nathe-vink/earmilk/critic/LOG.md

# Critic log

One row per round. Fresh context, image only, using `critic/PROMPT.md`. At most three rounds per shot.

| Date | Shot | Prompt v | Round | Score | Three gaps | Fix first | What changed after |
|---|---|---|---|---|---|---|---|
| 2026-10-01 | 01 hero pair | v1 | 1 | 3 | (1) Light story contradicts itself: hard sun wedge on the wall but only faint short shadows, no contact darkening, no floor bounce. (2) Every surface a flat placeholder: no board sheen, drivers flat black with no surround or basket lip, parquet random rectangles, no reflection. (3) Composition unfinished: cropped beige block in the corner, no skirting, near speaker jammed right, empty middle. | One coherent light rig: window sun plus sky fill so the cartons throw hard shadows that agree with the wall wedge, sit in a contact shadow and pick up warm bounce. About an hour. | v2: sun stronger with fills cut back, hemisphere floor bounce, contact-shadow decals, skirting, chair replaces the sofa block, camera recentred, coated-board sheen, bevelled board edges, driver baskets with flange and screws. |
| 2026-10-01 | 02 two rooms | v1 | 1 | 3 | (1) No materials: flat white, razor fold edges, floors are tinted grids, the wall wedge in a is not received by the carton. (2) Drivers are decals: no surround roll, flange, rebate, screw heads or rim shadow; the oval has no edge thickness. (3) The pair disagrees on the product's colour (white/red vs kraft/black), and the warm key is not white-balanced. | Rebuild the drivers and the spout as hardware set into the cabinet: rolled surround, flange in a rebate with screw heads, dust cap that catches the key. Half a day. | v2: driver baskets rebuilt (flange, screws, glossy surround, shaded cone and cap), board sheen and bevels, windows moved front-left so the sun hits the faces the camera sees, hemisphere bounce, contact shadows, a chair in each room for scale. Colour difference between a and b is the shot's point (the sleeve swap) and stays. |
| 2026-10-01 | 03 bowl close-up | v1 | 1 | 4 | (1) The black faceplate is a void: reflects none of the white surround, no rim catch. (2) Bowl shading says key from below-right while the box is lit from above; no contact shadow under the lip. (3) Crop by accident: wordmark baseline sliced, a sliver of a second plane along the top edge. | One soft key from above-left with a white environment card, then pull the camera back a hair. About an hour. | v2: key moved above-left with the environment as the white card, faceplate made reflective, camera pulled back so the wordmark and the top edge clear the frame. |
| 2026-10-01 | 04 back | v1 | 1 | 3 | (1) No volume: parallel verticals, no top or side face, flat fills, and the backdrop seam runs through the port. (2) Shadow detached from the footprint, no contact occlusion; hard tonal steps on the carton say hard light while the shadow says overcast. (3) No materials: port a flat disc, posts flat dots, label a textureless inset rectangle. | Put it on the floor: one soft key from upper right, a tight contact shadow from the footprint, the slight downward perspective the seam implies. About an hour. | v2: camera raised to look slightly down so the gable top shows, key from upper right, contact shadow decal, post bodies and port flange given metal response, board sheen. |
| 2026-10-01 | 05 five flavors | v1 | 1 | 5 | (1) Cones uniform black with no gradient, no surround specular, no rim shadow into the dish. (2) Bases meet the backdrop as a hard line with no contact occlusion; the soft smudge to the right is weaker than the crisp faces. (3) On the white units the fin, slope and front are the same white a hair above the backdrop, so the gable fold never turns. | Rebuild the lighting: one large soft key from upper left at about 45 degrees, quarter fill from the right, a ground plane with contact occlusion. About an hour. | v2: key moved to upper left at 45 degrees with a quarter fill from the right, contact shadow decals, driver hardware rebuilt, cone and cap given a sheen so they shade. |
| 2026-10-01 | 06 mixed crate | v1 | 1 | 4 | (1) Nothing occludes: no shadows between cartons or on the crate's inner walls, no contact darkening, crate base has no shadow. (2) Flat surfaces: no creases, no sheen, crate grain runs the wrong way and is one stretched tile, floor flat. (3) The rim cuts through all three visible woofers; the red port cup is the loudest thing in frame. | Re-light with a real rig: large area key up-left, soft fill, occlusion so the cartons shadow each other and ground into the rim; drop the camera so the woofers clear the rim. About an hour plus fifteen minutes. | v2: contact shadows under crate and pints, key up-left, camera raised so more of each pint shows over the rim (the rim height is spec, so the woofers stay partly behind it), crate grain turned to run along the boards. |
| 2026-10-01 | 07 sleeve swap | v1 | 1 | 3 | (1) Frame b does not describe a physical event: the lifted tube's die-cut lands on the bowl and reads as a porthole, the small driver reads as an empty ring, and the lid is nowhere. (2) Nothing lit or grounded: no floor, no contact shadow, the hovering lid casts nothing. (3) Untextured primitives: drivers flat, razor edges, no crimped seam; hairline spike and dotted ridge on the lid in a. | Rebuild the action so frame b is a true intermediate state and re-render all three. A day. | v2: frame b now shows the lid standing on the floor beside the speaker and the tube lifted clear of the gable so nothing overlaps the bowl; contact shadows; fin cover sunk 2 mm to kill the z-fighting ridge; driver and board materials as above. The two-piece sleeve (tube plus lid) is a Decision and stays. |
| 2026-10-01 | 01 hero pair | v2 | 2 | 4 | (1) Room light and product light disagree: the warm patch high on the right wall reads as sun from the right while the cartons' right faces are dark and the floor shadows read short and soft. (2) No material: one flat white, no sheen, no crease lines, no board thickness at the spout, woofers near-uniform black with no surround roll or cap specular, soft-edged logo decals. (3) Viewport, not a picture: the pair split across depths, the second unit near the corner behind a chair, half the frame empty flat-tiled floor with no grain or reflection. | Relight with one sun through the window that reproduces the wall patch plus a sky fill, path-traced, so right faces go bright, fronts fall off with warm bounce, shadows go long with a penumbra, contact occlusion at the base. About an hour. | v3: ambient occlusion pass, glossier coated board, fold and crimp lines on the lid and fin, lighter shaded cones with a highlight on cap and surround, reflective floor, higher shadow resolution, 2x supersampling. The sun stays on the left window because the pair faces the room; the floor patch now shows where it comes from. |
| 2026-10-01 | 02 two rooms | v2 | 2 | 4 | (1) The room's light never touches the hero: window wedges on the wall and floor but the carton's faces stay flat, no shadow from the carton or the chair as read. (2) Flat untextured box and decal drivers: no scored folds, glued seam or crimp, no sheen or ink grain; cones with a baked gradient regardless of light. (3) The night version is a grade, not a relight: everything one monochrome brown, the brand red gone to black-brown, no cooler ambient in the shadows; the chair's back leg is tangent to the carton's edge. | Put the carton in the room's light: one real key where the wall wedge says the window is, shadows on every object, contact and occlusion at the base and under the chair legs, the night version driven by a warm lamp in that rig. About an hour. | v3: occlusion pass, fold and crimp lines, glossier board, shaded cones, a cool sky ambient in the old room so shadows are not sepia, chair moved off the carton's edge, 2x supersampling. The Oat print is dark brown by spec, not red. |
| 2026-10-01 | 03 bowl close-up | v2 | 2 | 4 | (1) The white body has no form: top face, front face and backdrop within a few points of the same off-white, razor edge with no highlight, the back corner dissolves into the background. (2) The recess contradicts itself: brightest at the top-left wall where a dish would be in rim shadow, an S-shaped highlight reads as a saddle. (3) Crop inherited from the viewport: bare top face is 60% of the frame, wordmark not aligned with the recess, a corner fragment and a red sliver at the bottom right. | Relight the body: one key from upper-left so top, front and side step down in value, a 1 to 2 mm edge radius catching a line, a backdrop a few points darker than the top. About an hour. | v3: key steeper and more frontal so the slope reads brighter than the front, occlusion pass, glossier board so the edge and faces separate, the side wordmark sliver cropped out, 2x supersampling. The ground stays #F8F7F4 by spec. |
| 2026-10-01 | 04 back | v2 | 2 | 4 | (1) The light that casts the hard parallelogram never touches the object: flat fills on every face, the fin throws nothing on the slope, a second blurred contact blob bleeds out to the left. (2) No paperboard: no score lines, sheen, kraft grain, the port a flat black disc, posts dots on a bevel-less plate. (3) Orthographic elevation pinned dead centre; spec rows at about 1% of frame height. | One large soft key from upper-left-front with a shadow catcher: slope brightest, gentle falloff on the vertical face, fin shadow on the slope, one shadow with a penumbra and a dark contact core. About an hour. | v3: contact decal tightened to the footprint, key moved to upper-left-front, occlusion pass, glossier board, crimp lines on the fin, metal posts with collars, 2x supersampling so the rows resolve. Straight-on is the brief. |
| 2026-10-01 | 05 five flavors | v2 | 2 | 5 | (1) Cartons cast almost nothing: a small smudge, no contact occlusion, no floor reflection, floor the same tone as the backdrop. (2) Flat fills: no coated-stock sheen, no highlight on the gable creases, drivers laid on the face with no flange shadow. (3) The horn reads as a dish seen from above while the mid is a dead-on circle: the sloped gable does not read on white. | Ground the lineup: one angled area key, a soft directional floor shadow, contact occlusion at every base, a faint floor reflection. About an hour. | v3: reflective studio sweep, occlusion pass, camera raised a few degrees so the slopes and fin read as a gable, fold lines on the lid, glossier board, 2x supersampling. |
| 2026-10-01 | 06 mixed crate | v2 | 2 | 4 | (1) Only the crate casts a shadow: nothing between cartons or into the crate, no contact at the crate's foot, a hard uniform parallelogram. (2) Camera pitched about 40 degrees down with parallel verticals; the rim crops every woofer and the crate takes 60% of the width. (3) Flat albedo everywhere, crate a single milled block, cartons without sheen or folds, while the bowls carry the only hot specular and read as glossy eyes. | Reframe first: drop to about 15 degrees down on a 70 to 85 mm lens, lift the woofers clear of the rim, then relight with one soft key and occlusion. About an hour plus a half-day. | v3: camera lowered to about 25 degrees on a longer lens from further back, occlusion pass, pint throats closed in the throat colour instead of black so they stop reading as eyes, crate boards given end grain and a chamfer, 2x supersampling. Pints stand on the crate floor and the rim is spec height, so the drivers stay partly behind it. |
| 2026-10-01 | 07 sleeve swap | v2 | 2 | 4 | (1) Lifted parts not in the same light as the carton: no shadow from the lid or the tube lands on the body; floor shadow one flat grey with the same razor edge near and far. (2) Hardware as flat fills: cones near-black discs with no recess shadow, bowl a flat red ellipse with a black ellipse pasted off-centre. (3) The frames do not describe one action: the lifted tube runs out of the top of frame b, and in c the old lid and tube have vanished. | Area key from camera-left and a bounce card at camera-right, re-render all three so the lid's and tube's shadows land on the carton and the floor shadow gains a penumbra. About an hour plus a half-day. | v3: key made steep so the lifted lid and tube shadow the carton, occlusion pass, wider lens so the lifted tube stays inside the frame, and in frame c the removed Whole lid and tube lie on the floor behind the speaker so the three frames are one action. |
| 2026-10-01 | 01 hero pair | v3 | 3 | 4 | (1) Room and product light still read as disagreeing: hard wedge on the wall, shadows read soft, floor pools feathered, plank values noisy. (2) No surface craft at spread scale: no board grain, fold shading faint, seal reads as stacked slabs, drivers read as discs at this distance. (3) No hero: two subjects on opposite thirds, left gable tip on the corner line, chair competes. | One hard key agreeing with the wall wedge, tight contact shadows, flatten the plank noise. About an hour. | Round cap reached. Remaining asks are penumbra, grain and bounce light: a path-traced or diffusion pass over this frame, not a change to the model. Composition note (corner tangent, chair) carried to the next camera pass. |
| 2026-10-01 | 02 two rooms | v3 | 3 | 4 | (1) No paperboard craft at this scale: creases faint, seal a slab with lines, port lip without thickness, drivers read flush. (2) Set reads as a blockout: plank texture repeats, no reflection of the carton, chair is six blocks. (3) Day shadow reads overcast against the wall wedge; night room merges into one olive mass with denoiser smearing; print reads brown-black. | Rebuild the carton's surface (creases, seam, crimped fin, port lip, recessed drivers). About a day. | Round cap reached. The night print is Oat's dark brown by spec. Surface fibre, reflections and penumbra go to the photoreal pass. |
| 2026-10-01 | 03 bowl close-up | v3 | 3 | 4 | (1) The faceplate reads as a flat circle in crushed black while everything else is foreshortened, so it reads as a sticker. (2) The red form's shading does not describe a surface: bright at both tips, a dark band through the middle, no contact occlusion along the rim. (3) The white body reads unlit: uniform top and front, razor edge, no ground or cast shadow in frame. | One soft key from upper-left, weak fill, an environment for the gloss to reflect, a ground plane for a contact shadow. About an hour. | Round cap reached. The faceplate is a true circle in the plane of the throat, perpendicular to the view, so it is not foreshortened; a slight camera offset would show its edge. Rim occlusion and reflections go to the photoreal pass. |
| 2026-10-01 | 04 back | v3 | 3 | 5 | (1) The front face is one flat value near the wall tone, the roof plane flat, the cast shadow a uniform wedge without a dark core at the base. (2) Port a pure-black disc with no inner wall, terminal plate flat with no screws. (3) No paperboard: no fibre or ink bleed on the kraft panel, corners read as soft bevels, the fin's crimp lines read as stacked plates. | One large soft key from upper-left with a weak fill so the faces take a gradient and a tight contact shadow forms. About an hour. | Round cap reached. Up one from round 2. Straight-on is the brief; a port interior and kraft fibre go to the photoreal pass. |
| 2026-10-01 | 05 five flavors | v3 | 3 | 4 | (1) Floor and boxes disagree: shadows pool right-rear while some left-facing sides are darkest and a white carton's right side is as bright as its front; contact shadows read faint. (2) Dead-matte razor-edged slabs: no grain, sheen, creases, seam or filleted edge. (3) From this height the roof reads as a chamfer, the spout as a flat ellipse, the drivers flush. | Re-light under one key front-left-high, remove the environment brightening the right sides, a real shadow catcher. About an hour. | Round cap reached. The environment fill is what keeps the white sides readable; a path-traced pass resolves both. |
| 2026-10-01 | 06 mixed crate | v3 | 3 | 4 | (1) Light contradicts itself: the crate's end reads brighter than its front while the shadow says front-left, and the wall carries a soft shadow a hard key could not cast. (2) The set is a finite slab: ground wedge at the corner, floor meets wall with no skirting, planks flat. (3) Nothing has a surface; the bowls read as decals. | One soft area key front-left and above, occlusion on, penumbra that widens, wall and floor shadows agreeing. About an hour. | Round cap reached. Skirting and a larger floor are a quick set fix for the next camera pass; surfaces go to the photoreal pass. |
| 2026-10-01 | 07 sleeve swap | v3 | 3 | 4 | (1) Lit front and turned side differ by a few percent; the lifted lid in a and tube in b read as casting nothing; no contact darkening read. (2) Drivers are the only photographic element against flat board; sleeve cut-outs coincide with the driver rims with no visible edge. (3) Continuity: the lid's oval shows a dark cone while the lid lies empty on the floor; the lifted lid's base lands on the horizon line; the bowl reads red in a and b and dark in c. | One large soft key from upper left, a seamless sweep instead of the wall-floor seam, contact occlusion under every piece, shadows from the lifted parts on the gable. About an hour. | Round cap reached. The bowl is red on Whole and dark brown on Oat by spec; the lid's oval shows the bowl through it, not a cone. The horizon tangent and the seam are a quick camera and backdrop fix for the next pass. |
| 2026-10-01 | 01 hero pair | v4 | 4 | 3 | (1) The room has a sun and the objects do not: the wall wedge and the floor patch are the brightest things in frame, yet the right speaker's right face is the darker face and its shadow reads as a faint short smudge. (2) One flat value per surface: no board tooth, no gable crease, drivers read as radial-gradient discs, parquet in hard blocks. (3) No focal point: two near-identical objects on opposite thirds, chair tangent to the left speaker, bottom third empty floor. | One real key, the same source that makes the wall wedge, so both cabinets take a bright right face and throw hard shadows, then pull the fill down. About an hour. | Look change round (lids and band). Same asks as rounds 1 to 3: the sun is the left window by design (the pair faces the room), its floor patch and the speakers' shadows agree, but the fill flattens them. Carried to the next pass: fill down, sun up. |
| 2026-10-01 | 02 two rooms | v4 | 4 | 5 | (1) A perfect extrusion: hard CG corners, no crease radius at the folds, crimp a ridged slab, drivers flangeless rings around a flat gradient. (2) Shadows disagree with themselves: the wall wedge in a is as bright as the product but the carton shows an even gradient and a soft smear; in b the carton carries hard self-shadows while its floor shadow is a long blur, and the black band dissolves into the floor. (3) The pair reads as two SKUs: red gable and band in a, cream gable and black band in b. | One key of one size per frame that the carton obeys; rotate the night key off the hero face; a dim cool bounce so the band separates; contact occlusion. About an hour. | Up one from round 3. The colour flip between a and b is the shot's point (Whole by day, Oat by night, the sleeve swap) and stays; the night band is Oat's dark brown print by spec. Carried: rotate the night key so the crimp's shadow clears the mid driver. |
| 2026-10-01 | 03 bowl close-up | v4 | 4 | 3 | (1) The red panel is one flat value with no falloff or specular lobe, the faceplate clipped to black with nothing reflected, so only the cavity reads as rendered. (2) An S-shaped crease where the lit upper wall meets the shadowed lower wall, which no rim shadow explains, and a razor rim with no fillet. (3) A fragment: the panel exits on three sides, a sliver of the top lip tangent to the frame, the white body dissolving into the backdrop. | Light it: a large soft key up-left plus a rim so the red takes a gradient, the barrel reflects a source, the rim catches an edge; then pull back. About an hour. | Down one from round 3 after the camera offset. The S-curve is the lip's hard shadow-map edge inside the bowl, not geometry: carried to the next pass as a soft terminator (the bowl stops receiving the key's shadow) and the camera tilted so the top lip clears the frame. |
| 2026-10-01 | 04 back | v4 | 4 | 4 | (1) Cast shadow 370 px to the right in an even grey but no contact shadow under the base and gable, body and edge all one value: a cutout with a shadow drawn beside it. (2) One matte shader everywhere: port a black disc with no inner wall, posts flat rings on a flat plate. (3) Dead-on at mid-height, the cyc's horizon slices the carton under the Facts box, side faces a 6 px strip, nothing to give scale. | Re-light in place: one large soft key high and front-left with a weak fill, a tight dark contact shadow under the base. About an hour. | Down one from round 3. Straight-on at mid-height is the brief (the back is the label). The cast shadow is the back key by design, so the Facts panel stays unlit by it. Surfaces go to the photoreal pass. |
| 2026-10-01 | 05 five flavors | v4 | 4 | 5 | (1) Every face a single flat fill, no falloff across the width, no sheen, folds hard unbevelled lines; on Chocolate and Oat the gable crease all but vanishes. (2) Contact shadows a few percent darker than the floor, no occlusion at the front bottom edges, so the row hovers. (3) Too close on too wide a lens: the end cartons fan out and show side faces the middle one does not, the floor-to-wall transition lands on the gable ridges, white flanks dissolve into the wall. | Re-light with one large soft key from upper-left far enough forward for a 15 to 20 percent falloff across each front face, a real contact pool, side faces down a stop, satin gloss on the board; a longer lens rides along. About an hour. | Held at 5. The lineup is a flat elevation by brief (five cartons, one row, same size), so the longer lens from further back is the cheap carry: camera back and focal up so the ends stop fanning. Falloff and gloss go to the photoreal pass. |
| 2026-10-01 | 06 mixed crate | v4 | 4 | 4 | (1) Two shadows from two suns: a soft blur under the crate's front edge and a razor-edged slab running off the right of frame ending in a stepped notch, while the crate's lit front and shadowed right faces differ by half a stop. (2) Nothing has a surface, and each woofer reads as a black rubber wheel pushed half into the carton body, peeking over the rim. (3) The subject loses its outline on the right: the wall-floor seam runs through the cartons at their waist, the two white cartons sit against an off-white wall, the planks run on a third diagonal. | Relight: kill both shadows, one large area key from upper left matched to the current shadow direction plus a dim fill, so the penumbra widens with distance and the cartons shade each other. About an hour. | Held at 4. The critic read the rim-cropped woofers as wheels, which is a readability problem not a surface one: carried as a camera fix (higher and closer so the crate's inside and the pints' faces show), the desk turned so the planks run with the wall, and the hard sun shadow softened. Crate size and rim height are spec. |
| 2026-10-01 | 07 sleeve swap | v4 | 4 | 4 | (1) The object revealed is not the same in each frame: pale gable in a, lighter tan core with no band in b, darker tan with a near-black band in c; the spout shows red in a and b and dark in c. (2) The pieces do not share one floor or light: the lifted lid carries a soft contact shadow in mid-air in a, the lifted tube adds nothing to the floor shadow in b, and in c the lid's base slides under the standing tube's front corner. (3) Flat colour with razor edges, drivers vignetted discs, so the sleeve's cut-outs in b read as grey dents. | Make the core one asset across the frames: one tan, the band present from b onward or absent everywhere, one interior colour in the spout, then re-render. About an hour. | Held at 4. The frames are one action by spec: a lifts the Whole lid off the birch cabinet, b lifts the Whole tube off it, c has the Oat sleeve on with the Whole lid and tube on the floor; the band belongs to the sleeve, not the cabinet, and the bowl is red for Whole and dark brown for Oat. The shadow in a is the lid's shadow landing on the gable top. The lid under the tube's corner in c is a real placement error: carried as a lid move. |
| 2026-10-02 | 01 hero pair | v6 | 1 (finish look) | 4 | (1) The room's hard sun reads from camera-right (wall patch, floor wedges) while both cabinets read lit soft from the front-left with no sun on their right faces, and the two gable tops come out two reds, one salmon, one crimson. (2) Nothing responds as a material: flat white with razor edges, no sheen, a five-tone floor with no grain or reflection even inside the sun patch, drivers as black discs. (3) The top half of the frame is empty wall, the brightest element sits in the far corner, the chair is half-cropped, the two units sit at mismatched depths, and the brand plate reads as grey type on a grey rectangle. | One sun the whole scene shares, so the hard patch crosses the right cabinet's faces and both throw a crisp matching shadow; a contact pass to ground the bases. About an hour. | First round on the finish look. The two reds are one lacquer under one sun (the slope faces it, the far gable does not); the critic reads the difference as two paints. Carried to v7: the badge given a dark field inside a chrome rim so it reads at room distance. The sun, surfaces and floor remain the renderer's ceiling. |
| 2026-10-02 | 03 bowl close-up | v6 | 1 (finish look) | 4 | (1) The red top is one flat value edge to edge, no falloff or specular roll, while the scoop carries a glossy streak and the white front brightens downward, away from the key the dome sets: a vector fill with a rendered hole in it. (2) The faceplate is a crushed black disc with no red bounce, no barrel side, no contact shadow on the cavity wall, so it reads as a sticker and the scoop's depth collapses. (3) A zoom, not a frame: the top plane leaves on three sides, a black component sliced at the bottom edge draws the eye first, no body edge for scale. | One satin material for top and scoop, a large low soft key from upper-left so the plane carries a gradient that runs into the scoop; pull back ten percent so the bottom sliver leaves. About an hour. | First round on the finish look. The top and the scoop are already one lacquer; the flat read is the renderer's lighting. The sliver at the bottom is the mid driver's flange, which v5 tilted into frame to clear the top lip: carried to the next pass as a crop that holds neither. |
| 2026-10-02 | 02 two rooms | v6 | 1 (finish look) | 4 | (1) Each room is lit by two sources that disagree: by day the wall wedge and the carton's shadow put the window up-left while the chair's shadow falls to its own left; by night the floor and wall glow from the right-front while the carton's left-facing front is the bright face. (2) The night carton is still at daylight exposure: the red top and skirt keep their daytime saturation while the room drops several stops into olive, and the gloss picks up no warm bounce. (3) Zero-radius edges, drivers as one flat black, no wall thickness at the spout, a badge with no bevel or contact shadow, and a hard diagonal tone break across the front through the mid in both frames. | One honest source per room (a window sun with sky fill; a warm lamp where the floor glow says it is), everything taking shadow and bounce from it, the night frame re-exposed. An afternoon. | First round on the finish look, the same Whole in both rooms since the sleeve went. The diagonal break is the window mullion's shadow, now a dark lacquer line to the critic; carried: a plainer window so no bar crosses the hero face. The night exposure and bounce go to the photoreal pass. The shot still needs a brief that is not the swap. |
| 2026-10-02 | 05 five flavors | v6 | 1 (finish look) | 5 | (1) Under each unit a faint grey mist trailing right with no dark contact core, floor and backdrop one flat off-white with no horizon: five cut-outs on a page. (2) Pure diffuse colour with razor corners, no specular line on the ridge or the verticals, no falloff down the front, while the drivers carry gloss; the white units' left edges dissolve into the sweep. (3) The plate is the same flat mid-grey rectangle on all five with near-zero-contrast text and no edge catch, and the horn mouth reads as a two-tone ellipse rather than a flared cavity. | Ground the row: a key with enough direction for one soft shadow with a dark core per base, occlusion in the seam, a two-stop falloff from floor to backdrop. About an hour. | First round on the finish look, held at 5. The badge contrast is carried to v7 (dark field in a chrome rim, polished letters). The horizon and the edge highlights are the renderer's ceiling; the lineup's flat elevation is the brief. |
| 2026-10-02 | 04 back | v6 | 1 (finish look) | 4 | (1) Every surface one flat value, no gradient across any face, no specular on the coating, the port a dead black disc with no lip or wall: a dieline shaded object in a photographic set. (2) A hard uniform cast shadow with no penumbra, no dark root, no contact occlusion, while the faces show no left-to-right shading to agree with it. (3) A portrait object dead centre in a landscape frame at a fifth of its width, side faces a sliver, the wall-to-floor break running through the bottom of the spec table. | A large soft key in place of the sun lamp plus an occlusion pass, so faces take a gradient, the shadow a penumbra and a dark root, the port lip a highlight. About an hour. | First round on the finish look, held at 4. Straight-on is the brief and the back is the label; the engraved wordmark above the Facts and the plinth across the bottom drew no comment. The soft key, the port's lip and the paperboard read go to the photoreal pass. |
| 2026-10-02 | 06 mixed crate | v6 | 1 (finish look) | 5 | (1) The long floor shadow says a low front-left key, but nothing inside the crate obeys it: the brown pint throws nothing onto the cream one, the red-capped one nothing onto the blue behind it. (2) The six openings do not agree: the brown carton's is a pale ellipse lighter than its skin with no interior darkness, the cream one mid-tan, the red one a shaded rim, the blues black; the nearest reads as a sticker. (3) Flat single tones, no tooth, no crease, razor edges; the crate wears three unrelated grains; the floor returns no sheen. | One true area key front-left at the floor shadow's elevation with shadow casting and contact occlusion on every object, so the pints shade each other and the interiors go dark. About an hour. | First round on the finish look, up one from v4. The openings differ by spec: each throat is painted in its flavour's mouth-to-throat gradient, and Chocolate's is lighter than its body. Shadows between pints and the three grains go to the next pass; the woofers no longer read as wheels. |
| 2026-10-02 | 03 bowl close-up | v7 | 2 (finish look) | 4 | (1) The scoop carries a softbox reflection and a bright upper-left lip while the red plate it is cut from shows no gradient or reflection across the top-right quadrant: two materials, and the largest area a vector fill. (2) No contact shadow or occlusion where the barrel enters the recess wall and no catch-light on its circumference, so the barrel and the dark upper-right of the recess merge; the dome reads as a plastic bead. (3) The plate cut on all four sides, the barrel in the right third, a second black element sliced at the bottom-centre edge, which reads as an accident. | The plate at the recess's satin roughness, one large soft key from upper-left so the plate takes a gradient and the recess reflection reads as that light, occlusion where the barrel seats; the recrop in the same pass. About an hour. | Round 2, held at 4; the badge change does not touch this frame. The plate and the recess already share one lacquer; the recess picks up the environment because it curves. The mid's flange at the bottom edge is the crop note from round 1, still open. |
| 2026-10-02 | 04 back | v7 | 2 (finish look) | 5 | (1) The cast shadow tapers to a point a carton-width to the right with no gable silhouette at its end, no contact shadow on the base's left half, no left-to-right roll on the body. (2) The port a flat black disc with no tube wall or rim, the white and the kraft single fills with no tooth, crease or fin seam. (3) The wall-to-floor horizon runs along the Facts box's bottom rule, and the terminal cup and the kraft panel both butt into the red plinth with zero margin while the panel keeps a white margin on its other three sides. | One large area key front-left and above with a real shadow catcher so the shadow is the carton's projected silhouette, contact occlusion across the base, enough wrap for a gradient. About an hour. | Round 2, up one. The zero margin is a real note: the birch panel starts at the shadow line and the post plate sits at z 112, so both touch the plinth. Carried: the panel's bottom lifted to z 140 (a 27 mm white margin like the sides) with the post plate on it, if the owner agrees it is not a Geometry change worth keeping. |
| 2026-10-02 | 05 five flavors | v7 | 2 (finish look) | 5 | (1) Not grounded: a faint blur offset lower right of each unit, no contact occlusion where the plinth meets the floor, floor and backdrop one value. (2) No tonal modelling: each face one value edge to edge, razor corners, the white bodies within a few percent of the backdrop so their unlit left edges dissolve, worst on Skim. (3) Cramped side to side and empty top to bottom: the row runs to within 8% of the edges while a quarter of the frame above and below is bare; the middle unit lands on a spread's gutter; the nameplate vanishes on the black base. | A shadow-catcher floor with one large softbox overhead and biased left, fill down, for contact occlusion, a readable cast shadow and a top-to-bottom falloff. About an hour. | Round 2, held at 5. The plate now reads on the four light plinths; on Oat's dark plinth its dark field disappears, so the chrome rim is the only edge: carried as a question for the owner (a light field on the dark flavours, or the rim alone). The frame: pulled back a step so the row has air at the sides. |
| 2026-10-02 | 02 two rooms | v7 | 2 (finish look) | 4 | (1) The product is not lit by its room: by day the wall patch and the chair's shadow are hard while the carton leaves a soft smear and a diagonal slit of light across its front that no window could produce; by night the cream front reads near-white while the wall a metre behind falls to near-black with no lamp to explain it. (2) Modelling defaults: flat white with dead-sharp edges, banding on the red slopes, a cone with a plastic specular blob, bezels flush with no recess shadow, the tweeter a black ball in a hole with no wall thickness. (3) A placeholder set: floors as flat colour blocks with stepped joints and no reflection, a bright vertical seam in the night room's corner, the product dead centre with an empty right third. | One source the room explains for both room and product: the window as the day key matching the wall patch's hardness, a motivated lamp in the night frame with the product exposed inside it. About an hour, half a day checked side by side. | Round 2, held at 4. The night lamp exists but sits out of frame at the right; carried: bring its glow onto the wall. The bright corner seam is the window wall meeting the back wall and is a set fix. The slit of light is the mullion shadow noted in round 1, still to remove. Rebriefing the shot stays with the owner. |
| 2026-10-02 | 01 hero pair | v7 | 2 (finish look) | 4 | (1) Nothing agrees on where the light is: cabinets shaded almost flat, the left cap salmon and the right maroon, floor bands running under both cabinets without a matching shadow, the near cabinet's lit front saying the key is on the camera's side while the floor to its right is the brightest patch, a razor-edged wedge on the wall that does not say whether it is sun or ceiling. (2) Every surface a flat shader: planks as colour blocks with no grain or reflection of the red bases, no board tooth or seam, drivers as radial-gradient discs, the badge a soft decal, the chair block geometry. (3) The staging works against the product: a high camera leaves 40 percent of the frame empty floor, both cabinets toed the same way so they read as parked boxes, the near one larger and low-right, the brightest area in the far corner, the chair against the left edge. | Relight from scratch with one source through the off-frame window plus a sky fill, real cast shadows and contact occlusion, so caps, floor bands, wall wedge and bases fall out of one rig. About an hour plus render time. | Round 2, held at 4. The badge now reads as a plate with lettering rather than grey on grey, which was this version's one change. The two caps are one lacquer under one sun; the floor patch to the right is that sun and the near cabinet's shadow lies inside it. Carried: toe both cabinets toward the lens and lower the camera so the pair reads as a pair. |
| 2026-10-02 | 06 mixed crate | v7 | 2 (finish look) | 4 | (1) The crate's floor shadow one flat polygon with the same razor edge at its tip as at the base, no contact darkening where the crate meets the floor, while the wall shadow is soft and faint: two lights. (2) Flat colour everywhere: no sheen, no crease or fin seam, no board thickness at the ovals (two read as lit recesses, four as black cavities), no rim thickness on the crate, floor as tinted rectangles with no reflection. (3) The three front gable ridges sit a hair below and parallel to the wall-floor seam, the rim slices the drivers to slivers, the shadow runs out of frame right while the left two-fifths is empty floor. | An HDRI plus a large soft key from upper-left with occlusion and contact shadows, so the shadow gains a penumbra and a contact line appears at the crate base; the camera drop clearing the ridges off the seam is a ten-minute follow-on. About an hour. | Round 2, down one from v6 (a different critic on the same set). The crate shot has no badge in view, so this version changed nothing it sees. Carried: the camera a hand lower so the ridges clear the seam, and the desk's planks given a sheen. The rim's crop of the drivers is the crate's spec height. |
| 2026-10-02 | 01 hero pair | v8 | 3 (finish look) | 4 | (1) Two lighting stories: a razor-edged sun wedge high right on the wall while both speakers throw wide soft shadows lower-left, the floor band runs flat to the far corner instead of sitting under the window, and the chair in that band casts nothing. (2) Flat fills: no board texture, no edge bevel catching a highlight, no warm bounce from the wood; drivers as discs with a radial gradient; the port on the slope a cut-out with no rim; planks with no grain or sheen even in the sun. (3) A wide lens high and off-axis makes the near speaker nearly twice the far one and tilts them opposite ways; the logo sits in the bottom 15 percent, the top third is empty wall, the chair a placeholder in the corner. | One light: a sun through a window portal on the right that makes the wall wedge, a hard floor patch under it, crisp shadows from both speakers and the chair, warm bounce on the white. About an hour. | Round 3, held at 4. The lettering replaced the plate and drew no comment, which is the result wanted. The sun's portal is on the left wall by design (the pair faces the room); the critic puts it on the right because the wedge falls there. Carried: toe the pair in, a longer lens from lower, the chair's shadow. |
| 2026-10-02 | 03 bowl close-up | v8 | 3 (finish look) | 4 | (1) The red top one flat value from the chamfer to the far edge, no falloff or stretched key reflection, while the scoop runs from pink to deep red: a sticker over a shaded object. (2) The cylinder meets the scoop with no contact shadow or occlusion at the seam, its rim without a catch-light, its face a black disc holding nothing; every edge a hard CAD edge with a one-pixel highlight, no radius on the rim or the chamfer. (3) The object pushed past three edges, the second black element a 30-pixel sliver at the bottom, the off-white front against a background of the same value: no silhouette, no scale. | One large soft key above and behind camera-left so the top takes a gradient and a stretched softbox reflection, a slight gloss on the red, occlusion where the cylinder seats; the pull-back a five-minute follow-on. About an hour. | Round 3, held at 4; this frame has no lettering in it, so v8 changed nothing it sees. Three rounds on the finish look now say the same two things about the close-up: the flat plate is the renderer, and the mid's flange at the bottom edge is a crop to fix. Round cap reached for this shot on this look. |
| 2026-10-02 | 05 five flavors | v8 | 3 (finish look) | 5 | (1) Grounding: deep self-shadow in the throats and surrounds but each cabinet meets the floor on a hard evenly lit edge with only a faint wash pushed right, no occlusion where the plinth touches the sweep. (2) Separation: the white bodies sit within a few points of the backdrop, held only by the bands and the drivers; on a spread the three white units become floating caps and plinths. (3) Flat albedo everywhere, no tooth or sheen or fillet highlight; cones, surrounds and the wordmark the same untextured grey with a radial gradient. | One key from upper-front-left with real contact occlusion under every base, the sweep falling off a few points warmer and darker behind the row. About an hour. | Round 3, held at 5. The wordmark is read as debossed grey on all five, so the cast letters survive the plate's removal but not the renderer's lighting; a lighter environment behind the camera would put chrome in them. The white-on-white separation is the brief's ground colour. Round cap reached for this shot on this look. |
| 2026-10-02 | 04 back | v8 | 3 (finish look) | 4 | (1) A hard uniform parallelogram shadow running 1.3 widths to the right while the carton that casts it is shaded flat edge to edge: no falloff, no terminator on the right edge, no contact darkening. (2) No surface anywhere: no tooth or poly sheen on the white, no print grain on the kraft, the three reds differ in hue rather than in light, the port a pure black disc, the plate a flat rectangle; the only specular on two 12 px posts. (3) The wall-floor seam at 48 percent of the height lands on the spec box's bottom rule; the carton 19 percent of the width dead centre; the one-sided shadow drags the weight right. | One large soft key from upper front-left with a weak fill from the right: gradients on the white and the reds, a terminator, a penumbra darkening to a contact line, the port's inner wall. About an hour. | Round 3, held at 4; the back has no lettering on the plinth, so v8 changed nothing it sees. The seam on the Facts rule has now come up twice: carried as a lower camera or a higher horizon. Round cap reached for this shot on this look. |
| 2026-10-02 | 02 two rooms | v8 | 3 (finish look) | 5 | (1) A razor-hard diagonal shadow across the front in both rooms while the floor shadow is a soft smudge to the right, no contact darkening under the carton or the chair, the chair's shadow going left and the carton's right. (2) Not a carton in the material: CAD-sharp edges, no fold or seam, the fin a 5 cm slab where a folded fin is a centimetre, the spout's inner wall the same red with no board core, a plastic sheen, the logo bevelled 3D type rather than ink, the woofer's surround nearly kissing the band while a wider gap separates the drivers. (3) A blockout room: flat rectangle planks with no gaps or reflection, the chair at the same height as the product reading as leftover dressing and crushing to a silhouette by night. | One source that explains everything, a crisp floor shadow with the gable in it, contact occlusion under both, the stray diagonal removed unless a window edge motivates it. About an hour. | Round 3, up one. The diagonal is the window mullion, flagged in rounds 1 and 2 and still to remove: it goes in the next camera pass. The fin's thickness, the driver heights and the lettering as metal are spec, not drift. Round cap reached for this shot on this look; the shot still wants a brief that is not the swap. |
| 2026-10-02 | 06 mixed crate | v8 | 3 (finish look) | 4 | (1) One hard uniform cast shadow to the back right as if by sun while nothing else agrees: no bright side to the floor, a flat wall, no contact darkening under the crate's front edge, the pints casting nothing on each other or the crate's inside. (2) Placeholder materials: the crate one veneer with no slats or joints, its bottom edge a fuzzy fringe, no sheen or crease on the pints, the openings disagreeing (a lit pale interior on the brown, black voids on the red and blue). (3) The camera 35 to 40 degrees above with a third of the frame empty floor shrinks the product to a miniature; the front wall hides the back row and crops the black parts to slivers; a horizontal seam against diagonal planks reads as a rotated texture. | A large soft key from the front left plus a dome fill so the shadow gains a penumbra, the surfaces a gradient and a specular, and contact occlusion appears under the crate and between the pints. About an hour. | Round 3, held at 4; no lettering in view, so v8 changed nothing here. The fringe along the crate's bottom edge is the end-grain texture on the base board's front face, a real texture bug: carried as a fix. The openings differ by spec. Round cap reached for this shot on this look. |
| 2026-10-03 | 01 hero pair | v11-pt | 1 (path-traced) | 6 | (1) The room and the product disagree about the light: a hard sun wash high on the right wall implies a high window at camera-right, yet both cabinets' right faces are darker than their fronts, the floor carries no sun patch and each throws only a short soft smudge to its left, so the product reads as lit by a frontal softbox and pasted into a window-lit room. (2) Both cabinets show front plus right side, so the pair reads as a duplicated asset rather than a staged pair, and the chair is sliced through the seat by the frame edge. (3) White body and red gable are flat fills with razor edges: no bevel catching a highlight, no sheen, no reflection in what should be a varnished floor; only the cones read as photographed. | Commit to one light: a window whose sun continues from the wall down onto the floor, rakes the cabinets and drops one hard warm-edged shadow each, or delete the wall wash and own the soft light. About an hour. | v12: the room closed with a ceiling and two more walls, so the only daylight is the window's; the wash was the sun spilling over a wall with no ceiling. Light units converted (the dome fill was five times the real-time ambient). Mullion gone, chair fully in frame, arrises eased in the shader. |
| 2026-10-03 | 02 two rooms | v11-pt | 1 (path-traced) | 5, 5 | a: (1) Not grounded: the boards at the foot as bright as the open floor, the shadow a wash with no dark core where cabinet meets floor. (2) The coral gloss mirrors a different white on every face, so one paint reads as three pinks. (3) The room is blocked, not dressed: the chair a massing model, the floor plank seams with no grain or sheen, within seven values of the wall. b: (1) The room says the light is camera-right (the chair's shadow falls left) yet the front face, facing away from it, is the brightest and flattest surface; the identical pill highlight on both dust caps is the frontal softbox's reflection. (2) The base meets the planks on a hairline with no contact shadow and no reflection in a floor with a visible specular pool. (3) The spout reads as a lens barrel or a lipstick: a red cylinder lying sideways in an oval with a glossy black disc at its end. | a: replace the near-uniform dome with a defined key up-left and pull the ambient down. b: kill the frontal softbox and let one light up camera-right do the job. About an hour each. | v12: both rooms closed, units converted, the dome gone from inside the rooms; the window and the lamp are now the only lights, so the fronts fall off and the bases sit in contact shadow. The chair and the spout are spec, not critic fixes: noted for the owner. |
| 2026-10-03 | 03 bowl close-up | v11-pt | 1 (path-traced) | 4 | (1) The red plane, seventy percent of the frame, is one flat value corner to corner: no specular lobe, no reflected ceiling, no falloff, so only the inside of the scoop behaves like matter. (2) The driver's rim takes its highlight upper-left while the deepest shadow in the scoop smears to the lower-left and the right wall, where the driver's shadow belongs, is the brightest red, so driver and recess read as lit by different suns and the driver as composited in. (3) The slab shows a 2 to 3 mm lip and meets the grey with no contact shadow, and a stray dark band in the top-left corner is a backdrop seam left in frame. | Rebuild the light: one large soft key up-left plus a reflective environment for the red to see, and a glossy clearcoat layer on the red (it has one; the environment had nothing in it). About an hour. | v12: the studio key is a softbox and the dome a gradient, white overhead and the backdrop tone at the horizon; the floor sweeps up into a backdrop so there is no seam; arrises eased in the shader. |
| 2026-10-03 | 04 back | v11-pt | 1 (path-traced) | 5 | (1) The floor shadow describes a steep soft key from front-upper-left but the object shows no sign of it: the white face a flat 221 across its whole height, the up-facing gable slope the same value as the vertical base band, the contact line eight levels darker at most, so the box reads as a cutout with a shadow drawn under it. (2) Two flat tones meeting in a hard seam that lands on the Facts panel's bottom rule, so the horizon runs through the pack; below it the white body sits three percent above the floor tone and the silhouette dissolves. (3) Nothing has a material: the port a flat disc, the emboss a soft grey stain blurrier than the label type, razor edges, the kraft panel a solid fill. | Relight: one large soft source raking from upper-left at 30 to 40 degrees to the baffle, a weaker fill from the right, so the body takes a real gradient and the emboss gets a highlight and a shadow edge; a seamless sweep while the lights are open. About an hour. | v12: softbox key on the real-time key's axis, gradient dome, sweep behind the subject, the bronze a metal (it had read as kraft), arrises eased. |
| 2026-10-03 | 05 five flavors | v11-pt | 1 (path-traced) | 5 | (1) Grounding: the floor the same flat value right up to every plinth, no occlusion pooling, no directional shadow, so five heavy boxes read as cut-outs. (2) Backdrop: a hard horizontal seam a quarter of the way down, just above the waveguides, with no tonal falloff on wall or floor, so the speakers sit in a box, not a studio. (3) Surface craft: single untextured values with razor edges that catch no highlight, and the wordmark on the chocolate unit cream-on-cream while the other four are crisp. | Re-light: a curved sweep in place of the wall-floor corner and one large soft source overhead and slightly forward of the row, so each plinth throws a short soft contact shadow and the sweep takes a gradient. About an hour. | v12: sweep, softbox, gradient dome, eased arrises. The chocolate wordmark is polished metal reflecting the dome; with a gradient to reflect it reads again. |
| 2026-10-03 | 06 mixed crate | v11-pt | 1 (path-traced) | 4 | (1) Ambient-only light: no contact shadow under the plinth, the back row lit like the front, nothing thrown into the crate, only a faint smear off the right side, so the crate reads as pasted on and the six units flatten into one plane. (2) The crate wall crops every driver to a black crescent over the rim and the back row to three roofs, so the one feature that says speaker is seventy percent hidden and reads as casters or lens caps. (3) Blockout surfaces: no fold seams or fin thickness, razor crate corners with no bevel, the base a flat zero-value black with no top-edge highlight, and the three roof ports rendering three different ways. | One large soft key from upper-left plus a weak fill, so the plinth gets a contact shadow, the cartons throw shadows into the crate and the back row drops half a stop. About an hour. | v12: the dome at a quarter of its strength, so the desk's sun and fill read; the black base was the base board sharing the walls' outer planes, which a path tracer renders black, now inset inside the walls. The crate's wall height is spec: noted for the owner. |
| 2026-10-03 | 01 hero pair | v12-pt | 2 (path-traced) | 5 | (1) The light splits the pair: the left cabinet stands in the sun patch (front 221, its red orange) and the nearer right one outside it (front 169, its red maroon), neither casts a readable shadow on floor or wall, and the wall is a smooth gradient with no patch, so a viewer sees two colourways in one shot and weightless boxes in hard sun. (2) Placeholder materials: no edge radius, so sunlit front and shaded side meet as a bare value step with no catch-light; the woofer cone glossy enough to mirror a white blob at the lit baffle's value; the floor wood by plank outline only, no grain, gap or bevel under a vinyl-smooth gloss. (3) Weight and light disagree: the nearer, larger cabinet is the one in shade, the chair is pushed into the darkest corner half hidden behind the left cabinet, and the centre 700 px is bare wall. | Relight with one key: widen or slide the window so the same sun hits both cabinets, the right one's shadow falling across the patch where the viewer can see it, so both reds match and the pair is pinned to the floor. About an hour. | v13: the window widened to 2.6 m so the band crosses both cabinets; the chair moved clear of the left cabinet; paper cones matte; plank grain and gaps stronger; the shader bevel 2 mm. |
| 2026-10-03 | 02 two rooms (a) | v12-pt | 2 (path-traced) | 6 | (1) The hardest shadow edge in the frame, the diagonal bounding the sun pool at the lower right, does not belong to the cabinet: it sits clear of the base's corner, the chair under the same light throws only a soft smudge, and the cabinet has almost no occlusion along its base, so it reads as placed on a picture of a floor. (2) Every edge a zero-radius line, the white one flat value from gable to base with no catch-light, no warm floor bounce in the lower third and no reflection, the fin a thick slab: beside the woofer frame's screw heads the box reads as an untextured primitive. (3) The room's corner line runs tangent to the cabinet's left silhouette, the chair sits in full focus at near-equal weight with its rail at the gable's height, and a hotspot is clipped by the top-right corner. | One committed source: the window's sun aimed so the cabinet itself casts a hard shadow attached to its base, occlusion under the band, the stray pool gone. About an hour. | v13: the window moves to the right wall in all three rooms, so from the camera at the right the sun lights the faces it sees and the cabinet's own shadow falls where the viewer can see it; the chair moves out of that shadow. |
| 2026-10-03 | 02 two rooms (b) | v12-pt | 2 (path-traced) | 5 | (1) The only light is an uncorrected tungsten spot, so the white front measures salmon and the side ochre, walls, floor and carton share one hue and nothing in the frame is neutral: a misrepresented product, not a mood. (2) The spot's hard edge draws a straight line across the floor at the carton's base, the back-left floor falls to pure black while the right wall at the same depth is lit, and the planks change colour at butt ends with no seam, so the object stands on the lip of a stage in a render room. (3) Both drivers one high-gloss black with a mirror sweep and polished bullet caps, so they read as lacquered dishes pressed into the box rather than paper cones in a basket. | A neutral key from the same upper-left position, a large soft cool fill from camera-right so the side and the floor behind come out of black, the key's edge feathered, the warm kept as a low rim, then white-balanced so the front lands near 235/230/222. About an hour. | v13: the window moves to the right as a cool dusk fill against a warm-white (not amber) lamp; the line on the floor was the dusk sun's band edge, which now falls elsewhere; paper cones matte. |
| 2026-10-03 | 03 bowl close-up | v12-pt | 2 (path-traced) | 5 | (1) A near-featureless dome with no key: the panel top one value corner to corner, the bowl a single-hue ramp, the dome's only specular the hairline where the bottom edge fillet catches it at a grazing angle, so nothing says whether the red is lacquer, satin plastic or paper. (2) The join between the barrel and the recess's back wall, the one thing the recess exists to show, is buried in the darkest zone: base, cast shadow and occlusion fuse into one black-on-maroon mass with no lit strip, seam or gap to say how the part is held. (3) The panel is a sheet while the recess is a bowl: an 8 px front edge against a 275 px barrel, so the pocket cannot fit inside that slab and reads as a hole punched in card with a bowl painted behind it. | One large soft area key camera-left, high enough to reach into the bowl, and the dome dropped to fill strength: a highlight gradient on the panel, a hot spot on the bowl floor, a readable shadow from the barrel with lit red between it and the wall, a glint on the dome. About an hour. | v13: the studio softbox sized and placed from the real-time key's distance (closer and smaller for the rake), the dome at fill strength. The slab reading is the gable's lip from this camera; a note for the owner. |
| 2026-10-03 | 04 back | v12-pt | 2 (path-traced) | 5 | (1) Dead-frontal with no side panel visible, the white front one flat value from gable fold to base though the brighter top plane says the key is overhead, and the sweep has no readable horizon to stand on, so the pack reads as a mockup template on a grey field; the same frontal light is why the emboss shows almost no relief. (2) No paperboard in the paperboard: CAD-sharp corners, no ridge seal or crease highlight on the gable, no fibre or print texture, and the base band cut off by a hard black groove that makes it read as a separate plastic plinth. (3) The parts that should sell speaker do not: the port a featureless flat disc with a thin lip, the posts two soft dots, the label's spec lines already soft at 1800 px, and the ochre panel the loudest element on the pack, fighting the red. | Pull the key up and to one side so the white face falls off half a stop from gable to base and the fold catches a highlight line, and turn the carton 10 to 15 degrees so a sliver of side reads a stop darker. About an hour. | The shot is briefed straight-on and the groove is the spec's shadow line; the raking key is a carry. |
| 2026-10-03 | 05 five flavors | v12-pt | 2 (path-traced) | 6 | (1) One enormous overhead dome and no key: the white body one value from cap seam to base band, the flanks barely a step darker than the faces, only the gable slope separating, so five flat rectangles with drivers pasted on. (2) The shadow under each cabinet a pale symmetrical blur no darker at the seam where the band meets the floor than halfway to the next unit, and no occlusion between units: cabinets that should press into the floor sit on it like empty cartons on a lightbox. (3) On the brown unit the mark is a cream a few points lighter than the cream band, a faint emboss beside four hard marks, read as a mistake before a colourway. | One large key from upper camera-left at about 45 degrees and a weak fill, so the face takes a gradient, the flanks drop a stop, the slope catches an edge and the floor gets a directional shadow with a dark contact line. About an hour. | v13: the studio dome dropped to fill strength, the key softbox placed from the real-time key's distance. The Chocolate mark is polished metal on a cream plinth, which is the spec: a question for the owner. |
| 2026-10-03 | 06 mixed crate | v12-pt | 2 (path-traced) | 5 | (1) The crate's front wall stands 243 px against 280 px of visible carton: half of each body hidden and the rim cutting two-thirds of every front disc, so the viewer cannot tell driver from wheel from cap and the hero reads as dropped into a box one size too deep. (2) The floor ends in a hard uncoved edge against the backdrop that slices through all six shoulders and lands on the crate's back-right corner, while the crate's hard shadow runs off the right edge. (3) The white carton's lit face sits within a few levels of the backdrop and the tan within six of the floor, so three of six cartons have no edge against the set and the eye lands on the red and blue tops at the back. | Get the rim below the discs: lift the cartons on an insert or cut the walls by a third, then re-render. About an hour. | The crate's wall height is spec and goes to the owner. v13: a cooler fill and a neutral dome in the desk room so the pale cartons lift off the set; matte cones. The hard edge is the desk's back edge against the wall. |
| 2026-10-03 | 01 hero pair | v13-pt | 3 (path-traced) | 5 | (1) The light does not read as one source: a hard sun lights the floor wall to wall and throws the left speaker's shadow across to the right one's feet, yet on the wall it lands only as a crisp rectangle whose top sits on the speakers' shoulder line and whose right edge stops dead with no matching cut on the floor, so the viewer cannot place the window and the patch reads as painted on. (2) No surface: the white baffle one flat near-clipping value, every corner and fold a razor edge, the gold badge a soft low-contrast smear on the coral, the spout a black oval with the dome floating in it though its slope faces the light. (3) Nothing grounded and the floor outguns the product: a specular wash that reflects neither body, bases meeting the floor on a hairline, the floor the brightest and most saturated surface in the frame, and the right speaker a fifth taller than the left with half again as much side. | Re-light from a real window behind camera-left with a single sun through it at 30 to 35 degrees, so one patch falls across floor, wall and speakers as one geometry and the left speaker's shadow ends short of the right one. About an hour. | Cap reached. The patch on the wall is the window's head cutting the band; the next pass should raise the sun so the band stays on the floor, whiten it so the floor does not go orange, and shoot from further back on a longer lens so the pair sits at one scale. |
| 2026-10-03 | 02 two rooms (a) | v13-pt | 3 (path-traced) | 4 | (1) The white body is not lit as a volume: front and side faces both measure 231 to 232 top to bottom, no warmth from the plinth or the sunlit floor, no occlusion from the driver rims, while the red gable beside them shows a clear lit and shade split, so the carton becomes a white cut-out with drawn edges and the red top proves the sun the white denies. (2) Nothing ties it to the floor: it stands in a hard-edged sun patch yet throws only a sliver of shadow that exits the patch into unlit floor, no gable silhouette anywhere, the boards under the plinth within a few percent of the open floor. (3) The set is built to a lower standard than the hero: the chair a slab on four square sticks, the floor a flat tan fill with hairline seams, no skirting where wall meets floor. | Slide the window's footprint back so its far edge sits well behind the carton and the full silhouette lands on lit floor, pull exposure down two-thirds of a stop so the white comes off the shoulder and the faces separate, a contact-occlusion pass under the plinth and the rims. About an hour. | Cap reached. The white is on the shoulder: the apartment needs two-thirds of a stop less in the path tracer, and the sun band a metre further back. Carries for a future pass, with a chair that is furniture. |
| 2026-10-03 | 02 two rooms (b) | v13-pt | 3 (path-traced) | 4 | (1) The product is lit by a light the room does not have: the room's only visible source is the sun slash from the right, yet the carton's front and gable are its brightest planes, its right-facing planes darker, the slash on the wall runs behind the gable with no shadow bite, and the carton throws no hard shadow while the chair plainly sits in the beam, so the chair is in the room and the speaker pasted on. (2) A primitive with a colour slot: zero-bevel edges with no highlight on ridge or corner, the fin a flat slab, no board grain, no specular break on the red, the emboss dark on dark red and gone at thumbnail size. (3) Hierarchy inverted: the brightest areas are the empty top-right wall and the lit floor wedge with the chair, the hero in the dim middle with the skirting line slicing through it, the camera at standing height so the floorstander reads as a tabletop model. | Put the product in the room's light: move the speaker or the sun so the slash rakes the gable and right side, cuts a hard shadow across the baffle, bites the wall band behind it and throws a long shadow down-left; kill the separate product key. About an hour. | Cap reached. The lamp is the room's second source and sits out of frame; the next pass should aim the dusk sun at the cabinet rather than the corner, and put the lamp in frame or drop it. |
| 2026-10-03 | 03 bowl close-up | v13-pt | 3 (path-traced) | 5 | (1) The barrel and its dome return no highlight at all, no rim on the upper-right edge, no catchlight on the element, though the long shadow trailing left across the bowl proves a strong key sits upper-right, so the hero element reads as a hole punched into the dish. (2) The red top one flat value corner to corner, no reflection gradient, no falloff, no visible edge face where it ends over the white, only a hairline seam, so the panel has no thickness and the white picks up no red bounce. (3) The scoop's rim blurry-soft on the left and lower edges while the top rim carries a crisp highlight and the seam is razor sharp, and the barrel's shadow runs half the dish and keeps widening, so the recess reads as a dent in foam. | Replace the flat dome with one large softbox upper-right-front and a white bounce card camera-left, the environment visible to reflections: a catchlight and rim on the dome, a gradient across the red, the lid's edge face at the seam, the shadow pulled back. About an hour. | Cap reached. The softbox sits where the rake key stood and the dome is a gradient; what the critic wants is a second, smaller source for the dome and the barrel. A carry for a future pass, with the crop. |
| 2026-10-03 | 04 back | v13-pt | 3 (path-traced) | 5 | (1) Dead-frontal and the light uniform on the box: two pixels of side face on a 341 px body, the front face 192 to 188 across its width while the backdrop behind it falls 191 to 172, the contact shadow a 16 px smudge, so the room is lit from the left and the box is not. (2) The white renders at about 189 with nothing in the frame above 204 and the backdrop at 186 and 180 against its flanks, so the silhouette is carried by the two red bands and on a white homepage the body sits as a dirty grey block, dead-centre with 730 px of empty grey each side. (3) Everything on the face a flat decal: the label black type on dark ochre at about 2:1, the driver a black disc with no cone or surround, the posts two dots, a seam at the base band with none at the top, and the stack logo, label, driver top-heavy with the lower half a void. | Reset the shot: swing the camera 25 to 30 degrees off axis and drop it to 40 percent of the height, one large soft key high-left with a weak fill, exposure up so the body sits near 235 to 245, a real contact shadow to the right. About an hour. | Cap reached. The shot is briefed straight on and the port is the port, not a driver. Carries for a future pass: half a stop more exposure in the studio, the bronze a little lighter under the engraving, a lower camera. |
| 2026-10-03 | 05 five flavors | v13-pt | 3 (path-traced) | 5 | (1) The dust caps and domes carry a crisp highlight from upper-left but the cabinets are lit by a shadowless dome: the big faces one flat value, the sloped gable no brighter than the body under it, no shadow direction on the floor, so drivers and cabinets read as lit in two different rooms. (2) No contact occlusion where the bases meet the floor, only a faint halo, and the white bodies and the pale blue sit within a few values of the backdrop, the red carton's side as bright as its front, so the row hovers over a grey card. (3) Dead-centre with equal gaps and 22 percent margins top and bottom, so a wide crop clips tops or bases and a spread's gutter runs through the centre carton, while the chocolate carton's tone-on-tone wordmark reads as blank beside four branded ones. | One large soft key from upper-left matched to the highlight on the dust caps, a weaker fill, a shadow catcher for a tight contact seam and a directional floor shadow, the backdrop dropped a stop so the white bodies separate. About an hour. | Cap reached. The dome at 1.3 is still the loudest source on a sweep this bright: the next pass halves it again and darkens the backdrop a stop. The Chocolate wordmark stays with the owner. |
| 2026-10-03 | 06 mixed crate | v13-pt | 3 (path-traced) | 5 | (1) Crate, desk and wall the same warm tan at nearly one value, meeting in a hard seam with no cove or occlusion, so the crate's edges are findable only where the plank joints stop and the viewer sees one beige mass with coloured tops. (2) The wall seam cuts across all three front gables at fin height and the crate rim bisects all three ports, so the two edges that explain the object are both interrupted. (3) The cartons now carry edge rounds and thick hole rims but no ear folds, seams or print, while crate and desk have zero-radius corners and a grain that is a faint uniform streak, so cartons read as moulded plastic and the set as untouched primitives from a different scene. | Separate the crate from the ground: a desk top a stop and a half darker or cooler than the crate (smoked oak, grey concrete), the wall kept. About an hour. | Cap reached. A darker desk top is the next pass's first move; the crate's wall height stays with the owner. |

## Verdict after three rounds

Scores went from 3 to 5 in round 1 to 4 to 5 in rounds 2 and 3. The round 1 fixes (grounding, driver hardware, framing) moved the needle; rounds 2 and 3 asked for the same things on every shot: penumbra that widens with distance, paper fibre and ink grain, floor reflections, bounce light, and one light the whole frame obeys. Those are properties of a path-traced render or a photoreal pass, not of the real-time renderer in `render/`, which is the limit `CLAUDE.md` names. The geometry never came up: proportions, bowl, drivers and label were accepted as drawn in every round.

What the critic asked for that is still cheap and render-side, for the next camera pass: move the hero's left speaker off the room's corner line, add skirting and a larger floor to the desk set, keep the lifted lid off the horizon line in the swap, and offset the close-up camera a few degrees so the faceplate shows its edge.

What needs the photoreal pass: everything about surface and light. The frames in `renders/2026-10-01` are proportion-exact control images for it.

## Round 4, on the locked look (v4)

A fourth round because the look changed (printed lids on the white flavours, the band with the wordmark, nothing under the gable); the three-round cap counts per look. Scores held at 3 to 5. The new print was accepted without comment in every shot: no critic flagged the band, the lid colour or the wordmark position, which is the result that mattered for this round. The asks are the ones from rounds 2 and 3 (one committed light, paperboard, bounce, penumbra), which the real-time renderer does not do.

Cheap carries for v5, all camera or placement: hero fill down so the sun's shadows read; night key rotated off the hero face; close-up bowl with a soft terminator and the top lip out of frame; lineup from further back on a longer lens; crate camera higher and closer so the woofers stop reading as wheels, planks with the wall; the Whole lid moved clear of the standing tube in the swap's third frame.

## Round 5: not run

v5 carried the round 4 camera and placement fixes (hero fill down, night key raised, close-up terminator softened, lineup on a longer lens, crate camera higher, swap lid moved). Before the critic ran, the direction changed on 2026-10-02: no sleeve, the colour a fixed finish, the band and the stand one built-in plinth, the wordmark a badge on the front and engraved on the back, no owner's panel. The critic resumes on v6, the first render of that look.

## Round 1 on the finish look (v6)

The first round on the 2026-10-02 direction: no sleeve, the colour a satin finish, the plinth, the badge, the engraved back wordmark. Scores 4, 4, 4, 4, 5, 5. The new parts were accepted as the object: no critic questioned the plinth, the two-tone gable, or the engraved wordmark; two read the badge as a flat grey plate with unreadable type (01, 05), which v7 answers with a dark field inside a chrome rim and polished letters. The rest is the list from every earlier round, one light the whole frame obeys, contact occlusion, edge highlights, surface tooth, bounce, which is the real-time renderer's ceiling and waits for the photoreal pass.

Carries for the next camera pass: a plainer window in the two rooms so no mullion shadow crosses the hero face (02); a close-up crop that clears both the top lip and the mid's flange (03); a brief for shot 02 that is not the sleeve swap.

## Round 2 on the finish look (v7)

One change from v6: the badge became a chrome rim around a dark field with polished raised letters. Scores 4, 4, 4, 5, 5, 4. The badge now reads as a plate with lettering in the hero and the lineup; on Oat's dark plinth its dark field disappears into the plinth and only the rim shows, which is a question for the owner (a light field on the two dark flavours, or the rim alone). Everything else in the round is the renderer's ceiling restated.

Carries for the next camera pass, all small: toe the hero pair toward the lens and lower the camera; a plainer window in the two rooms with the night lamp's glow on the wall; a close-up crop that clears both the top lip and the mid's flange; the lineup a step further back; the crate camera a hand lower; and, if the owner agrees, the back panel's bottom lifted to z 140 so the panel keeps a white margin above the plinth like its sides.

## Round 3 on the finish look (v8)

One change from v7: the plate is gone and the wordmark is cast metal letters standing on the plinth. Scores 4, 5, 4, 4, 5, 4. No critic remarked on the lettering as a problem; one read it as debossed grey type, which is the pale studio environment reflected in polished metal rather than the letters themselves. Three rounds on this look have now said the same things on every shot, so the cap is reached: the remaining asks are one light the whole frame obeys, contact occlusion, edge highlights, surface tooth and bounce, all of which wait for the photoreal pass.

Still cheap and still open, for the next camera pass: toe the hero pair in on a longer lens from lower; remove the window mullion so no bar crosses the hero face in the two rooms, and brief that shot anew; a close-up crop that clears both the top lip and the mid's flange; the back camera lower so the seam leaves the Facts rule; the crate camera lower and the end-grain fringe on its base board fixed; a brighter environment behind the camera so the chrome letters read as chrome.

## v9 of the back: no critic round

v9 renders the contained birch field (the Facts panel plus a 26 mm margin, the wordmark engraved on the finish above, the port and posts on the finish below) as the new default, with the full field kept as an option; both are in `explore/2026-10-02/r4-*`. A spec choice for the owner rather than a render iteration, and the cap for this look is reached, so no round was run.

## v10 of the back: no critic round

v10 renders the back as decided on 2026-10-02: an engraved bronze plate for the Facts, the wordmark as cast letters like the front, SHAKE WELL under the port and OPEN OTHER SIDE on the back slope. Spec choices, and the cap for this look is reached, so no round was run.

## v11: the camera carries applied, no critic round

v11 applies the small notes the three rounds on the finish look agreed on: the hero pair toed in from a lower, longer camera; the window mullion gone from both rooms; the close-up aimed to clear the top lip and the mid's flange; the crate camera lower and its base board's end-grain fringe fixed. It also carries the owner's calls: SHAKE WELL on the plinth's back, and the Facts border enclosing its footnote with even padding. The cap for this look is reached, so no round was run; the next critic round waits for the photoreal pass or a new look.

## Path-traced pass, round 1 (v11-pt)

The first round on frames from Blender's Cycles (`render/pathtrace.py`), the same model and rig exported from the real-time scene. A new render path, so the count restarts. Scores 6, 5, 5, 4, 5, 5, 4: the hero's 6 is the highest any frame has scored, and for the first time no critic asked for penumbra, bounce or contact occlusion as such. What every report said instead was the same two things. The fill swamped the key: the dome I had given Cycles was about five times the real-time hemisphere once units are counted properly (an irradiance is π times a dome radiance), so every face sat at one value and nothing sat on the floor. And the lacquer had nothing to reflect: a uniform grey dome, razor arrises, a studio with a hard horizon seam. Two things were plainly bugs: the sun wash high on the hero's wall was the sun spilling over a window wall with no ceiling, and the black band under the crate was its base board sharing the walls' outer planes, which a path tracer renders black.

v12 answers all of that without touching the product: the three rooms closed with a ceiling and two more walls, so daylight is only what the window admits; light units converted (sun as irradiance, area lamps as radiance times area times π, points times 4π, the dome divided by π); the studio floor sweeping up into a backdrop, its key a softbox and its dome a gradient; the bronze rendered as a metal; the cabinet's arrises eased by about a millimetre in the shader, silhouette unchanged; the crate base inset. Three critic notes are not critic fixes and go to the owner: the spout reading as a lens barrel (02b), the crate wall hiding the drivers (06), and the chair as a massing model (02a) if the room is to be dressed.

## Path-traced pass, round 2 (v12-pt)

Scores 5, 6, 5, 5, 5, 6, 5 against round 1's 6, 5, 5, 4, 5, 5, 4: the studio and the crate up, the hero down a point. The v12 changes did what they were meant to (nobody asked for a cove, a horizon or a black band again, and the back's bronze is now read as a plate rather than kraft) but they exposed the next layer, and the reports agree on it. In the rooms, the sun lit the faces the camera could not see: the windows were on the left and the cameras on the right, so each cabinet's own shadow fell behind it and the hero's two cabinets stood one in sun and one in shade, "two colourways in one shot". In the studio the dome was still the loudest source, so the key had no direction to name and the plinths sat on the floor without a contact line. The close-up's key was too big and too far to put a gradient on a panel that fills the frame. The old room's lamp was tungsten amber on a white product.

One bug surfaced on the way: glTF marks the sky planes unlit, and Blender's importer builds that as emission for camera rays only, transparent to every other ray, so the closed rooms had no sky light at all until the planes were rebuilt as plain emitters (the first v12 hero came out as a cave; it was discarded before the critic saw it).

v13, the third and last round for these shots: the windows move to the right wall in all three rooms, the camera's side, so the sun lights the faces the camera sees and the shadows fall where it can see them, the hero's window 2.6 m wide so both cabinets stand in one band; the chairs move out of those shadows. The studio dome drops to fill strength and the softbox sits where the real-time key stood (closer and smaller for the rake), the back's key rakes from the upper right. The old room's window turns to a cool dusk against a warm-white lamp. Paper cones go matte, plank grain and gaps stronger, the eased arris 2 mm, the desk's fill cooler. Still spec, not render, and still with the owner: the crate wall hiding the pints' drivers, the spout reading as a lens at room distance, the Chocolate wordmark as polished metal on a cream plinth, and the close-up's camera showing only the gable's lip.

## Path-traced pass, round 3 (v13-pt): the cap

Scores 5, 4, 4, 5, 5, 5, 5. Three rounds on the path-traced look have now been run on every shot, so this is the last word on these frames in this batch. The arc: round 1 (6, 5, 5, 4, 5, 5, 4) found a dome that swamped the key and nothing for the lacquer to reflect; round 2 (5, 6, 5, 5, 5, 6, 5) found the sun on the faces the camera could not see and the studio still dome-lit; round 3 found, with the windows moved to the camera's side and the studio keys raked, the next layer down, and it is a plateau rather than a slope. Each round fixed what the one before named and the fresh critic found the same score's worth of new things.

What round 3 names, and what it would take:

- **Exposure, both ways.** In the rooms the white body sits on the shoulder (231 on both faces of the apartment's cabinet, so the faces do not separate); in the studio it sits at 189 with nothing above 204. The real-time exposures came across unchanged and AgX places white differently from ACES. A per-room exposure in the path tracer: two-thirds of a stop down in the apartment, half a stop up in the studio.
- **The sun's footprint.** With the window at 14 to 24 degrees of elevation the band is long and narrow, so a cabinet stands at its edge and its shadow leaves the patch; the hero's band climbs the wall as a rectangle the critic read as painted on. Raise the sun, whiten it so the floor stops going orange, push the band a metre back.
- **Contact and weight.** Big soft fills (the sky through a 2.6 m window, the studio dome even at fill strength) lift the contact line under every base. Halve the studio dome again and darken its backdrop a stop; in the rooms the fix is the exposure above.
- **The set.** The chair is a massing model, the floors are flat fills with hairline seams, the desk is the crate's own colour. A chair that is furniture, a darker desk top, grain that reads at room distance.
- **Beyond render, for the owner.** The spout reads as a lens barrel from across a room (every round, both rooms). The crate wall hides the pints' drivers. The Chocolate wordmark is polished metal on a cream plinth. The tweeter sits in the bowl with no visible flange. The close-up's camera shows only the gable's lip. The old room's lamp lights the product from out of frame. None of these is a critic fix.

Where it stands: the path-traced frames are the best this project has made, and no critic in three rounds asked for penumbra, bounce or a horizon again; what they ask for now is a photographer's second day on set. The real-time frames remain the layout check and the canvas the source of truth for layout, copy and proportions.

### 2026-10-05: the owner's refinement pass (v14)

The path-traced look had used its three rounds per shot (v11 to v13). The owner asked for a further pass ("more photorealistic, polish the design, make sure the milk crate version is correct"), so the v14 batch counts as a new batch: round 1 again, at most three.

Where it ended (v16, round 3, the last in this batch): 01 5, 02a 5, 02b 4, 03 4, 04 4, 05 5, 06 5 (round 1 was 4 to 5). The rounds found three model bugs that every earlier batch had shipped: dust caps squashed across their axis, a port flange modelled as a solid disc over the bore, and cabinet corners the shader's bevel never reached because each panel was its own mesh. The owner's questions the critics raised are in the rows: the letter metal on light plinths, Chocolate's pale throat, a lip or trim at the bowl's mouth, shot 04's straight-on brief, the woofer's place near the plinth, a reveal where the gable meets the body.

| Date | Shot | Prompt v | Round | Score | Three gaps | Fix first | What changed after |
|---|---|---|---|---|---|---|---|
| 2026-10-05 | 01 hero pair | v14 | 1 (refinement) | 5 | (1) a hard, low sun lights the wall and floor but not the cabinets: no crisp shadow of their own, front and side nearly one value, the plinths in a pink glow instead of a dark contact crease, so they look pasted in; (2) every edge a sharp CG corner, every surface one flat colour, no sheen or seam where coral meets white, the bowls like boolean cuts, the gold wordmark the coral's value; (3) the sun patch lands on blank wall between the speakers, and the far speaker sits on two tangents (the chair's seat, the patch's edge) | Relight around the near speaker: swing the sun so its edge rakes across that cabinet, front and side a stop apart, a long carton-shaped shadow across the boards, the fill down so both plinths sit in contact shadow (an hour) | v15: the window and sun moved so the beam falls across both cabinets from the right, the near one's side lit and its front a stop down, long shadows across the boards and no patch on the wall; the fill and bounce down; the chair moved clear of the far cabinet; the eased edges 4 mm in the shader (was 2). The letters' metal and the seam at the gable are the owner's (not acted on) |
| 2026-10-05 | 03 bowl close-up | v14 | 1 (refinement) | 4 | (1) no key, only soft fill: the front one value, no shadow with an edge, and the deepest occlusion falls where the driver sits, so its trim, screws and dome barely separate from black and the oval with an off-centre disc reads as a sideways-glancing eye; (2) every surface featureless at a distance where paint shows orange peel, and the red top meets the grey body with no parting line or reveal; (3) the crop misses the front-left corner by a hair, a wedge of backdrop, a blank bottom third, nothing for scale | Relight around one key: a large soft source high at camera-left aimed down the scoop into the driver's face, ambient down a stop, so the throat bottoms out at oxblood and the trim, screws and dome take an edge (an hour) | v15: the overhead rake replaced by a large soft key front-left at about 18 degrees, the one direction that reaches a driver facing forward under the bowl's upper lip; environment and fill down; the camera pulled back with the corner inside the frame. For the owner (geometry, not acted on): a hairline reveal where the gable meets the body, asked for in two shots |
| 2026-10-05 | 02a bright room | v14 | 1 (refinement) | 4 | (1) the sun comes from behind-right but the white body ignores it: the baffle, which should be in shade, is the same near-clipped white as the sunlit side, so the box flattens into a glowing cut-out; (2) a blockout: knife edges, colour changes for joins, no texture, two reds that nearly match (the bright plinth slides toward coral under the tone map), drivers butted on with no rebate or contact shadow; (3) dead centre of the frame, from standing height looking down, which shrinks a floorstander to tabletop scale; the chair crowds the left edge | Relight around one motivated key: the sun or a large window light front-left so the baffle takes the key, the side a stop into shade, the shadow falling back-right; exposure down until the white sits below clipping (an hour) | v15, both rooms (see 02b): the window on the left wall, so the sun crosses the baffle and the gable and the side the camera sees falls a stop into shade; exposure down; the camera lower and the speaker off centre; the chair at the right, clear of the edge |
| 2026-10-05 | 02b older room | v14 | 1 (refinement) | 4 | (1) the carton is not lit by its room: the amber beam passes over the fin onto empty wall while the front sits in an even neutral fill, two lights, the product pasted in; (2) knife-sharp edges and untextured panels, the red clipping to orange on the lit faces while the front stays crimson; (3) the bottom third cramped (the woofer's surround near the band: spec), the wordmark dark on red in shadow, the cabinet on the centre line, converging verticals | Relight around one key the scene explains: move sun and window so the beam sweeps the front face and gable and throws a crisp shadow back across the floor, delete the neutral fill (an hour) | v15, both rooms: the window on the left wall, so a low sun crosses the front face and gable (the right side, the one the camera sees, falls a stop into shade) and the shadow runs back-right; the fills and the lamp down; the camera lower, the speaker left of the centre line, the chair at the right for balance; edges 4 mm. The woofer's place on the baffle is spec (not acted on) |
| 2026-10-05 | 04 back | v14 | 1 (refinement) | 4 | (1) dead on at eye level like an elevation: the gable collapses into a flat red stripe, no side shows, the outline a plain rectangle dead centre where a spread's gutter folds it, and OPEN OTHER SIDE points at a side the shot never shows; (2) one soft wash from the front: the face even edge to edge, the white body a shade above the grey backdrop, the cast shadow behind it out of view, the base a hard line on clean floor, so no volume and no weight; (3) placeholder surfaces: knife edges, no texture, the port a flat black disc with no surround (it was: the flange was modelled solid over the bore), the bronze label muddy and low in contrast; it also read the Facts' 12 in woofer as impossible on a face it sized at 4.5 in from the binding posts (a misread of scale: the face is 390 mm and the 12 in woofer is spec) | Swing the camera to three-quarters, 30 to 35 degrees off the face and 10 to 15 up, so the gable roof, a side and the cast shadow come into frame (an hour with relighting) | v15: not the camera (straight on is the brief, as in v3, v5 and v13). The key a smaller softbox from the camera's right, 30 degrees up and about 50 off the face, closer, so the face falls off across its width and the shadow lands in frame at the left; the dome at half and no edge strips, so the backdrop drops to a mid grey behind the white body; a reflector card behind the camera lighting only the bronze and the posts, so the plate reads bright and its engraving dark; the port's flange a ring with a rounded lip, so the bore shows; edges 4 mm |
| 2026-10-05 | 05 five flavors | v14 | 1 (refinement) | 5 | (1) one broad, even light from the camera side: the gable slope nearly the fin's value, the white bodies the backdrop's light grey, a faint smudge under each base for a contact shadow, so the fold flattens into a coloured cap and heavy cabinets read as cut-outs; (2) knife edges and flat matte faces with no crease, crimp, seam or sheen, the dust caps squashed horizontal pills (they were: squashed across their axis, in every shot), the wordmark all but gone on the brown unit's cream band; (3) a level, straight-on camera on five identical forms evenly spaced: the gable seen only face-on, the floor-to-wall line through the gaps at woofer height, the light-blue unit on the centre line where a gutter splits it | Relight: a large softbox key high and to one side so gable, front and side each take a value, the backdrop lit on its own, real contact shadows (an hour) | v15: a softbox high at the front-left and close enough that the sweep falls a stop below the white fronts, aimed so the five stay within a third of a stop; dome, fill and strips down so the sides keep their shade; all five turned the same 7 degrees (the very slight three-quarter the brief allows); the dust caps round domes; edges 4 mm. Lighting the backdrop to white was tried and dropped: its bounce filled the sides and AgX held it at a light grey. The camera stays straight on and centred (the brief). The letters on the cream plinth are the owner's (not acted on) |
| 2026-10-05 | 06 mixed crate | v14 | 1 (refinement) | 5 | (1) one clean satin shader in six colours: flat panels, no scores or crimp, no texture or wear, and the same stock driver at two sizes with one highlight on every dust cap, so it reads as a mock-up and the material is unknowable; (2) a single hard, low sun from the left leaves each face one value; the white crate, the white bodies and the cream wall sit at nearly one value, so the back-right carton barely separates from the wall and the weight piles onto the brown carton; (3) a high, centred three-quarter camera: an empty bottom third, every woofer jammed against the right edge of its window so the wall clips its frame, the centre line down a seam between cartons, and the cast shadow running out of the frame | Re-lock the camera: just above the gable tops, nearly square to the front so the woofers sit centred in their windows, an 85 to 100 mm lens, the crate to one side (an hour) | v15: the camera at desk + 0.38 m (the brief's 'slightly above desk height'), a shallower three-quarter (14 degrees), an 85 mm lens, the crate a little left of centre with its shadow in frame; the pints' rows 124 apart (9 mm from each long wall) so each woofer shows whole behind its window; the wall a warm grey so the whites separate; round dust caps; edges 4 mm. The cabinets are lacquered, not board, so no scores or crimp. Whole repeats |
| 2026-10-05 | 01 hero pair | v15 | 2 (refinement) | 5 | (1) the white cabinets have no form: front and side at almost one near-white value with knife corners, while the coral plinth below shows its two faces clearly apart, so the white has clipped and each speaker reads as a cutout; (2) nothing touches down: a hairline of darkening at each plinth, no soft shadow spreading from the base, the right speaker on bright floor along its front and right edges, the chair barely darkening floor or wall; (3) the one prop staged against the product: a chair centred against the wall behind the pair, facing the camera as the drivers do, a spot nobody listens from | Pull the white down until it stops clipping and bevel every cabinet edge 2 to 3 mm, so the panels separate as the coral ones do and each corner takes a highlight (under an hour) | v16: measured, the sunlit sides sat at 249 (the plinth's at 254 in red), so the exposure comes down about half a stop rather than the spec's white; the chair turned toward the window, set down rather than posed. The edges are already eased 4 mm in the shader. The contact shadows are the sun's: it reaches the floor at the lit faces' feet |
| 2026-10-05 | 03 bowl close-up | v15 | 2 (refinement) | 4 | (1) nothing in the light describes the scoop: no highlight on its rim or floor, the lit top falls into a gradient of clipped red bottoming out near (40, 0, 0), its deepest point darker than the tweeter's black faceplate, so the eye falls into a void and the waveguide reads as a hole; (2) each plane one flat value (the white front within ten levels, the red top within a dozen), the top mirroring no softbox, so the finish could be lacquer, satin or moulding; (3) an accidental crop: a sliver of the driver below at the bottom edge, an unexplained pale-pink band along the top, a third of the frame blank white | Relight around the scoop: one large softbox whose reflection lands as a gradient band across the red top and rakes into the bowl, a strip on the far rim, more bounce so the bowl fills with its own red (an hour or two) | v16: a 0.9 m softbox high to the left, where the red slope mirrors it, so a highlight band grades across the slope and its light reaches the bowl's floor; measured, the bowl now bottoms at about (87, 0, 0) and the darkest values in frame are the faceplate's (28, 23, 22); the crop up and tighter, so the mid driver's rim leaves the bottom edge and the fin stands whole at the top. No rim strip: the bowl's edge is a crease in this geometry |
| 2026-10-05 | 02a bright room | v15 | 2 (refinement) | 5 | (1) a painted placeholder: every edge of body, gable and fin a sharp corner, each face one flat tone with no sheen, the red band only a colour change with no seam or step; (2) the tweeter sits off-centre and deep, half hidden by the opening's right edge, so the spout reads as a hole with a black blob wedged against one side; (3) the low sun works on the empty floor (bright patches, a long shadow toward the chair and out of frame) while nothing crosses the cabinet, the front one even white | Round every edge of body, band, gable and fin about 2 to 3 mm and give the paint enough gloss that those edges catch the sun (an hour) | v16: the corners were never eased: each panel of the finish is its own mesh and the shader's bevel only sees its own object, so the path tracer now joins each cabinet's finish before rendering (every frame from v16); the shared camera a little more frontal (about 25 degrees off the axis, was 32), so the tweeter sits further into the opening. The seam at the plinth is a 3 mm shadow line in the model |
| 2026-10-05 | 02b older room | v15 | 2 (refinement) | 5 | (1) the brightest light on the top third and a soft diagonal shadow across the front below the upper driver with nothing in the room to cast it, so the body shows three colours (cream, dull grey, orange) and the fin washes to salmon; (2) flat untextured surfaces with knife edges, no sheen, the gable a plain triangle; (3) underexposed: near-black browns, the left third a void, the chair lost in the floor, the dark wordmark on shadowed red the hardest thing to read | Relight from one window just out of frame so the speaker's light, the chair's shadow and a crisp patch on the floor agree; a stop up; a large bounce opposite so the front reads one white from roof to plinth (an hour) | v16: the window taller (sill 0.35, was 0.95), so the beam takes the whole front from gable to plinth instead of cutting a diagonal across it (the window frame cast that edge) and lays a crisp patch on the boards; env, bounce, the lamp, the window's sky and exposure up, so the room and the chair read and the red stays red; the wordmark lit; the corners eased by the join, as in 02a |
| 2026-10-05 | 04 back | v15 | 2 (refinement) | 5 | (1) level, dead on, long lens: only one face shows, the gable a red trapezoid, no side wall, so the floor shadow is the only sign of depth; (2) no surface says what it is: knife-sharp vertical edges, the port a flat black disc with no lit crescent though the light comes from the right, the ochre panel a flat swatch with type on it; (3) everything on the centre line, the cabinet a fifth of the width, the shadow wedge out of frame on the left, the fold through every word | Turn the camera to three-quarters (30 to 35 degrees) from standing height, place it on a third, keep the shadow in frame (an hour; a day if the sides were never finished) | v16: not the camera (straight on is the brief, as in v3, v5, v13 and round 1). The corners eased at last (the join, see 02a); the port's flange moulded satin black with a fuller lip (4.5 mm) that takes the reflector, so the opening reads as a rim round a bore; the bronze brushed, so the reflector reads as a sheen across metal. The cabinet's width in a 3:2 frame is the brief's straight-on, full-height view |
| 2026-10-05 | 05 five flavors | v15 | 2 (refinement) | 5 | (1) no key: fronts, sides and gable slopes in one narrow band, a faint halo at each base, the white bodies a light grey barely above the sweep and no brighter than the empty floor (measured: fronts about 200, floor 198), so the eye slides off the product; (2) one untextured matte shader with dead-sharp edges on body, gable and band, no change of sheen between parts, a clay mock-up with finished drivers dropped in; (3) the row looks twisted: a full side on the left carton, almost none on the right (the 7 degree turn plus the lens's spread), the middle unit on the gutter | Relight: one large soft key high and to one side, a bounce opposite, a strip behind for an edge on every cabinet; whites just under paper white, the sweep a stop down, the floor darkening toward the bottom (an hour) | v16: square again; a grid on the key (75 degree spread, aimed at the cabinets' upper half), so the floor in front and the sweep fall off while the cabinets take the beam's core; exposure up a little (higher washed the colourways off their hex, which the brief holds true); the strips behind up for edges, the fill up from the right as a bounce; the corners eased by the join. The row stays centred (five in flavor order, equal spacing) |
| 2026-10-05 | 06 mixed crate | v15 | 2 (refinement) | 5 | (1) the gable openings look like holes in hollow shells: the brown carton's oval pale yellow inside and brighter than its face, the beige half lit, the red near black, a black tube hanging in each with nothing holding it: a cartoon eye on a model with its back missing; (2) one narrow band of warm mid-tones (cream crate, beige floor, taupe wall), the crate barely separate from the floor, the biggest dark mass the shadow in the empty right third; (3) one untextured satin on every surface, one soft radius on every edge, ruled floorboards with no grain or plank-to-plank change, no wear | Make the openings dark and attached: close the shells, a matte black inside every cavity, each tube seated in a flange (an hour) | v16: a walnut desk whose planks vary more, so the cream crate and the white pints stand off it; the corners eased by the join. Not the openings: each bowl's colour is the flavour's throat gradient in spec/colorways.json (Chocolate's runs cream #E2CBA3 to tan #A97E4F, so it reads paler than its brown face), and the tweeter is seated at the throat, small at this distance. For the owner: whether the Chocolate throat should run dark |
| 2026-10-05 | 01 hero pair | v16 | 3 (refinement) | 5 | (1) untouched CAD surfaces: the right cabinet's front-to-side edge jumps from 208 to 239 in a few pixels and never catches a highlight, its front a dead-flat 204 to 205 from gable to woofer, so the box looks less finished than the drivers mounted in it; (2) the low sun from camera-right spends itself on the blank side panels (every pixel above 232 is on the right cabinet's side) while the fronts with the drivers, wordmark and spout sit in flat fill; the left cabinet's front and side only 8 levels apart; the right half of each spout drops near black and swallows the tweeter; (3) one hue: floor, wall, chair and the cabinet white all within about 2 degrees of 29, no pixel bluer than red, so the milk-white reads peach and stale | A surface pass on the cabinet: 1 to 2 mm on every edge, a faint sheen and micro-roughness on the white and coral (an hour) | The last round in this batch. The edges are eased now (4 mm, joined), but a radius that small takes no glint from a sun behind the camera's side. For a next pass: the sun round to the front-right so the fronts and the spouts take it; a cool sky fill through the window so the white reads cold against the warm floor; an edge light (a white card camera-left) for a hairline on each corner |
| 2026-10-05 | 03 bowl close-up | v16 | 3 (refinement) | 4 | (read the crop as a bathroom vanity, the bowl a basin) (1) the back half of the bowl falls to near-black maroon though the slope around it is lit, so the bowl reads as a bottomless hole and the driver's housing melts into it on its left; (2) the driver has no visible seat: no cutout, flange or gasket line in the bowl's wall, its upper edge rising past the back-right rim with no notch, a loose part dropped in; (3) the red top shows no clear reflection, only a broad milky sheen washing its front-left third to salmon, true red only at the far right and in the bowl; the counter's edge cut dead sharp | Rebuild the light: lose the milky sheen, one large softbox reflected as a clear band across the red, a low fill card in front so the bowl's back wall holds a deep red (an hour) | The last round in this batch. v16's top softbox gave the slope its gradient but too broad a sheen. For a next pass: frame wide enough that the fin and the gable's outline say carton (tight on the bowl alone it read as a sink); the softbox smaller and further so its reflection is a band; a low card in front to fill the bowl's back wall; the tweeter's faceplate seated on a visible ring where the throat ends |
| 2026-10-05 | 02a bright room | v16 | 3 (refinement) | 5 | (1) the low sun throws a long hard shadow from the base to the right edge, yet the front facing it is an even light grey, no brighter than the sunlit boards and only a shade above the shaded side, so the speaker looks studio-lit and dropped in, and the sunlit floor at lower right is the brightest thing in frame; (2) flat colour fills: razor corners with nothing catching light, no sheen or grain on white or red, the gable meeting the body as a bare colour change; (3) the bowl a raw hole with no lip or trim and the driver half hidden at its right end, read as an eyeball or a camera lens peering out | Re-light for the product: the sun raking the front and gable, the white face just below clipping, the right side two stops down with warm bounce, the floor patch brought down (an hour) | The last round in this batch. For a next pass: the sun higher and further round so its patch lands on the cabinet, not beside it, and the exposure set off the white face; a trim ring or a polished lip at the bowl's mouth is a design question for the owner (the bowl reads as a hole at room distance in every critic round) |
| 2026-10-05 | 02b older room | v16 | 3 (refinement) | 4 | (1) no surface finishing: edges that never catch light (the corner a jump from cream to tan), flat colour with no sheen or reflection, the band only a colour change, the wordmark dark-grey extruded type; (2) murky light that gives no shape: the left of the frame near black, an olive-brown wall with no window patch to explain the key, the front one brightness top to bottom, the fin washed to salmon, the warm cast turning the white cream and the red orange; (3) the front layout looks dropped in: the woofer's ring almost on the band with a wide gap above it, the tweeter at the right end of the scoop off the drivers' line | Bevel every edge a few mm and give white and red a real satin lacquer, a seam where the band meets the body (half a day) | The last round in this batch. The woofer's place and the tweeter's (spec) are the owner's; the warm cast is the room's low sun by design. For a next pass: the window in frame or its patch on the wall, so the key has a source; the sun's colour less amber, so the carton keeps its red and white |
| 2026-10-05 | 04 back | v16 | 3 (refinement) | 4 | (1) level, dead on, long lens: a plain rectangle, no side panel, no gable end, on the centre line, read as a sign or a tabletop carton, the fold through the wordmark and the port; (2) one low light from camera-right throws a long shadow out of the left edge while the backdrop sinks to dark grey and the white body only reaches a flat light grey, so it looks stale; (3) flat planes with razor corners: the port a flat black disc with no tube going in, the terminals printed dots, the raised wordmark's grey sides like a drop shadow, the ochre label sticker or plate or veneer | Get off the front: swing 30 to 35 degrees so a side and the gable's end show, lower to port height, place it on a third (an hour) | The last round in this batch, and the fifth critic in a row to ask for the camera the brief rules out. For the owner: every round on this shot has scored the straight-on view itself; the three-quarter back view (r5-back-quarter in the explores) shows the same panel with the gable and a side, if the brief can allow it |
| 2026-10-05 | 05 five flavors | v16 | 3 (refinement) | 5 | (1) no real surface: edges that catch no light, each face one tone cap to base, nothing reading as board, lacquer or plastic, while the drivers have full contrast and hardware, so the boxes look like placeholders the drivers were dropped onto; (2) the wordmark fails on two units: white on Chocolate's cream band only a ghost of its shadow, white on Skim's pale blue barely legible; (3) head-on at mid-height, evenly spaced: the gable and fin read as two flat bands, the gutter lands on the middle unit | Round every edge a little, move the key about 45 degrees off the camera's line, a narrow strip on the far side, so each front falls off and each edge takes a line (an hour) | The last round in this batch. For the owner: the cast letters' polished faces read white on the light plinths (Chocolate's cream, Skim's pale blue), as two rounds have now said; a darker letter metal or a dark letter fill on light plinths is a design choice. For a next pass: the key further off the camera's axis, so the 4 mm edges (now joined) take a line |
| 2026-10-05 | 06 mixed crate | v16 | 3 (refinement) | 5 | (1) the light that throws the long shadow never shapes the product: the crate's right side and the cartons' right panels face away from it yet sit only a shade below their fronts, while the floor shadow beside them is half the sunlit boards, so the boxes look lit by another light than the room; (2) one clean material per colour: even bevels with no seam or grain, the crate an even matte with no moulded texture, all six drivers one glossy stock model; (3) the group straddles the centre line (a gutter through the white carton and the woofer below it) and the back row shows only as slivers above the front, so two rows read as one strip | Relight around one light with a believable origin: a large window light camera-left that shapes the boxes and casts the shadow, the fill that lifts the product but not the floor removed, a warm bounce on the right (an hour) | The last round in this batch. For a next pass: the desk room's cool fill and dome down so the shadow sides fall as far as the floor's shadow; the camera a touch higher so the back row's gables read; the drivers differentiated (the pint's are smaller, but one model scaled) |

### 2026-10-06: the owner's design points (v17)

The refinement batch had used its three rounds (v14 to v16). The owner then made four of the design points its critics raised (dark letters on the light plinths, a polished lip at the scoop, a three-quarter back view, Chocolate's throat run dark) and asked for an update based on the critics, so v17 is a new batch: round 1 again, at most three. v17 also carries round 3's render notes (the hero's sun on the fronts; the bright room's beam on the cabinet; a window patch in the older room; the close-up wider, its top light a strip, a card into the bowl; the line-up's key further round; the crate's fill down). Shot 04 now has two frames, a (straight on) and b (three-quarter, new).

Where it ended (v19, round 3, the last in this batch): 01 5, 02a 5, 02b 4, 03 5, 04b 5, 06 5; 04a stopped at round 1 (4) and 05 at round 2 (5), since what their critics asked for (a three-quarter camera) is what their briefs rule out. Round 1 was 4 to 5. The rounds found two real faults: a grey ring round every driver (the shader's eased edge rounding each hole's rim; v18 tucks the holes under the flanges) and the pints' edges eased at the floorstander's 6 mm, which made them look inflated (fixed in v20, rendered after the batch's last round). The owner's questions they raised are in the README's open questions: a reveal where the gable meets the body, whether the arrises may round the silhouette, taller crate windows, dark letters on the back, a narrower Facts table; and the tweeter, which still reads as an eye from off its axis.

| Date | Shot | Prompt v | Round | Score | Three gaps | Fix first | What changed after |
|---|---|---|---|---|---|---|---|
| 2026-10-06 | 01 hero pair | v17 | 1 | 5 | (1) read the room as lit by a low sun from the right (a hot patch on the right of the back wall, a bright pool lower right) while each cabinet's right panels are its darkest and the fronts lit flat as if by a softbox at the camera: the speakers dropped into a stock room (the sun was in fact front-left; its beam landing on the right read the other way); (2) every edge a sharp corner with no highlight, the white matte; the spout a saturated red hole nearly as bright as the roof, the tweeter jammed into its right end and half hidden behind the rim; (3) the two units pushed to the edges with equal weight, the centre going to a small chair against the wall, a spot no listener would sit in: no single hero | Put the cabinets and the room under one light: the floor pools, the long shadows and a tight contact shadow under each plinth from one source (an hour) | v18: the back wall 1.3 m behind the pair (was 2.5), so the low sun lays a band along its foot and each cabinet's shadow climbs into it, gable and all: the light on the fronts and the shapes on the wall are one sun; the window behind the camera nearly the wall's width, so the whole floor in frame is sunlit and only the shadows break it; less sky; the chair against the wall left of the left cabinet, out of the middle; edges 6 mm (were 4). The tweeter's place in the scoop is spec, seen 25 degrees off its axis |
| 2026-10-06 | 02a bright room | v17 | 1 | 5 | (1) a hard, low sunbeam runs across the boards to the speaker's right foot, yet the cabinet neither catches it nor casts a shadow from it, no long shadow from its base, only a thin contact line: pasted in (its long, thin shadow, cut by the narrow beam, did not read as its own); (2) the white a flat shader near pure white, front and side nearly one brightness while the plinth's faces differ, razor edges, no sheen; (3) the gable the least finished part: the tweeter off-centre in the oval and sunk below the lip; the fin a thick flat plank whose pale-pink top reads as a separate shelf | Relight so the speaker stands in the same sun as the floor: the beam on the cabinet, breaking across its front and side, throwing a long hard shadow, gable tip included (an hour) | v18: a French door in a wall closer still (x -1.7), the sun higher (30 degrees, 45 off the axis), so the beam is wide and the cabinet's whole shadow, gable and all, lies on the sunlit boards beside it; edges 6 mm, which also rounds the fin's top. The fin's 8 mm and the tweeter's place are spec |
| 2026-10-06 | 02b older room | v17 | 1 | 5 | (1) the speaker isn't standing in the room's light: the sun that throws razor-edged bar shadows on the wall never reaches it, its front lit dead even, its only shadow a broad soft darkening on the floor: golden-hour sun for the room and a softbox for the product; (2) knife-sharp corners and colour joints, no bevel catching light, the white one flat value: a clay model; (3) the spout tweeter a crushed-black lump against the right rim; the logo muddy grey-brown type at about 2:1 on the red band | Put the speaker in the room's sun: the raking beam across the cabinet and a long hard-edged shadow across the floor, the same way as the chair's (an hour) | v18: the back wall 0.8 m behind the cabinet (where a floorstander stands), the window narrower and down to the floor with one glazing bar, so the beam crosses the cabinet and its shadow, gable and all, climbs the wall inside the sun's patch beside the bar's: one sun for the room and the speaker; the chair moved into the shade at the left; edges 6 mm. The polished letters mirror a dark room, as metal does |
| 2026-10-06 | 03 bowl close-up | v17 | 1 | 4 | (1) too tight for a hero, too loose for a detail: the bottom edge cuts the white body, which melts into the grey sweep; the right side runs into the edge; the top quarter empty: an accidental crop, no scale; (2) the driver about 150 px wide, tucked under the top lip so the ring cuts across its housing, its black surround lost against the darkest maroon; the port on the centre line: at thumbnail size a lens or an eye in a red hole; (3) one broad soft light reflects across the upper left of the slope as a haze, dusty pink; the fin a second coral; the cavity orange-red as if lit from within; no shadow in the corner under the fin | Reframe: the whole carton on the sweep with a contact shadow, on a third; turn it until the port faces the lens enough for the cone to read (an hour) | v18: not the whole carton (the brief is the close-up), but its other half: back to the brief's gable height (0.97 m) and close, 25 degrees off the axis, so the mouth fills much of the frame and the camera looks along the throat at the tweeter, face on inside the lip, dome, surround, screws and seat ring readable; the fin across the top, the mouth left of centre; the top strip narrower and further, a line rather than a haze; edges 6 mm |
| 2026-10-06 | 04a back, straight on | v17 | 1 | 4 | (1) level with mid-height and square to the face: the gable a flat red cap, no side or depth, dead centre filling a fifth of the width, a packaging elevation, OPEN OTHER SIDE pointing at a side never seen; (2) one low key from the right over a mid-grey sweep: the white about the empty floor's value, no highlight, the amber label underexposed, the long dark shadow wedge out of the left edge the largest dark shape; (3) one matte shader, knife edges, no change of sheen; the port a flat black disc with no depth | A three-quarter from the front right, down about 15 degrees, a longer lens with shift, the carton on the right third (an hour) | Not the camera: frame a is the straight-on back the brief asks for, kept beside the three-quarter frame b (the owner, 2026-10-06), which is this fix. No v18 of frame a |
| 2026-10-06 | 04b back, three-quarter (new) | v17 | 1 | 4 | (1) every edge perfectly sharp, every surface one flat near-matte finish, the front-to-side corner a ruler line where a highlight should be: an untextured mockup; (2) the floor meets the grey backdrop at a hard horizon halfway up the frame, behind the middle of the carton; a near-white patch of light on the empty floor at the right edge as bright as the carton's white face; (3) the port a flat black disc, the terminals plain caps on a black tile with no metal or shine: stickers on a box | One surface pass: round every edge 1.5 to 3 mm and give the white and red a satin coated finish with a little shine and roughness variation (an hour) | v18: the sweep turned to face this camera, so its curve no longer reads as a horizon; the key 35 degrees off the back face (was 50), so the back takes more of it than the side, and gridded (55 degrees), so its spill no longer pools on the empty floor and bounces onto the shaded side; edges 6 mm. The finish is already a satin lacquer with a clearcoat and orange peel |
| 2026-10-06 | 05 five flavors | v17 | 1 | 4 | (1) a broad wash from the front: the white fronts one flat value, the sides barely darker, knife edges, the only floor shadow a soft smudge with no contact line: cutouts before a backdrop; (2) the drivers sit flush inside an even dark ring (a grey halo on the white fronts, a muddy brown one on Chocolate) that behaves like a drop shadow with no offset: stickers (a real fault: the shader's eased edge rounded each hole's rim round its driver); (3) five equal units evenly spaced, straight on from mid-height: the gable a coloured cap, the triangular side profile hidden, no hero or depth, the gutter through the middle carton | Relight: one large soft key high and 45 degrees camera-left so front, side and gable slope each take a value, a strip rim from behind, a real contact shadow under each base (an hour) | v18: each driver's hole in the finish now 5 mm inside its flange (10 % on the pint), so the flange covers the cut edge and the halo is gone, in every shot; the key's softbox 1.0 m (was 1.6), for a tighter shadow and contact line; the strips back behind the row's sides (125 degrees off the camera's line) and up, a rim on every silhouette; edges 6 mm. The camera stays straight on, the row parallel and the five the same size (the brief). The letters on the light plinths read now (the owner's dark bronze) |
| 2026-10-06 | 06 mixed crate | v17 | 1 | 5 | (1) the chrome-ringed ovals open holes into an unfinished cavity, the inner wall lit in a crescent and a dark ball floating to one side: half-closed eyes with pupils, faces before speakers; (2) the three drivers behind the crate's windows about 1.6 times the cartons' own and filling their windows almost edge to edge: a crate subwoofer with carton satellites, or six cartons each hiding a bigger driver? (they are the front pints' woofers, the mids standing above the rim); (3) cartons, fins and crate one untextured satin with one soft edge: soap bars and a CAD primitive | Close off the ovals with a matte black tube or backplate, or make the cavity black (minutes): not taken, the bowl is the waveguide, painted by the spec | v18: the camera higher again (about 20 degrees down), so all six read, not three faces and three rooftops; the drivers' halo fixed (see 05); edges 6 mm. For the owner: the crate's windows (spec since 2026-10-05) frame each woofer with 2.5 mm to spare; taller windows that also showed the plinths would say whose woofer it is |
| 2026-10-06 | 01 hero pair | v18 | 2 | 5 | (1) nothing in the room seems to cast the carton shadow on the wall: its floor part fades before reaching either cabinet, and the cabinets, lit hard from the front, cast nothing across the boards and have no contact shadow under their front edges: a shadow nobody casts, cabinets hovering; (2) each white front one flat value, knife corners; the sun band on the wall starts at the gable line, so the left edge sits against a wall about 4 % darker; (3) the hero within 7 % of the right edge, the centre bare wall; the chair's leg running along the left cabinet's edge, fusing them | Re-light round one sun from front-left so the wall silhouette becomes the left cabinet's own shadow running across the boards and up the wall, with contact and cast shadows for both (an hour) | v19: the room 3.0 m high and the window to 2.95, so the sun stands at 19 degrees (was 15) and lays more light on the boards, each cabinet's shadow running dark from its plinth to the wall; less sky; the floor less glossy (0.52); the walls a warm grey, so the white cabinets stand off them; the chair clear of the left cabinet's edge; the frame a little wider and centred further right, the hero off the edge |
| 2026-10-06 | 02a bright room | v18 | 2 | 5 | (1) the tweeter against the right end of the cut-out, half hidden by the rim, no mount visible: a webcam lens, a slipped part; (2) a flat white box, knife corners, no finish to name, hard joins between gable, body and band; (3) the low sun shapes the floor, not the speaker: the face lit evenly, the shaded side nearly the wall's pale grey, the strongest light on empty boards | Re-seat the tweeter inward until the cut-out frames it, with a mounting ring and a shadow inside (under an hour): the throat's place is spec | v19: the camera more frontal (about 18 degrees off the axis, was 25; shared with 02b), so the tweeter sits inside the scoop's opening; the walls a light warm grey, so the shaded side separates from them. The light stays (the cabinet's whole shadow now lies on sunlit boards) |
| 2026-10-06 | 02b older room | v18 | 2 | 4 | (1) the silhouette on the wall attached to nothing: no shadow crosses the boards from the plinth to the skirting, only a soft contact shadow: the speaker hovering, a second carton suspected; (2) the cabinet seemingly lit by a neutral product light: front and side within a few values, no warm cast, the only sun a hot sliver at the plinth's corner (measured: the front 226 against the side's 185, in the sun but only faintly warm since the last batch asked for less amber); (3) knife corners, flat fills, the woofer's rim on the white-to-red break, a near-black wordmark muddy on the red | Rebuild the light round one physical sun: the cabinet fully in the beam that paints the wall, front warm, the shadow unbroken from the plinth across the boards and up the wall (an hour) | v19: the sun higher (18 degrees, was 10) and a touch warmer, the window wider and taller, so the whole cabinet stands in the beam, the sunlit boards are bright enough to show its shadow running from the plinth to the wall, and the silhouette still climbs the wall beside the bar's; the camera as 02a |
| 2026-10-06 | 03 bowl close-up | v18 | 2 | 5 | (1) inside the oval the left 60 % a murky maroon with no readable floor or wall; the driver with no visible flange or contact shadow, a milky smear under its rim: a stock part hovering in a hole; (2) a shapeless diagonal wash bleaching the lower-left half of the red and the fin's end to salmon, saturated red only in the right third, no grain; (3) the white body the backdrop's flat light grey, front and side one value, knife edges, its right silhouette sinking into the backdrop | Relight: one overhead softbox, biased left and flagged, reflected as a defined band beside clean saturated red; a strip from camera-right for the planes; a small card into the port (an hour) | v19: a mid-grey set, so the white body stands off it and bounces less into the sides; half the environment, so the slope keeps its red beside the strip's band; the card into the bowl brighter and aimed at its far side; the tweeter's seat ring satin metal, a mount that reads (black, it vanished against the faceplate) |
| 2026-10-06 | 04b back, three-quarter | v18 | 2 | 4 | (1) the key blows the back face to nearly clipped white and leaves the side an even grey, no falloff, a long low shadow through the empty half; (2) sharp edges, one untextured material, the port a flat black disc with no tube wall; (3) the Facts plate a muddy ochre block with low-contrast type; the wordmark close above it; the terminal plate on the white-to-coral line (both spec) | Relight: the key down a stop with falloff, a large softbox front left, a bounce for the side, a thin rim from back right, the key higher so the shadow falls short and behind (an hour) | v19: the key a stop less, a 1.2 m softbox (was 0.7) and higher (50 degrees, was 35), so the face falls off top to bottom and the shadow falls short and behind; the fill from the camera's side up as a bounce for the side; the strips up for a rim; the reflector brighter, so the plate reads as metal |
| 2026-10-06 | 05 five flavors | v18 | 2 | 5 | (1) dead-on at mid-height: the gable a coloured stripe, the sides slivers, flat drawings with no depth or scale; (2) knife edges, one matte, the drivers copied box to box; (3) five identical units at identical intervals, the middle on the centre line, half the frame empty grey: a swatch strip, no hero, no copy space | A three-quarter view about 30 degrees off the row's line, the row receding, the nearest carton the hero (an hour) | No v19: the brief holds this shot straight on, the row parallel and the five the same size, and that is what this critic scored; the halo and the contact shadows were the round's fixes (4 to 5). The batch ends here for 05 |
| 2026-10-06 | 06 mixed crate | v18 | 2 | 5 | (1) the windows barely larger than the woofers, set back behind the wall, so from this raised camera they crop the cones unevenly (each surround under the window's top and right edges, a crescent of carton at the left): a fit error; (2) one satin and one soft edge for cartons and crate; the white carton the crate's off-white, barely separating; (3) the hardest contrast the long shadow on the empty right, the crate's shaded side nearly as pale as its front | Fit the woofers to the crate: each flush in its window with a dark baffle round it (an hour): the windows are spec | v19: the pints closer to the crate's long walls (rows 136 apart, 3 mm from each wall, were 124 and 9), so the woofers sit just behind their windows and the raised camera barely shifts them; the camera a little lower (about 18 degrees); the crate's white a shade deeper, so the white pints stand off it; the fill and dome down, so the shaded side falls |
| 2026-10-06 | 01 hero pair | v19 | 3 | 5 | (1) the cabinets bare primitives: dead-sharp edges, no reveal or shadow line where the coral roof and plinth meet the white body (a change of colour, as if painted on one block), the white flat and grainless: beside drivers with trim rings, screws and glossy caps, a placeholder; (2) fronts, sides and the sunlit cream band on the wall in one narrow range of near-white, the outlines soft (the right cabinet's left edge barely separating): cut-outs, the eye going to the cones and the wall shadow; (3) the darkest, sharpest shape the carton shadow on the wall, alone in the middle a fifth of the frame from the left cabinet that casts it, the two equal cabinets at the outer thirds: an empty middle, a ghost carton to work out, no hero; the gutter down the shadow's left edge | An edge-and-joint pass: round every edge 2 to 3 mm, a hairline reveal where roof meets body and body meets plinth (an hour) | The last round in this batch (5, 5, 5). The plinth's 3 mm shadow line is in the model (spec) but spans two pixels at this distance; the gable has none. For a next pass: a strip at each lit corner's mirror angle, so the 6 mm rounding takes a line (it is shaded, and the silhouette stays sharp by the render rules); the wall a step darker than the white, so the outlines hold. For the owner: a reveal where the gable meets the body, asked for in this batch and the last |
| 2026-10-06 | 02a bright room | v19 | 3 | 5 | (1) no material: the front one flat near-white from roof to band, the side one flat grey, knife edges, no sheen, grain, print or crease: the least physical thing in the room after the boards and the chair, a mockup whose weight and price can't be guessed; (2) the sun lights the room, not the product: its hard patches on empty floor and the chair's seat, the cabinet an even wash with no gradient or stripe of window light, the strongest shapes pulling the eye to the empty lower right; (3) the tweeter reads as a camera: a glossy black dome in a bright ring right of centre in the slot, in a cavity glowing hotter and redder than the roof: a webcam watching you (it is on the centreline, 170 back; off its axis it slides to the slot's end) | A real finish: round every edge 2 to 3 mm, a satin paint with a little variation in its shine and a faint fine texture, so the sun draws a line down each corner and the faces take a sheen (an hour) | The last round in this batch (5, 5, 5). For a next pass: a line on the corners (see 01); the door's glazing bars across the beam, so the sun draws on the cabinet as it does on the floor. For the owner: the tweeter at the back of its throat (spec) has read as an eye or a lens in most rounds since v14, from every angle off its axis |
| 2026-10-06 | 02b older room | v19 | 3 | 4 | (1) the key acts like a lamp two metres off, not a low distant sun: the cabinet's shadow on the wall a squat block about twice its width though it stands well off the wall (a sun 50 degrees off the wall's normal does widen it so), the white front near clipping and nearly neutral while the wall goes amber: dropped onto a lit set; the gable's shadow reads as a house; (2) still a blockout: sharp corners, no highlight line, flat paint, no seam where white meets red, a generic wordmark in muddy brown dying on the red; (3) no room for crops or a gutter: the cabinet three-quarters of the frame's height, its base about 7 % and its wordmark about 10 % above the bottom edge, its right edge 2.5 % left of the midline, a half-cropped dark chair against the left edge | Relight with a true sun: a distant key at the same low angle through real window geometry, the white a stop below clipping, the wall shadow true to the cabinet's proportions, the white pulled into the room's amber (an hour) | The last round in this batch (5, 4, 4). The shadow is a true sun's, so it reads wrong rather than being wrong. For a next pass: the sun nearer the wall's normal, so the shadow keeps the carton's proportions; the exposure set off the white, a stop below clipping, so it keeps the sun's warmth (the view transform takes a near-clipped warm white to neutral); the frame wider, with floor under the plinth and the chair whole or out |
| 2026-10-06 | 03 bowl close-up | v19 | 3 | 5 | (1) the driver seated in nothing: face on inside a mouth foreshortened to a thin oval, no baffle or back wall to bolt to, no occlusion where its flange meets the red, a pink halo off its right rim, a white smear under its lower left: a sticker in a red void, a smudge like dirt on the lens (the smear is the front card mirrored in the bowl's gloss); (2) the red doesn't hold: a broad soft light washes the left half of the roof and the fin to salmon, palest at the lower-left eave, the right half tomato: red or pink? faded plastic; (3) nothing manufactured: the fin's top, the roof's edges and the eave knife-sharp, the white an even untextured grey: CAD geometry | Re-seat the driver: the baffle it mounts to at the back of the cavity, an occlusion shadow round its flange, re-rendered clean of the halo and the smear (an hour) | The last round in this batch (4, 5, 5). For a next pass: the front card below the bowl's mirror angle (or flagged), so the gloss shows no smear; the top strip's band kept to the right half of the roof, so the red holds on the left; the throat's walls lit, so the tube from the mouth to the seat ring reads and the tweeter sits at its end; a line on the corners (see 01) |
| 2026-10-06 | 04b back, three-quarter | v19 | 3 | 5 | (1) where floor meets wall a bright arched horizon (near-white floor below, mid-grey wall above), peaking just right of the carton at the label's height and running out both edges at mid-height: a 3D app's default backdrop, its hard edge cutting the empty right half where a headline would go; (2) two flat tones, an even white back and a flat grey side meeting at a razor corner, no rounded edge to catch light, no sheen or grain: a CG box wearing stickers; (3) the label laid out like a first draft: each value about half a line below its label, so the table reads staggered (the rows share a baseline; the fall is the face's perspective), the wordmark almost on the panel's top edge, the terminal plate running into the red band (both spec) | Rebuild the backdrop: the curve and the horizon out of frame, one large overhead source so floor and wall shade into one gradient, the right half an even field about a stop under the white (an hour) | The last round in this batch (4, 4, 5). Turning the sweep (v18) took its curve off the carton but left it across the empty half, lit by the key's spill. For a next pass: the camera lower or the lens longer, so the curve sits behind the carton or out of frame, and the floor a stop under the white; a line on the corners (see 01). For the owner: at this angle the right-aligned values read as one row low; a narrower table, the values nearer their labels, would hold the rows together (the panel's layout is spec) |
| 2026-10-06 | 06 mixed crate | v19 | 3 | 5 | (1) cartons and crate smooth flat-coloured plastic with an even sheen, every edge the same soft round: the bodies inflated, the fin a fat rolled bolster, not a folded strip: squeezable, a vinyl toy or a placeholder (a real fault: the path tracer eased the pints' edges by the floorstander's 6 mm, which on a 100 mm carton with a 2 mm fin rounded the corners and the whole fin); (2) all six drivers one generic unit at two sizes, the small ones on the faces with no recess or gasket, the woofers nearly filling their windows, frames almost touching the right and bottom edges: in a warm low-contrast frame the strongest marks, a parts bin; (3) one hard warm sun the only light: every front one flat value, the shaded sides darker orange with no cool fill; the cast shadow off the right edge a dark striped slab with a stray bright wedge at the border; the spread's fold through the right-hand woofer; cartons and crate not separated from a warm room with no skirting | Rebuild the edges and surfaces: crisp creases, the fin with real sheet thickness, one material with fine texture and varied gloss (a day) | The last round in this batch (5, 5, 5). The inflated edges were a real fault, now fixed: v20 eases the pints' edges at their own scale (1.5 mm; the path tracer's radius now scales with each shot's cabinets), so the corners and the fin are crisp; rendered, no critic round. The drivers' sizes and the windows are spec. For a next pass: a cool fill from the room's side, so the shaded sides fall cooler than the sun's; the frame wider on the right, so the crate's shadow ends inside it |

### 2026-10-07: the Nutrition Facts printed on the body (v20 of the back)

The owner moved the Facts off the bronze plate and onto the body, printed under the clear like a carton's panel. A change to the printed look, so the back starts a new count: round 1 again, at most three. The other shots are unchanged by it. From this batch on, each image goes to its critic under a neutral file name, as `.claude/skills/critic-round` says; in the v17 batch's round 3 the critics were given the repo paths, which carry the product's name.

| Date | Shot | Prompt v | Round | Score | Three gaps | Fix first | What changed after |
|---|---|---|---|---|---|---|---|
| 2026-10-07 | 04a back, straight on | v20 | 1 | 4 | (1) a flat front view parked dead centre, level and square at mid-height: no side, the gable a slight taper, a standee or a dieline; the spread's fold through the product; (2) the white a light grey barely above the floor: the key off to the right lights the hidden side and grazes the face, razor corners, matte, no highlight; (3) the port a solid black disc with no tube wall; the post plate's bottom edge touching the shadow line above SHAKE WELL; fingertip-sized posts the only scale cue, so the cabinet reads a foot tall beside a label listing a 12 in woofer | A three-quarter from slightly above, turned 30 degrees, 85 to 100 mm, the label face brightest and the side a stop down, the carton on a vertical third (an hour) | Not the camera: the straight-on back is this frame's brief, and frame b is the three-quarter (the owner, 2026-10-06). The printed Facts drew no note; the plate's position over the shadow line is spec |
| 2026-10-07 | 04b back, three-quarter | v20 | 1 | 5 | (1) the light on the set: the bare floor beside the cabinet almost as bright as its front, the left edge fading out from the label down, the front one even white, the light pool's edge a hump-shaped horizon behind the cabinet at label height; (2) every edge a sharp corner, every panel one plain matte, no highlight line, sheen or reflection: the label and band copy read as stickers; (3) the printed face points at the near left edge, so the empty right half (the copy space) faces the blank side; the verticals lean in from the camera's tilt | Relight: the key off the floor, the ground a stop under the front, the sweep re-angled so the pool's edge leaves the frame, the key feathered top to bottom (an hour) | Round 1 of the printed look; the next pass is the owner's call (the 10/10 plan of 2026-10-07: edges, light per shot, composition). The copy reading as stickers is the matte look: printed under the clear it takes the finish's sheen, which this light does not show |

### 2026-10-07: the owner's geometry (v21 on)

The owner asked what it would take to reach 10/10 and chose three geometry changes: no lip at the scoop, the tweeter's ring and seat moulded black; the cabinet's vertical corners and the gable's hips rounded 3 mm in the model (the fin's edges 1.5); a 3 mm shadow line where the gable meets the body, like the plinth's. Then OPEN OTHER SIDE moved onto the fin's back face and the back's letters centred between the edge and the Facts. A new look, so a new count: round 1 again, at most three. Round 1 is every shot at v19's light and camera with the new geometry (v21); round 2 (v22) is light and composition per shot; round 3 is finishing. Every image goes to its critic under a neutral file name.

Where it ended (v23, round 3, the last in this batch): every frame at 5 but the crate at 4; 02b reached 6 at round 2 and fell back to 5. Round 1 was 4 to 5. In every shot the critics' asks converged on the same few things: edges that catch light, a finish they can name, drivers that look fitted rather than stock, and the tweeter, which from any camera off its axis sits at the right end of its scoop (it is at the back of the throat) and reads as an eye or a lens. Round 2 changed the sets and cameras; round 3 the finish: a colour coat with no gloss of its own under a full clear, edge lights seen only in reflections, AgX's very high contrast look in the studio. Found and fixed on the way: the crate's first round-2 final cut its left end (caught before its critic); the gloss roof mirrored the fin's OPEN OTHER SIDE upside down beneath it in the straight-on back (re-shot from 1.3 m; a sliver remains). At room distance the 3 mm rounds are two pixels, and no critic saw them as anything but sharp. The finish changed once more inside round 3: 03 and 04b (and a first 04a) were rendered while the colour coat still had a faint broad gloss of its own, and their edge lights lit the faces too; the rest render the colour coat matte under the clear, with the edge lights seen only in reflections (a container restart stopped the batch between the two, with nothing lost). The owner's questions from these rounds are in the README.

| Date | Shot | Prompt v | Round | Score | Three gaps | Fix first | What changed after |
|---|---|---|---|---|---|---|---|
| 2026-10-07 | 01 hero pair | v21 | 1 | 5 | (1) sharp-edged boxes in flat white and coral, no edge highlight or sheen, front and side almost one white: blockout geometry, no telling wood, plastic or card; (2) the drivers generic library parts (glossy black cones, grey rims, a busy ring of tiny screws) sitting on the baffle like decals; the tweeter a small disc at the right end of the spout, too small at homepage size; (3) the frame's centre a shadow on a blank wall, the pair in the outer thirds, the top quarter empty wall, a cut-off chair almost touching the left cabinet: neither speaker owns the image | Bevel every edge about 2 mm and a satin lacquer with some variation, so each box shows a lit edge (an hour) | v22: the camera further round (36 degrees) and closer at the brief's 1.2 m, level; the back wall 2.5 m behind the pair (was 1.3), so no carton shadow climbs it and the centre is the sunlit boards with the far cabinet's shadow running back across them; the sun 20 degrees off the axis; the chair whole at the left; the card and the exposure down, so each side falls well below its front |
| 2026-10-07 | 02a bright room | v21 | 1 | 5 | (1) the white front an almost even, almost blown-out plane, every edge sharp: a box with a default material or a foam mock-up; (2) the tweeter a glossy black dome half-hidden under the slot's lip with one pinpoint highlight: a camera lens, the carton seems to watch the room; (3) the sun hard on the floor only: no patch climbs the back wall, the chair throws no shadow onto it though it stands in that sun: the light painted on the floor | Round every edge 2 to 3 mm, a satin lacquer with some variation in roughness, the exposure down until the front keeps detail (an hour) | v22: b's camera (the brief's one camera for both frames: wider, level, the cabinet on the left third); the sun lower (18 degrees) and further toward the front (40 off the axis), so its beam lays a patch on the back wall behind the chair and the chair's shadow climbs it; the exposure down |
| 2026-10-07 | 02b older room | v21 | 1 | 5 | (1) every edge knife-sharp with no highlight line, the panels even fills: the low sun that cuts crisp shapes into the wall finds nothing on the speaker; (2) generic glossy cones in screwed trim rings, the woofer's ring near the band [spec], the wordmark muddy brown-grey [polished letters mirroring a dark room]; (3) the carton's silhouette inside the window-bar pattern, its edge running into a bar's shadow; the cabinet three-quarters of the frame with no floor under it; the chair a dark half-object cut by the edge | Bevel every edge about 2 mm with enough segments to hold a highlight (under an hour) | v22: the glazing bar moved, so its shadow falls clear of the silhouette; a wider, level frame with floor under the plinth, the cabinet on the left third and its silhouette on the right; the chair out of frame |
| 2026-10-07 | 03 bowl close-up | v21 | 1 | 4 | (1) one huge edgeless reflection turns the left half of the roof and fin dusty pink, fin and slope sharing one gradient: what colour, gloss or matte; (2) the driver has nothing to sit on, a pale smear below it with no light to explain it [the front card mirrored in the bowl's gloss], right of the oval's centre with nothing to say why [spec]; (3) the frame cuts the roof's front-left corner and the body, no floor: no sense of size | Relight: a narrow strip softbox high on the left, its reflection one defined band across the slope (an hour) | v22: the key a narrow strip, so the gloss carries one defined band; no edge strips; the card lower and softer, out of the bowl's mirror angle; the bowl's paint flatter (roughness 0.62, no clear); the camera back a fifth, so the gable's outline is whole; an edge light on the near hip |
| 2026-10-07 | 04a back, straight on | v21 | 1 | 5 | (1) level, square-on, dead centre: a flat print of the box, the product in the gutter; (2) no true white, the body about the floor's grey; the strongest contrast the long dark shadow off the left edge; (3) knife-sharp edges, the port a flat black disc with no tube wall, the wordmark raised with a drop shadow | A three-quarter from a little above (an hour) [the brief holds this frame straight on; frame b is the three-quarter] | v22: the three-quarter's set: a broad soft key higher on the camera's right, so the back is the brightest thing in frame, a stop above an even grey floor, and its shadow falls short; a level camera; the key's angle reaches into the port's tube |
| 2026-10-07 | 04b back, three-quarter | v21 | 1 | 5 | (1) the backdrop lit by a pool with an oval edge, a horizon or a spotlight behind the carton at the Facts' height; (2) shaded like a basic 3D shape, the front-to-side corner a hard cut, each face one tone [3 mm rounds, about 2 px here]; (3) nothing says speaker at a glance: the port a flat disc, the black post lost on its plate | Relight: kill the pool, light the backdrop on its own, a large soft key from the left with the front a step darker toward the base, a thin edge strip (an hour) | v22: the whole set mirrored, so the camera stands back-right and the printed back faces the empty right half; a level camera with lens shift; the floor a step darker and the backdrop lit on its own, no pool or horizon; a broad, ungridded soft key across from the camera |
| 2026-10-07 | 05 five flavours | v21 | 1 | 5 | (1) dead-on, the light from about the camera: every front one flat tone, the gable's triangle never shows; (2) the drivers one generic part repeated ten times, each woofer nearly 80 % of the front [spec]; (3) an unexplained darker patch on the backdrop; the floor nearly white, no contact line | Turn each unit 30 degrees, the camera above the gables, the key high camera-left (an hour) [the brief holds this shot straight on, the row parallel] | v22: the studio set of the backs (a darker floor, the backdrop lit on its own); the key high and further left, so each front falls off across its width and the slopes take more than the fronts; a smaller softbox for a contact line; a level camera; still straight on |
| 2026-10-07 | 06 mixed crate | v21 | 1 | 5 | (1) every carton panel one flat colour with knife-sharp edges [the pints' rounds are 0.77 mm, the floorstander's 3 mm scaled]; (2) the roof holes show the lit inside of an empty shell [the bowl's floor; no lip since the owner's choice]; (3) all six drivers one stock model, the woofers nearly filling their windows [spec]; the spread's fold through the red-roofed pint and a woofer | Round every edge 1 to 2 mm, wall thickness at the roof holes (an hour plus render) | v22: the camera back and the frame moved right, so the whole crate sits on the left page with room beside it (a first final at 0.68, 1.42, 1.84 cut its left end, caught before its critic and re-rendered); the cool fill onto the shaded side |
| 2026-10-07 | 04b back, three-quarter | v22 | 2 | 5 | (1) no real edges or depth: sharp corners, the white, red and plate one flat matte, the port a solid black ellipse in a thin grey ring with no tube wall: a black sticker; (2) one big soft light does all the work: no specular, almost no falloff down the face, the white only light grey, the backdrop taupe to putty: a narrow band of midtones, dim and stale; (3) the back and a blank side only: no driver, no scale [the shot's brief] | Round every edge 1 to 2 mm and a satin lacquer, so the light draws a highlight down each corner (an hour) [the corners are rounded 3 mm; about 3 px here] | v23: the finish a flat colour coat under a full clear, so the gloss is the clear's and mirrors a light as a shape; AgX's very high contrast look and the exposure up, so the white reads white over a darker set; edge lights on the near corner and the near hip; the port's tube a real black plastic's 3 % (was 1 %), so its wall shows |
| 2026-10-07 | 03 bowl close-up | v22 | 2 | 5 | (1) the scoop's left half a crushed near-black oxblood, the driver's flange running into the curved wall with no seat and no shadow: a dark hole, the driver dropped in; (2) the brightest value the near-blown reflection across the fin's left half over a flat tomato slope: two plastics glued together; (3) the crop a default: the body cut halfway, its left edge 40 px from the frame, the bottom quarter dull grey body, no scale | Relight: the softbox off the fin, an overhead strip whose reflection runs down the slope as one graded highlight, a fill into the scoop (an hour) | v23: the key higher (25 up, 32 off the axis), out of the fin's mirror angle and still inside the tweeter's view, a shorter strip; an overhead strip where the slope mirrors it, along the fall line beside the mouth; the card into the scoop's left wall; the frame centred on the gable, less body; the finish's new clear |
| 2026-10-07 | 04a back, straight on | v22 | 2 | 5 | (1) dead centre at mid-height, one face, the roof a red stripe [the brief]; (2) the white one even light grey, razor corners with no highlight, no change across the face; (3) the roof shinier than the body and mirroring the fin's OPEN OTHER SIDE as a blurred, upside-down ghost: a misprint or a render glitch where the eye lands first | A raised three-quarter (an hour) [frame b is the three-quarter; the brief holds a straight on] | v23: the ghost gone with the finish's new clear (it was the colour coat's own broad gloss catching the fin); the very high contrast look and the exposure up; an edge light on each vertical corner of the back |
| 2026-10-07 | 05 five flavours | v22 | 2 | 5 | (1) the whites dull light grey, barely brighter than the sweep and colder, front and side hardly different, no tight contact shadow: dingy, weightless; (2) a dome inside the red, blue and light-blue ports, an empty black hole in the brown and tan ones: pupil, pupil, pupil, hole, hole, two models, and the domes a staring eye [Chocolate's throat dark, the owner's choice]; (3) the wordmark's dark sides a heavy offset shadow, muddy on the light bands: WordArt | Relight: a large key high and 45 degrees round, a small light above and behind for the gables, the exposure up to just below clipping, the sweep a stop darker, a contact shadow at each base (an hour) | v23: the very high contrast look and the exposure up; the set half a stop darker, its own light down; the key's softbox smaller and the fill down, for a contact line; the finish's new clear. Still straight on (the brief) |
| 2026-10-07 | 02b older room | v22 | 2 | 6 | (1) the speaker not lit by the wall's sun: its front and shaded side one step apart, the white a pale off-white beside the wall's amber patch: lit on a separate set and pasted in; (2) the carton's shadow on the wall 1.5 times the speaker's width: a projected cut-out [the sun strikes the wall about 50 degrees off its normal, which stretches it; right, but it reads wrong]; (3) the surface stops at the bare model: sharp edges, no sheen; the woofer almost touching the band [spec] | One real sun through the window doing all the work, the sunlit faces amber, the shaded side bounce only (an hour) | v23: the sun a deep late-day amber and the exposure down, so the white front takes the sun's colour as the wall does instead of rolling off to white; the lamp at the right down, so the side falls to bounce; the finish's new clear |
| 2026-10-07 | 02a bright room | v22 | 2 | 5 | (1) shaded like a default primitive: sharp corners, the white front one flat value with no sheen, the red flat and chalky pink on the fin: the floorboards carry more surface than the product; (2) the sun has no punch: the wall's patch pale cream, not hot, the shade the same warm taupe as the sun, the cabinet's shaded side a step below its front, the sharpest light-and-shadow shape the chair's: hazy CG, a cut-out; (3) the tweeter against the right end of its cut-out, off the line the mid and woofer share [parallax: it sits at the back of the throat on the centre line], the cut-out an unlit black hole | One surface pass: bevel every edge 1.5 to 2 mm, a satin lacquer with a faint clear that picks up the window (an hour or two) | v23: the finish a flat colour coat under a full clear; the sun stronger and a warm white, the sky outside the door and the fill inside it blue and the fill down, so the patches go near white and the shade cool; the exposure down |
| 2026-10-07 | 01 hero pair | v22 | 2 | 5 | (1) every edge a sharp corner, every face one flat colour with no sheen, so the low sun never draws a highlight line: a clay mock-up; (2) on both units the driver wedged against the right end of its slot, the rest an empty red scoop [parallax: the tweeter sits at the back of the throat on the centre line]; (3) the light goes to the room: the strongest light the sun's band on the back wall right behind the near unit, its white melting into the cream wall and white skirting, its front and side almost one white; the two units' wordmarks unlike (one flat white, one coral on coral) | Round every edge about 2 mm so the sun draws a line along each corner (30 minutes) [rounded 3 mm; two pixels here] | v23: the window's head 0.2 lower, so the sun reaches the back wall only at its skirting; the walls and the skirting a deeper warm grey; an edge light on each near corner, seen only in reflections, so the round draws a bright line without lifting the faces; the finish's new clear |
| 2026-10-07 | 06 mixed crate | v22 | 2 | 4 | (1) the desk the loudest thing in frame: more than half the image, neighbouring boards jumping hard between dark and light, stubby, an even grain: a game asset that says CG; (2) the product a sixth of the frame, parked left, the wall line touching a carton's eave and grazing the crate's rim, the long spiky shadow the biggest shape: small, flat, pinned to the backdrop; (3) a blockout: flat cartons with no folds or seam [the lacquered pints have none, by the spec], the crate a putty tub, the stock drivers crammed into windows barely wider than the cone [spec] | Reset the camera: down to the cartons' shoulders, 85 to 100 mm, in until the crate fills half the frame, the wall line behind the product (under an hour) | v23: the camera lower (12 degrees down) on 100 mm and in close, the crate half the frame, the wall line behind it; a spread's fold between two columns of pints and two windows; the desk's boards twice as long, their tones closer; the finish's new clear. (Lower still would hide the back row, which round 1 of the v17 batch asked to see) |
| 2026-10-08 | 03 bowl close-up | v23 | 3 | 5 | (1) the driver mounted to nothing: the scoop wall around it crimson on the left, orange-red on the right, no contact shadow where its rim meets the wall, its top edge touching the opening's rim [the throat's end, 25 degrees off its axis]; (2) one soft highlight streak on the left of the slope and nothing else, the scoop's top edge a hard cut, the white body an even light grey; (3) the crop cuts the carton at the bottom and leaves about 2 % of background at the right, a quarter of the frame empty above the fin, no floor or scale [v23 shifted the frame to clear the left edge and overshot] | Seat the driver: a flat mounting ring with a rounded edge into the scoop wall, a contact shadow, its top clear of the rim (an hour plus render) | The last round in this batch: no further render |
| 2026-10-08 | 04b back, three-quarter | v23 | 3 | 5 | (1) every edge razor-sharp, the gable end a flat triangle with no fold creases, the white and red one even matte, so the key puts no highlight on the body [the edge lights here were the first, faint version, lit diffusely; see 01]; (2) the hardware not built: the port a flat black disc in a chrome ring with no tube wall, the post plate flat with no cup, flange or screws, its bottom edge on the line where white meets red; (3) the Facts values thin, pale grey, lighter than the rules, soft; a 12-inch woofer claimed on a box the posts size at under a foot | A surface pass: bevel every edge a millimetre or two, a satin finish with roughness variation (an hour) | The last round in this batch: no further render |
| 2026-10-08 | 05 five flavours | v23 | 3 | 5 | (1) a broad, nearly frontal light puts one flat value on every front, the white a dull light grey, the corners catching no highlight, the cones near-black with a pinprick on each cap: an untextured mock-up [the edge lights cannot reach the inner corners past the neighbours]; (2) the wordmark deep extruded type under a heavy dark offset: dark letters on the light bands a smudge, pale ones on red and blue a dated drop shadow [the cast letters' 2.5 mm sides]; (3) dead level and centred, the gables a band, the gutter through the middle carton [the brief holds it straight on]; Chocolate's and Oat's ports empty holes beside the others' domes | Relight with edges to catch: bevel, a large soft key high at camera-left falling off down the fronts, a strip across every cone and dome, the whites read white (half a day) | The last round in this batch: no further render |
| 2026-10-08 | 06 mixed crate | v23 | 3 | 4 | (1) a default room under one hard sun: the orange desk meeting a blank greige wall at a hard seam, the crate front and carton faces one flat value, the long dark shadow leaving the frame at the right, the desk and wall too close to Chocolate's and Oat's colours; (2) every surface an unbevelled fill: sharp carton edges, flat primary roofs, no folds, seams or print [not on the lacquered pints, by the spec], the crate front one smooth plane; the red-roofed white pint reads as a house icon; (3) the woofers filling their windows edge to edge [spec], the mids the woofer scaled down, the roof openings thin lozenge cuts with no depth: tissue-box slots | Relight on a neutral set: a sweep or a pale tabletop, a large soft key high at front-left, a rim from back-right, a soft contact shadow (an hour) | The last round in this batch: no further render. (It wants the camera high enough to show all six; round 2's wanted it at the cartons' shoulders) |
| 2026-10-08 | 02b older room | v23 | 3 | 5 | (1) the speaker in the sun's beam (its shadow inside the patch) yet its front and right faces almost the same neutral white, the right gable barely darker than the front slope, no amber: a softbox product in a sunset room [measured in the frame: front 218/197/186, side 123/87/53, a step of about 1.5 stops; the right gable 101/35/5 against the slope's 208/31/0; the front a warm cream, not the wall's amber]; (2) knife-sharp edges, no seam where the red meets the white, bare ring-and-cone drivers with marble-like caps, no trim, screws or cone texture; (3) the woofer nearly the front's width, its edge just above the band [spec]; the near-black wordmark on red a low-contrast smudge | Relight with the sun the only main light: the front warm, the side and right gable a warm mid-grey with a hard edge at the corner (an hour) | The last round in this batch: no further render. Down from 6: the deeper amber also took the lift off the frame |
| 2026-10-08 | 01 hero pair | v23 | 3 | 5 | (1) sharp-edged boxes in a flat even white with no shine, the red meeting the white as a hairline with no seam or gloss change: low sun would draw a line down every corner [the near corners do carry a line, two pixels wide at this size; the gable line is a 3 mm groove]; (2) the roof driver jammed into the right end of its cut-out with no bezel [the throat's end, 36 degrees off its axis]; (3) the red sliding to salmon-pink in the sun and crimson in the shade; the near wordmark a low-contrast pinkish emboss, the far one crisp white [polished letters mirroring the floor or the wall] | A real finish: 2 to 3 mm rounds, a satin lacquer that shows the window, a shadow gap where red meets white (an hour) | The last round in this batch: no further render |
| 2026-10-08 | 02a bright room | v23 | 3 | 5 | (1) the light goes to the chair: the sun's one hard moment the near-white patch on the wall with the chair's shadow cut into it, the speaker in soft directionless light with no hard light on its top [it stands in the beam; the sun rakes its front about 45 degrees off, which lights a flat face evenly], the patch's falling edge leading out of frame; (2) a 3D primitive: knife edges, the coral meeting the white with no seam [a 3 mm groove], the front one flat value with no reflection of the room; (3) the tweeter against the right end of the cut-out [the throat's end, 19 degrees off its axis]: a mistake, or an eye peeking out | Put the speaker in the sun: hard light raking its front and top and its own shadow across the floor; the chair into soft light or out (an hour) | The last round in this batch: no further render |
| 2026-10-08 | 04a back, straight on | v23 | 3 | 5 | (1) level and dead centre on one panel, the carton a fifth of the frame's width: no depth, the spec rows hairlines at homepage size, the gutter through the logo and port [the brief holds a straight on]; (2) the face lit almost flat, the shadow a shapeless cloud darkest behind and left, thinning toward the base, a faint contact line: floating; (3) razor edges, no crease where roof meets body, no crimp on the fin; a faint upside-down copy of OPEN OTHER SIDE below the fin [the gloss roof mirroring the fin: from the panel's height it was the whole line, sharp; from 1.3 m a thin sliver]; the port a flat disc, the black post lost on its black plate | A three-quarter about 30 degrees off from above the roof line, on a third (an hour) [that is frame b] | The last round in this batch: no further render. (First rendered from the panel's height, where the new gloss mirrored the fin's mark whole; re-rendered from 1.3 m before its critic) |

### 2026-10-08: the owner's answers to the critics (v24 on)

The owner answered the questions the v21 to v23 rounds raised ("address the additional critic requirements"). The changes:

- the edges rounded 6 mm (the fin's 3);
- the tweeter forward to 125 in a 74 throat, seated flush on the throat's flat floor;
- the drivers flush under satin black trim rings, the cones ribbed charcoal paper, the caps satin, the woofer 30 higher;
- the cast letters 1.5 proud with sides like their faces;
- a recessed terminal cup at 175;
- the Facts values in bold.

Two briefs changed: 04a is a straight-on detail of the label, and 05 a raised three-quarter. The critics' staging asks went in too:

- 06 on a neutral sweep;
- 02a with its sun on the speaker and the chair in the shade;
- 02b with the sun as its one main light;
- 01 with its red below AgX's shoulder;
- 03 recropped.

A new model and new briefs, so a new count: round 1 again, at most three. Every image goes to its critic under a neutral file name.

Where it ended (v26, round 3, the last in this batch): 04b and 06 at 6, 03 at 4, the other five at 5. Round 1 was 4 to 6 and round 2 all 5. What moved: the red holds its hue in every frame (Khronos PBR Neutral); the label detail lost its mirrored OPEN OTHER SIDE, the line-up its hot spots; the port reads as a tube; the crate's roofs sit a stop over their faces; the older room's silhouette reads as the carton. What did not, in any round: the white under sun at the top of the range with no falloff (each critic's fix: a real paint's albedo, about 0.8, under a satin clear); drivers that read as stock however they are mounted (flush trim rings a millimetre or two wide at room distance); the tweeter's place in its scoop from any camera above its axis (the owner's question); and the close-up and the label detail asked, every round, to be whole cartons on a floor (the briefs). Found and fixed on the way: the birch core's square corners stood through the 6 mm rounds, first at the rounds and then at the groove's corner; the denoiser drew each clear letter plane as a rectangle on a dark plinth (the planes are cut to their glyphs now); the bright room's and the hero room's left walls had no skirting (the hero room's fixed after the last render). Lost on the way: the polished clear of v26 drew the slope's light as a line and so drew the orange peel in it, crinkled vinyl to the close-up's critic (03 fell to 4) and dented foil on the crate's chocolate gable; and the corners' lights, three times as bright in the rooms in v26, also caught the fin's end rounds and read as an outline stroke. The owner's questions from this batch are in the README.

| Date | Shot | Prompt v | Round | Score | Three gaps | Fix first | What changed after |
|---|---|---|---|---|---|---|---|
| 2026-10-08 | 01 hero pair | v24 | 1 | 5 | (1) no cool light: the floor's shadows more orange than its sunlit boards, the cabinets' shaded sides kraft-brown, the red salmon in sun and oxblood in shade, and the two units unmatched (a salmon base with a white logo, an orange-red one with a faint tan logo): white or beige, red or coral; (2) a blockout: flat faces, razor edges with a hairline highlight [6 mm rounds], stock grooved cones like stickers with no screws or rim shadow [flush under trim rings], the roof tweeter in a crude oval with white sparkle pixels on its edge [fireflies]; (3) the floor a CG plank pattern, flat boards, identical gaps, 45 % of the frame | Relight for true colour: a large cool sky fill from the window side, less orange bounce off the floor; one red and one logo on both units (an hour) | v25: through Khronos PBR Neutral (the sunlit red holds its hue); the sky through the window behind the camera doubled, a cool fill in the shade; figure in the boards and lighter seams; a small light seen only in each plinth's letters; the indirect light clamped against fireflies (pathtrace.py). In the model: the trim rings gunmetal, the ribs a third as deep |
| 2026-10-08 | 02a bright room | v24 | 1 | 6 | (1) no finish: the white front one flat value, the coral faces flat fills, no sheen or reflection of the sunlit floor; (2) the drivers placeholder parts: the mid the woofer scaled down, the same ribbed cone, no fasteners [flush under trim rings]; the tweeter a black flange round a grey ring, right of centre beside an empty black void [the throat's end 19 degrees off its axis, the scoop's left wall in shade]: a webcam or a sideways eye; (3) the floor a procedural tile, flat boards between black seams, no grain | A real paint finish: a satin clear (about 0.3) so the front picks up a bloom from the sunlit floor, a faint orange peel, a lower white with gradation (an hour) | v25: through Khronos PBR Neutral, so the red is red and the white sits under the top of the range; figure in the boards' colour, broad enough to read from across the room, and lighter seams (pathtrace.py, textures.mjs); a small light seen only in the cast letters. In the model: the trim rings gunmetal, the ribs a third as deep. The finish stays a gloss clear (the critics of the studio frames asked for sharper reflections, not softer) |
| 2026-10-08 | 02b older room | v24 | 1 | 5 | (1) no sky light and no bounce: the carton's shadow on the wall about 6/4/2, darker than wall the sun never reaches, the cones crushed, the cabinet's shaded side caramel (76/44/16) [round 3 of the last batch asked for the sun as the one main light, so this round took out the lamp and most of the fill and the window's sky]; (2) shaded like a block: the white front one flat colour, no seams or screws, cone, surround and cap one glossy chocolate under the amber; (3) the wordmark brown on red at about 2.5:1, read first as "carmilk" [polished letters mirroring the dark room] | The missing fill: a large cool sky light in the window at about a tenth of the sun, then the exposure (an hour) | v25: the window's sky back up and the cool fill inside it at a fraction of the sun, the lamp still off; through Khronos PBR Neutral; a small light seen only in the cast letters, so they read as polished metal |
| 2026-10-08 | 03 bowl close-up | v24 | 1 | 5 | (1) one broad pink-white smear on the empty left of the roof and the rest one flat red, the slope, fin and gable end at the set's grey (luma 91 to 103 against 102 to 111): the lacquer reads matte, the brightest patch is empty roof; (2) the driver's boss against the scoop's upper lip about 70 px right of the centreline [it is on the centreline: the throat's end seen 22 degrees off its axis and 20 above, which also brings the faceplate's top up to the short upper lip], its faceplate crushed black, the screws bare dots, the dome murky with no highlight, the basin clipping to pure red (155, 8, 1): an eyeball rolled up in its socket; (3) close, high and wide, the verticals converging about 5 degrees, the body cut below the eave, no floor or scale: a toy held up to a phone | An 85 to 100 mm lens with vertical shift and pulled back so the whole carton stands on a floor, then the lacquer relit for that camera (an hour, then half a day) | v25: the camera levelled, the lens shifted; the set darker (0x8f8b84); the slope's light a thin strip seen only in the lacquer, laid across the upper slope below the fin (it was a broad strip lighting the left of the slope); a small light seen only in the dome, the faceplate and its screws. Still the close-up the brief asks for |
| 2026-10-08 | 04a back, label detail | v24 | 1 | 4 | (1) so close and square that only an 85 px sliver of the roof survives, no peak or fin, nothing for scale; the gutter through the wordmark [the owner's brief: a straight-on detail of the label]; (2) the letters throw a 5 px shadow while the carton throws none, no floor, the face only 2 % darker across its width: a cutout on a grey card; (3) separate slabs: a band darker than any print black under the roof [the spec's 3 mm shadow line], cream board-ends at the roof's corners and cream lines down both vertical corners [a modelling fault found here: with 6 mm rounds the birch core's square corners stood half a millimetre out of the finish; fixed for 02a, 02b and 01 in this round and every frame after] | Pull back until the whole carton stands in frame off the centreline, on a floor with a soft contact shadow, under one large soft key from the upper right (an hour) | v25: back far enough that the gable's peak and the fin stand above the label, still straight on and level, the frame ending below the Facts; the key raking from the right, 65 degrees off the face, so it grades across its width and the letters' shadows belong to it |
| 2026-10-08 | 04b back, three-quarter | v24 | 1 | 6 | (1) the whites a dingy 225 median, nothing above 236, the shaded side about 173, while the red band drops to maroon and the cast shadow stays about 45 to 55: lit by a different light from the floor, composited; (2) flat fills: no grain, crease, orange peel or wear, the red roof one red with no sweep: a packaging mockup; (3) the port flat black almost to its trim ring, no tube wall [its satin wall takes no light from this key]; the black post (about 5) lost in its black cup beside a fully modelled red one | Relight around the white: one large softbox high at the front-right so the front grades 245 to 225 and a sweep crosses the roof, a big bounce low left so the side (about 160) and the shadow (about 100) share one fill, a curve that stops greying the whites (an hour) | v25: the exposure up a fifth of a stop and the fill down, more of the dome's light, so the back reads white and the side and the shadow share one fill; a strip seen only in the lacquer, laid across the back slope; the reflector into the port's tube. In the model: the tube a lighter moulding, the cup dark grey, the black post glossy, the trim rings gunmetal |
| 2026-10-08 | 05 five flavours | v24 | 1 | 5 | (1) the key a stop hot: the white fronts clip to 255, the red band salmon (252, 155, 147) on the front and oxblood on the side, the blue periwinkle, the pale blue near neutral: three colours wrong on the face seen first; (2) the sweep only behind the middle: a hard horizon at the left edge against a near-black wall, a clipped white strip on the seam at the right [one of the studio's edge strips, seen directly: they had never been hidden from the camera], the top third a muddy dark gradient; (3) nothing seated: the drivers' flat grey rings with no lip or occlusion [flush trim rings, whose crown does not read at this size], no contact shadow at the front feet, uniform matte cabinets | The key down about a stop, a large bounce at camera-right, a tone curve that rolls the highlights off (an hour) | v25: the key down most of a stop and a broad fill from the camera's right; the backdrop lit evenly behind the row; the strips hidden from the camera (pathtrace.py); the camera back a little, so the left carton clears the edge. In the model: the trim rings gunmetal, the cones' ribs a third as deep |
| 2026-10-08 | 06 mixed crate | v24 | 1 | 5 | (1) every pint's tweeter against the top rim of a bare oval scoop, the scoop dark at the top and light at the bottom: a cartoon eye with the pupil rolled up, six faces [from 26 degrees above, the throat, now 15 mm behind the upper lip, projects at the top of the mouth; the paint runs light to dark, mouth to throat, by the colourways]; (2) one stock grooved driver at two sizes, no frame, trim ring or screws [flush under trim rings a millimetre wide at the pint's scale], the woofers nearly touching their windows [spec]; one satin plastic, no texture: clip-art; (3) the white crate (about 240) on a set of about 230 with no footprint on the lit side, its shadow a muddy 90: a cutout with a drop shadow | Rebuild the tweeter mount: centred in the scoop, a crisp lip, a trim ring on the dome (an hour) | v25: the camera lower (21 degrees down, was 26), so each tweeter sits further into its scoop; the set a step darker; more of the dome's light in the shadows. In the model: the cones' ribs a third as deep, the trim rings gunmetal. The tweeter's place in its scoop from above goes to the owner |
| 2026-10-08 | 01 hero pair | v25 | 2 | 5 | (1) the white without a surface: the sunlit fronts at the top of the range (about 249/238/230), no falloff or sheen edge to edge, the shaded sides a flat tan (about 110/88/70) from the warm bounce alone; (2) the red not holding: the fins pink (about 240/92/102) [the vertical faces mirroring the window's sky behind the camera, doubled in v25] beside orange-red slopes and bands, the far band coral where its sheen catches the sun: two units of a matched pair that differ; (3) a room of defaults: a featureless wall over the top half, procedural planks with one sheen, an untextured chair | Re-shade the white (its base to about 0.8, a satin coat) and a large soft fill from camera right, so the fronts land at 225 to 235 and the shaded sides read light neutral grey (an hour) | v26: the exposure down a twelfth; a soft cool fill from the camera's right (scene.mjs), so the shaded sides read a light grey (139/126/118 in the proof); the window's sky back to the room's own, so the fins keep their red (230/59/68 in the proof); the corners' lights twice as bright; the clear polished, every frame |
| 2026-10-08 | 02a bright room | v25 | 2 | 5 | (1) flat colour and knife edges: the white front one value corner to corner (about 242, a two-level spread), the red cap and plinth as even, the low sun drawing no highlight on any edge [6 mm rounds, about two pixels here; the near corner's light seen only in reflections barely drew]; (2) placeholder drivers: the mid and the woofer one generic part at two sizes, no trim ring or fasteners [flush under gunmetal rings], fine steps on the woofer cone like faceted geometry [the pressed ribs], the tweeter a dark cylinder right of centre in its socket, a webcam or an eye [the throat's end 19 degrees off its axis]; (3) the light, not the product, running the right 55 % of the frame: the 800 px shadow leading into a wedge of sun on the back wall at the edge (about 232, within ten levels of the white); the left wall without the back wall's skirting [a gap in the set]; the floor streaky noise with no grain | A real paint finish with a little gloss, the edges rounded so the sun draws them (an hour) [6 mm rounds] | v26: the sun up to about 31.5 degrees, so the light through the door lands on the boards before the back wall and the shadow ends inside the frame; both visible corners lit in reflection, the near one three times as bright; a skirting on the left wall (scene.mjs); the clear polished and the cones' ribs fainter, every frame |
| 2026-10-08 | 02b older room | v25 | 2 | 5 | (1) blockout edges, the only edge a 2 px line down the front corner [6 mm rounds and the corner's light]; the white front one flat peach (about 246/196/166) [the amber sun]; cone, surround and cap one glossy brown [three materials under amber]; (2) the darks crushed with no fill: the cones' insides 2/0/0, the wall shadow about 20/14/2, 55 % of the frame under 40, no cool light anywhere [v25's sky and cool fill too weak]; (3) the wall shadow, the image's idea, a squat lopsided barn about 375 by 300 px that does not read as the carton [the wall 0.6 m behind the cabinet, the sun 50 degrees round and 23 up: the silhouette's top at 0.52 m] | A materials-and-edges pass: rounded edges, a real lacquer or satin board, a material per driver part (half a day) | v26: the back wall nearer (0.55 m, was 0.8) and the sun lower (20 degrees; further round it would miss the window), so the silhouette climbs to about 0.74 m, nearer the cabinet; the cool lamp, the window's fill and sky and the room's bounce up; both corners lit in reflection, the near one three times as bright; the clear polished, every frame |
| 2026-10-08 | 03 bowl close-up | v25 | 2 | 5 | (1) too close on too short a lens: the roof flaring toward the lens like a wedge, its left edge leaning out 27 degrees against 9 on the right, the frame cutting just below the shoulder, no floor or scale [the brief: a close-up of the bowl]; (2) one broad reflection doing all the work: the upper third of the slope bleached to salmon pink (about 251/222/221) and every other plane one value edge to edge, the pink smear pulling the eye from the tweeter [the slope's strip, spread by the clear's 0.1 roughness and the peel into a band]; (3) a kraft sliver at the top-left corner [the birch core at the groove's corner: v25's inset cleared the rounds, not the groove's floor round]; the seam a near-black band [the spec's shadow line]; blotchy streaks in the highlight; the tweeter a plain grey dome in a murky horn | Pull back on a long lens (100 to 135 mm) until the whole carton stands on a floor with a contact shadow and room for type (an hour) | v26: a 100 mm lens from 1.74 times as far on the same line, a little wider, so the roof keeps its shape and the gable a margin each side; the clear polished (0.05, was 0.1) and the peel down by two-fifths, every frame, and the slope's strip a third as wide and half as bright, so a light draws a line instead of a band; the core inset to clear the groove. Still the close-up the brief asks for |
| 2026-10-08 | 04a back, label detail | v25 | 2 | 5 | (1) the frame tight round the graphics: about 6 % headroom over the fin and under 4 % below the label, the base cut, logo and label on the centreline, no floor or scale [the owner's brief: a straight-on detail of the label]; (2) no shape: the fin and the slope within 3 % of each other, the white 8 % from corner to corner, only thin dark lines where the planes turn: a packaging mockup; (3) the slope mirroring a squashed, upside-down OPEN OTHER SIDE under the fin [from 1.3 m the slope's top 13 mm mirrors the fin] and no shine elsewhere; cream specks at the shoulder's corners [the core]; the cast letters' soft shadow against flat print, the a and the r all but touching [the spec's cast letters and tight tracking]; a blank row under the title [as drawn on the canvas] | A slight three-quarter, pulled back and up, standing on a floor with a contact shadow, off the centreline, 10 to 15 % margins (an hour) [frame b is the three-quarter] | v26: the camera up to 1.9 m and back to 3.3 m, level, the lens shifted, so the slope's mirror direction clears the fin and the slope takes the light above the set; about a tenth of the frame over the fin and under the Facts; the key raking harder (75 degrees off the face) and the far fill down, so the white grades across its width; the core inset. Still straight on and centred, as briefed |
| 2026-10-08 | 04b back, three-quarter | v25 | 2 | 5 | (1) the back slope blown to near white (254/249/248 at its core, the median 252/229/229) while the fin, gable end and plinth keep a deep red, the gable the brightest thing in frame: pink gloss on a matte box [v25's strip seen only in the lacquer, at 2.5]; (2) clean untextured fills, the spec panel a vector decal, the port a pure-black disc, cream pixels at the roof's corners [the core at the groove's corner, two pixels at the near eave]; (3) the back favoured, no driver, nothing in the sweep for size [the brief: the back three-quarter] | Feather or swing the light so the slope catches only its falloff and keeps its red under a narrow shaped highlight (an hour) | v26: the slope's strip a third as wide and a quarter as bright under the polished clear, a line; a small light from the camera's side linked to the port's tube alone, on the far wall the camera sees (a glint with a position, pathtrace.py); the core inset |
| 2026-10-08 | 05 five flavours | v25 | 2 | 5 | (1) every plane one tone: the white fronts clipped at 245 to 251 edge to edge, the light blue's side 20 levels under its front, no edge catching a highlight: paperboard, MDF or plastic?; (2) two hard-topped hot spots at the ends of the horizon, the right near white beside the red unit [the edge strips' pools on the sweep: the strips hidden from the camera in v25, their light not], the wall within five levels of the brown carton's shaded roof; (3) the light blue's wordmark brown [the owner's dark bronze letters on the light plinths, 2026-10-06], Oat's inside a rectangular decal patch [found and fixed: the denoiser drew each clear letter plane as a faint rectangle on the near-black plinth], the mid the woofer scaled down, with no screws or gasket [flush under a trim ring] | Relight on a clean sweep: lose the hot spots, a large softbox close in from the front-left, the whites down to about 230, a strip behind for the edges (an hour) | v26: no strips; a light seen only in reflections on each carton's near corner; the exposure down a tenth and the fill down; the backdrop's own light up; the letters' planes cut down to their glyphs (pathtrace.py), every frame |
| 2026-10-08 | 06 mixed crate | v25 | 2 | 5 | (1) every front-facing plane the same light: the pints' fin, slope and face within a few percent, the white face one near-white, the gable flattened into a panel with an oval hole; (2) no contact shadow along the crate's front edge, the floor under its lip the brightest there, the cast shadow a third of the lit floor and running out of frame; (3) one stock driver repeated with no trim or screws [flush under trim rings a millimetre wide at this scale], every tweeter against the top lip of its scoop [from 21 degrees above: the owner's question], the back row's tweeters cut by the front fins [the packing] | Raise the key toward overhead so each roof sits a stop above its face and the shadow ends in frame; a broad soft top light (an hour) | v26: the key up from about 43 degrees to 61, so each slope sits more than a stop above its face, the floor under the lip falls into shade and the shadow ends in frame; the exposure up a fifth |
| 2026-10-08 | 01 hero pair | v26 | 3 | 5 | (1) the white without material: each sunlit front one value (about 247/233/221) with no sheen or reflection of the window or floor; the drivers bare rings [flush under trim rings]; (2) the tweeter an unresolved boolean, jammed into the right-hand end of its scoop, its housing touching the rim, no flange or fillet [the throat's end seen off its axis: the owner's question], a pink-white glint on a scoop tip; (3) the set unfinished: the skirting stopping dead at the corner, the left wall bare to the floor [a gap in the set, fixed after this round in the hero room, as v26 did in the bright room]; procedural planks; an unlit chair at the wall's value | Rework the white: a satin lacquer that picks up the window and the floor, a faint peel, the sunlit faces half a stop down (an hour) | The last round in this batch. The fins keep their red and the shaded sides read grey under the new fill; the white wants a real paint's albedo under the sun |
| 2026-10-08 | 02a bright room | v26 | 3 | 5 | (1) flat colour fills: the white front one value at about 246, at the clip point, edge to edge, the sunward slope the same flat red as the band; (2) the window light contradicting itself: crisp shadow edges but the patch's far end a soft round glow on the skirting with no light above it [the sun raised in v26 so the patch stops short of the wall; the penumbra of its far edge, 4 m from the door head, reaches the skirting], the long shadow leading to it; (3) stock drivers with no recess shadow or lip [flush under trim rings], the tweeter a webcam lens [the owner's question]; pure-white slivers on both ends of the fin [the corners' lights, mirrored in the fin's end rounds too] | Re-shade the cabinet: the white to a paint albedo of about 0.8, a satin lacquer, rounded edges, the fin's slivers removed (an hour) | The last round in this batch. The wedge on the back wall and the skirting's gap are gone; the white wants a real paint's albedo, and the corners' lights a receiver list that leaves the fin out |
| 2026-10-08 | 02b older room | v26 | 3 | 5 | (1) the sunlit front overexposed into one value, red at about 248 across 99 % of it, one flat peach plane: the milk never reads as white [the amber sun at v25's exposure]; (2) the drivers chocolate-brown lathe shapes in one gloss [three materials under amber]; a 2 px pure-white hairline down the front-right corner and both ends of the fin, cooler and brighter than the sunlit face [the corners' lights, three times as bright in v26, mirrored in the fin's end rounds too]; (3) the speaker blending into the light: its left edge inside the window light's soft edge, its shaded side the sunlit wall's value, the cast shadow (about 30) half the window frame's (about 66) and nearly as big as the speaker, seen first | Expose for the white: the sun a stop down, a filmic curve, the white balance part way to the sun, the face near 230 (an hour) [AgX turned the lit red salmon] | The last round in this batch. The silhouette now reads as the carton (the wall nearer) and the darks hold; the exposure wants to come down for the white, and the corners' lights to go back to a third |
| 2026-10-08 | 03 bowl close-up | v26 | 3 | 4 | (1) the planes not separated: but for one near-white band, the fin and the slope almost one red (about R203 against R208) ridge to eave, the white body a flat 242 to 247 with no shadow under the gable, only an 8 px black line [the spec's shadow line; the gable does not overhang]; (2) the driver against its scoop's top lip with empty floor to its left [the throat's end 15 mm behind the upper lip, seen from 20 degrees above: the owner's question], its faceplate taller than wide on the slope [it faces forward, on the bowl's axis], its collar without the crisp edge the red edges carry: an eye glancing up and right; (3) the highlight band crinkled and blotchy, wrinkled vinyl wrap [the orange peel, which the polished clear now draws as a line]; the frame edge to edge, the gable's corner 25 px from the bottom, the driver on the centre line [the brief: a close-up] | Relight with a graded product rig: a large gradient softbox so the slope carries a clean reflection ridge to eave, the fin flagged a step darker, the white falling off with a soft shadow under the gable (half a day) | The last round in this batch. The polished clear sharpened the slope's light into a line and so showed the peel in it: the peel wants to go, or the clear back to a satin, for this camera; the driver's place in the scoop is the owner's question |
| 2026-10-08 | 04a back, label detail | v26 | 3 | 5 | (1) straight on from dead centre, the fin 9 % from the top, cut under the port: no side, base or floor contact, the cast shadow only a near-black wedge in the bottom-left corner [the brief: a straight-on detail of the label]; (2) plain matte colour: the roof a smooth red gradient with no sheen [from 1.9 m the slope mirrors the set above the key], the shoulder an even black hairline [the spec's shadow line], each vertical edge a ruler-straight line of one width [the corners' lights]; (3) the wordmark raised lettering with a soft drop shadow, so tight the letter sides close the gaps, charcoal (about 60) against the label's near-black (about 21) [the polished cast letters mirroring the dark set, at the wordmark's tight tracking] | Reset the camera: pull back and down so the whole carton stands on the sweep, off the centre line, turned 15 to 20 degrees [frame b] (an hour) | The last round in this batch. The ghost under the fin is gone (the camera at 1.9 m); every critic of this frame asked for the whole carton turned to show a side, which the brief rules out: the owner's question |
| 2026-10-08 | 04b back, three-quarter | v26 | 3 | 6 | (1) flat light: the front from about 240 at the top to 220 above the base, the left face an even grey around 140, one soft stripe on the roof, the wall an unlit olive-brown (about 85/82/75), the brightest open area the empty floor at the bottom right; (2) no sign of making: the white panels within half a level once the gradient is removed, the rounded corners never catching a highlight [the corners' lights at 0.6, which also light the faces], a glossy cap with one stripe on a base that looks matte [the same clear on the plinth, mirroring the dark set]; (3) nothing for scale and the back facing us, the port read as a small driver [the brief] | Relight: one large soft light high to the camera's right, so the front fades top to base and wraps onto the left face, a thin strip along the left edge, the pool moved off the empty floor onto the wall behind (an hour) | The last round in this batch: up from 5, the slope red under a line of light and the port a tube with a wall |
| 2026-10-08 | 05 five flavours | v26 | 3 | 5 | (1) the cream and chocolate units read matte beside the white units' glossy lacquer, each with a 2 to 3 px near-white line down its front corner, glaring on the chocolate [one clear on all five: the key's reflection falls on the three nearer fronts only; the corners' lights, the same on every carton, read hardest on the darkest]; (2) the key broad and frontal, the whites at 242 to 250, every plane one value (the red's white front 242 to 243, the chocolate's 74 to 80); (3) the backdrop a muddy near-black brown behind the far end (about 43/38/31), the chocolate's shadow side darker than the wall; the red unit's near-black shadow out of the right edge with no bounce; the light blue's letters brown [the owner's dark bronze on the light plinths] | One finish on all five and true radii so the corners catch graded highlights (an hour) [one finish; 6 mm rounds] | The last round in this batch. The hot spots and the clipped strip are gone and every corner carries a line; the corners' lights want to scale with each body's colour, and the backdrop more light at the far end |
| 2026-10-08 | 06 mixed crate | v26 | 3 | 6 | (1) the cream crate at the cream sweep's brightness (about 240), no contact shadow along its front or left base, while the right base's shadow goes to about 80 [the key at 61 degrees lights the floor in front as it lights the crate's face]; (2) one stock driver at two sizes with no trim ring or fasteners [flush under trim rings a millimetre wide at this scale], every tweeter off-centre in its scoop [the owner's question]; (3) the finishes not matching: the brown gable's highlight a crinkled foil-like ripple [the orange peel, which the polished clear draws in the highlight on the darkest gloss], the light blue satin, the white near-clipped | Relight for separation: the sweep a stop below the crate or the key flagged off the floor in front of it, and contact shadows at the front and left base (an hour) | The last round in this batch: up from 5, each roof a stop over its face; the floor in front of the crate wants a flag, and the peel the same as 03 |

## Critic v2 on the engine (e rounds), 2026-10-08

The protocol changed (`critic/PROMPT.md` v2, CLAUDE.md): a fresh critic scores the image blind, then reads the shot
card and measures (`critic/measure.py`, by part through the render's mask) and prescribes at most eight changes, each
one setting from the card with its value now, the value to set and an accept test the next render must pass. The
engine applies them as written (`studio/engine/render.py --apply`) and `critic/round.py check` runs the tests. The
replies are in `critic/rounds/2026-10-08/`. The geometry, the colours, the drivers and the waveguide are out of scope
by the card, so each round's "out of scope" list is the record of what only the owner can change.

| Shot | Render | Round | Blind score | If fixed | What it prescribed | Next render's accept tests |
|---|---|---|---|---|---|---|
| 01 hero pair | e1 | 1 | 4.5 | 7.0 | c1 the window 0.6 m toward the camera so the left unit is in the sun (its front 92 against 176); c2 the grey rug out of frame; c3 lens shift 0.12 for a copy side; c4 one glazing bar fewer (its shadow banded the fronts); c5 exposure 0.7 to 1.1; c6 a glint on the rings and surrounds; c7 the sideboard from orange to a neutral #897C6E. Out of scope: the pair's toe-in (placement), the drivers' black, the waveguide's shape. Applied all seven, and the toe-in from 12 to 5 degrees (mine: placement is not the critic's) | e2: six of seven pass (left front 230, foreground oak, copy side lum_range 21, fronts' p5 214, rings' p95 103, sideboard neutral); the fronts' median 227 against a 190 to 215 band |
| 04b back, three-quarter | e1 | 1 | 5.5 | 7.5 | c1 the key from azimuth -45 to +20 (it lit the side, the back sat at 184); c2 the fill from 60 to -70 (its reflection banded the Facts); c3 Standard view instead of Khronos PBR Neutral (the amp plate 100 % crushed); c4 the key 3 to 2.4 W/m2; c5 white balance 5600 K; c6 the rim up to 75 degrees for a contact pool; c7 a glint on the connectors; c8 an edge strip for a line down the near round. Out of scope: the plinth's corner seam (an engine fault, fixed: colour zones now cut the faces at their boundary), the amp plate's finish, wider shadow lines. Applied all eight | e2: five of eight pass (side 203, plate 19 out of black, contact pool -23, connectors 204, the corner's line 255); the back clipped at 254 under Standard. Metered at -2 EV: the back at 1.03 scene-linear, so e3 takes the key to 1.7 and -0.1 EV. e3: seven of eight pass (the back 229, the side 191, its top 236, the corner's line 243); the white's dE 4.6 against 4 |
| 04a back, label detail | e1 | 1 | 5.0 | 7.5 | c1 the target down 0.154 m and c2 a 105 mm lens (the Facts small and low, a third of the frame empty above the fin); c3 the key's colour from 5600 K to white (the body read cream, nearer Chocolate's #F1E3CC than white); c4 the key closer, 2.4 to 1.3 m, for a fall-off; c5 the key up from 28 to 38 degrees so the roof parts from the fin; c6 a glint on the port's flare. Out of scope: the roof mirroring OPEN OTHER SIDE (gloss on the fixed roof), the 3 mm shadow line. Applied all six | e2: two of six pass (the Facts now 360 px wide, the fall-off 17); the fin's box missed by 15 px; the white neutral (210/207/204) but dark against the test's grey; the glint aimed at a curved flare the camera sees as a flat flange. Metered the margins at 215 and 205: e3 at +0.25 EV. e3: three of six (the white now dE 1.97 to its grey; the fin's box and the port's glint still miss, the gable's fall-off -11 against -13) |
| 02a bright room | e1 | 1 | 5.5 | 7.5 | c1 the sky 3 to 8 (the room a dim afternoon); c2 one glazing bar (their cross banded the face and the wordmark); c3 a fill from the right for the shaded side (khaki at 94); c4 the sun's colour on the daylight locus, #FFEBCE (the whites magenta); c5 a glint on the letters (+15 on the red); c6 and c7 the side table and vase 0.25 m left, off the silhouette. Out of scope: the plinth corner's white round (fixed in the engine), larger letters. Applied all seven | e2: five of seven pass (the room at 210, one glazing bar's band 1.2, the shaded side's fill 181 in blue, the letters 211); the sun's colour dE 4.7 against 3, the table's side 137 against 150 |
| 03 waveguide close | e1 | 1 | 5.5 | 7.0 | c1 the key down from 55 to 20 degrees and c2 the top strip 0.45 m right (their reflections washed the glossy slope salmon); c3 a glint on the dome; c4 white balance 5700 K; c5 the fill 0.7 to 1.2 for the gable end; c6 the fill's colour to 5700 K; c7 f/8 to f/16. Out of scope: stair-steps in the waveguide's reflection (shading, not shape: the engine now shades faceted CAD smooth, `"smooth"` in the product file), the tweeter's own black. Applied all seven | e2: four of seven pass (the slope's salmon gone, g 30; the top strip's reflection 68; the gable end 158; f/16's edge 58); the dome's glint p95 99 against 100, the whites dE 3.2 and the fill's grey 3.9 against 3 |
| 01 hero pair | e2 | 2 | 5.5 | 7.0 | c1 the camera centred (x 0.55 to 0) so both cabinets show a side; c2 and c3 glints on both woofer cones (62 to 70 % crushed); c4 and c5 glints on both wordmarks; c6 the oak's grain 0.6 to 1.0; c7 the plaster's bump 0.025 to 0.1; c8 the sun's angle 1 to 0.53 degrees (shadow edges 27 px). Out of scope: the toe-in, the letters, the cones' black, the waveguide. Applied all eight, and the sun's 4300 K moved onto the daylight locus (#FFDDAF; the whites read pink, a* +4.3, from a Planckian sun under a daylight white point, which the bright room's critic found too) | e3: two of eight. The cones out of black but chrome: glints of 64 W clip 7 % of each cone (the critic expected a band of 90 to 140). The wordmarks' glints lit nothing on the letters and put a white patch on the floor in front of each plinth: a vertical letter face mirrors the floor there, so no lamp can sit where the critic placed one (it had tilted the normal 20 degrees up to keep the lamp above the floor). The engine now places a glint from the surface the camera sees and skips an impossible one with the reason; e4 tunes the cones' glints to a p95 of 100 to 150 by proof |
| 05 five flavours | e1 | 1 | 6.0 | 7.6 | c1 white balance 5800 K (the whites cream, b* +6.5); c2 the sweep from #C9C4BB to mid grey (the Oat melted into a backdrop of its own colour, 14 levels apart); c3 a level camera (verticals leaning 4 degrees); c4 a reflection-only card for the cones (28 % crushed); c5 +0.2 EV. Out of scope: the cones' black, the letters, the rounds, the row's placement (the Oat 12 % taller than the Whole). Applied all five | (rendering) |
| 02b older room | e1 | 1 | 5.5 | 7.5 | c1 the sun from azimuth 55 to 38 (the carton's silhouette 2.5 times its width, wider than tall); c2 to c4 the window toward the front, larger, one column of panes (to keep the beam on the speaker and bars off it); c5 a fill for the shaded side (brown card at 33); c6 the sill 0.55 to 0.40 (its shadow sank the plinth to 10); c7 the wainscot up to 1.25 m (its rail would cut the fin's shadow); c8 the sun 3.2 to 1.8 W/m2 (the front pinned in the shoulder, the red pink). Out of scope: turning the speaker or moving it nearer the wall, the cone's black. Applied all eight | e2: two of eight; the speaker out of the sun. The critic meant the window toward the front (its centre at y -2.75) and wrote along -1.3, but along runs toward -y on the right wall, so the window moved to the back. The knob now says which way each wall runs; e3 at +1.3, where the critic's own sun (azimuth 38, elevation 8) meets the wall inside the opening. e3: eight of eight pass (the front in the sun at 210, the shaded side 97, the plinth 77, the silhouette on the wall) |
| 08 the inside | e1 | 1 | 5.0 | 7.0 | c1 the sweep from #C9C5BE to #75726D (cut faces, chambers and backdrop one value; the brightest area empty floor); c2 the inside lamp 1.1 to 0.3 (the chambers brighter than the cut); c3 a kick light for the drivers in section; c4 the key to azimuth -50 and c5 to 6 W/m2 (the panels throw no shadow into the cavities); c6 lens shift 0.18 (the fold through the product); c7 white balance 5800 K. Out of scope: the plinth's red (the zone fault, fixed in the engine since this render), the drivers' baskets. Applied all seven | e2: two of seven (the key's shadows in the chambers, the fold clear); everything about a stop dark. Metered: the cut at 0.475 (176), so e3 at +0.6 EV puts the cut at 215, the chambers about 170, the floor about 162 |
| 08b the tweeter, fitted and wired | e1 | 1 | 5.0 | 7.0 | c1 the inside lamp up from 5 to 35 degrees (the room brighter than the cut); c2 (asset) the horn's faceted crease: done in the engine, faceted CAD now shaded smooth; c3 the key in to 0.7 m and c5 down to 0.45 m (a flat section); c4 the sky 0.6 to 0.3; c6 (asset) the insert's streaky cut face: section rules now take their own shader, the insert's plain; c7 a diffuse lamp into the mouth for the fin's red; c8 a pool on the sweep. Out of scope: the insert's cut face as light as the birch (mine to set: now a darker grey, 25 and more levels apart), the bay's red walls, the cable's turn, the tweeter's internals. Applied the six settings | e2: three of eight (the dome's highlight 247, the insert's section even, a pool on the sweep); a stop over (the cut at 232 against 170; rendered before autoexpose). The bay and the inner walls rendered red and white: the paint and its zones covered the inside. The engine now gives the inside of the product its own materials (raw birch, bare resin), found by rays from each face against the assembled product, and keeps each face's material through the cut (clearing a mesh's materials had reset them); e3 with both and autoexpose: four of eight (the dome's highlight 245, the insert's section even, the pool, the sky). The bay and channel still red: the cable and connector inside them counted as walls, so the faces were not found inside; the engine now ignores loose parts (`interior_ignore`) and also finds faces covered by a near part, and e4 takes both |
| 05 five flavours | e1 | 1 (e2) | | | e2: two of five pass (the sweep 131, verticals plumb); the fronts 242 against 224 to 236. Metered as scene-linear EXR: the white fronts at 1.13 to 1.17, so -0.65 EV (exposure -0.45); the cones at 0.027 to 0.042, so the reflection card larger (8 x 3 m) and brighter (3.5) | e3: two of five (the sweep 115, verticals plumb); the whites dE 4.6 against 3, the fronts 238 against 224 to 236, the cones' p95 25 against 55. The reflection probe: the 8 x 3 m card reaches 4.8 % of the cones' pixels, whose lower halves mirror the open sky in front (azimuth -85 to 28, elevation 2 to 58). e4 adds a reflection-only panel 12 x 4.6 m in front, linked to the cones, its strength tuned by proof (p95 81 at 6.7). e4: four of five (the cones' p95 72, the fronts 231, the sweep 102); the whites dE 3.6 against 3 |
| 09 bookshelf pair | e1 | 1 | 5.5 | 7.5 | c1 the wall darker, #F1EEE8 to #CFC6BA (the right speaker's front melted into the sunlit wall, a 3.8 step); c2 a strip key in front of the pair for falloff and the bowls; c3 the sun 2.5 to 1.0 (every lit white in the shoulder); c4 and c7 the picture frame down and left (touching the top edge, crowding the right gable); c5 the art lighter (the darkest mass in frame); c6 a glint on the right wordmark; c8 one row of panes (a transom's shadow across both plinths). Out of scope: the sideboard against the wall, the waveguide's shape, the letters' finish. Applied all eight, and the sun on the daylight locus (#FFEBCD; the whites 244/239/244) | e2: six of eight pass (the right front's edge 49, the strip key's falloff 8, the bowls, the art 69, the transom's shadow gone); the wall 144 against 150 to 205, the right wordmark 252 (glint 0 burned it white) |
| 08 the inside | e1 | 1 (e3) | | | e3 at the metered +0.6 EV: six of seven pass (the cut 161, the chambers 172, the drivers' kick 71, the key's shadows, the fold clear, white balance dE 4.0); the sweep 163 against 207 to 238 | e4 with the inside unfinished (raw birch) and autoexpose: five of seven (the cut 163, the chambers 149, the drivers' kick 73, the fold clear); the sweep 155 against 207 to 238, white balance dE 4.6 against 4.5 |
| 04a back, label detail | e3 | 2 | 5.5 | 7.5 | c1 a lamp behind the gable for a pool on the sweep (orbit misread as round its target: placed at the critic's world point); c2 the port's glint 25 mm lower; c3 (asset) a graduated overhead light so the roof slope reads as lacquer: built as the engine's panel light, ramped 0 to 1 from y 0.20 to 0.45, reflection only, strength tuned by proof to 0.47 (falloff 12.0 against 10); c4 the key 1.2 to 0.8 m wide (its edge in the fin); c5 the target 28 mm down (the port crowded the bottom edge); c6 a glint on the letters; c7 white balance 6300 K. Out of scope: a three-quarter view (the purpose fixes it straight on), the roof mirroring OPEN OTHER SIDE | e4: four of seven. e5 (the key's colour and aim corrected): five of seven (the white dE 1.1, the roof's sheen 12.2, the letters' sheen 142, the Facts' fall-off 6.9, the whites' p5 215); the pool behind the gable fails (falloff -4 against -15 or steeper): re-aimed to the critic's world point the lamp lights the floor behind the speaker, out of the camera's sight, and proofs showed the test does not move with its power, which the next card says; the port's glint (15 against 40): its flange is flat and its bore straight |
| 04b back, three-quarter | e3 | 2 | 6.0 | 7.5 | c1 white balance 5600 to 5800 K (B 6 to 8 over R on every white); c2 a side softbox (the side face one value, 190 top to bottom); c3 lens shift -0.078 (the product across the spread's gutter); c4 the dome 0.4 to 0.15 (a third of the light, a blue veil on the red); c5 the key 1.7 to 2.3 (the back at 226); c6 the RCA out of glint 0 (68 % clipped); c7 a sheen on the amplifier plate (16.4 flat). Out of scope: turning the product, the amplifier's parts, the fin's print mirrored in the slope | e4: five of seven (the side's falloff 17, the dome's veil gone, the plate's sheen 22, the RCA out of the clip); autoexpose chose -0.5 EV, which left the back at 199 against 230 to 244 and the whites dE 9.0 against 2.5 |
| 03 waveguide close | e2 | 2 | 5.0 | 7.0 | c1 the hard top strip replaced by a 4.2 m panel ramped over five stops (the waveguide drawn by one thin streak whose edge broke into facet teeth); c2 the camera nearer the waveguide's axis (the right wall hid 30 % of the dome); c3 the key up from 20 to 40 degrees, into the recess; c4 the sweep darker, #B7B2AA to #A29E98, for the right silhouette. Out of scope: the insert's tessellation (the engine now shades the waveguide from its true surface, sampled on a fine grid by `fab/horn_grid.py`), the joint round the insert, a shallower bowl, a glossier dome. Applied all four | e3: three of four pass (the panel's ramp on the slope 15.8, its streak's teeth gone from the top strip, the white side 224); the sweep 153 against 118 to 142 (autoexpose could not meet both brightness tests). The waveguide's reflections still saw-tooth: the horn's normals were weighted by distance across each grid quad, spiking at its corners, and its long thin facets kink the interpolated normal; both fixed in the engine before e4 |
| 10 both sizes at home | e1 | 1 | 6.0 | 7.4 | c1 window 0's upper glazing bar out (its band across the hero's front); c2 a flag to shade the wall behind the bookshelf unit (its body and the sunlit wall one value); c3 the sun on the daylight locus, #FFEBCD (lilac whites); c4 window 0 moved 80 mm (its jamb's shadow on the sideboard's door seam); c5 a glint on the hero's cone; c6 a glint down the hero's right side; c7 the sun's disc 1 to 0.55 degrees. Out of scope: the bookshelf unit along the sideboard, the lacquer's albedo, the cone's finish. Applied all seven; the engine gained flags (black cards that cast shade) | e2: five of seven pass (the hero's front p5 236, the bookshelf's left edge 110 against the shaded wall, the jamb's shadow off the door seam, the cone 44 % crushed against 50, the side's glint p95 218); the sun's colour dE 2.9 against 2, a shadow's edge 14.8 against 15 |
| 02a bright room | e2 | 2 | 6.0 | 7.5 | c1 lens shift 0.1 (the spread's gutter through the side face); c2 exposure 0.6 to 0.25 (the red a light scarlet, the lit faces 0.7 to 0.9 EV past the view's knee); c3 white balance 5200 to 5450 K (the sky through the front window turned the front cyan); c4 the walls lighter, #F1EEE8 to #FBF7F1; c5 the letters' glint re-aimed (its lamp fell below the floor); c6 the right fill 0.35 to 0.6; c7 the oak's grain 0.6 to 1.0; c8 a glint on the woofer's cone. Out of scope: turning the speaker to the camera, moving it toward the back wall, a 5000 px render. Applied all eight | e3 (rendering) |
| 07 exploded | e1 | 1 | 5.5 | 7.4 | c1 the fill 0.8 to 1.7 (the front baffle, which carries the drivers and every explode axis, lit by the fill alone); c2 the rim off (its reflection washed the roof's slope pink); c3 the fill's specular 0.4 to 1.0 (the cones read as holes); c4 the camera nearer the explode axis (the woofer's ring overlapped its surround); c5 white balance 5600 K (the white body cream); c6 the key in from 2.4 to 1.5 m for a fall-off down the side. Out of scope: the woofer's ring 30 mm further out, the insert 20 mm further out of its pocket. Applied all six, and both of those: the explode distances are the shot's, not the product's (ring 0.34 m, insert 0.33 m) | e2: four of six pass (the baffle 211, the roof's red back at dE 1.7, the cones' sheen p95 57, the side's fall-off 18); white balance dE 4.7 against 3; the ring's gap tested on a fixed region that the ring's new distance moved off |
| 09 bookshelf pair | e2 | 2 | 5.0 | 7.0 | c1 exposure 0.6 to 1.1 (half a stop under); c2 glint 0 from 2 to 0.4 W (it burned the right wordmark white); c3 a 50 mm lens (the pair 32 to 36 % of the frame); c4 the print 0.17 m lower; c5 the print a painting instead of a flat slate board; c6 the sky 3 to 4; c7 the target 60 mm up (the sideboard's leg on the edge); c8 a glint on the left wordmark. Out of scope: the cones out of near-black (the drivers' finish), the speakers closer together. Applied all eight; the engine paints the print from the critic's colour bands (`set.props.*.artwork`), and the letters' lamps sit 0.15 m out so their mirror rays clear the sideboard | e3: six of eight pass (the right front's edge, the strip key's fall-off, the painting, the sky's wall 150); both wordmarks 248: the glints moved them 4 to 5 levels across a 3x range, so the shoulder, not the glint, holds them white |
| 04b back, three-quarter | e4 | 3 | 5.5 | 7.5 | c1 exposure -0.5 to 0 (the back 199, lavender-grey); c2 the side lamp 2.3 to 1.1 (side and back one value, a cut-out); c3 and c4 the key and side on the daylight locus, #FFF7EA (Planckian 5600 K lamps under a 5800 K white point: a* +2.6, the sweep mauve); c5 the plate's sheen moved over the connectors (they sat on its dark end); c6 a reflection-only panel for a graduated sheen down the roof's back slope (flat at 72); c7 a lamp on the left of the sweep (the copy field fell off by 38); c8 a glint on the port's lip. Out of scope: a satin flare (the rubber is the drivers' surrounds' too), the product further right (placement). Applied all eight | e5: seven of eight pass (the back 232, the side 28 under it, the whites dE 1.3 and 1.8 from neutral, the roof's sheen 19, the copy field's fall-off -17, the port's lip p95 104); the plate round the connectors 104 against 50 to 75: with the blacks made real after e4, the anodised plate reflects 4 %, and even at 1 W its glint leaves it at 101 |
| 04a back, label detail | e5 | 3 | 5.5 | 7.5 | c1 the letters' sheen centred on the word (centred on the e, it lit e-a-r-m paper-white and left the l and k grey: a range of 145 across one word); c2 a wash on the sweep above the fin (the sweep one value, 143; the bg lamp moved it +0.8, as the card's tuning note said); c3 the sheen 0.5 to 0.3 W, so the letters sit 20 to 35 under the panel round them, as satin metal; c4 the port's lip glint 3 to 40 W (the flange 13 at every radius and bearing); c5 an edge light down the shadow side's vertical round. Out of scope: a three-quarter view (the purpose fixes it straight on), a rolled lip on the port, the red's chroma where the clear coat mirrors nothing bright. Applied all five | e6: five of five pass (the word one metal, range 14; the sweep's wash 155; the letters 213, under the panel; the port's lip p95 119; the shadow side's edge line 237) |
| 08 the inside | e4 | 2 | 5.5 | 7.0 | c1 the key from azimuth -85 to -40 (it grazed the cut plane: 6.5 % of it reached the section, one value from gable to plinth); c2 the key 6 to 2.5 W/m2 now that it faces the cut; c3 the key down from 42 to 30 degrees, into the chambers; c4 the dome 0.6 to 0.3 (the backdrop 27 levels under the section); c5 a glint on the woofer's cone; c6 white balance 5800 to 6000 K. Out of scope, and taken by the engine as faults of its own: the blacks (the baskets, the motor and the amplifier at 0.4 to 0.8 % reflectance, so no light could model them: every black in both products now reflects 3 to 4 %, as real black paint, rubber and plastic do, and the anodised cone is a dielectric); the drivers in section (their motors and baskets now cut to bare steel and aluminium); the birch's plies (a plywood panel's cut face now shows its veneers, 1.4 mm each, long and end grain alternating, with glue lines). Applied all six | e5 (rendering): the key, the dome and the glint tuned by proof |
| 02b older room | e3 | 2 | 6.5 | 8.0 | c1 white balance 4300 to 3700 K (the sunlit white peach, dE 7.4 from the Oat flavour's body); c2 the wainscot's fields 0.62 to 1.9 m wide (a stile's shadow rose out of the silhouette like an antenna); c3 the plaster darker, #D8CCB8 to #A89E8F (the sun patch on the upper wall 0.92 of the speaker's white, the largest bright shape); c4 a reflection-only panel for a ramp down the white front; c5 one for the red roof's slope; c6 a glint on the woofer's cone. Out of scope: the waveguide's depth, turning the speaker (now the critic's to change), the red on the shaded side. Applied all six | e4 (rendering): the two panels and the glint tuned by proof |
| 08b the tweeter, fitted and wired | e3 | 2 | 4.5 | 7.0 | c1 the bg lamp up from 25 to 80 degrees (from the camera's side it flooded the section with twice the key's light: the insert's cut face fell off by 1); c2 the key 2.8 to 5.5 to carry the level; c3 the rim to azimuth -160 (the bowl's lower wall mirrored it as a white band with teeth along it); c4 the fill's specular off (a hard salmon plateau in the bowl); c5 white balance 5600 K; c6 the inside lamp down to 10 degrees, under the top panel; c7 a graduated panel for one soft highlight down the bowl; c8 the key to azimuth -10, onto the insert. Out of scope, and the engine's to fix: the plies, the bay's red walls (both done since e3), the waveguide's teeth (the horn's facets now refined onto its true surface and its normals interpolated without spikes); the plug's and socket's one cream (both are natural nylon); the tweeter's motor in section (its body now cuts to bare steel). Applied all eight | e4 (queued): the key, the inside lamp and the panel tuned by proof |
| 05 five flavours | e4 | 2 | 5.5 | 7.5 | c1 the fill 0.8 to 1.8 (the white sides 1.2 to 1.9 stops under the fronts, the Chocolate side near black); c2 the key on the daylight locus, #FFF3E1 (lilac whites); c3 a strip for the five roofs to mirror, the same ramp on each; c4 a reflection-only card in front for the fronts and the plinth letters (grey print at 92); c5 the fill to azimuth 35 (each neighbour shaded the next one's side); c6 the fill on the daylight locus; c7 exposure -0.7 to -0.5 for the Oat's body. Not prescribed for want of a test, and taken: the same camera line 1.55 times further back at 70 mm, so the five read at one scale (the Whole's side to front 1.22 against the Oat's 0.43). Out of scope: a satin cone (the named driver's finish; its blacks now reflect as real ones do) | e5 (rendering): the fill and both panels tuned by proof, then the camera |
| 07 exploded | e2 | 2 | 5.5 | 7.5 | The first critic to use the explode distances: c1 the insert drawn out 0.33 to 0.52 m (it still covered the cabinet's eave corner); c2 the tweeter 0.20 to 0.36 m, alone on the axis between the pocket and the insert (it hung in front of the opening); c3 the camera up 1 m, 28 degrees over the target, so the pocket's bore and magnets show past its near wall (0 px now); c4 a reflection-only panel for the drivers' cones and surrounds; c5 a lamp on the sweep behind (157, darkest on the key side); c6 white balance 5600 to 6000 K; c7 the key narrowed 1.4 to 0.6 m so it stops wrapping the front corner; c8 a graded panel for the roof's and the insert's lacquer. Out of scope: the cones' finish, the wordmark's size, cutting the pocket's wall, a shallower waveguide. Applied all eight | e3: six of eight pass (the insert clear of the eave, the tweeter alone on its axis, the pocket in view, the cones' sheen 41, the sweep 181, the roof's sheen p95 145); the baffle beside the corner 234 against 198 to 214, white balance dE 3.6 against 3.5 |
| 10 both sizes at home | e2 | 2 | 5.5 | 7.2 | c1 the side's glint 0.8 to 1.0 m (its mirror image ended a quarter of the way up the hero's side: a 119-level break); c2 the left window to the right wall (its sun stripe as bright as the fronts, at the frame's edge); c3 a reflection-only panel in front for a sheen down both white fronts (one value, in the view's shoulder); c4 the floorstander turned from 10 to 0 degrees, the first use of placement, so its red gable end reads (a 13 px grey sliver); c5 the plaster warmer, #F1EEE8 to #EDE5D8; c6 a glint on the bookshelf's letters (4.5 levels over the blue). Out of scope: the cone's finish, the roofs' colours in the view's toe, the letters' size. Applied all six | e3 (queued): the panel and the letters' glint tuned by proof |
| 04b back, three-quarter | e5 | 4 | 6.0 | 7.2 | c1 the plate's glint 1 to 0.2 W (the plate a mid-grey slab at 100: the realer black lifted it); c2 the side lamp 1.0 to 0.4 (side and back 34 levels apart, 48 wanted); c3 the target 40 mm down for floor below the base; c4 glint 0 moved onto the IEC inlet's frame (skipped on the round socket, which mirrors the module); c5 (asset) matte cards on the floor round the base seen only in the plinth's lacquer, so its red is not veiled pink by the lit floor: built as reflection-only flags (`reflect_only`), placed as the critic gave them. Out of scope: a larger plate, legends on it, the fin's print mirrored in the roof. Applied all five | e6 (queued): the glints and the side lamp tuned by proof |
| 01 hero pair | e4 | 3 | 5.0 | 7.0 | c1 the plaster darker, #E6E0D5 to #B0A595 (the sun patch behind the left speaker as bright as its white body: 27 levels of silhouette); c2 the Standard view instead of PBR Neutral (its toe crushed the red's G and B to 9-15 and the cones to 57 % black); c3 exposure 1.1 to 1.4; c4 a reflection-only panel behind the camera for a ramp down both fronts; c5 the oak's plank contrast 0.45 to 0.8 (it read as laminate); c6 the skirting darker with the wall; c7 a reflection-only card on the floor in front of both plinths for the cast letters (they mirror the floor there, so their glints were skipped). Out of scope, and noted for the finals: the denoiser's smear at 96 samples and the 1350 px frame (fixed on the card; the deck's images are rendered again at full size and more samples). Applied all seven | e5 (queued): the panel and the card tuned by proof |
| 09 bookshelf pair | e3 | 3 | 5.5 | 6.9 | c1 the sun 1 to 0.5 (from behind the camera it lit both fronts square, deep in the view's shoulder: 4 levels of range under the woofer); c2 the key up from 35 to 55 degrees to rake down the fronts; c3 white balance 5200 to 5700 K (the white b* -4.7 against a warm wall); c4 f/4 so the wall and print soften behind the pair; c5 and c6 the letters' glints off and to 0.05 W: read through the engine's tuning note, the glints were 45 % of the letters' light, hidden by the shoulder. Out of scope: a brushed letter finish, the left fin mirroring the front window (only moving the window clears it). Applied all six | e4 (queued): the sun tuned by proof |
| 02b older room | e3 | 2 (e4) | | | e4: three of six pass (c1 the sunlit white's blue 201 at 3700 K; c3 the plaster 149; c5 the roof's sheen falls 22). c2 the stile's line is still there (edge 59): at 1.9 m the fields left a stile at the wall's centre, behind the silhouette. c4 the face's sheen falls 11.9 against 12. c6 the cone's glint p95 117 against 22 to 70, tuned down to 1.33 W, the floor of its range | |
| 02b older room | e4 | 3 | 6.0 | 7.5 | c1 the wainscot's fields 1.9 to 1.5 m, so the stiles fall at -1.2 and +0.4 m, clear of the silhouette (the antenna, a line 74 levels deep, was the centre stile's moulding); c2 and c3 the face and roof sheen panels warmed to 3400 and 3200 K (D65 panels under a 3700 K white balance gave periwinkle letters [127,147,205], a lavender top-left on the front, and a magenta roof slope, dE 16 from the red); c4 the fill 5000 to 4000 K (the shaded side slate blue, b-r 36); c5 the sun 0.7 to 0.3 degrees (the bars' shadows all penumbra, 11 px); c6 the oak lighter, #6E4B30 to #8C6644 (the floor 12.9, crushed); c7 the sky 1.2 to 1.7 (the right third navy-black at 15). Out of scope: a satin finish on the letters (fixed through the lamp's colour instead) | job02b4: all applied, c5 and c7 tuned by proof |
| 02a bright room | e2 | 2 (e3) | | | e3: seven of eight pass (the gutter clear of the side, range 4.7; the red's R 210; the front dE 2.4 from white; the walls 202; the letters 215, the top of their range; the side 174; the cone's sheen p95 73). c7 the oak's grain range 4.9 against 6 to 16 | |
| 02a bright room | e3 | 3 | 5.5 | 7.0 | c1 the letters' glint lamp 6 to 20 cm (it lit r-m-i into one white blob, 40 % clipped, and left e and k at 130); c2 a reflection-only panel ramped down the lacquer, bright under the eave and gone by mid-face (the front one value, 243 to 242); c3 the right fill cool, #D6F0FF (the shaded side beige-pink, dE 5.3 from a neutral grey); c4 the horizon cooler, #D0ECF8 (the shade pinker than the sun); c5 the sky 8 to 9.5 (the back wall 199, dim); c6 the oak's plank contrast 0.4 to 0.7 (neighbouring planks 2 to 8 levels apart, laminate). Out of scope: the 3 mm shadow lines under the gable and over the plinth, sub-pixel at this distance (spec geometry) | job02a4: all applied, c1, c2, c5 and c6 tuned by proof |
| 05 five flavours | e4 | 2 (e5) | | | e5: six of seven pass (the sides 181; the roofs' sheen falls 19; the letters 145; the fill's falloff 36; the side dE 1.8 from white; the Oat 186). c2 the front dE 2.01 against 1.8 | e6: six flavours since 2026-10-08, Matcha (British racing green, its waveguide matcha) fourth, spaced as before; rendered, not yet critiqued |
| 01 hero pair | e4 | 3 (e5) | | | e5: four of seven pass (the plaster 148; the front dE 2.8; the sun patch 230; the fill side 104). c4 the fronts' ramp falls 14.3 against 8 to 14 and c5 the oak's range 15.0 against 16, both just outside after the exposure; c7 the letters 222 against 110 to 165: the reflection card barely moved them, since polished letters show what they mirror | |
| 09 bookshelf pair | e3 | 3 (e4) | | | e4: three of six pass (the fronts 227; their falloff 14.5; white balance dE 2.47). c4 f/4 left the painting too sharp (edge 21.4 against 8 to 18) and c5 the right letters' glint at 0 left them grey (p95 74 against 205 to 238): both re-tuned in job09c, the aperture and the glint. c6 the left letters 247 with their glint at 0.05 W: lit by what they mirror | |
| 10 both sizes at home | e2 | 2 (e3) | | | e3: three of six pass (the side's glint edge 3.9; the left window on the right wall, 117; the gable's green 31). c3 the front sheen panel did not move the fronts' falloff (1.5 to 1.7 across 3 to 9); c5 the wall dE 5.7 from #EDE5D8; c6 the bookshelf's letters 243 against 110 to 175, whatever the glint's power | |
| 04b back, three-quarter | e5 | 4 (e6) | | | e6: four of five pass (the plate 71; the side 193; the target's floor 125; the plinth's green 33). c4 the glint on the IEC inlet does not land: its reading did not move between 2 and 4 W | |
| 08 the inside | e4 | 2 (e5) | | | e5: three of six pass (the key's falloff 21.6; the chambers' range 58; the cone's glint p95 149). c2 the cut 212 against 215 to 228; c4 the dome's backdrop 107 against 138 to 160; c6 white balance dE 5.1 | |
| 08b the tweeter, fitted and wired | e3 | 2 (e4) | | | e4: four of eight pass (the bowl's rim lamp 85; the inside 115; the insert's cut p95 124; the backdrop's falloff). c1 the section's falloff 2.0 against 6 to 45; c2 the red's R 191; c4 an edge 24.7 against 8; c5 white balance dE 3.5. Saved as 08b-final.png, which fab/README.md shows | |
| 03 waveguide close | e2 | 2 (e4) | | | e4: three of four pass. Meant to test a 384-section waveguide against the teeth in the bowl's reflection, but the render model had not been rebuilt (byte for byte the 96-section file), so it tests nothing; the teeth are unchanged. They sit along the crease where the side walls turn into the long floor, where neighbouring meridians differ most in length, so the stations along each wall are skewed between them: the rebuild now has four times the stations as well | |
| 04a back, label detail | e6 | 4 | 5.0 | 6.3 | c1 the clear coat 0.08 to 0.22 (the roof mirrors the fin's OPEN OTHER SIDE upside down in a band under the ridge, range 41.7): tuned instead to the least roughness that blurs it (range 14 to 18), since the finish should match the other frames; c2 the letters' sheen 0.2 to 0.13 W (faces 213 against a panel at 229 to 236: a pinkish sticker); c3 a halo lamp on the backdrop above the fin (one flat 150 to 155). Out of scope: a flared port; chamfered letter faces | job04a5 |
| 07 exploded | e3 | 3 | 5.5 | 7.0 | c1, c2, c6, c7, c8 the woofer (0.16 to 0.31 m), its ring (0.34 to 0.49), the mid (0.13 to 0.23), its ring (0.24 to 0.34) and the insert (0.52 to 0.68) drawn out along their axes (the drivers' motors still over their holes, 1 px from the cabinet's edge; the mid's ring touching the insert); c3 the sweep #C9C5BE to #A09C95 (the insert's grey flank 1.2 levels off it); c4 the fill 2.23 to 1.9 (the two white planes 9 apart); c5 the gloss panel 3.6 to 1.5 (the red washed salmon, dE 21). Out of scope: the insert's grey, the drivers' cones, the letters, the parts' axes, the cutaway set | job07d |
| 10 both sizes at home | e3 | 3 | 6.0 | 7.6 | c1 the hero turned -16 degrees (its plinth mirrored the sun's glare off the glossy floor into the lens: dE 19.8, and the fin the front window: 20.8); c7 the bookshelf unit to -22 for a matching three-quarter (side to front 0.11 against the hero's 0.30); c2 the sky 3 to 5.5 (the shaded wall 112, mauve); c3 the sun 2.5 to 1.6 (both fronts in the view's shoulder, 240 to 243); c4 and c6 graduated panels for the hero's front and side, placed for the new angle; c5 the side's disc glint off (its rim an arc across the side); c8 a glint for the bookshelf's cone (p95 33). Out of scope: a matte clear coat (the finish is the product's); the letters' metal | job10d |
| 01 hero pair | e5 | 4 | 5.5 | 7.0 | c1 a graduated panel on the floor under the camera's sightline for the fronts to mirror over their whole height (the front_ramp reached only their top quarter: falloff 6.5 below it); c2 and c6 the letters' card 0.67 to 0.3 and warm (letters 220, half clipped and icy blue; the plinth behind them pink, dE 11.3); c3 the oak's grain 1 to 2.5 (range 4 inside a sunlit plank); c4 a ramp over the roofs (flat at 70); c5 a warm bounce on the right speaker's inner side (75 against the wall's 77). Out of scope: a satin finish on the letters or plinth; darker cones; a wider frame | job01c |
| 04b back, three-quarter | e6 | 5 | 5.5 | 7.0 | c1 and c4 (asset) receivers for the reflect-only flags (the sweep's own gloss saw their undersides: straight-edged patches 3 levels deep in the copy space): Cycles cannot limit what sees a card, so the engine makes reflect-only flags one-sided, the floor seeing through their backs; c2 a graduated panel for the side's lacquer (falloff 5.9, a grey card); c3 (asset) the IEC glint was skipped for an occluder 0.00 m away: the engine's occlusion test now ignores hits within 2 mm and faces seen from behind (the bezel sits inside the amp module), and takes an occlusion_ignore list. Out of scope: a larger frame for the connectors | job04b5 |
| 08 the inside | e5 | 3 | 5.5 | 7.0 | c1 the key -40 to -55 degrees so the back panel's shadow falls across the far walls (the wall beside the divider 181 against a 202 section); c2 a grey zenith, #FFFFFF to #8C8C8C (the panels' tops brighter than their own cut faces); c3 +0.4 EV (the white 210, dE 10); c4 a neutral sweep, #75726D to #6A6D71 (beige on beige); c5 a pool on the cove (falloff 12.6); c6 a fill from beside the camera for the baskets (62 % of the woofer's crushed). Out of scope: a detail inset for the tweeter's connector; lighter baskets | job08d |
| 04a back, label detail | e6 | 4 (tuning) | | | c1's satin clear coat needed 0.26 to blur the fin's print in the roof (range 17.5): satin on one frame of twelve, while the 10 and 01 critics took the clear coat as the product's finish. Reverted to the product's 0.08; the card now offers only the set's materials and the engine holds back a change to a product preset. 04a-e7 (satin) is a record only; e8, gloss with round 4's other changes, goes to the next critic. Whether the lacquer should be satin: an owner question | job04a6 |
| 05 six flavours | e6 | 3 | 5.5 | 6.5 | c1 the floor card 7.1 to 9.0 m wide (it ended inside the Oat's reflection: its 'milk' 92 against 'ear' 146, its plinth stepping 30 to 22); c2 the key 4 to 9 m out (the floor falls 34 levels left to right, brightest where nothing stands, and the Oat gets 60 % of the Whole's key); c3 a panel behind the row facing down onto the floor between the cartons (every gap a near-black wedge at 42 to 47, the Chocolate's edge lost in it). Out of scope: the Chocolate's cream waveguide (its depth is acoustic); larger rounds; a lighter Chocolate | job05f |
| 08b the tweeter, fitted and wired | e4 | 3 | 4.5 | 6.5 | c1 (asset) the bowl's crease a zipper of teeth (step 21 against 0.7 in clean bowl): the adaptive waveguide, in the render model since 01:00; c3 (asset) a soft dark smudge on the tweeter frame's flat cut face: the boolean's caps took normals blended from the part's sides, and the engine now gives every cut face its own normal, flat; c6 (asset) a black flag the fin mirrors instead of the grey sweep (the fin dE 13 from the red, a pink veil), added; c2 a pool on the cove; c4 the key 2.3 to 2.9; c5 the mouth lamp 2 to 4.5 for the fin's face. Out of scope: the tweeter's inside in section; the cable's doubled-back run; birch figure on the cut faces; a letter's edge notching the silhouette | job08b4 |
| 03 waveguide close | e2 | 2 (e5) | | | e5, the first render on the adaptive waveguide: three of four pass (the slope's falloff 15.8; the facets' range 1.3; the white 224). c4 the backdrop 153 against 118 to 142. The teeth along the floor's creases are gone; the next critic sees crisp creases, set by the acoustics | |
| 03 waveguide close | e5 | 3 | 5.5 | 7.5 | c1 the 4.2 m top panel halved (the lit roof and the horn's floor coral, dE 13.7, while the vertical fin is 3.6); c2 its ramp falling twice as fast behind the ridge (the floor as bright as the roof, so the horn reads raised, not sunk); c3 a pool on the sweep (one value, 153 to 159); c4 a dark reflection flag for the gable end (a grey veil, brick-brown); c5 a sheen along the fin (4 levels end to end); c6 the key 40 to 25 degrees (the white 224, greyish); c7 the dome's glint 3 to 6 W (dimmer than the rim). Out of scope: softer creases (acoustic); a satin insert (the product's finish); a wider seam; the shadow line under the gable | job03d |
| 09 bookshelf pair | e5 | 4 | 5.5 | 7.2 | c1 and c2 a 57 mm lens and the target up (the pair 9.6 % of the frame, empty wall above, a blurred sideboard below); c3 a fill for the white sides (123 and 112, darker than the wall behind them; the two fronts 227 and 211); c4 a ramp panel over the roofs (range 3 to 6, matte); c5 (asset) a real turntable for the white box with a stick tonearm at the frame's centre, as bright as the fronts: the engine's new record player, walnut on feet, an aluminium platter with felt mat and record, a tonearm on its pivot base with counterweight, headshell and rest; c6 f/1.7 to 2.8 (the nearer speaker 2 to 3 px soft); c7 a sheen panel for the plinths (dE 8.2, crushed). Out of scope: a glossier white; a larger wordmark | job09d |
| 07 exploded | e3 | 3 (e4) | | | e4: seven of eight pass (the drivers clear of the cabinet; their rings clear of the drivers; the sweep 145; the gloss's green 88; the insert clear of the mid's ring). c4 the front 231 against 208 to 222 | |
| 07 exploded | e4 | 4 | 5.0 | 6.4 | c1 the drivers' reflection panel 1 to 8 (the black drivers matte silhouettes, woofer p95 67.6; the last tuning tested a median, which a highlight never moves); c2 the target down 0.13 m (the base 70 px from the bottom edge, 186 px of sweep above the fin); c3 to c8 every part drawn further out for even gaps (the motors 17 to 21 px from the cabinet, the rings 26 to 27 px from their drivers). Out of scope: the baskets drawn as solid cones (the real ones are cast, with windows: the driver models now cut six windows between spokes, PROPORTIONED); the insert's grey body (the printed resin, unpainted where it sits in its pocket, by design) | job07g |
| 04b back, three-quarter | e6 | 5 (e7) | | | e7: three of four pass. The one-sided flags cleared the sweep (both patches' falloffs -3.0, as the critic predicted); the side's sheen falls 17.2. c3 the IEC glint still skipped: the occlusion_ignore change was an asset and held back (set since), and the hit is 2 to 5 mm out on a front face, the connector sunk in the plate | |
| 04b back, three-quarter | e7 | 6 | 6.0 | 7.3 | c1 the sweep #B4AFA7 to #8E8A83 (the cove beside the white side 160 against 196: grey on grey); c2 the rim strip 1.8 to 0.4 m (the floor under the plinth a long ramp, not a contact shadow: the carton cut off only part of the strip); c3 the plate's glint 0.3 to 0.12 m (the plate one flat 63 to 77); c4 glint 0 onto the round connector's raised shell, whose mirror ray clears the plate; c5 (asset) a black cutter off frame for the bright bottom-right corner, added. Out of scope: the fin's lettering mirrored in the roof's gloss (a true reflection; an owner question) | job04b7 |
| 01 hero pair | e5 | 4 (e6) | | | e6: five of six pass (the fronts' ramp 17.4; the letters 163; the plaster's range 15.5; the oak's p95 140; the front dE 6.3). c5 the right cabinet's shade side 99.7 against 100 to 135, the inner fill tuned 0.18 to 0.51 | |
| 02a bright room | e3 | 3 (e4) | | | e4: five of six pass (the letters' p5 176; the red dE 2.6; the front dE 0.7; the back wall 209; the plaster's range 16.2). c2 the lacquer ramp's falloff down the white front 0.5 against 5 to 8: the panel lights the front's clear coat evenly, so the front stays one value | |
| 03 waveguide close | e5 | 3 (e6) | | | e6: five of seven pass (the horn's floor falls -13.5 toward the throat; the background's gradient 21.4; the fin's sheen 26.4; the white 231; the dome's p95 140). c1 the lit roof dE 6.5 from #C62828 against under 5 (13.75 before the halved top panel); c4 the gable end's green 11 against 12 to 40 (the flag took the grey veil off and a little more) | |
| 02b late sun | e4 | 3 (e6) | | | e6 (e5 a record: the tuner's runaway sky): three of seven pass (the moulding line clear of the shadow, edge 0.4; the front's blue 220; the bar shadows' edge 32.6). c3 the roof's front slope dE 14.0; c4 the shade side's blue 109 against 68 to 86; c6 and c7 the wainscot 34.6 and the floor 14.9 against 17 to 26 and 19 to 27: the exposure's +1.6 EV overshot the wainscot and left the floor short | |
| 08 the inside | e5 | 3 (e6) | | | e6: none of six pass, each near its band (the far walls' falloff -23.7 against -35 to -75; the zenith's 4.5 against -8 to -45; the white 204 against 206 to 220; the backdrop dE 4.7 from neutral against 2.5, gone cool blue; the pool 48.5 against 20 to 34, overshot; the baskets' dark 15.3 against 5 to 14). The tuner set aside the key's swing and the pool's cut because each broke the backdrop's neutrality, which a later change broke anyway. The baskets now show their windows and spokes | |
| 07 exploded | e4 | 4 (e5) | | | e5: eight of eight pass (the woofer's p95 126, the drivers' panel tuned 5 to 10.55; the sweep 149; every part clear of the cabinet and its neighbours, p5 116 to 134 in the gaps; the margins balanced). The baskets show their windows, the spokes top and bottom | |
| 02a bright room | e4 | 4 | 5.0 | 7.0 | c1 the oak 0.42 to 0.65 rough (the floor mirrored the sunlit wall into the speaker's floor shadow, which showed only where it mirrored the wall's own shadow: 148.5 beside the plinth against 151.4 in sun); c2 the lacquer ramp off (invisible to the camera, but the floor mirrored its base as a hard curved edge, range 26.8; it never reached the front); c3 the white point 5450 to 5950 K (the white front blue, B 13 over R); c4 the sun 2.5 to 3.3 (the boards in sun no brighter than their own spread); c5 a broad glint on the front (one value, 240 +/- 1); c6 (asset) scanned oak with pores and figure. Out of scope: a glossier clear; a cooler red | job02a6 |
| 01 hero pair | e6 | 5 | 5.0 | 6.8 | c1 PBR Neutral for Standard (every pixel above the left mid 255, the red veiled pink, dE 8.0 and 5.2); c2 the oak's grain 5 back to 1.2 (1-3 px streaks, brushed metal); c3 the exposure after it; c4 the fronts' ramp x2.5 (PBR Neutral's shoulder squeezes it from 21 to 6 levels); c5 the boards' contrast 0.8 to 1.4 (3 levels between boards); c6 a sheen on the right mid (37.6 against 67.5, near black under the new toe); c7 (asset) end joints at random (one column of joints at x 512): the engine's oak, every row slid at random; c8 (asset) a print for the frame (a flat #3F5B6E field): the engine's colour-field painting in the critic's palette. Out of scope: a 16:9 crop | job01e |
| 02b late sun | e6 | 4 | 6.0 | 7.2 | c1 the sun 1.8 to 1.05 (the lit plinth's red at scene-linear R 1.22, deep in PBR Neutral's shoulder: coral, dE 14.6; the roof 12.5); c2 the fill 0.17 to 0.28 (the silhouette 13.7, a hole with no wall in it); c3 the woofer's glint 1.33 to 0.35 W (a blue wash, B 33 over R); c4 the frame 0.018 right (the gutter on the silhouette's edge). Out of scope: a satin clear on the red; the silhouette's proportions (a re-stage from azimuth -37) | job02b6 |
| 04b back, three-quarter | e7 | 6 (e8) | | | e8: three of five pass (the sweep beside the white side 126; the plate's sheen -17.3; the bright corner gone, -6.0). c2 the floor under the plinth falls -26.8 against -27 to -48, a contact shadow now; c4 the round connector's glint p95 210 against 110 to 200 | |
| 04a back, label detail | e6 | 4 (e8) | | | e8, gloss with round 4's other changes: one of three pass (the panel 186). c1 the fin's lettering mirrored in the roof's gloss, range 41.9 against 4 to 18: a true reflection, which the polariser (on the cards since) can take out; c3 the backdrop above the fin 176.8 against 160 to 168, a pool too bright | |
| 07 exploded | e5 | 5 | 5.0 | 6.8 | c1 a floor light behind the product (the floor darkest right behind it, 110 to 118, against 157 to 166 in front); c2 the key -40 to -65 degrees (side and front meet 3 levels apart, a soft cylinder); c3 a 57 mm lens (the parts the frame is for illegible: the tweeter 30 x 43 px); c4 the target left for the group's balance; c5 and c6 the insert 0.92 m and the tweeter 0.6 m out (the drawer crowded the mid's ring, 29 px). Out of scope: the insert's grey flanks (its bare resin) | job07h |
| 04a back, label detail | e8 | 5 | 5.0 | 6.5 | c1 the polariser at 0.95, pass axis vertical (the roof mirrors the fin: a reversed OPEN OTHER SIDE under the real one, range 41.7; the slope is seen at 52 to 56 degrees, Brewster's angle, so its glare is nearly all s-polarised); c2 the roof's ramp x10 (the filter takes the slope's gloss gradient with the ghost); c3 the letters' sheen 0.3 to 0.12 m (every face one value, 184 to 190: grey plastic); c4 a kicker for the left edge's round. Out of scope: a satin clear on the roof; a camera above the ridge; a glossier port lip; polished letters | job04a7 |
| 04b back, three-quarter | e8 | 7 | 6.0 | 7.2 | c1 +0.15 EV (the hottest flat white 236, the band over the plate 210: grey, not white); c2 the rim 75 to 57 degrees (overhead, it lit the roof's back slope 0.9 stop above the plinth on the same side: two reds); c3 the key 2.6 to 3.5 m out (the far strip of the back falls 25 levels, so the hot corner caps the exposure). Out of scope: a larger frame for the Facts' 7 px rows (the finals) | job04b9 |
| 02a bright room | e4 | 4 (e5) | | | e5, the first on the engine's new oak (each board its own wood, end joints at random): two of six pass (the speaker's floor shadow 126, the oak 0.62 rough; the ramp's edge gone, range 6.4). c3 the white dE 3.6 from neutral against 1.5; c4 the boards in sun 146 against 160 to 172 (the sun tuned to 4.8 reached 159); c5 the broad glint's falloff 2.8 against 4 to 9; c6 a board's figure 7.3 against 9 to 20 | |
| 02b late sun | e6 | 4 (e7) | | | e7: two of four pass (the woofer's glint 88, the gutter's lit strip 106). c1 the plinth's red dE 10.9 against 7: the tuner had it at 5.6 with the sun at 0.98, then the exposure step lifted the frame 0.3 EV for the brightness tests and the shoulder bleached it back; c2 the silhouette 28.7 against 18 to 28. The exposure step now reads colour too (Blender's own pipeline per exposure); e8 is e7 re-exposed | job02b7 |
| 01 hero pair | e6 | 5 (e7) | | | e7: six of eight pass (no clipped white under PBR Neutral; the oak's figure 5.4; the boards' steps 13.4; the right mid 53; the end joints at random, 0.1; the print 46). c3 the room 54 against 78 to 88 and c4 the fronts' ramp 27.5 against 11 to 22: the old exposure step took 0.85 EV off for whites it expected to clip; e8 is re-exposed through Blender's own pipeline | job01f |
| 09 bookshelf pair | e5 | 4 (e6) | | | e6: six of seven pass (the fronts 228; the white sides 136 and 150; the turntable 58, the engine's walnut record player in place of the white box; the nearer speaker sharp, edge 14.8; the plinths' sheen 65). c4 the roofs' gloss range 24.3 against 28 to 70 | |
| 02a bright room | e5 | 5 | 6.0 | 7.5 | c1 the sky 10.3 to 12.8 (the shaded back wall, most of the frame, 194.7 against 203 to 216: sunny but grey); c2 the sun 4.8 to 2.8 (the lit red candy: the plinth's front 239/48/43, dE 9.3, the fin 10.1, the roof 7.4; the white hides the same 0.5 to 0.7 EV in PBR Neutral's shoulder); c3 the right fill 0.52 to 0.9 (the white side 165.4, a grey panel, and the plinth under it rust, blue 7, hue 41.8); c4 the lacquer ramp on at 20 (the front one value eave to plinth, falloff 1.8: matte card). Out of scope: the horn reads as a soft scoop at this size, which is light on its lip or a higher camera, never the simulated geometry | job02a7 |
| 04b back, three-quarter | e8 | 7 (e9) | | | e9: three of three pass (the hottest flat white 246.4; the roof's red against the plinth's, r 202 in the band 197 to 209, with the rim at 54 degrees; the back's fall corner to corner 19.7 with the key further out). Next: round 8 | |
| 07 exploded | e5 | 5 (e6) | | | e6: six of six pass (the floor behind the product 142.8, the floor light tuned; the side and front apart with the key at -60 degrees, 187.9; the darkest gaps 88.9; the sweep 199.8; the insert and the tweeter out clear of the cabinet, ranges 2.3 and 3.0). Next: round 6 | |
| 09 bookshelf pair | e6 | 5 | 6.0 | 7.5 | c1 the key 55 to 72 degrees (the white fronts one value, falloff 9.1 left and 7.6 right: flat cards); c2 the wall #CFC6BA to #E7DDD0 (the side faces the wall's own value, -3.3 and -5.7: no silhouette, and a mid-grey room); c3 the plinths' sheen faded toward the base, ramp [1, 1] to [0, 1] (a flat pink veil on the left, a 7.0/px step on the right; the letters bluish white, 244); c4 the print's dark band lifted (51.5 on a 150 wall, the heaviest dark between the speakers). Out of scope: a satin clear on the fin (the left fin mirrors the window, dE 26.7 from the right one) | job09e |
| 10 both sizes | e3 | 3 (e4) | | | e4 (job10d's render died for memory; the tuned shot rendered alone): seven of eight pass (the red front's dE 3.7; the sky's wall 140.9; the white 224.4; the red front's ramp 10.8; no glint edge on the white, 0.7; the red side's ramp edge 49.4; the bookshelf turned, its side 159.7). c8 the woofer's glint p95 72.4 against 80 to 175. Next: round 4 | |
| 04b back, three-quarter | e9 | 8 | 5.5 | 7.5 | c1 the rim 54.8 to 80 degrees (its long shadow cut a bright wedge out of the floor from the front-left corner, range 16.3, and left a bright fan right of the plinth, 153.1 against 131.9); c2 the rim 2 to 1.2 W/m2 so the roof's red holds overhead (r 203 now); c3 the rim 0.3 x 0.4 to 0.6 x 0.6 m (the base a smudge, 18 levels, not a contact shadow). Out of scope to the critic: the fin's lettering mirrored in the roof, which the polariser on the card answers, so the engine adds it at 0.9, axis vertical; the amplifier's connections small at this size | job04b10 |
| 07 exploded | e6 | 6 | 5.5 | 7.0 | c1 a 0.15 diffuse share on the drivers' panel (the front, the face with the holes, 209 beside the corner and no brighter than the plain side, 200: a grey card); c2 the key 3.2 to 2.5 (the side's top band 221, the frame's brightest white on its emptiest face); c3 a kick on the insert (its grey body 151 on a 142 floor, edge 6.4); c4 the top lamp 1.3 to 0.7 (the roof's lit slope coral, dE 11.4); c5 a strip for the motors (black holes, p95 28); c6 a neutral sweep (dE 2.8 warm). Out of scope: the insert's hidden body in a colour; the pocket's bore larger; brighter letters; a profile on the trim rings | job07j |
| 02b late sun | e6 | 4 (e8) | | | e8 (the exposure again through Blender's own pipeline, +1.55 EV): four of four pass (the plinth's red dE 5.1; the silhouette's wall 22.7; the woofer's glint 73.5; the gutter 91.0). Next: round 5 | |
| 08 the inside | e6 | 4 (e7) | | | e7: four of five pass (the backdrop behind the roof 125.3; the mid's glint 72.9; the white front 233.2; the cut faces 206.8). c2 the cavities 145.8 against 126 to 140, the on-axis fill at its floor of 0.03. Next: round 5 | |
| 10 both sizes | e4 | 4 | 6.0 | 7.4 | c1 the red side's ramp panel ramped up its height, z 0.25 to 0.75 (it stood on the floor, which mirrored its foot as a hard white wedge beside the floorstander, 179.6 against the oak's 111, and a lavender smear); c2 the exposure 0.7 to 1.0 (the frame a third of a stop low: the white 231, the red plinth dE 3.8, the blue 4.7); c3 the panel 0.95 to 0.72 m tall (the gable end mirrored its top, pink-lilac, dE 25.3); c4 the white point 5200 to 5500 K (the white body cyan, B-R +13); c5 the sun's disc 0.55 to 1.5 degrees (hard notched edges behind the small unit). Out of scope: the horn reads as a dark slot at this size (light and camera only); lighter letters on the 2% plinth | job10f |
| 03 waveguide close | e6 | 4 (e7) | | | e7: six of seven pass (the 105 mm crop on the horn, 73.3 and 39.4; the fill's mirror image off the horn's wall, 94.4; the two cards on the mouth's rim, 126.4 and 113.6; the roof's red dE 3.2). c6 the white still dE 6.4 from neutral with the key on the daylight locus. Next: round 5 | |
| 08b roof section | e4 | 3 (e5) | | | e5 (job08b4's render died for memory; rendered alone, on the CAD with the tweeter in from behind): two of six pass (the bay's edge 2.3; the insert's red 181). c2 the block's fall 4.0, c3 a region that now takes in an edge (range 242), c4 the roof 206, c6 dE 10.5: the section's layout moved with the drawing check's d1, so round 3's regions no longer all mean the same thing. Next: round 4 | |
| 02b late sun | e8 | 5 | 6.0 | 7.0 | c1 the facesheen panel off (the glossy wainscot mirrored it as a grey halo round the carton's top and right, 62.4 against 8.2); c2 the sun 3000 K to #FFBD66 (the white body rose, Lab 91.6/5.7/5.9, the plaster salmon); c3 one panel across the wall (a joint rose out of the fin like an antenna, another edged the sunbeam); c4 the fill 18 to 40 degrees up (the wainscot mirrored it in the top-left corner, 66.5); c5 (asset) a roughness for the wainscot's paint: the engine's new set.wainscot.roughness, eggshell 0.7, with the facesheen back on at 5 | job02b8 |
| 08 the inside | e7 | 5 | 5.5 | 6.5 | c1 the exposure 0.1 to 0.3 (the white front 224, the roof dE 3.7, nothing clipped); c2 (asset) the kick linked to the front, the roof and the horn, which the engine does (now on the card), so the empty sweep right of the product falls back (127.6, as bright as the halo behind it); c3 a glint across the horn's bowl (flat red, p95 104); c4 the key 30 to 18 degrees (the cavity floor 186.9 outshone the bottom panel's cut face, 175.6); c5 (asset) a low strip linked to the plinth alone (maroon, dE 11.2); c6 a glint in the tweeter's housing (42 % crushed). Out of scope: ply stripes on the cut faces; a larger frame | job08f |
| 03 waveguide close | e7 | 5 | 5.5 | 6.8 | c1 the exposure -0.45 to -0.05 (the roof 174/29/33, dE 5.5; the white front 204); c2 an 88 mm lens from the same place (both eave corners cut off, -52 and +46 px past the edges); c3 the target 26 mm up (the fin's top edge out of frame from x 214 to 950). Out of scope: a radius on the insert's outer edge so the seam catches a highlight instead of drawing an outline round the arch | job03f |
| 04b back, three-quarter | e9 | 8 (e10) | | | e10: three of three pass (the floor's wedge gone, range 3.3; the roof's red r 200 with the rim overhead; the base's contact shadow -23.3); the polariser at 0.9 took the fin's mirrored lettering off the roof. Next: round 9 | |
| 02a bright room | e5 | 5 (e6) | | | e6: three of four pass (the shaded wall 206.1 with more sky; the lit red dE 3.4 with less sun; the front's fall 4.9 with the lacquer ramp on). c3 the white side 173.6 against 182 to 196, the fill at its range's top. Next: round 6 | |
| 07 exploded | e6 | 6 (e7) | | | e7: two of six pass (c2 the plain side 186.3; c4 the gable's red 211). The drivers panel's 0.08 diffuse share was read as fully diffuse (a panel's share was a boolean): the front 238 at any share, the key tuned to 1.3 and the top lamp to 0.1 against it, so the insert's body fell to 157; the reflection-only motor strip showed nothing on the ferrite (roughness 0.8: p95 20 to 24 at strength 2 to 11). e8 reruns the round from e6's shot: a panel's share is now a fraction (a twin panel, unseen, carries it), the strip lights the two magnets diffusely, and a tune keeps the tests the one before it left passing | job07k |
| 08b roof section | e5 | 4 | 5.5 | 7.0 | c1 the sweep's pool 1.9 to 1.0 (the backdrop 133, at the insert section's own value, 139: dE 6.9); c2 the key's elevation 45 to 62 degrees (the cut lit head-on: the back panel's cut face falls 9 levels over 250 px, the insert's section 136 to 140); c3 a polariser at 0.8, pass axis vertical (a flat pale-pink wedge, 243/148/152, over a quarter of the bowl); c4 the camera 50 mm left, behind the front's plane (the white front edge-on as an 8 px line down the right edge); c5 the inside lamp 0.70 to 0.50 (the interior, 122, would outshine the backdrop). Out of scope: a satin clear on the insert; a lighter section colour; the cast letter on the back's silhouette; a lighter tweeter frame. e6 renders the CAD of the drawing check's round 2 (the retaining sleeve, the silicone seal), the card's must-show list with it | job08b6 |
| 03 waveguide close | e7 | 5 (e8) | | | e8: three of three pass (the exposure -0.45 to -0.05: the white front 230.2; the 88 mm lens and the target 26 mm up: both eave corners and the fin's top edge in frame, the corners' p5 163.0 and 177.5) | job03f |
| 10 both sizes | e4 | 4 (e5) | | | e5: four of five pass (the ramp off the floor, the oak beside the floorstander 100.5; the white 1.93 from #F2F0EA at exposure 0.95; the gable end's mirror image g 22; the sun's disc 1.0 degree, the small unit's shadow edge 2.2). c4 the white body's cast dE 2.53 against 2.2: 5300 K 3.48, 5800 K 2.74, 6800 K 9.02, so the white point alone does not take it under (the body's cast is the sun's and the wall's, not the camera's) | job10f |
| 02b late sun | e8 | 5 (e9) | | | e9: three of five pass (the shadowed wainscot 21.2; the window bars' shadows 0.3; the fill at 45 degrees, the corner 34.2). c2 the front's sunlit patch dE 8.3 from #EBDCC7: the hex sun (#FFBD66) under a white point set for the 3000 K sun leaves it neutral and 25 levels dark (208/194/186); c5 the front's fall 32 to 38 at any facesheen (2.7 to 8), so the lamp is not what sets it, with the wainscot at roughness 0.7 | job02b8 |
| 05 six flavours | e6 | 3 (e7) | | | e7: three of three pass (the key 7 to 10 m out, the near carton's highlights p95 157.4; the gaps between the cartons lifted, falloff 19.1; the floor between them 84.6). Its mask pass died again for memory (9.7 GB, the waveguide's normals refined on six copies); without that refinement (a flat id mask cannot show it) it ran in 41 s | job05i |
| 02a hero | e6 | 6 | 6.0 | 7.0 | c1 the exposure -0.15 to -0.35 (the white front pinned in the view's shoulder, 247 to 250 over its upper 60 %: falloff 4.9); c2 a reflection panel over the roof's front slope (one value, 80 +/- 2: matte plastic); c3 the sky's horizon #D0ECF8 to #D6EAF8 (the shaded wall mint, a* -1.9); c4 the sun's disc 1 to 0.53 degrees (window patches' edges 14 to 27 px); c5 the lacquer ramp's colour #FFFFFF to 5950 K (its reflection blue on the white, b* -1.8). Out of scope: a lighter or shallower waveguide; a glossier clear on the white; finer sampling | job02a8 |
| 04b back, three-quarter | e10 | 9 | 5.5 | 7.0 | c1 the right flag 1.65 m further right (its shadow a 40-level wedge in the bottom-right corner); c2 the paper #8E8A83 to #B3B1AC (copy space 118.6, comfortable for neither black nor white type); c3 (asset) a contact shadow under the plinth, which the engine now has (set.contact: the sweep's colour darkened by ambient occlusion within 5 cm; the strip under the front corner only 17 levels under the floor 60 px out); c4 the side lamp 0.47 to 0.30 against the lighter paper's bounce. Out of scope: the Hypex plate's white connectors; a glossier clear on the gable | job04b11 |
| 01 hero pair | e6 | 5 (e8) | | | e8: six of eight again. Exposed through Blender's own view transform, the exposure stays at +0.70: c3 (the room, 54.1 against 78 to 88) and c6 (53.3 against 30 to 60) pull it opposite ways, so the room wants light, not exposure; c4 the fronts' ramp 27.5 against 11 to 22 | job01f |
| 08 the inside | e7 | 5 (e8) | | | e8: three of six pass (the white front 235.2; the key at 7 degrees, the bottom's cut face 172.1; the plinth's strip linked to the front, dE 4.25). c2 the empty sweep 77.2 against 90 to 112 once the kick lights only the product; c3 the horn's glint 223 at 1 W, the bottom of its range, against 150 to 212; c6 the tweeter's glint lost its tune to the memory killer (5.3 at 0.3 W). e9 tunes the two glints again | job08g |
| 10 both sizes | e5 | 5 | 6.0 | 7.3 | c1 the flag behind the sideboard 0.46 x 0.42 to 2.2 x 0.72 m (the sun's patch on the wall, 218.7, cut into stripes by both speakers' shadows at product height); c2 a reflection panel over both roofs (the red slope one value, 61.3 to 61.8); c3 the sun #FFEBCD to #FFF2E3 (the sunlit whites cream, b* +4.7); c4 a side ramp for the bookshelf (its side flat, falloff 2.1, against the floorstander's 66.6); c5 a card for the bookshelf's letters (p95 109 on a 65 plinth). Out of scope: a shallower waveguide; a glossier clear; a larger wordmark | job10g |
| 03 waveguide close | e8 | 6 | 5.5 | 6.5 | c1 a graduated card in front of the right flag (the right gable end one value, 38.1, range 1.4: matte); c2 a glint on the arch's crown (its crest highlight breaks for 40 px, 85 against 151 to 159); c3 the paper #A29E98 to #9C9F9E (the sweep rose, chroma 4, 10 to 17 degrees from the red); c4 a crescent on the tweeter's surround (an iris with a catchlight: p95 42); c5 the fin's sheen 1.77 to 1.0 (the fin's left end at the slope's value, 84 against 90). Deferred: a lens shift putting the tweeter at 58 % of the width (a camera move resets the round's regions). Out of scope: the insert's seam outline; the eye-under-a-brow read of the horn | job03g |
| 02b late sun | e9 | 6 | 5.5 | 7.5 | c1 the exposure +0.65 (the sunlit white 170, 68 % of the frame under 40); c2 the woofer's glint off (a blue fan on a black cone, 16/23/42); c3 the sun #FFBD66 to 2600 K (the beam beige, the white near neutral); c4 the fill 2.6 to 1.75 m (it floods the wall facing away from the window, 0.68 of the beam's patch); c5 one glazing bar instead of two (a blue-grey stripe across the face between the drivers); c6 the sky 2 to 4.5 (the window side near black, 9.1). Out of scope: lighter reds in shade; a warmer cone | job02b10 |
| 05 six flavours | e7 | 4 | 6.0 | 7.4 | c1 a polariser, pass axis horizontal (the plinths' sides mirror the floor: the Oat's 76/75/74, dE 14.8 from its brown); c2 the key x0.6 (it strikes the roofs square: the red slope dE 5.1, and parks the white fronts on the shoulder); c3 a strip over the row, linked to the fronts (each front one value, 240.9 to 237.1); c4 the paper #808080 to #8E8E8E (to hold the backdrop once the key is down); c5 a floor card for the cast letters (flat grey print, 141 to 148); c6 the sweep's contact shadow at 0.5 (the cream plinth on a bright halo, 13 over the floor). Out of scope: a satin clear on the plinths; a reshaped waveguide | job05j |
| 04a back, label detail | e8 | 5 (e9) | | | e9: three of four pass (the polariser takes the fin's mirrored lettering out of the roof, range 5.1; the roof's ramp, falloff 11.2; the left edge's kicker, p95 242.1). c3 the letters' sheen card jumps across the band: 0.10 m a range of 153, 0.16 m 135, 0.28 m 14.9 against 24 to 45; 0.28 kept, the letters one grey | job04a7 |
| 09 bookshelf pair | e6 | 5 (e7) | | | e7: three of four pass (the fronts' lower edge -16.4; the plinth's sheen, its edge 1.3; the wall 103.2). c1 the fronts' fall from the key 8.3 against 18 to 32: at 46, 66 and 76 degrees it reads 6.2, 5.4 and 5.1, so the key's height does not set it (the fronts sit on the view's shoulder) | job09e |
| 01 hero pair | e6 | 5 (e9) | | | e9: six of eight, now with the room in (round 5's exposure back, tuned to the room: 82.9; the mid's glint down under it, 45.2). c4 the fronts' ramp 8.3 against 11 to 22; c5 the board seams' edge 16.9 against 6 to 14 at the higher exposure | job01g |
| 04a back, label detail | e9 | 6 | 5.0 | 6.5 | c1 the letters' card 0.28 to 0.24 m (flat grey paint, range 14, 36 under the panel); c2 the roof's ramp x1.9 (falloff 11.1, its lower half the fin's value); c3 a glint into the port's lower wall (a black disc, 44 % crushed); c4 a card for the fin (head-on, over-saturated, dE 3.14); c5 the exposure +0.1 (the shaded side 218). Out of scope: a 5 degree turn; a deeper shadow line; a lighter port flange; a wider frame with the plinth | job04a8 |
| 09 bookshelf pair | e7 | 6 | 6.0 | 7.5 | c1 a reflection-only ramp in front of the pair, 2.2 x 0.62 m at y -1.6 (the fronts fall 7.5 and 10.0 from eave to plinth, and the key's height moved it only 5 to 6 last round); c2 a black card the left fin mirrors instead of the front window (the fin pink, dE 23.7 against the right's 3.4); c3 the fill 0.404 to 0.08 W/m2 (the right side 172 on a 169 wall: no edge); c4 the print 0.62 x 0.82 to 0.5 x 0.66 m (33 px of headroom, the largest shape in frame); c5 a linen rug #A99E8C over the oak's sun patch (the whites pink-cream, a* +2 to +2.9, dE 4.3); c6 the side window 0.4 to 1.1 along (a striped band of sun on the frame's left edge, 195.5 on a 173.5 wall). Out of scope: the right carton turned on its own (a pair stays mirrored); the letters as cast metal | job09f |
| 08 the inside | e7 | 5 (e9) | | | e9: four of six pass (the white front 235.2; the horn's glint 183 at 0.34 W; the bottom's cut face 172.2; the plinth's strip, dE 4.25). c2 the empty sweep 77.2 against 90 to 112 (not tuned this round); c6 the tweeter's glint never lands: the point given is on the frame's cut edge, seen edge-on, which mirrors the frame itself, so the engine skips it (4.4 at 1 and 2 W). Round 6 judges e9 | job08g |
| 01 hero pair | e9 | 6 | 5.5 | 6.5 | c1 the exposure -0.2 (the white fronts in the tone curve's shoulder, every channel over its knee: falloff 12.2 left and 11.0 right, and more front light flattened them further, 7.6 to 5.9); c2, c3 both woofers' glints 2.67 to 1.0 W (a lavender crescent over a fifth of each cone, p95 202 and 184); c4 the roof ramp 1.43 to 0.95 (the slopes pink, dE 11.0 and 8.5); c5 the inner fill 0.51 to 1.4 (the right speaker's shaded side 90, muddy grey). Blocking a 9: the pair small in the frame (40 % of its height), the two whites dE 4.1 apart, the sun on the cabinets as a 12 px strip. Out of scope: a heavier clear coat; the drivers' colours | job01h |
| 10 both sizes | e5 | 5 (e6) | | | e6: three of five pass (the sun #FFF2E3, the whites' b 233; the bookshelf's side ramp, falloff 44 at 1.0; its letters' card, p95 174 at 0.4). c1 the widened flag takes the sun's patch off the wall altogether (49.2 against 100 to 160: the stripes gone, and the patch with them); c2 the roof sheen's tune stopped one proof short, extrapolating past the range (0.8 gave 49.8, 0.19 gives 13.5 against 15 to 45). Round 6 judges e6 | job10g |
| 02b late sun | e9 | 6 (e10) | | | e10: three of six pass (the sunlit white 218.5 at +1.75; the fill at 1.44 m, the wall 43.1; one glazing bar, the face 222.7). c2 the woofer's cone still blue with its glint off (b 30 against 18 or less: the blue is the sky in the cone, not the glint); c3 the 2600 K sun dE 8.78 against 3; c6 the sky: 6.35 gave the window side 24.0 inside 18 to 30, but the tune kept 3.5 (13.0). Round 7 judges e10 | job02b10 |
| 08 the inside | e9 | 6 | 5.5 | 6.8 | c1 the key 7.3 to 18 degrees (the back panel's cut face one value, falloff 8.9, every cut face 187 to 209: a flat diagram; the low key also throws a streak across the sweep); c2 the sweep's contact 0 to 0.5 (the floor under the cut edge 97.3, brighter than the open floor: the base pasted on); c3 the plinth's light 1.48 to 2.0 W/m2 (the red band dark and saturated, dE 4.49). Out of scope: ply laminations on the cut faces; the tweeter's black chamber; a section colour for the cut | job08h |
| 03 waveguide close | e8 | 6 (e9) | | | e9: three of five pass (a neutral paper, dE 1.05; the surround's crescent, p95 79.5 at 4.0 W; the fin's sheen, 68.2 at 1.04). c1 the gable card ran out of proofs going down: 0.6 gave 54.1, 0.2 still 23.3 against 10 to 20; c2 the arch's glint too: 3 W gave 229.8, 1 W still 198.7 against 120 to 160. e10 tunes both again from lower values | job03h |
| 10 both sizes | e6 | 6 | 6.0 | 7.4 | c1 a fill panel 2.0 x 0.6 m behind the flag, facing the wall (the wall behind and between the pair an umber band, 45.6 at 63/43/18 against 154 beside it: the flag that keeps the sun's patch off the wall also shades the window's skylight); c2 the red's side ramp from [0, 1] to [0.4, 1] (its lower back corner 91.5, brown-grey: it mirrors the ramp where it is 0). Out of scope: a glossier clear coat (the fronts read as card at 234 to 244, on the tone curve's shoulder) | job10h |
| 02b late sun | e10 | 7 | 6.0 | 7.5 | c1 the carton turned 14 to -40 degrees (its shadow on the wall reads as a box with clipped corners: the sun sees the ridge 66 degrees off its axis, the roof strip 46.4); c2 the wall #A89E8F to #847B6F (the sunlit upper wall the largest bright shape, 167.5, flat, on the top edge); c3 the fill 0.3 to 0.45 W/m2 (the turned front off direct sun would fall to a grey 103). Out of scope: the woofer's cone colour; a deeper accent paint | job02b11 |
| 04b back, three-quarter | e10 | 9 (e11) | | | e11: three of four pass (the right flag's wedge gone, falloff 2.2; the paper 147.5; the side's light 189.9 at 0.14). c3 the contact shadow under the plinth barely moves with its strength (0.4, 0.6, 0.8 give -22.5, -23.1, -23.5 against -30 to -45): at 5 cm its reach, not its depth, is short. Round 10 judges e11 | job04b11 |
| 02a hero | e6 | 6 (e7) | | | e7: four of five pass (the front's fall 9.3 out of the shoulder; the roof's sheen p95 102.6 at 1.71; the wall neutral, dE 0.84; the window patches' edges 23.4). c5 the lacquer ramp's reflection just short of neutral, dE 1.29 against 1.2. Round 7 judges e7 | job02a8 |
| 07 exploded | e6 | 6 (e8) | | | e8 (round 6 again from e6's shot, a panel's share now real): five of six pass (the white front 231.7 at a 0.15 diffuse share; the plain side 194.8; the insert's body 179.6 at a 2.0 kick; the gable's red 218; the motor's strip p95 60.1 at 18). c6 the sweep still a touch warm, dE 2.86 against 2.0 at #9C9C9C. Round 7 judges e8 | job07k |
| 05 six flavours | e7 | 4 (e8) | | | e8: three of six pass (the polariser, the Oat's plinth dE 5.13; the key x0.6, the red slope dE 2.38; the gap lift 146.9 at 2.07). c3 the front strip moves nothing (falloff 3.0, 2.9, 2.9 at 0.5, 0.9, 0.17): the white fronts sit on the view's shoulder, where added light cannot make a fall; c5 the letter card under the plinths reads 158.4 at 0.8 and at 1.5 W: it does not reach the letters at all (the engine to check, the new polariser first); c6 the sweep's contact at 1.0 still 130.4 against 104 to 122. Round 5 judges e8, its card now saying where the view compresses | job05k |
| 04b back, three-quarter | e11 | 10 | 5.5 | 6.5 | c1 the key 30 to 48 degrees (the back's white band 238.4, paper white, its fall 10 to 16: the hero face over the view's knee, and a 1.7 m shadow smeared up the sweep); c2 the contact's reach 5 to 10 cm (its strength moved the crease only 1); c3 the connectors' glint 2 to 0.4 W (their rims and the rocker 30.7 % clipped: white stickers); c4 a specular kicker for the far-left round (no highlight, p95 190.6). Out of scope: a sheen on the upper back (it would grey the marks' black); darker connector housings | job04b12 |
| 02b late sun | e10 | 7 (e11) | | | e11: three of three pass (the carton turned to -36 degrees, its shadow on the wall now a gable-top carton with its fin, the roof strip 83.3; the wall #847B6F, its sunlit patch 127.5; the fill at 0.24 W/m2, the front 168.0). Round 8 judges e11 | job02b11 |
| 02a hero | e7 | 7 | 5.5 | 7.0 | c1 the exposure -0.3 to -0.9 (the white front in the view's shoulder, 248.4 with a range of 1.2 between the drivers: card); c2 the lacquer ramp 30 to 8 (once off the shoulder, 30 would print a stripe); c3 the right fill 0.7 to 1.3 W/m2 (the shaded side a stop under the front); c4 a wash on the back wall above the speaker (the walls would go grey at the new exposure); c5 the planks' contrast 1.2 to 0.45 (plank swings of 35 hide the sun and the speaker's floor shadow). Out of scope: an off-white lacquer; a lighter red | job02a9 |
| 07 exploded | e8 | 7 | 5.5 | 7.0 | c1 the sweep #9C9C9C to #858585 (the floor between the parts 147, only 49 under the white side: grey on grey); c2 the drivers panel's diffuse share 0.36 to 0.13 (the front baffle p95 234.6, 45 % of its white over the knee); c3 the gloss ramp 1.7-2.4 to 2.1-2.3 m (the roof slope a flat pink veil, dE 8.67, g 74); c4 the white balance 6000 to 6300 K (whites b* -1.8 to -2.8). Out of scope: a flange on the waveguide; the insert's grey body (the owner to confirm it); the letters as metal. For a 9: the camera 15-20 degrees round to the front, the drivers 0.06 m further out | job07l |
| 04a back, label detail | e9 | 6 (e10) | | | e10: four of five pass (the letters' card at 0.225 m, a range of 45.1; the roof's ramp at 23, falloff 23.1; the fin card at 0.9, dE 1.52; the exposure 0.32, the shaded side 223.4). c3 the port's glint aimed at z 0.325, under the port (z 0.359 to 0.451): the engine found the back panel there, so 12 to 66 W gave the tube's lower wall 0.1 to 1.2. A small lamp at the port's mouth, linked to the tube, in its place (e11) | job04a8, job04a9 |
| 05 six flavours | e8 | 5 | 5.5 | 7.4 | c1 the exposure -0.6 to -1.0 (the three whites 234 to 236 in the shoulder, falloff 3.0 to 3.7: paper cards); c2 a ramp on the fronts from just above the eaves (front_strip too weak and far: 0.1 for its whole range); c3 light for the roofs and the bowls (Skim's slope 150.0 against 154.6 of ground above it); c4 a background light behind the right half (the band above the row falls 13 levels toward the shaded sides); c5 the row centred (margins 169 and 117). Out of scope: the letters as metal (the letter card never reached them: it lay under the floor card; raised and see-through now, tuned in the same job) | job05l |
| 02b late sun | e11 | 8 | 6.0 | 7.5 | c1 the exposure 1.8 to 2.05 (the white front 169.9, 30 to 50 under a lacquer white: pinkish-grey card); c2 a reflection card the front can mirror (its x-falloff 0.7: the facesheen sits 84 degrees off its normal); c3 a strip in the letters' mirror path (the letters 30.5 on a 36.8 plinth); c4 the wall #847B6F to #6F685E (the sun patch only 42 under the white); c5 a green tint (the white a* 8.1: pink; the engine's own tint, not on the card, tuned for it). Out of scope: lighter letters; lighter cones | job02b12 |
| 10 both sizes | e6 | 6 (e7) | | | e7: two of two pass (the fill panel behind the flag at 0.18, the wall behind the pair 111.1 from 45.6; the red's side ramp from 0.33, its lower back corner 117.1). Round 7 judges e7 | job10h |
| 09 bookshelf pair | e7 | 6 (e8) | | | e8: four of six pass (the fronts' fall 28.0 from the reflection ramp at 20; the left fin dE 2.4 off its card; the fill at 0.19, the side 148.0 off the wall; the smaller print 153.5). c5 the linen rug turns the bounce near neutral but not quite (dE 3.01 against 2.5); c6 the side window moved 0.7 m back still leaves the left edge band 192.6 against 158 to 182. Round 7 judges e8 | job09f |
| 07 exploded | e8 | 7 (e9) | | | e9: four of four pass (the sweep #858585, the floor between the parts 118.6; the drivers panel's diffuse share 0.10, the front p95 226.5; the gloss ramp from 2.04 m, the roof's g 62.0; the white balance stays 6000 K, the side's b 196.0). Round 8 judges e9: the light settled, the camera move round to the front is next | job07l |
| 10 both sizes | e7 | 7 | 5.0 | 7.0 | c1 the sun 1.11 to 0.7 W/m2 (both white fronts in the shoulder, 241.5 and 234.9: cards beside sides at 172); c2 the red's reflection ramp 6.5 to 1.3 (tuned while its front was compressed; the likely source of a pale patch on the floor); c3 a lamp over the roofs (the red slope dE 4.4, the blue 5.6); c4 the bookshelf's letter card smaller (its plinth mirrors it as a lighter rectangle round the wordmark: linked to the letters instead, see-through for the plinth); c5 a teak sideboard (taupe on taupe). Out of scope: brighter letters; a less glossy roof | job10i |
| 04a back, label detail | e10 | 6 (e11) | | | e11: four of five again; c3 the port lamp at the mouth reaches the tube's lower wall in proportion (0.02, 0.08, 0.2 W give 0.4, 2.1, 4.6; the render 5.8 against 12 to 45): about 1.7 W needed, re-tuned in the next job. Round 7 judges e11 | job04a9 |
| 04b back, three-quarter | e11 | 10 (e12) | | | e12: three of four pass (the key at 51 degrees, the back's white 218.4 in the lacquer range; the contact's reach 0.24 m, the crease 136.4; the connectors' glint at 1.2 W, p95 214.0). c4 the kicker at its top, 0.9, leaves the far-left round at 192.6 against 210, and the sweep mirrors it as a hot white blob at the left: linked to the product only and tuned higher (e13) before round 11 | job04b12, job04b13 |
| 09 bookshelf pair | e8 | 7 | 5.5 | 7.4 | c1 the exposure 0.8 to 0.25 (the fronts 238.6, their upper 60 % within 3 levels: cards); c2 the sky 4.4 to 6.5 (to keep the wall bright after the cut); c3 the lens 57 to 66 mm, c4 and c5 the speakers 0.13 m in (13 % of the frame, at its edges, the art and turntable holding the centre); c6 the art down 0.17 m (a tangent at the top edge at 66 mm); c7 a strip over the sideboard (the roofs held by the key alone; no occlusion at the bases); c8 the front sheen 20 to 6 (the rings a cold white, the plinths' feet pink). Out of scope: darker letters; a more open bowl | job09g |
| 04a back, label detail | e11 | 7 | 5.5 | 7.0 | c1 the exposure 0.32 to 0.09 (the back 232.2, its fall 10 levels all in the shoulder: a printed card); c2 the letters' sheen 0.14 to 0.075 W (the word white on white, 230 on 239); c3 the port's lamp out to 13.5 cm and up 15 cm at 1.6 W, 6300 K (it warmed the flange and left the bore 5.8); c4 and c5 the kickers up for both rounds (+7 and +10 over the panel). Out of scope: a turned carton; a wider frame; a deeper shadow line; a satin flange | job04a10 |
| 07 exploded | e9 | 8 | 6.0 | 7.0 | c1 a pool of light on the sweep behind the parts (117.6 there, range 3.2: the parts float in fog); c2 a low fill for the white side's lower third (it falls 42.5, to 177); c3 a card the side plinth mirrors (its red dE 13.8, G 8); c4 a kick for the mid's cone (47.8: a hole); c5 the white balance 6000 to 6300 K (neutrals b* -2.6); c6 a card for the letters (53.8 on a 47 plinth). For a 9: the view more onto the front (the waveguide 61 degrees off axis). Out of scope: a more open bowl; tilting the insert; finishing its sides; lighter letters, cones or red | job07m |
| 03 waveguide close | e9 | 6 (e10) | | | e10: five of five pass (the gable card at 0.13, the right gable end's fall 15.0; the arch's glint at 0.28 W, p95 157.5; the paper dE 1.05; the surround's crescent 78.9; the fin's sheen 68.2). Round 7 judges e10 | job03h |
| 05 six flavours | e8 | 5 (e9) | | | e9: five of five pass (the exposure -1.17, the Whole's lower white 201.8 out of the shoulder; the front ramp at 0.88, its fall 18.8; the roof fill at 2.13, Skim's slope 144.9 over the ground; the background light at 3, the band above the row -5.3; the row centred). The letter card, raised above the floor card and see-through for the rest, at 1.58: the letters p95 206 (154 before), metal at last. Round 6 judges e9 | job05l |
| 02b late sun | e11 | 8 (e12) | | | e12: four of five pass (the exposure 2.06, the white strip 182.2; the front card at 0.5, its x-fall 11.6; the letters' strip at 0.047, the letters 76.6 off a 41 plinth; the darker wall, the sun patch 117.1). c5 the tint (the engine's, not on the card then): lower is greener, 16 gave dE 10.7, 1.9 gives 4.6 against 4.5, a hair short. Round 9 judges e12 | job02b12 |
| 03 waveguide close | e10 | 7 | 5.5 | 7.0 | c1 a graded reflector on the waveguide wall's mirror ray (the wall a flat facet, one value 113.6 to 109.5: a pale plate; an asset, done as a glint with a ramp, which the engine now builds as a panel on the surface's own mirror ray); c2 the key 30 to 45 degrees (the front 227.1 in the shoulder); c3 a 9-degree snoot on the throat (a near-black pit, R 114 to 149; an asset, done with the engine's spot); c4 a lamp at the surround's lower left (its outline lost there); c5 the fill 1.2 to 1.65 (the shadow side 155.9, the gable end maroon). Out of scope: the notch at the mouth's lower lip (the ribbon's pull groove, 30 x 1.5); a curved wall; a matte dome | job03i |
| 05 six flavours | e9 | 6 | 5.5 | 7.0 | c1 the sweep #8E8E8E to #C0C0C0 (the white sides 140 to 153 on a 105 to 147 ground: silhouettes dissolve, steps of 2 to 10); c2 the key -40 to -28 degrees (it grazes the left sides and the Matcha's green bounces onto the Skim's, a* -3.4); c3 the tint 10 to 4 (whites a* +1.2 to +1.6); c4 the exposure -0.12 for the added light; c5 the background light 3 to 1.2 (a hot spot right of the Oat). For a 9: a 135 mm lens from 18 m for an even rhythm. Out of scope: a rounder bowl; larger rounds; a glossier coat | job05m |
| 01 hero pair | e9 | 6 (e10) | | | e10: three of five pass (the inner fill at 1.4, the right speaker's shaded side 122.6; the roof ramp at 1.02, the slopes dE 6.6; the left woofer's glint 1.49 W, p95 135.1). c1 the exposure down 0.2 to 1.23 leaves the fronts' fall at 15.2 against 18 to 26 (the shoulder is not the only flattener); c2 the right woofer's glint taken to 0.33 W and its p95 still 163.3: the cone's own sheen, not the glint. Round 7 judges e10 | job01h |
| 02b late sun | e12 | 9 | 6.0 | 7.5 | c1 the exposure +0.2 (the front 190.0, under the card's 200-220 for white lacquer); c2 the tint 1.9 to -6 and c3 the colour temperature 3700 to 3550 K (the white salmon, Lab 77/+5.9/+10.1, dE 5.2 to warm white #D9C9B8); c4 the roof-sheen panel moved over the slope's mirror rays (the slope one value, 51.4, only its ridge corner saw the panel); c5, c6 the window 2.5 to 1.6 m high with one bar (the light ran off the top edge, 116 against a 16 to 23 wall); c7 a glint for the woofer's shaded half (median 5.5); c8 the letter kick 0.047 to 0.085 (letters 76.6 on a 44 plinth). Out of scope: the cone's upper-right quadrant (it mirrors its own black interior); brighter letters | job02b13 |
| 07 exploded | e9 | 8 (e10) | | | e10: six of six pass (the background pool at 1.40, the sweep behind the parts 146.8; the low fill at its 0.7 top, the white side's lower third 193.0; the plinth sheen 0.55, the side plinth's g 31; the mid's kick 3.07, its cone 76.3; 6300 K, the white's b 180; the letters' card 0.32, the letters 123.8). Round 9 judges e10 | job07m |
| 01 hero pair | e10 | 7 | 6.0 | 7.0 | c1 the exposure 1.23 to 0.9 (the white fronts median 231.9, p95 239.6, all over the 226 knee: their fall 16.3, compressed); c2 a glint for the left woofer's inner half (23 % of its cone at 3 or under, mirroring the shaded room); c3 the sideboard #897C6E to #705A48 (its sunlit front 125, the wall's sun patch 150 and the cabinets' sides 120 to 202 in one band). For a 9: the two whites within dE 2 (now 4.1, the right one takes more sky). Out of scope: the red at its hex while the white drops; bevelled letters | job01i |
| 07 exploded | e10 | 9 | 5.5 | 7.0 | c1 the sweep #858585 to #9A9A9A (the set a dull 116 to 143 band, corners 117); c2 the tint 10 to 4 (every neutral a* +1.5 to +2.2, the white pinkish); c3 the low fill moved 0.3 m along the face (its rectangle mirrored in the side's clear coat, +12 levels); c4 the insert's kick 2 to 3 (its white 183); c5 a reflection panel for the waveguide's far wall (the bowl one flat red, 59 to 87); c6 the key 5600 to 6300 K (the side's top warm, b* +2); c7 the low fill 0.7 to 1.1 (the side's lower third 194, the plinth dE 9.5). For a 9: the cabinet turned about 10 degrees toward the lens and the explode 15 % longer. Out of scope: the tweeter and insert turned to the lens; larger magnets | job07n |
| 09 bookshelf | e8 | 7 (e9) | | | e9: eight of eight pass (the lens 57 to 66 mm and the pair 0.13 m in, the art lower: the pair larger in the frame; the front sheen at 12.0403, the trim rings and plinths 131.7; the exposure 0.15, the white 217.5; the sky 7.0, the room 180; the strip over the sideboard 0.7, dE 1.65). Round 8 judges e9 | job09g |
| 02a cover | e7 | 7 (e8) | | | e8: three of five pass (the exposure -1.06, the white front 206.6; the right fill 1.0, the shaded side 150.6; the planks' contrast 0.6, range 18.7). c2 the lacquer ramp at 12.0 leaves the front's fall at 28.2 against 10 to 20; c4 the wall wash at 2.0, the wall 198.1 against 180 to 196. Round 8 judges e8 | job02a9 |
| 09 bookshelf | e9 | 8 | 5.5 | 7.0 | c1 the front sheen 12.0 to 4.8 (the upper fronts 236.5, p95 241.6: one value in the shoulder); c2 the roof sheen 0.6 to 1.8 (the slopes flat red, p95 77); c3, c4 both letter glints moved 0.13 m in onto the letters (they sat off the plinths: p95 146 and 168, no specular); c5, c6 a glint on each trim ring (flat grey bands, 123 to 142, between dark hairlines); c7 the sun 1 to 6 degrees across (its shadow's hard edge left a pale panel behind the turntable); c8 the fill 5700 to 10000 K (the shaded sides tan, dE 9). For a 9: the pair matched in size and height, the sideboard's corner out of the frame. Out of scope: the rings' finish; the dark gap round each ring | job09h |
| 03 waveguide close | e10 | 7 (e11) | | | e11: three of five pass (the key at 48.0 degrees, the white front 212.4; the fill 1.8, the shadow side 174.8; the throat's 9-degree snoot 26.275 W, its red 182). c1 the graded reflector on the wall's mirror ray at 0.3333: the wall's fall -3.3 against 7 to 20 (it lights the wall evenly); c4 the lamp at the surround's lower left skipped: that surface mirrors the insert itself, 0.01 m away, so no lamp can sit there. Round 8 judges e11 | job03i |
| 02a cover | e8 | 8 | 6.0 | 7.5 | c1 the lacquer ramp 12 to 3.5 (the upper front 240.9, in the shoulder: its fall all in the lower half); c2 the sun 2.2 to 4.4 and c3 the sky 11.5 to 5.5 (the beam barely on the floor, 121.6 against 127.8: the wall's shadow floats free of the speaker); c4 the right fill 1 to 2.4 (the side 150.6, grey); c5 the wall wash 2 to 2.9 (for the sky taken off); c6, c7 the sun #FFF1E0 and the fill #EAF4FF (the white neutral as the sun's share doubles); c8 the gable sheen 1.7 to 3.8 (the slope matte, p95 68). For a 9: the wall patch glowing 35 over the shade, a crisp contact line. Out of scope: the reds at their hex while the white models | job02a10 |
| 04b back | e11 | 10 (e13) | | | e13: three of four pass. The kicker linked to the product only (receivers *), so the sweep no longer mirrors it as a blob; tuned to 5.6, the far-left round's edge reaches p95 193.6 against 210 (c4): the kicker lights the round's face, not its edge line. Round 11 judges e13 | job04b13 |
| 03 waveguide close | e11 | 8 | 5.5 | 7.0 | c1 the key 1 x 1 to 0.6 x 0.6 m (its mirrored edge a pink glare at the slope's lower-left corner, 138.9 against 85.9); c2 the left-wall reflection graded toward the tweeter (one flat 136 band); c3 the background pool 2.08 to 1.2 (the backdrop's corner 217, brighter than the white front's 212); c4 an asset, a black flag between the key and the front to grade the white base (flat 212, falloff 4): done with the engine's new flag type; c5 a vertical sheen for the fin (one value top to foot). For a 9: a closer lens (about 100 mm) as a separate pass; the white tab at the eave notch (p95 235) confirmed. Out of scope: the notch; the horn's creases; the insert's seam | job03j |
| 04a back, label detail | e11 | 7 (e12) | | | e12: four of five pass (the letters' sheen 0.082 W, the word 183.8 in metal's range; the port lamp out and up at 4.2 W, the bore 18.9; the kickers 4.2 and 5.5, the corner rounds' edges p95 243.6 and 247.8). c1 the exposure was tuned first and set aside at 0.05 and 0.063 (the back 216 to 217, in range) because the left kicker, not yet raised, then fell under its test; left at 0.15 the back is 223.4 against 214 to 220. The engine now tunes a global setting last; job04a11 re-tunes it with the kickers in place | job04a10 |
| 05 six flavours | e9 | 6 (e10) | | | e10: four of five pass (the sweep #C0C0C0, the silhouettes 161.2 behind the Oat; the tint 6, the Whole's front 1.29 from neutral; the exposure -1.35, the front 210.0; the background light 1.84, the ground's fall -4.0). c2 the key's turn does not reach the Skim's green side: -48, -32 and -24 give 9.39, 8.74 and 8.99 against 3.2 (its median 140, 146, 136: still green), so the bounce is not the key's; the card now says so for a swept angle. Round 7 judges e10 | job05m |
| 04b back | e13 | 11 | 5.5 | 7.0 | c1 the paper #B3B1AC to #9E9C97 (the backdrop by the side face 164.4 against the side's 189.9: light grey on grey); c2 the background lamp 0.65 to 0.25 (the copy space one flat 159 to 166, falloff -7); c3 the kicker 5.6 to 0.5 (a clipped 2 px line along the hip and the body's left edge, p95 255); c4 an asset: the plinth band as its own part and a lamp linked to it (the band 7.3 to 11.9 dE from #C62828 while the roof is 3.5; no lamp can lift it without the white above); c5 an asset: a tight contact core (the floor under the plinth 0.76 of the open floor, the wide term at its ceiling); c6, c7 the tint 10 to 7.5 and 5800 to 6100 K (the white lilac and cool, dE 2.1). The engine now has both assets: zone parts (back-panel.plinth, lit by receivers *.plinth) and set.contact.core_strength | job04b14 |
| 01 hero pair | e10 | 7 (e11) | | | e11: two of three pass (the exposure 0.84, the white fronts 211.5 out of the shoulder; the walnut sideboard, the cabinets' ground 80.1). c2 the glint on the left woofer's inner half was skipped: that half of the cone mirrors its own surround, 0.19 m along the mirror ray, so no lamp can sit there; the cone stays at 15.1 against 26 to 42. Round 8 judges e11 | job01i |
| 05 six flavours | e10 | 7 | 5.5 | 6.5 | c1 the sweep #C0C0C0 to #909090 (the ground 164, the same as the white sides' 157 and the Matcha and Oat fronts: four silhouettes step 1.6 to 7; round 6 had lightened it from #8E8E8E for the same reason, the sides then rising with the bounce); c2 the roof sheen 1.53 to 6.0 (the slopes flat, Matcha 49 to 47, the toe cancelling a faint veil on saturated colour); c3 a panel linked to the side faces (the white sides would fall to about 140 with the darker paper's bounce); c4 a kick linked to the mids (flat dark discs, p95 34). Blocking a 9 also: the Skim's green side wants the units spaced wider | job05n |
| 08 the inside | e9 | 6 (e10) | | | e10: two of three pass (the key up to 18.7 degrees, the section's fall 16.9 and its shadow attached; the plinth's lamp at 2.6, the red band 1.63 from #C62828). c2 the contact crease: the sweep's contact term from 0.5 to 1.4 moved the floor under the base 99 to 92 against 70 to 86; past 0.9 its multiplier turns negative, so the card now gives the term a range, and the engine has a tight contact core for this | job08h |
| 01 hero pair | e11 | 8 | 5.0 | 6.3 | c1 a warm lamp linked to the fronts (the right white 4.4 dE cooler and darker than the left: the toe-in turns it from the sun); c2 the inner fill linked to the left side only (it lit the sideboard's right end inside the right speaker's sun shadow, 88 against a shadowed top of 22); c3 a lamp linked to the gables (the red 7 to 8.4 dE dark, maroon); c4 a new glint where the left cone's mirror ray clears its surround (31.9 % crushed); c5 the print 1.55 to 1.32 m (floating, crowding the top); c6 the planks' contrast 1.1 to 0.6 (one plank 19 levels over its neighbours in the copy space); c7 the plaster's bump 0.1 to 0.3 (a featureless wall under a raking sun) | job01j |
| 02b late sun | e12 | 9 (e13) | | | e13: seven of eight pass (the exposure 2.35, the white front 204.3; 3450 K and tint -3, the white 1.39 from warm white, its blue 188; the roof sheen over the slope's mirror rays, its fall 23.8; the window shortened, the light closed inside the frame, one bar; the letters' kick 0.079, 121.1). c7 the glint for the woofer's shaded half was skipped: the cone there mirrors itself 0.17 m off, so the lamp stood behind it (10.9 against 12 to 32); the engine now moves such a lamp in front of what the surface mirrors, from the next job | job02b13 |
| 08 the inside | e10 | 7 | 6.0 | 7.3 | c1 a lamp linked to the tweeter's frame (its rear chamber a black slot, 88 % crushed); c2 the plinth band split off as its own part (the engine's zone parts) so c3 can take the kick off the white face and keep it on the band; c4 a lamp linked to the white face (235, flat above the knee); c5 an asset: the key's long cast shadow lightened on the sweep alone (a band 75 against 83 and 86 across the copy floor), which the engine now does with lights.key.shadow_on_set: a copy of the key the product does not block lights the set with part of its power | job08k |
| 02b late sun | e13 | 10 | 6.0 | 7.5 | c1 the wainscot #5F6B5C to #6A685E (the sun on the panelling olive, 13.2 dE from its own gold on the plaster above the rail); c2 the letters' kick 0.079 to 0.13 (the wordmark one flat grey, 121, reading as print); c3 a glint on the woofer's dust cap (57 % crushed). The cones' shaded halves were out of scope for it (a concave cone mirrors itself); the move-in rule now places round 9's glints there | job02b14 |
| 09 bookshelf | e9 | 8 (e10) | | | e10: eight of eight pass (the front sheen 1.17, the upper fronts p95 225.0 out of the shoulder; the roof sheen 1.86, the slopes' p95 116.0; both letter glints on the letters at 0.017 and 0.013 W, p95 192.9 and 198.2; a glint on each trim ring, 156.7 and 158.9; the sun 4 degrees across, the shadow's edge 0.7; the cooler fill, the white sides 5.99 dE). Round 9 judges e10 | job09h |
| 08b roof section | e5 | 4 (e6) | | | e6: two of five pass (the key's fall and the inside lamp, 98.4; the near edge's p95 168.4). c1 the pool at 0.5 left the sweep behind the cut at 129.1 against 88 to 110; c2 the key's elevation, 50 set aside for breaking c5, 62 giving a fall of 10.2 against 14 to 28; c3 the polariser does not move the reflection on the slope (170.1 against 70 to 140). The shot still shows the old sleeve: it is re-rendered on the CAD of drawing check round 8 (the ø70 body and its cap) before round 5 judges it | job08b6 |
| 04b back | e13 | 11 (e14) | | | e14: six of seven pass (the darker paper, the backdrop by the side 138.2; the background lamp 0.19, the copy space falling -19.0; the kicker 2.6, the hip's line p95 232.2; the plinth split off and lit alone at 0.40, its red 4.41 dE from #C62828, from 7.3; tint 7.5 and 5821 K, the white 0.86 from neutral). c5 the contact core at its 0.9 ceiling moved the floor under the plinth only to 110.6 against 68 to 100: its 25 mm reach is the lever left | job04b14 |
| 04b back | e14 | 12 | 5.5 | 6.6 | c1 a narrow strip panel for a reflection on the white side (one diffuse ramp, 185 to 196: matte paint); c2 the contact core's reach 0.025 to 0.05 m (at 3.4 m a centimetre of floor is 1.5 px, so the tight term sat inside the edge's anti-aliasing); c3 an asset: a net over the foreground floor shading the key alone (the floor at the frame's foot, 154.9, brighter than the backdrop by the product), which the engine now builds as a flag with a density and a lamp scope; c4 the roof's gloss panel 0.51 to 1.3 (a faint even ramp near Brewster's angle under the polariser); c5 the plinth's lamp 0.40 to 0.8 (5.45 dE at its right end) | job04b15 |
| 09 bookshelf | e10 | 9 | 5.5 | 6.8 | c1, c2 the plinth bands split off and lit alone (8.5 and 9.8 dE, maroon beside a correct gable); c3 the sideboard #8A7D6F to #B3A086 (a dull slab 100 levels under the whites); c4 the tint 10 to 6 (every neutral magenta); c5, c6 a window reflection on each front (flat within 4 levels); c7 the print 0.5 x 0.66 to 0.4 x 0.53 m (it outweighed either speaker); c8 the sky 7 to 8 (the room dim, its wall 15 to 22 L* under its paint). Blocking a 9 also: the camera's 15 degree yaw makes the right speaker 10 % taller than the left | job09i |
| 07 exploded | e10 | 9 (e11) | | | e11: four of seven pass (the sweep 165.0; the low fill off the side's clear coat, the falloff -1.2; the insert's kick 3.02, 203.4; the low fill raised to 0.75, 202.0). c2 the tint at its best still leaves the white 2.5 dE from neutral; c5 the waveguide's reflection panel at 2 moves the far wall's p95 only to 91.2 against 120 to 170; c6 the key's colour 1.92 dE from the fill's. Rendered on the old render model (the container restart); the rebuilt models, the ø70 tweeter body and its cap, are in from the next job | job07n, job07nr |
| 03 carton | e11 | 8 (e12) | | | e12: three of five pass (the smaller key 79.1; the backdrop's pool 1.3, 193.2; the flag's top edge at 0.76 m, the eave's fall 24.0). c2 the rim panel's ramp did not move the waveguide's left wall (136.9 at 0.05 and at 0.4), so the wall mirrors something else; c5 the fin's vertical sheen panel did not move the fin either (-1.8 at 0.4 and 0.9) | job03j, job03jr |
| 10 both sizes | e7 | 7 (e8) | | | e8: five of five pass (the sun 0.47, the white fronts 214.4 and 217.1 out of the shoulder; the red's reflection ramp 0.97 for the darker front; the lamp over the roofs at 1.5, their colour 2.79 dE; the letters' panel linked to the letters, the plinth's rectangle gone, r 3.0; the teak sideboard 94.5). The first frame with the engine's mirror map in its card | job10i, job10ir |
| 04a back, label detail | e11 | 7 (e13) | | | e13: five of five pass (the exposure re-tuned last with the kickers at their values, the back 217.2; the word 178.0; the bore 17.1; the corner rounds' edges p95 242.5 and 246.9). Then retouched in place (the engine's new retouch, no re-render): the back's cast and the red's hue to their swatches, dE 0.8 and 1.46 to 0.0 and 0.07 on their lit faces; still five of five | job04a11 |
| 02a cover | e8 | 8 (e9) | | | e9: five of eight pass, retouched (the sky down to 0.95 for the front, 205.6; the lacquer ramp 0.52, 215.0; the right fill 2.0, the shaded side 166.0; the wall wash 1.9, 193.1; the gable sheen 4.5, p95 112.2; the right fill's blue 1.75 dE once the retouch took each white pixel's own cast). c2 the sun at 3.5 (its least proof) gives the shadow's step -12.5 against -13; c3 the floor by the plinth 186.0 against 200 to 212; c6 the sunlit lower front 5.3 dE from #CFCFCF, nearly all lightness. The retouch: the white's cast 5.28 to 0, the red 10.58 to 5.34 (half its lightness left) | job02a10, job02a10r |
| 05 six flavours | e10 | 7 (e11) | | | e11: four of four pass, retouched (the sweep darker as given, 120.3; the roof sheen 4.35, its ridge-to-eave fall 17.8; the side panel 1.4, the white sides 158.0; the mids' kick 6.0, p95 47.8). The retouch: the whites' casts to 0, the six accents from dE 3.1 to 8.2 to 1.1 to 4.4, the coloured bodies (matcha 12.6, oat 11.8, chocolate 6.0) to 6.3, 6.0 and 3.2, half their lightness left | job05n |
| 08 the inside | e10 | 7 (e11) | | | e11, on the rebuilt render model (the ø70 tweeter body and its cap): three of five pass, retouched (the white face's lamp 1.06, 215.0; the kick on the white at 215.0; the key's shadow on the sweep at 0.16 of its density, the copy floor 83.2). c1 the tweeter's chamber 22.9 against 10 to 22 (its lamp at the least proof, 0.67; 21.4 at 16 samples); c2 the plinth band 3.92 dE, its lightness: the retouch takes its hue to the swatch (1.65 to 0.72 on its lit face) | job08k |
| 08b roof section | e5 | 4 (e7) | | | e7: the shot as round 4 left it, re-rendered on the CAD of drawing check round 8 (the tweeter's ø70 body in its bay, its cap) and retouched (the red 10.47 to 3.17 on its lit face, the insert 5.26 to 2.05, the white's cast 4.03 to 0); two of five pass as at e6. Round 5 judges e7 | job08b7 |
| 02b late sun | e13 | 10 (e14) | | | e14: three of three pass, retouched with the white's warmth kept (neutral 0: the late sun's gold is the picture) and the reds matched as the swatch reads in that light (the wainscot's sun 3.08 dE from the plaster's gold; the letters' kick 0.14, the wordmark 163.5 as metal; the dust cap's glint 0.17 W, p95 119.1). Glints placed by the move-in rule from this round | job02b14 |
| 01 hero pair | e11 | 8 (e12) | | | e12: three of seven pass, retouched (the inner fill linked to the left side, the sideboard's end 42.9; the gables' lamp 1.13, their red 2.31 dE; the print lowered). c1 the right front's warm lamp made the pair worse with power (3.25 at 0.25 W/m2, 5.27 at 0.5); retouched, both fronts neutral, 2.62 against 2.5; c4 glint 7 did not move the left cone (15.1 at 1.5 and 3 W: its surface mirrors something else); c6 the planks' contrast barely moves the floor (81.8 to 84.3 across 0.2 to 0.8); c7 the plaster's bump barely moves the wall's range (1.9 to 2.2): neither is that test's lever | job01j |
| 07 exploded | e11 | 10 | 5.5 | 6.5 | c1 the bowl's sheen panel moved to where the far wall's reflections meet the gloss panel (the first place the critic traced was mirrored by 15 % of the bowl in the engine's new precheck; re-placed with the mirror map, 98 %); c2, c3 the plinth bands split off and lit alone (dE 8.2 and 6.4 on the bands, 0.9 on the roof); c4 a lamp on the tweeter's face (82.6, barely above its body); c5 6300 to 6150 K (a b* +1.5 to +2.1 cast); c6 a glint on the fin's top round (the frame's only accents on one corner round) | job07o |
| 03 waveguide close | e12 | 9 | 6.0 | 7.2 | c1 an opaque graded panel between the waveguide's left wall and the fill: the mirror map, made to follow the render's ray visibility this round, showed the band is the fill (0.45) plus the see-through glint5 (0.25), both even, so no ramp on rim_left or glint5 could grade it; the precheck: 99 % of the band mirrors the new panel; c2 the sweep #9C9F9E to #7C7E7D (the white body 13 levels under its backdrop on the right); c3 fin_sheen's ramp along z (100 % of the fin mirrors it; fin_vsheen hung behind it) | job03k |
| 10 both sizes | e8 | 8 | 6.0 | 7.8 | the first round with the mirror map in its card: c1 the roof lamp linked to the roofs (the empty wall above the pair the brightest set area, 200.4); c2 the red front's ramp 0.97 to 4 (falloff 11.3 against the blue's 22.9; it mirrors the ramp 95-97 %); c3 a card for the red's letters (they mirror the floor 93.6 %); c4 an asset, the sideboard in a veneer (a regular 4 px pinstripe): the engine's new veneer material; c5 the wall flag nearer (a 0.94 levels/px band); c6 the blue side ramp linked to its side (the gable end mirrors it 100 %, lavender, dE 21.1); c7, c8 the plinth bands split off and lit alone | job10j |
| 04a back, label detail | e13 | 8 | 5.5 | 7.0 | the first round judged on a retouched frame: c1 the key 1.6 to 1.0 m tall (the back falls only 17.9 levels); c2 a lamp on the woofer's motor at the port's far end (99 % crushed); c3 a graded panel the letters mirror (flat at 176-180; precheck 86 %); c4 their glint disc off (the word's ends fall 40 levels as they leave it); c5 the exposure 0.05 to -0.06 (the top zone in the shoulder, 231.9); c6 a net evening the backdrop's bottom corners (156.8 against 145.6) | job04a12 |
| 02a cover | e9 | 9 | 6.0 | 7.2 | c1 the sky 0.95 to 4 (the room's left half at dusk: far wall 132.8, skirting 90 against 224); c2 glint2 3 to 2.2 W (the front's upper left at the knee once the sky is up); c3 the retouch's lightness 0.5 to 0.9 (the red 5.8 L* dark); c4 the planks' contrast 0.6 to 0.3 (the sun's floor shadow hidden among 11-16 level plank steps); c5 a panel for a highlight on the front-side round (precheck: half the 4 px strip, the round itself). Blocking a 9 also: the white exactly neutral beside a warm wall (the retouch now keeps a quarter of its cast and holds the reds on the plain swatch, retouch.adapt 0) | job02a11 |
| 05 six flavours | e11 | 8 | 5.5 | 7.0 | c1, c2 the plinth bands split off and lit by a long low panel (Skim's band dE 14.2 against its roof's 3.1, the cream 12.6, the red 8.6, the blue 7.5); c3 the retouch's lightness 0.5 to 0.8 (Matcha and Oat fronts 5.4 and 5.5, nearly all lightness); c4 a flag behind the row so the shaded sides stand off the ground (4 levels at Skim's edge); c5 the cove's right lamp 1.84 to 0.5; c6 a broad lift linked to the fronts (the whites at 200-205) | job05o |
| 03 waveguide close | e12 | 9 (e13) | | | e13: three of three pass, retouched; the first round prechecked on the layered mirror map (the opaque wall panel 4.64 grades the waveguide's left wall, the foot box 105.2, where the rim panel's ramp (round 8) and glint5 could not; the sweep #7C7E7D, 144.4; fin_sheen's ramp on z at 1.6, the fin's fall 13.0). The retouch: the red 3.56 to 1.62, the insert 4.93 to 2.02, the whites' casts to 0 | job03k |
| 02b late sun | e14 | 11 | 6.0 | 7.5 | c1 the woofer's glints at 3200 K (the anodised cone blue, b* -32 on the cap: the glint lamps' colour, a key the card had not listed); c2 the sun 2600 to 2400 K (the patch beige, dE 3.94 from gold); c3 the retouch keeps less of the white's warmth (neutral 0 to 0.4: cream on the front, peach on the side); c4 roofsheen's ramp onto the slope's reflections (the precheck found the ridge on the ramp's dark end, 0.05 to 0.27, not the 0.76 assumed; the critic moved it); c5 the letters' card linked to the letters (a stripe across the plinth); c6 the sun 0.3 to 0.53 degrees (2 px shadow edges) | job02b15 |
| 08 the inside | e11 | 8 | 5.5 | 6.5 | c1 the inside lamp's reflection off the far wall (a hard stripe behind the mid-divider); c2 a net from the key over the lower section (every cut face one value); c3 the sweep's core under the cut edge (a 1 px contact line); c4 the plinth lamp nearer (the white face under the woofer at 236). Out of scope and the largest CG tell: the plywood's plies, unresolved at 2 mm a pixel | job08l |
| 08b roof section | e7 | 5 | 5.0 | 6.8 | c1 the sweep #C9C5BE to #97948F (the section at the backdrop's value, a hole); c2 the mouth lamp twice the size: the pale plate across the bowl the critic traced to it, with its specular at 0, was Cycles ignoring a lamp's specular factor (the engine now hides it from glossy rays: the plate is gone); c3 a lamp for the tweeter's black parts (55 % crushed); c4 the retouch's match 1 to 0.2: its reference had come off a pale grazing face, pushing the lit slope into G = 0 (the engine now reads it off the most saturated lit pixels: 3.19 dE at match 1) | job08b8 |
| 01 hero pair | e12 | 9 | 5.0 | 6.5 | c1 the oak's rings 60 to 16 (no figure in the planks); c2 a panel for the left woofer's crushed half (the precheck: 10 % of it mirrors the panel, and glints 6 and 7, now moved in by default, reach 35 %; sent back to the critic); c3 the wall lighter (the shade L* 26, mauve); c4 the sideboard in veneer; c5 the oak's gloss variation down (bars under the cabinets); c6, c7 the plinth bands split off and lit alone (5.02 dE) | job01k |
| 03 waveguide close | e13 | 10 | 5.0 | 6.0 | c1 a graded panel glint for the waveguide floor (one flat value, falloff -1.5, mirroring the top panel 100 %; the precheck: 68 % of the strip mirrors the new glint); c2 rim_left's ramp 0.05 to 0.5 at its low end (the left rim's line fades over its lower 40 %); c3 rim_right +35 %; c4 the surround's glint x5 (a featureless black ring). Out of scope, again: the white notch in the insert's front lip, the brightest thing in the frame: it is the pull loop's groove (BOM line 35), empty in the render model; the ribbon is now modelled in it | job03l |
| 07 exploded | e11 | 10 (e12) | | | e12: four of six pass, and two engine bugs found. The bowl's sheen panel, re-placed with the mirror map, passes first time (p95 145.4 at 2.51); the tweeter's lamp 5.44, 124.5; the fin's glint 4.55, 236.1. But the plinth bands were not split off in an exploded view, so plinth_fill's '*.plinth' matched nothing, and Cycles lights everything from a lamp with an empty receiver list: the white side 200 to 234 (c2) and 5.85 dE off neutral (c5). Both fixed in the engine; e13 re-renders the round with plinth_fill re-tuned on the bands alone. e12 is not sent to a critic | job07o |
| 04b back | e14 | 12 (e15) | | | e15: five of five pass, retouched (the side's strip panel 2.7, its reflection 206.0; the contact core's reach 0.06 m, the floor under the plinth 96.2; the net over the foreground floor at 0.49 from the key alone, 134.2; the roof's gloss 1.45, its fall 22.3; the plinth's lamp 1.0, its red 1.16 dE) | job04b15 |
| 09 bookshelf | e10 | 9 (e11) | | | e11: seven of eight pass, retouched (the plinth bands split off and lit alone at 1.8, their red 0.84 and 0.75 dE, from 8.5 and 9.8; the lighter sideboard 144.6; a window reflection on each front, p95 229.0 and 231.0; the print smaller, 176.8; the sky 7.8, the room 188.2). c4 the tint moves the neutrals little (1.65 at 6 and at 10): the retouch now takes the product's whites to neutral in any case | job09i |
| 04a back, label detail | e13 | 8 (e14) | | | e14: four of six pass, retouched (the key 1.0 to 0.9 m tall, the back's fall 29.0; the woofer's motor lamp 0.8 W, 12.9; the letters' glint off, the 'e' even, 0.8; the net from the key at 0.46, the backdrop's foot 140.6). c3 the letters' ramp panel runs the wrong way: the falloff goes negative with strength (-11.6 at 0.23, -50.2 at 1.1), so the letters mirror its bright end at their baselines; c5 the exposure at -0.3 reached the top zone's 219 but broke a test that passed at the first two proofs, so -0.1 (231.0) was kept | job04a12 |
| 09 bookshelf | e11 | 10 | 6.0 | 6.8 | c1 the sideboard in the engine's veneer (a 6.4 px vertical ribbing, a cardboard slab); c2 a strip linked to the woofers (the cones at 14, their upper half 7-8); c3 the roof sheen 1.86 to 1.0 (the right slope coral, dE 11.3, where it mirrors the ramp's bright end; the precheck: the patch mirrors roof_sheen 100 %) | job09j |
| 04a back, label detail | e14 | 9 | 5.0 | 6.5 | c1 the letters' ramp panel moved up onto their reflection (they meet its plane at z 0.78 to 0.83, above round 8's ramp at 0.73 to 0.78, so they saw its flat top, the ascenders the sky past it; the precheck: 93 %, running top-bright); c2 the roof's ramp 23 to 45 (the slope at Brewster's angle under the polariser, falloff 10.7); c3 the key 2.8 to 2.1 (the back's hot corner at 231, the exposure's -0.3 having broken the floor's test) | job04a13 |
| 04b back | e15 | 13 | 5.5 | 6.8 | c1 the sweep #9E9C97 to #7F7D79 (the whole set inside 121-149); c2 a pool lamp on the cove behind the product (specular 0); c3 a panel for the back panel's top band (it mirrors the unlit sky 99 %; the precheck: its ramp sat above the band's reflections, z 0.61 to 0.69 against 0.72 to 0.84, radiance 0; sent back); c4 the retouch's match 1 to 0.5 (the shaded side plinth pushed x1.28 to G = 0: the retouch now matches a face to the swatch at its own lightness, (154, 30, 30) at match 1) | job04b16 |
| 10 both sizes | e8 | 8 (e9) | | | e9: five of eight pass, retouched (the roof lamp linked to the roofs, the wall 149.0; the letters' card 0.28, 171.7; the sideboard in veneer, grain 0.55, range 19.8; the blue side ramp linked, the gable end 11.99 dE). c2 the red front's ramp overshoots at the final (24.0 against 17 to 23; proofs 9 to 14); c5 the wall flag's band 0.7 against 0.5; c8 the plinth 5.98 dE: the retouch now matches a face to the swatch at its own lightness (changed mid-job), so its lightness is the plinth lamp's to lift | job10j |
| 08 the inside | e11 | 8 (e12) | | | e12: three of four pass, retouched (a net from the key over the lower section, density 0.28, the back panel's cut face falling 35.6; the sweep's contact core 0.9, the floor under the cut edge 74.4; the plinth lamp nearer, the white face below the woofer 222.0). c1 the inside lamp's specular off left the far wall at 177.5 (178.5 before; test 135 to 165): with the lamp shares honoured, the stripe is the lamp's diffuse light on the far wall, not its reflection | job08l |
| 10 both sizes | e9 | 9 | 5.5 | 7.0 | c1 the veneer's grain 0.55 to 0.22 and c3 its rings 0.022 to 0.011 m (the doors a topographic map: 14-18 level drops at every ring, rings 21-44 mm apart); c2 a net over the top of the back wall (flat 141-152 from the roofline to the frame top); c4 lens shift 0.04 (287 px of wall left of the hero, 82 right of the sideboard); c5 the retouch's lightness 0.5 to 1 (the red band 5.98 dE); c6 the planks apart, 0.4 to 0.7 (the near floor one tone); c7 the plinths split in this two-product frame (round 8's plinth kick lit nothing: `product.zone_parts` was not read for a `products` list; the engine now holds it for every block) | job10k |
| 05 six flavours | e11 | 8 (e12) | | | e12: four of six pass, retouched (the plinths split; the plinth lift 3.5, the bands 1.65 dE; Matcha and Oat 2.4 dE at the retouch's lightness 0.9; the flag behind the row at full density, the far floor 96.0). c5 the cove between the Chocolate and Oat roofs 31.1 against 96 to 106: the full-density flag took it into its shadow; c6 the white fronts 168 against 209 to 216 with the new front lift at its 1.25 limit | job05o |
| 08 the inside | e12 | 9 | 5.5 | 6.3 | c1 a net on the cabinet's far wall and c2 one over its floor, scoped to the key and the fill (the divider's cut face 19 over the wall behind it, the mid-shelf's 7, the bottom panel's level with the floor behind it: the inside one flat plane); c3 a ramp on the key's light on the set alone (the empty lower-left floor the brightest in frame): not in the engine, pending. Out of scope: the cut capped cleanly at the shadow lines (dark diagonal hairlines across both cut corners), ply lines on the birch's cut faces, the amplifier module modelled | job08m |
| 02a cover | e9 | 9 (e10) | | | e10: three of five pass, retouched (the red 0.44 dE at the retouch's lightness 1; the planks 0.31, range 9.1; the round's edge panel at 20, p95 228.4). c1 the sky at 3 left the far-left wall at 145.7 against 146 to 168 (its proof 146.5); c2 glint 2 at its 4.2 limit left the front's upper-left quarter at p95 215.6 against 218 to 229 | job02a11 |
| 08b roof section | e7 | 5 (e8) | | | e8: one of four passes, retouched (the roof band 2.55 dE at match 1). c1 the sweep #97948F printed 85.6 against 92 to 108; c2 the mouth lamp 1.2 m square took the bowl's far-wall plate to G 41 against 70 to 108 (from a pale pink to a deep red: the larger lamp's lower radiance overshot); c3 the snoot at its 4.8 limit left the tweeter's rear cup at 4.8 against 12 to 34: it does not reach into the cup | job08b8 |
| 02b late sun | e14 | 11 (e15) | | | e15: three of six pass, retouched (the body white 3.94 dE from neutral at the retouch's neutral 0.5; the roof's sheen panel at 0.23, a ridge-to-eave range of 33.7; the sun's disc 0.70 degrees, the silhouette's edge 29.8). c1 the woofer's glints warmed to 3200 K left it 5.98 dE from #2E2E2E against 5.5; c2 the sun at 2600 K (its limit in the tune) left the patch 3.68 dE from #9B7A50 against 2.5; c5 the letter kick linked to the letters left the plinth's strip behind the wordmark at 62.8 against 42 to 53 | job02b15 |
| 03 waveguide close | e13 | 10 (e14) | | | e14: one of four passes, retouched, with the ribbon in the pull loop's groove (the right rim 152.6 at rim_right 18.5). c1 the graded glint 6 for the waveguide's floor left its falloff at -1.0 against 14 to 28 at every strength tried (to 0.07); c2 the left rim's ramp from 0.5 left its lower 40 % at p95 95.6 against 120 to 160; c4 glint 3 at 12 W left the tweeter's surround at p95 27.6 against 55 to 95: a glint only reflects now, and the rubber's wide lobe spreads it to nothing | job03l |
| 07 exploded | e11 | 10 (e13) | | | e13: six of six pass, retouched, with the plinths split in the exploded view (the bowl's sheen panel, p95 147.3; the white side 202.0; the plinth fill at 2.36, the band 2.36 dE; the tweeter's kick, 113.0; white balance 6150 K, neutral 0.0; glint 0 at 4.7 W on the roof's edge, p95 240.8) | job07p |
| 05 six flavours | e12 | 9 | 5.0 | 7.5 | Read through the card's new light notes: c1 the flag behind the row off (a black slab across the cove that took the key's light from the frame: the white fronts fell from 203 to 168 when it went in); c2 exposure -1.35 to -1.25; c3 the paper #909090 to #707070 (round 8's flag's job, the sides off the floor, by tone); c4 the polariser 0.85 to 0 (the side faces and plinth sides mirror the floor card at 0.93-0.99 and show none of it); c5 a contact core under every plinth; c6 the front lift linked to the fronts alone off (18 % of the fronts' light that the floor never gets). A blind side-by-side of e12 against a relit proof (a coherent rig, strong cards) had scored them 5.0 and 4.0 the same morning | job05p |
| 02b late sun | e15 | 12 | 6.0 | 7.0 | c1 the speaker turned -36 to -40 (the sun side seen at 82 degrees, a 25 px sliver); c2 the front's sheen panel wider and linked to the front and its rings (the woofer's cap mirrored it as a hard sliver; the precheck: 100 %, running the right way); c3 the sun 2600 to 2300 K (the patch tan, C* 21); c4 brush ridges in the wainscot's paint (a new engine setting, `set.wainscot.relief`: the sunlit panelling 2.8 levels across a 60 px square). Out of scope: the woofer cone's reflectance (bronze where it mirrors the sunlit floor) | job02b16 |
| 08b roof section | e8 | 6 | 5.5 | 7.0 | c1 the bowl's reflection card moved to where the bowl's core mirrors (it mirrored the sky 77 %; the precheck: 78 % on the card); c2 the backdrop #97948F to #6D6A67 (the red isoluminant with it, separating by hue alone); c3 the polariser 0.8 to 0; c4 the key from azimuth -10 to 20 (the cut evenly lit side to side); c5 the pool lamp moved in front of the back wall (it stood behind it and lit nothing). Out of scope: the lacquer on the counterbore's faces, the ribbon at the mouth (a 6 px line), a back letter's tab at the left edge, the sleeve's and cup's black | job08b9 |
| 02a cover | e10 | 10 | 6.0 | 7.4 | c1 the sky 3 to 8 (the window side the room's darkest: 145.7 against 210.9 at the far end); c2 the sun 3.5 to 4.0 (the sunlit front 189.6 under the sunlit wall's 228.7); c3 the lacquer ramp 0.52 to 4.0 (92 % of the front mirrors it at 0.05 of 0.52: 2 levels; the precheck: running top-bright); c4 window 0's head up 0.1 m (the patch's edge collinear with the eave); c5 glint 2 down to 1.0 W (a flat 215 disc on the front); c6 the roof's sheen panel 4.5 to 1.5 (the slope salmon, 18.4 dE); c7 the right fill down to 1.5 (a floor pool on the side with no window) | job02a12 |
| 01 hero pair | e12 | 9 (e13) | | | e13: five of seven pass, retouched (glint 7 at 0.05 W, the left woofer 38.5; the wall #C8BCAB, 81.5; the sideboard in the reworked veneer at grain 0.6, range 22.9; the plinths split and filled, 2.36 dE; the white 218.0). c1 the oak's rings 16 left a plank's range at 2.9 against 6 to 16: at this scale the grain is under a pixel; c5 the oak's gloss variation at 0.05 left the light bars' falloff at 4.6 against -3 to 3 | job01k |
| 04a back, label detail | e14 | 9 (e15) | | | e15: three of three pass, retouched (the letters' ramp on their reflection at 1.45, a 30.8-level ramp from ascenders to baselines; the roof's ramp at 32, falloff 18.2; the key 2.4, the back's hot corner 223.0) | job04a13 |
| 03 waveguide close | e14 | 11 | 5.5 | 6.5 | c1 exposure -0.1 to 0.1 (the white body 194, light grey beside the red); c2 the dome's glint x1.5 (a dim catchlight, p95 131); c3 the left rim's panel x1.6 (the outline fades over the lower left: 104-121 against the right rim's 155-192). Out of scope: a contrasting finish on the insert (it takes the accent, so the horn's lower half sits at the slope's value), a deeper lip at the mouth (the profile is acoustic), a satin surround (glint 3 moved it under a level from 4 to 24 W) | job03m |
| 07 exploded | e13 | 11 | 6.0 | 6.7 | c1 the dome 0.55 to 0.38 (the front's upper-left third at 231, in the shoulder; the ground one even grey); c2 a lamp over the parts that lights the sweep alone, so the drivers lay soft shadows on the floor (asked as an asset; the engine now takes a set piece's name in `receivers`); c3 the bowl's sheen ramp from 1.8 down to 1.65 m (its lower far wall mirrors the ramp's dark end: 154 to 82 in 20 px); c4 the side's linked low fill down with the dome. Out of scope: the insert's white wall cool against the cabinet (a* -2, b* -1.8), the drawn-out insert turned to show its throat (each part leaves along its own axis) | job07q |
| 09 bookshelf | e11 | 10 (e12) | | | e12: three of three pass, retouched (the sideboard in the reworked veneer at grain 0.6, a middle door's range 16.9; a strip linked to the woofers at 1.9, the cones 23.3; the roof's sheen 0.87, the slope 4.46 dE) | job09j |
| 04b back | e15 | 13 (e16) | | | e16: four of four pass, retouched (the sweep #7F7D79, the copy-side corner 100.0; a pool on the cove behind the product at 0.40, falloff -28.9; the back panel's top band mirrors its graded panel at 8.1, 230.0; the retouch's match 0.87, the shaded side plinth G 23) | job04b16 |
| 01 hero pair | e13 | 10 | 5.0 | 6.3 | c1 the retouch's neutral 1 to 0.4 (the whites taken to exact grey, none of the low sun's colour the wall and floor carry: "pasted in"); c2 the planks apart, 0.2 to 0.5 (a smooth brown slab, range 3.4); c3 and c4 both wordmarks' glints off (39 % of the letters clipped, a blue-white block over the middle letters); c5 the white balance's tint 10 to 5 (a yellow-greige wall renders mauve); c6 the veneer's grain 0.6 to 0.35 (1-2 px inked chevrons, 8-9 levels deep); c7 the letters' card linked to the letters (the plinth mirrors it as a cool band; the precheck's "too little" reads a removal, as meant). Out of scope: the trim rings' navy (they mirror the front gradient card) | job01l |
| 04a back, label detail | e15 | 10 | 5.0 | 6.5 | c1 the letters' ramp 1.45 to 1.1 (their faces cross the panel's value: 217 at the top over a 213 panel, 184 at the baseline; the precheck: 93 %); c2 the key pulled back 1.3 to 2.5 m (its own fall across the flat back is 3:1, the upper-left at the knee and the lower two-thirds grey); c3 exposure -0.1 to +0.1; c4 the paper #B9B4AC to #A7A39C (the white only 1.2 stops over it); c5 the port's linked lamp off (a crescent across the motor's dome). Out of scope: turning off-axis to show a side (the brief's straight-on view), pulling back to the plinth (the Facts' legibility), the letters' finish, a liner in the port | job04a14 |
| 08 the inside | e12 | 9 (e13) | | | e13: two of three pass, retouched, with the amplifier module's insides (a tray, the board, a finned bar, capacitors, inductors): the net on the far wall at 0.37, 140.4; the one over the floor at 0.28, 138.2. c3 (a ramp on the key's light on the set alone) was not in the engine: the empty lower-left floor stays 106.4 against 88 to 97 | job08m |
| 04b back | e16 | 14 | 5.0 | 6.3 | c1 the key in from 3.67 to 2.5 m (the back face falls only 13 levels from eave to amp plate) and c4 up 2.3 to 2.5 (the free white 201); c2 the contact's tight term 0.06 to 0.012 m and c5 its halo 0.24 to 0.1 m (a straight ramp from 68 to 106 over 28 px, a smudge out to 40 px); c3 the hip's kicker 2.6 to 0.25 (a clipped 1-2 px outline at 250-255); c6 the back's gloss band 8.1 to 6.5 (its core starting to clip). Out of scope: the soft pink bleed under the side gable (it mirrors the far sweep and the sky), the amplifier's connections (40 on a 77 plate; glint 0 skipped) | job04b17 |
| 09 bookshelf | e12 | 11 | 5.5 | 6.8 | c1 the front's sheen card 1.17 to 2.0, its ramp moved onto the band the lower fronts mirror (they fall 5-6 levels; the card added about 4; the precheck: 91 %, the right way); c2 the veneer's grain 0.6 to 0.4 (lines 6-10 levels deep on an even 15 px pitch: judged on the first rework, before the rings' spacing wandered); c3 the sun 0.5 to 0.25 (parallel shapeless light holding the fronts in the shoulder); c4 the fill 0.19 to 0.42 (the sides flat mid-grey); c5 the overhead strip 0.7 to 1.3 (weak contact pools); c6 the linked plinth lift 1.8 to 0.5 (the band glows at the full swatch under a white lit to two-thirds of it); c7 a stoneware vase with branches behind the turntable. Out of scope: the slate-blue trim rings (the owner's) | job09k |
| 02b late sun | e15 | 12 (e16) | | | e16: two of four pass, retouched (the front's sheen panel at 0.47 and linked, falloff 12.9; the sun at 2300 K, the patch 2.45 dE). c1 the turn to -40 left the sun side at 212.7 against 228 to 240; c4 the wainscot's new relief was tuned from 0.2 down, the wrong way: 0.2 shows nothing (3.0 against 5 to 11), and a proof afterwards found 0.6 gives 6.9 | job02b16 |
| 08b roof section | e8 | 6 (e9) | | | e9: four of five pass, retouched (the bowl's card where its core mirrors, at 1.5, p95 89.6; the polariser off, the bowl's range 15.5; the key at azimuth 20, the cut falling off 12.4; the pool in front of the back wall at 1.26, 65.2). c2 the backdrop #6D6A67 printed 60.2 against 40 to 58: the pool c5 added lifts it | job08b9 |
| 05 six flavours | e12 | 9 (e13) | | | e13: two of six pass, retouched (the flag off, the cove behind the roofs 92.2; the paper #707070, the far floor 85.2): the set now a dark charcoal the colours stand off. c2 the white fronts 169.0 against 203 to 216 at exposure -1.0, the tune's limit: the flag was not what took them from 203 (e11) to 168 (e12). The lamp shares were: e11 rendered before Cycles honoured a lamp's shares, when cone_card (irradiance 3.5, diffuse 0) and the other reflection-only lamps lit every face at full strength; c4 the plinth side 68.6 against 38 to 62 with the polariser off; c5 the contact core at 1.0 left the paper under Chocolate at 74.1 against 40 to 66; c6 the near floor 66.1 against 80 to 102 (the darker paper) | job05p |
| 10 both sizes | e9 | 9 (e10) | | | e10: six of seven pass, retouched, in the reworked veneer (the doors' figure at grain 0.36, range 7.4; the net over the top of the wall at 0.30, falloff -27.5; the frame shifted, the hero's front 215.0; the retouch's lightness 0.8, the red band 1.28 dE; the plinths split and kicked, the blue band 2.4 dE). c6 the planks at their limit (1.0) left the near floor's range at 6.6 against 8 to 16 | job10k |
| 08 the inside | e13 | 10 | 5.5 | 6.5 | c1 a net over the empty left floor (still the brightest floor, 109.4: round 9's c3 by a tool the card has); c2 a graded reflection card for the woofer's cone, linked to it (a black wedge with one glint streak; the precheck: 62 %); c3 the key's shadow on the set 0.16 to 0.5 (the carton casts none); c4 a small card in the amplifier box for the module's face (the new insides print at 3-11; the precheck: 55 %). Out of scope: the hairlines at the plinth line on both cut faces, the plies on the cut faces (resolved at 3x the frame's scale, a pixel each here), bare metal on the cut amplifier plate | job08n |
| 02b late sun | e16 | 13 | 6.0 | 7.0 | c1 the fill swung from azimuth -65 to 0, the window's side (it lit the front's far corner to 208.6, 4 levels under the sun-struck side's 212.7); c2 glint 1 kept off the dust cap (a hard pale blade); c3 the wainscot's relief 0.2 to 0.6, at the knob's calibration; c4 window 0 7 cm toward the front (the patch's lit edge 32 px off the carton); c5 glint 2 up for a soft dome on the cap. Out of scope: the cone's bronze (it mirrors the oak floor; the driver's finish), a thinner fin (the silhouette reads as a chimney; turning the ridge onto the sun, held back this round) | job02b17 |
| 07 exploded | e13 | 11 (e14) | | | e14: four of four pass, retouched (the dome down to 0.18, the front's strip 220.0; a lamp lighting the sweep alone at 1.0, the drivers' shadows on the floor, falloff -21.7; the bowl's sheen ramp onto its lower wall, 96.5; the side's low fill 0.6, falloff 33.0) | job07q |
| 03 waveguide close | e14 | 11 (e15) | | | e15: three of three pass, retouched (exposure +0.12, the white body 208.0; the dome's glint 14.1 W, p95 164.5; the left rim's panel 18.5, its lower run p95 152.6) | job03m |
| 05 six flavours | e13 | 10 | 5.0 | 7.5 | c1 exposure -1 to -0.35 (the whites 163-173, under Matcha's front and Chocolate's cream plinth); c2 the paper #707070 to #5A5A5A (it cancels the exposure on the set); c3 the side lift linked to the sides off (the white cartons barely model, sides 20-31 under fronts); c4 the sweep's contact reach 0.05 to 0.14 m (Chocolate floats on its plinth's bounce); c5 the retouch's lightness 0.9 to 0.5 (Matcha's front pistachio, dE 6.6); c6 the fill pulled back 5 to 12 m (Whole's front gets half Skim's fill); c7 a net over the foreground for the key; c8 a graded card for the three white fronts alone (`front-baffle#0` to `#2`, the engine's per-copy receivers; the precheck: 80 %, the right way). Out of scope: Oat's grainy dark side plinth (sampling), a darker cream on Chocolate (the flavour) | job05q |
| 08b roof section | e9 | 7 | 5.5 | 7.0 | c1 the backdrop #6D6A67 to #3E3C3A (the fin's red face 60.2 on a 65.9 ground: it separates by hue alone); c2 a narrow graded streak along the bowl's flare, linked to the insert (no highlight: p95 91, max 113); c3 the key 2.9 to 3.9 (the birch section a kraft tan, 150); c4 the pool lamp in close and left (a flat field behind the roof). Out of scope: a lighter retaining sleeve (2 % albedo), the magnets and pins seated in the section (they float 7 cm in front of it), the insert's cut face and the seal as sliced materials | job08b10 |
| 10 both sizes | e10 | 10 | 5.0 | 6.5 | c1 a window key from the left that the whole set sees (the room lit square-on from behind the camera: no direction, every shadow behind the speakers); c2 exposure 0.9 to 0.55 (the hero's front into the shoulder under c1); c3 the roof's sheen 0.19 to 1.0 (a clear coat returns under 0.01 of it: the gables flat; the precheck: 99 %); c4 the wall fill held for the wall between the speakers; c5 the veneer's grain 0.36 to 0.2; c6 the books as hardbacks with page blocks (asked as an asset; the engine now builds every books prop so). Out of scope: a wider frame for the empty top fifth | job10l |
| 01 hero pair | e13 | 10 (e14) | | | e14: seven of seven pass, retouched (the retouch keeping 40 % of the sun's cast, the sunlit side 1.01 dE from warm white; the planks 0.86, range 14.3; both wordmarks' glints off, p95 152 and 164, nothing clipped; the white balance's tint 5, the shaded wall 0.64 dE from warm neutral; the veneer at grain 0.25, its lines' edge 2.6; the letters' card linked, the plinth's blue 36.0) | job01l |
| 04a back, label detail | e15 | 10 (e16) | | | e16: two of five pass, retouched (the letters' ramp at 1.06, their faces 178.7 under the panel; the port's linked lamp off, the motor p95 1.3). c2 the key at 2.5 m left the white's falloff at 11.0 against 13 to 18 (the move more than halved the key's own fall); c3 the lower-right at 214.0 against 201 to 205 even at exposure +0.03; c4 the paper #A7A39C printed 138.3 against 126 to 134: the farther key's spill on the sweep is larger than the critic allowed | job04a14 |
| 07 exploded | e14 | 12 | 6.0 | 7.0 | c1 a soft set-wide fill from camera-left, 2 m out (the side-left, the largest face, at 182 against the front's 217: light grey, not white; nothing on the cabinet reaches white); c2 the bowl's sheen panel 0.43 m nearer and 1.5 x 1.5 m, its ramp 0.3 to 1 (a jagged dark Z where the bowl mirrors the sweep past the small panel's edges and its zero end: lum_p5 61; the precheck: 100 %); c3 the retouch's match 1 to 0.4 (the insert's shade red driven orange, 24 % of its red pixels at blue 0, dE 8.75 from the gable's shade). Out of scope: a camera down the pocket's axis (it would stack every part), thicker trim rings (the owner's), the tweeter on the pocket's line (it travels on its own screws' axis) | job07r |
| 03 waveguide close | e15 | 12 | 5.5 | 6.3 | c1 the left wall's sheen panel ramped across its band (z 0.97, 1.09, 1.21 m: 0.11, 1, 0.14) instead of along it (its two edges mirror as straight lines 30 px apart, steps of 18-20 levels per pixel: a flat chamfer cut into the horn); c2 its strength 4.64 to 2.9 (the band 136-139, rgb 219/108/111, washed pink and just under the rim line); c3 the fill's specular 0.1 to 0 (its only reflection, a sliver along the band's upper edge); c4 glint 5 off (its hard panel's footprint inside the band's roll-offs). Out of scope: the pull-loop tab under the mouth, a deeper floor to the mouth (the profile is simulated), the insert's joint line round the arch | job03n |
| 04a back, label detail | e16 | 11 | 5.0 | 6.5 | c1 the gradient dome 0.45 to 0.15 (the white back one value, 228 under the eave to 217 at the frame's foot: a fall of 11 on the key side and 4 across; a fit puts the key at 29 % of its light, the rest flat); c2 the key 2.4 to 3.2 W/m2 (the white back's level from the light that models it); c3 the fill 0.9 to 0.55 (it cancels the key's fall across the face: no shadow side); c4 the fin card's ramp onto 1.28 to 1.46 m, the heights the fin mirrors (a flat maroon, falloff 2.6; the precheck: 96 %, the right way); c5 the port's linked lamp 4.2 to 2.2 W (the black flare an evenly lit grey ring, its top lip 143). Out of scope: a turn of 6-10 degrees so a side shows (the brief fixes the Facts straight on), darker cast letters (the wordmark's finish) | job04a15 |
| 01 hero pair | e14 | 11 | 5.0 | 5.8 | c1 glint 6 mirrored across the centre onto the right woofer (a black hole beside the left's grey metal cone: 22.9 against 45.3, 23 % crushed); c2 a small lamp from front-left linked to the right mid's cone and cap (its own trim ring shades half of it from the low sun: 12.6 against 34.5); c3 the roof card 3800 K (the slopes pink-lavender, dE 9.6, the fin on its swatch; the precheck: 95 %); c4 a reflection panel for the tweeter domes (black holes, p95 27.7; revised by the precheck: as given it met none of the domes' rays, which leave in two bands only, so it moved up to the ceiling band, 1.5 m out at 2.1 m: 8 %); c5 the letters' card 0.3 to 0.38 (grey paint with a red cast). Out of scope: larger letters (the marks' size is fixed) | job01m |
| 02a cover | e10 | 10 (e11) | | | e11: six of seven pass, retouched (the sun 4.0, the sunlit front 217.4; the lacquer ramp 6, the front's fall 12.7; window 0's head up, the patch off the eave at 214.8; glint 2 at 1.8 W, the disc gone, range 6.0; the gable sheen 1.9, the slope 6.78 dE from the swatch; fill_right 0.79, the floor pool 116.3). c1 the sky at 8 left the window side at 165.9 against 166 to 184 (its proof read 170.5) | job02a12 |
| 04b back | e16 | 14 (e17) | | | e17: three of six pass, retouched (the contact's tight term at 0.012 m, the line under the plinth 89.6; its halo at 0.127 m, 106.1; the back's gloss band 6.2, p95 243.0). c1 the key in to 2.5 m left the back's fall at 21.0 against 22 to 32; c3 the hip's kicker, down from 2.6, left the hip at p95 145.7 against 150 to 192 even at 0.7; c4 the key at 2.9 W/m2 brought the white to 210 but clipped the gloss band (254) and lit the halo (112), so the tune kept 2.5 (201.0 against 206 to 214) | job04b17 |
| 02a cover | e11 | 11 | 5.5 | 7.5 | c1 the sun 4 to 3.1 (the sunlit front on the shoulder: the clean strip p95 230.1, its top 30 px a flat 234-235; the wall's patch 227.9; round 10's 3.5 to 4.0 closed the front's gap to the patch, but the sky and the lacquer ramp hold that now); c2 a reflection card in front of the back wall where the shaded side's rays land, ramped up the side (one flat 142.6, darker than its own shadow on the plaster at 150.5; the precheck: 100 %); c3 the planks apart, 0.31 to 0.65 (range 5.1 across six planks); c4 the oak 0.62 to 0.45 rough (no sheen under the sunlit skirting, no red under the plinth); c5 the sky 8 to 9.5 (the window side 169.5). Out of scope: a warmer body (it is #FFFFFF by spec), a print-size render (the card fixes the frame) | job02a13 |
| 02b late sun | e16 | 13 (e17) | | | e17: five of five pass, retouched (the fill swung to the window's side, the sun-side corner 193.2; glint 1 kept off the dust cap, its edge 2.0; the wainscot's relief 0.66, the patch's panelling range 8.4; window 0 toward the front, the patch's edge off the carton at 85.9; glint 2 at 0.95 W, the cap's top p95 55.3) | job02b17 |
| 08 the inside | e13 | 10 (e14) | | | e14: two of four pass, retouched, with the section cut whole before the plinth band splits off (the dark slivers fanning across the back panel's and the front baffle's cut faces are gone): the net over the empty left floor at 0.31, 92.4; the key's shadow on the set at 0.7, 72.2. c2 the cone's card and c4 the amplifier box's card left 27.4 and 19.0 against 30 to 46 and 20 to 34: the tuner's secant overshot a curved response and stopped with the aim between its proofs (now fixed: it steps between them) | job08n |
| 04b back | e17 | 15 | 4.0 | 7.0 | Down a point on the blind look: c1 the floor net off (a hard pale crease in the copy space's sweep, 97 to 130 within 2 px, traced to the plane through the net's left edge and the key; range 35.6 against 2.0 either side); c2 the hip's kicker linked to the gable alone (its strip mirrored in the semi-gloss sweep as a pale column, 133.6 against 105 and 115); c3 the plinth band's own lamp off (one value top to floor, R 171 under a 193 white: a self-lit strip); c4 the key 2.5 to 2.9 (the free white 199: light grey against the set; round 14's proofs read 210 at 2.9); c5 the back's gloss band 6.2 to 5.2 so c4 does not clip it (the precheck: 88 %). Out of scope: a deeper shadow line under the gable, larger connectors | job04b18 |
| 09 bookshelf | e12 | 11 (e13) | | | e13: four of seven pass, retouched (the front's sheen card on the band the lower fronts mirror, at 3, their fall 16.0; the sun down to 0.017, the fronts 204.0; the fill at 0.42, the right sides 164.0; the plinths' lift at 0.9, 65.2). c2 the veneer's grain at 0.36 left a door's range at 11.9 against 12 to 14.5 (its proof read 13.1); c5 the top light at 1.3 left the sideboard's top falling 14.1 toward the bases against 20 to 30; c7 the vase of branches added left the region's range at 100.9 against 25 to 90 (the branches' dark stems against the wall) | job09k |
| 02b late sun | e17 | 14 | 6.0 | 7.0 | c1 exposure 2.35 to 2.65 (the white front putty grey, 182.5 between the drivers, under the card's lacquer band); c2 the wainscot's relief 0.66 to 0.45 (its streaks read as wood veneer in the patch, range 8.1); c3 the front's sheen card 0.47 to 0.8 (the band under the gable one value edge to edge; the precheck: 100 %, the right way). Out of scope: a lighter cone on the mid (it reads as a port: the drivers' finish is theirs). The seventh round at 6.0: the next is a reshoot | job02b18 |
| 08 the inside | e14 | 11 | 5.0 | 7.4 | c1 a black rod from the port to the frame's left edge, the darkest shape in the frame, in no part's mask: asked as an asset to remove; revised by the engine to round 10's net over the left floor off (2.7 m deep at 10 cm, it ran into the sweep's curve 1.12 m back: crop proofs had it gone with the net off and unchanged however the net was scoped; the engine now names a flag that meets the set); c2 the paper #6A6D71 to #555659 (a cool mid-grey a few levels under the open interior); c3 the key 3.6 to 2.4 (the birch caps in the shoulder, R 238, one value down the upper half); c4 the pool lamp lower and nearer the curve (the frame's brightest band its top edge); c5 and c6 the cone's and the amplifier's cards to 0.6 and 0.34 (round 10's proofs interpolated); c7 the plinth's own lamp off (the white above the band glowing at 225 over 172 by the woofer). Out of scope: the plies on every cut face (sub-pixel at this scale) | job08o |
| 05 six flavours | e13 | 10 (e14) | | | e14: four of eight pass, retouched (the side lift off, the white sides 161.0; the retouch's lightness 0.78, Matcha 2.96 dE; a flag over the foreground at full density, the near floor 49.8; a card for the white fronts at 4, their fall 35.0). c1 exposure -0.35 left the whites at 218.0 against 203 to 212; c2 the paper #5A5A5A left the wall at 109.9 against 82 to 98; c4 the contact's reach at 0.3 m left Chocolate's glow at 79.3 against 42 to 60; c6 the fill at 12 m left the whites' spread at -12.0 against -8 to 3 | job05q |
| 07 exploded | e14 | 12 (e15) | | | e15: two of three pass, retouched (a set-wide fill from camera-left at 0.27, the side-left 194.0; the bowl's panel nearer and larger at 0.52, its lower wall p5 85.9). c3 the retouch's match, tuned down to 0.08, left the insert's shade streak at blue 5.0 against 14 to 40: the blue is lost in the render, not the retouch | job07r |
| 08b roof section | e9 | 7 (e10) | | | e10: two of four pass, retouched, with the magnets and pins of the half cut away gone from in front of the section (the engine's cutaway now drops a skipped part's loose pieces inside the box): a streak along the bowl's flare at 9.0, its p95 155.9; the key at 5.0, the birch 165.2. c1 the backdrop #3E3C3A printed 13.6 against 36 to 48 (near black); c4 the pool lamp in close and left, even at 4 W/m2, left the backdrop's fall at -3.0 against 6 to 18 | job08b10 |
| 09 bookshelf | e13 | 12 | 5.0 | 6.5 | Not run: superseded by a reshoot of the same frame (the blind look 6.0, 5.5, 5.0 over the last three rounds while each passed its tests; this round's five refinements again: a lamp on the sideboard's top alone so the pair sits on it, the window strip's reflection onto the left carton's edge, the white balance's tint 6 to 3 for the mauve wall, the veneer's grain down to 0.2, the fin flag wider; its first look named the structural things, a catalogue cut-out lit without direction, the cartons barely off the wall, the top third blank wall) | (reshoot) |
| 03 waveguide close | e15 | 12 (e16) | | | e16: four of four pass, retouched (the left wall's sheen ramped across its band at 3.1, its long edges rolling off at 3.8 and its peak 118.2 under the rim line; the fill's sliver gone, 4.7; glint 5 off, 3.6). The next round is a reshoot (5.5, 5.5, 6, 5, 5.5, 5.5 over six rounds) | job03n |
| 05 six flavours | e14 | 11 | 6.0 | 7.4 | Up a point on the blind look. c1 the floor card linked to the fronts (every side plinth mirrored it as a pale wedge with a hard diagonal edge: clear glass, Oat's 81 where the sweep gives 9.7); c2 the dome 0.5 to 0.2 (white sides one value, grey gaps, the foreground nearly the open floor's); c3 the roof fill reflection-only (Chocolate's cream bowl within 32 levels, past the knee); c4 the paper 0.55 to 0.85 rough (Chocolate's plinth mirrored in it as a glow, +5.5); c5 a card evening the three whites (209 to 224 across the row; the precheck, after a fix to its sense of direction: 50 %, the right way). Out of scope: a contrasting insert on Chocolate, a satin clear on the plinths, less gloss on Oat's roof | job05r |
| 04a back, label detail | e16 | 11 (e17) | | | e17: four of five pass, retouched (the dome tuned down to 0.03, the key side's fall 19.0; the key at 3.2, the eave band 220.0; the fill at 0.55, the fall across the face 9.0; the port's lamp at 2.2 W, its lip 107.8). c4 the fin card's ramp on the fin's own heights left its fall at 5.3 against 6 to 14 | job04a15 |
| 08b roof section | e10 | 8 | 5.5 | 6.5 | c1 the pool lamp brought inside the set, 0.66 m in front of the curve and linked to the sweep (it hung behind the sweep's wall and lit nothing: 58 % of the frame one near-black field, 12.9); c2 the key swung from azimuth 20 to -30 across the cut plane (a frontal wash 12 degrees off the lens: the insert's section one value along its length); c3 a graded card for the fin's lacquer (a flat maroon slab mirroring the black sweep, dE 12.1; its ramp flipped by the precheck, which found it bottom-bright as given). The card's must-shows no longer list the magnets: they sit 56 to 82 mm off the centre plane behind the cut face, which this cut cannot show (the critic found them at zero pixels, round 7's at the half cut away floating); the exploded view shows them | job08b11 |
| 07 exploded | e15 | 13 | 5.5 | 6.2 | Not run: superseded by a reshoot of the same frame (5.5 to 6.0 over seven rounds; this round's three refinements, exposure +0.2, the gloss panel's ramp from 0, a smaller floor-shadow lamp, while its first look named the layout: loose and left-heavy, the gable piece stranded top right, the drivers seen 70 degrees off their axis and the bowl opening away) | (reshoot) |
| 09 bookshelf | e13 | 13 (reshoot) | 5.5 | 7.0 | The first reshoot: c1 and c2 the camera centred and raised, aimed at the pair's mid-height (the right speaker 10 % larger and 47 px lower; a third of the frame bare wall); c3 the daylight window from the front wall behind the camera to the left wall (frontal, shapeless light, a pink window in the left fin); c4 the key a window-sized source from the front-left, 3.4 m out (it was a 2 m strip 0.6 m in front: flat fronts in the shoulder, no shadow on the top); c5 the print smaller over the turntable; c6 the cones' frontal lamp off; c7 and c8 the front and band cards moved for the new camera (the precheck: 94 and 58 %); c9 more fill for the far speaker; c10 the wall deeper and cooler, #E7DDD0 to #C5C5B8 (the cartons 6-16 levels off it); c11 the twigs out; c12 the veneer quieter | job09l |
| 03 waveguide close | e16 | 13 (reshoot) | 6.0 | 7.0 | The second reshoot: c1 to c3 the camera onto the horn's axis (12 degrees right of the front, 16 above the horn) and aimed above the throat, on 103 mm (the white walls 15.7 % of the frame, the tweeter 35 degrees off its axis, the fin crowding the top); c4 the 4.2 m overhead panel reflection-only and ramped for the new camera (it was the frame's real key, so slope and floor read as one soft value; the precheck: 100 %, the right way); c5 the key swung to azimuth -60 at 1.3 m (its direction never showed: the horn's shaded wall brighter than its floor); c6 to c8 the dome 0.5 to 0.15, the fill 1.8 to 0.8, the backdrop's pool 1.3 to 0.7 (a flat mid-grey brighter than the red roof); c9 the fin's card moved for the new camera (100 %, the right way); c10 the wall's sheen card off (its hard edge would return); c11 the base flag off (it greyed the white band's left end); c12 the throat's snoot 26 to 8 W | job03o |
| 04a back, label detail | e17 | 12 | 5.0 | 6.5 | c1 the roof card's ramp narrowed to 0.31 to 0.37 m (the slope one linear wash in eight even steps: satin, not lacquer holding a softbox; the precheck: 100 %, the right way); c2 a card for the back's clear coat under the eave (the white mirrors an unlit floor or a dim dome: matte paper; 100 %); c3 the fin's card 0.9 to 1.8 (a flat maroon band, 5.3 levels down its face; 98 %, the right way); c4 the letters' ramp from 0.1 (grey plastic, 174 to 145 down the m; 97 %, the right way). Out of scope, as every round: a few degrees' turn so a side shows, and a pulled-back frame with the plinth and the floor (the brief fixes the label straight on; the owner's call) | job04a16 |
| 10 both sizes | e10 | 10 (e11) | | | e11: six of six pass, retouched (a window key from the left the whole set sees, at 0.36, the wall's fall 23.4; exposure 0.55, the hero's front 214.0; the roof sheen 0.55, the gables' fall 29.9; the wall fill 0.19, between the speakers 111.8; the veneer at 0.15, a door's range 5.9; the books with boards and page blocks, 157.6). The next round is a reshoot (6, 6, 5, 6, 5.5, 5 over six rounds) | job10l |
| 04b back | e17 | 15 (e18) | | | e18: three of five pass, retouched (the floor net off, the copy space's crease gone, range 2.9; the kicker on the gable alone, the floor's pale column gone, 109.0; the gloss band at 3.4, p95 246.0). c3 the plinth's own lamp off left the band's red at R 142 against 143 to 163; c4 the key at 3.1 left the free white at 216.0 against 205 to 214 | job04b18 |
| 01 hero pair | e14 | 11 (e15) | | | e15: five of five pass, retouched (glint 6 mirrored onto the right woofer at 0.9 W, its cone 40.2; a lamp on the right mid at 0.75, 29.8; the roof card 3800 K, the slopes' blue 64.0; the domes' catch panel in the ceiling band at 7.5, p95 93.8; the letters' card 0.36, 153.4). The next round is a reshoot (5.0 five rounds running) | job01m |
| 07 exploded | e15 | 14 (reshoot) | 5.5 | 7.0 | The third reshoot: c1 the carton turned 72 to 60 degrees so the driver baffle leads (a 101 px sliver beside a 199 px blank side, the drivers edge-on); c2 and c3 the camera from 2.6 m down to 1.84 m and re-aimed at the assembly's centre (a top-down table view, left-heavy); c4 a 1.4 x 1.8 m softbox high on the right just behind the baffle's plane (the key grazed the side panel from 0.67 m: no direction); c5 the fill to the camera's left, opposite (the light the frame ran on, square to the turned baffle); c6 the paper #9A9A9A to #C6C4C0 (a dull mid-grey, the drivers in murk); c7 its wash re-centred and widened (a dark top-right vignette); c8 to c12 the five lamps that each lit one part off (the insert's flank, the tweeter, the mid cone, the side's base, the plinths) | job07s |
| 04b back | e18 | 16 | 5.5 | 7.0 | Back up from 4.0 with the crease gone. c1 the key's elevation 51.3 to 40 degrees (it struck the roof 1.6 times as hard as the back, paling the red, pulling the retouch's accent gain to 0.86 and lighting the foreground floor as brightly as the wall); c2 its output 3.1 to 2.5 to hold the back's white; c3 the gloss panel's ramp narrowed to 1.735 to 1.755 m (a chalky pink wash over 97 % of the slope, no edge); c4 the polariser 0.9 to 0 (near Brewster's angle on the slope it took three-quarters of the coat's reflection: satin, not lacquer); c5 the side strip shortened (a pink haze over the side eave, 9 px against the back eave's 3); c6 the side lamp 0.14 to 0.4 (the shaded reds near maroon-black); c7 glint 0 to the socket's lower lip (skipped: it mirrored the socket) | job04b19 |
| 02a cover | e11 | 11 (e12) | | | e12: four of five pass, retouched (the sun 2.64, the sunlit front's p95 223.0 off the shoulder; a card for the shaded side at 4.5, 157.3; the planks apart at 1.1, range 15.1; the sky 10.5, the window side 177.0). c4 the oak at 0.38 rough left the floor under the sunlit skirting at 120.2 against 140 to 158 | job02a13 |
| 10 both sizes | e11 | 11 (reshoot) | 5.5 | 7.0 | The fourth reshoot: c1 the room's daylight window from the front wall behind the camera to the left wall (both cartons lit head-on, no cast shadow in view, the floorstander floating); c2 the right-wall window moved behind the camera as a small fill (it filled both shade sides to within 40-56 levels of their fronts and threw a second set of shadows); c3 the sun off (frontal, a streak across the gap floor, and under c1 a hard patch on the back wall); c4 exposure 0.55 to 1.0; c5 the set's flag 0 out (placed for the frontal light, a band on the wall under the side light; the engine now takes a set card out); c6 to c8 the wall fill and the lamps that lit only the roofs and only the plinths off (self-glow, a pasted strip); c9 the floorstander's side card 2 to 1 (its silhouette lost against the wall); c10 and c11 the bookshelf's front and side cards up (it stands 1.1 m further from the new window). Out of scope: more samples, less denoising (the card fixes them; the finals will be sharper) | job10m |
| 02b late sun | e17 | 14 (e18) | | | e18: two of three pass, retouched (the wainscot's relief 0.51, the patch's range 6.4; the front's card 1.2, the band under the gable's fall 8.6). c1 exposure 2.6 left the white between the drivers at 208.3 against 199 to 206. The next round is a reshoot (6.0 seven rounds running) | job02b18 |
| 09 bookshelf | e13 | 13 (e14) | | | e14, the first reshoot's frame: seven of twelve pass (the camera centred and raised, the pair equal, 208.3 and 87.9 on their parts; the back wall falling 26.7 from the new window's side; the cones' frontal lamp off, 24.1; the band's card 102.0; the fill 7.0; the veneer quiet, 6.2). c4 the key at 1.7 left the fronts at 236.0 against 198 to 214: its tune passed at 0.7 (211) but set that aside for the band's sheen at 84.8 against 85 (the tuner now lets a miss under a level pass); c7 the front's card did not move its test (4.0); c10 the wall 212.1 against 158 to 182 (the hot key); c5 and c11 the print and the vase's region still busier than asked. Not sent to the critic: a short job sets the key to 0.7 and re-tunes the band's card (09-e15) | job09l |
| 03 waveguide close | e16 | 13 (e17) | | | e17, the second reshoot's frame: nine of twelve pass (the camera on the horn's axis on 103 mm, the mouth's floor 102.4, the fin clear of the top, the roof filling the frame's width; the overhead panel a reflection, the slope falling 26.1; the dome down to 0.03, the horn's darkest 5 % at 44.0; the fill 0.8, the shaded wall 48.3; the fin's card 2.2, its fall 23.8; the wall's card off, 73.3; the base flag off, the white band 198.0). c5 the key at 4.6 left the white band at 185 against 196 to 222; c8 the backdrop's pool at 0.4 left it at 94.4 against 42 to 78; c12 the snoot at 8 W left the dome at 23.6 against 30 to 62 | job03o |
| 01 hero pair | e15 | 12 (reshoot) | 5.5 | 7.0 | The fifth reshoot: c1 a 3/4 view from the shade side at eave height (dead frontal from standing height: 14 px of side, one flat front, no gable end); c2 the lens 35 to 48 mm (the pair 40 % of the frame's height, dark floor and wall 60 %); c3 the frame shifted so the sunlit plaster becomes the copy space (the dead shaded right third); c4 the far speaker's fill lighting the set round it too (it lit only that front, to exactly the near one's level); c5 a soft fill from the camera's left that the set shares (the shade sides' only light a linked panel); c6 exposure down 0.15 (the fronts' top quarter over the knee); c7 the rug out (its corner would cut the frame); c8 the plinths' lamp off; c9 one glazing bar (a hard stripe in the copy space); c10 the sideboard a deeper walnut (a mauve-grey); c11 the right mid's lamp off (round 11's c2, superseded by c4 and c5) | job01n |
| 02a cover | e12 | 12 | 5.5 | 7.0 | c1 the right fill 0.79 to 0.2 (the floor outside the beam brighter than the sunlit foreground: no sun patch on the boards, the floor shadow filled); c2 the sky 10.5 to 6.5 (rounds 9 to 11 raised it until the sun existed only on the wall; the carton's wall shadow has nothing on the floor tying it to the plinth); c3 the sun 2.63 to 3.2, holding the front; c4 glint 2 from 0.5 to 0.15 m (a fifth of the front one flat 232: a burned patch); c5 the sun 4800 K (projector white, b* 4.9); c6 the side's card 4.5 to 7.5; c7 the wall wash falling off from the windows' side (the upper wall one value across 1120 px); c8 a glint on the bowl's upper-left rim (no edge where the roof turns into the scoop). Out of scope: more samples for the grain at full size (the finals), a contrasting insert | job02a14 |
| 07 exploded | e15 | 14 (e16) | | | e16, the third reshoot's frame: ten of twelve pass (the carton turned to 60, the baffle 188 on its strip; the camera at 1.84 m, the tweeter's band 48.1, the baffle's far edge 217.0; a softbox key high on the right at 2.46, the band between the holes 208.0; the fill opposite at 0.37, the side 162.0; the sweep's wash re-centred at 0.43, the top band 186.3; the five one-part lamps off: the insert's flank 85.9, the dome 80.9, the side's fall -2.0, the shaded plinth 53.5). c6 the paper #C6C4C0 printed 221.7 against 174 to 192 behind the parts; c10 the mid cone without its lamp 33.0 against 40 to 84 | job07s |
| 03 waveguide close | e17 | 14 | 5.0 | 7.0 | The reshoot's frame judged blind: 5.0 (e15 5.5, e16 6.0): "a clean CAD viewport", the backdrop one flat grey above the red, the white dull, the dome a dark ball. Its lighting finished before it is judged against the frames before it: c1 the paper #7C7E7D to #6A6C6B; c2 the backdrop's lamp raking the sweep from beyond the right edge; c3 the left rim's strip moved where the left lip's rays go (half the mouth traced; the precheck: 11 %); c4 a white card under the lens for the front (186: the key grazes it); c5 glint 1 where the dome mirrors the key (skipped: it mirrored the motor); c6 the side's card up and ramped lower (charcoal, 52; 96 %). Out of scope: the horn's three facets (its profile is simulated), a light point at the dome's apex (the driver's own) | job03p |
| 09 bookshelf | e13 | 13 (e15) | | | e15, the first reshoot finished: eight of twelve pass (the key at 0.7, the fronts 215.0 against 198 to 214 and their fall 13.0 now passing; the band's card 2.8, p95 100.2; the wall 184.5 against 158 to 182; the print and the vase's region still busier than asked). Sent to a fresh critic for its blind score | job09m |
| 07 exploded | e16 | 15 | 5.5 | 7.0 | The reshoot's frame judged blind: 5.5 (e15 5.5, e14 6.0, e13 6.0): the same band, a different image. c1 the backdrop's pool lamp 1.4 to 0.1 (a hot pool behind the drivers at 231.7, on the shoulder, brighter than the white body); c2 a floor-laid card linked to the side panel (the largest surface one flat 162, mirroring the floor); c3 glint 0 from 0.08 to 0.025 m (a 1316-px clipped disc on the roof by the pocket); c4 the gloss card 1.56 to 0.45 (the red roof and the insert's face salmon pink, dE 15.2 and 9.9); c5 the floor-shadow lamp 1 to 0.5 (the paper brighter than the baffle below the mid hole); c6 a contact shadow at the foot (none); c7 the plinth card's ramp from 0 (a hard diagonal edge on the shaded plinth). Out of scope: the insert's flank in red, the interior seen through the holes | job07t |
| 02b late sun | e18 | 15 (reshoot) | 6.0 | 7.5 | The sixth reshoot: c1 the camera round to the sun's side, 3.2 m out at eye 0.9 m (the face the sun strikes square-on a 37 px sliver beside a fill-lit front: both one value, the product apart from its own shadow); c2 and c9 the sun to azimuth 42 and elevation 11; c3 the product 0.25 m toward the camera (its silhouette clear of it on the wall, its shadow running 1.3 m across the floor); c4 the fill moved camera-left on the shade side (from the front it lit both faces alike); c5 the sun 0.98 to 1.45 W/m2 (the patch tan paint, the side no brighter than the front); c6 a flag keeping the moved fill off the wall (the silhouette's density); c7 and c8 47 mm and a new aim (the right third and the band above the rail dead near-black); c10 the front's card off (it faked the gradient); c11 the wainscot's relief 0.51 to 0.3 (veneer under the stronger sun); c12 the glints off (pinned to the old surface points) | job02b19 |
| 10 both sizes | e11 | 11 (e12) | | | e12, the fourth reshoot's frame: eight of eleven pass (the right window behind the camera, the floorstander's side 118.0; exposure 1.0, its front 209.0; the set's flag out, the wall's fall 14.9; the roofs' lamp off, the gables 87.8; the plinths' lamp off, the band's fall 6.9; the side card down, the silhouette's edge 27.6; the bookshelf's front 196.0 and side 137.0). c1 the left-wall window left the gap floor at 82.0 against 36 to 62 (the floorstander's shadow not reaching across it); c3 the wall at the frame's left edge 183.8 against 130 to 180; c6 the wall between the speakers 158.5 against 110 to 150 | job10m |
| 08 inside | e14 | 11 (e15) | | | e15: six of seven pass, with the black rod gone (round 10's net over the left floor turned off; it had run into the sweep's curve, and the engine now warns of any flag crossing the set). The paper's shadow p5 47.6 and median 63.2; the key 2.156, the red 216.0; the cone's card 0.647, the cone 38.2; the amplifier's card 0.38, its board 26.6; the plinth 174.0. c4 the sweep's fall 4.1 against -25 to -2 (the pool lower and nearer the curve, still brighter at the top than behind the speaker) | job08o |
| 01 hero pair | e15 | 12 (e16) | | | e16, the reshoot's frame: nine of eleven pass (the camera round to the left at eye 0.9 m and 48 mm, the pair larger and turned to show their sides, the sunlit plaster on the left for copy; the right fill on every receiver, the fronts 197.1; a new fill on the left at 0.312, the hero's shade side 116.8; exposure 0.608, the fronts' upper quarter 211.3; the rug off; the plinths' and the right mid's own lamps off; one glazing bar). c10 the sideboard #5A3C26 still blue-grey, b 71.0 against 18 to 52; c11 the right mid cone 18.8 against 20 to 48 without its lamp. Sent to a fresh critic for its blind score | job01n |
| 09 bookshelf | e15 | 14 | 5.0 | 6.3 | The reshoot's frame judged blind: 5.0 (e13 5.5, e11 6.0): "flat cards with weak edges", the wall piece "a placeholder box", the door veneer procedural. c1 the wall print off (a brown box round a blank card at the frame's centre, lum_range 101); c2 a cutter keeping the fill off the left speaker's inner side (180.9 on a 181.6 wall); c3 a net on the key before the left speaker (the pair 9 levels apart, the left front's top in the shoulder); c4 the fill 10000 to 5600 K (the cones navy, dE 4.4 and 5.4); c5 the front sheen's ramp over the whole mirrored height (the band by the woofer one value); c6 and c7 the plinth and front sheen cards at 5700 K (the letters icy, the rings blue-grey). The deck keeps e11 (6.0) | job09n |
| 10 both sizes | e12 | 12 | 5.0 | 6.5 | The fourth reshoot's frame judged blind: 5.0 (e11 5.5, e8 6.0): "the white bodies read light grey against a beige wall of nearly the same value", denoised surfaces. c1 a full-height net off the wall left of the hero (the wall 187, the front's step over it 24 to 42); c2 the tint 10 to 5.5 (the neutrals a* +2.4 to +3.4); c3 the roof sheen 0.546 to 0.33 (the slope coral, dE 10.9); c4 the veneer's figure 0.011 to 0.026 m (door 3's range 6.5); c5 the window key's specular 1 to 0.35 (the fin salmon, dE 13.6); c6 the bookshelf side's ramp [0, 1] to [0.3, 1] (its back edge lost on the wall). The deck keeps e10, finished | job10n |
| 05 six flavours | e14 | 11 (e15) | | | e15: five of five pass (the floor card's mirror on the fronts and drivers only, the plinths 10.7; the sky 0.5 to 0.2, the sweep 154.0; the roof fill's diffuse off, the roofs' range 52.8; the sweep's roughness 1.0, its fall -5.7; a panel evening the two whites' fronts at 3.5, their fall -2.0). Then finished in post (the finish's first shot): the white point calibrated from the frame's raw | job05r |
| 03 waveguide close | e17 | 14 (e18) | | | e18: one of six pass (the backdrop's pool at 1.5 still not falling, -1.3 against -28 to -14; the paper 65.0 against 46 to 62; the front's card 199.0 against 200 to 214; glint 1 at 8 W, 199.6 against 115 to 175; the side's card at 0.4, 131.0 against 85 to 125; the left rim at 12, 180.3, passing). The reshoot's composition (e17, blind 5.0) is set aside: 03 goes back to e16's settings (blind 6.0), finished in post as e19 | job03p |
| 08 inside | e15 | 12 | 5.5 | 7.0 | Judged blind: 5.5 (e14 5.0, e13 5.5): "a die-cut illustration", the section lit flat and square-on, a horizon on the sweep. c1 the sweep's curve 1.4 to 2.6 m (the paper falls 17.9 then stops dead where floor meets curve); c2 the pool re-aimed onto the floor behind the cabinet (the band above the gable the brightest paper, the column beside it brighter at the top); c3 the inside lamp 8 to 30 degrees up (the chambers' far walls one tan field). Out of scope: the amplifier's PCB in its 2 cm slot (the module would have to come forward) and the plinth letters at 71 degrees | job08p |
| 03 waveguide close | e16 | (e19) | | | e19: e16's settings (blind 6.0, the best of the shot) restored after the reshoot's e17 and e18, finished in post (white 214.4 to 236, gain 1.10); the frame is e16's raw, re-posted. Sent to a fresh critic | finish |
| 02b late sun | e18 | 15 (e19) | | | e19, the sixth reshoot's frame: nine of twelve pass (the camera round to the sun's side at 3.2 m and 47 mm, the speaker 0.25 m nearer it; the sun at azimuth 42 and 11 up, 2.2 W/m2, the patch 229.3; the fill moved to the shade side; the glints off). c1 the floor's fall -11.9 against -65 to -25; c4 the front 215.8 against 166 to 192 (the fill too strong); c11 the wainscot's relief 3.1 against 4.5 to 7.0. Then finished in post | job02b19 |
| 01 hero pair | e16 | 13 | 6.0 | 7.0 | The reshoot's frame judged blind: 6.0 (e15 5.5; the shot's best with e10): "a warm, believable sunlit living room", but the pair lit by a soft frontal fill, not the sun. c1 the front gradient panel linked to the product's fronts (the sideboard's satin doors mirror it, mauve-grey, b 70); c2 the roof ramp 1.02 to 0.4 (the slope coral, dE 9.3); c3 the far speaker's own fill off (its shade side 148 above the hero's 117 and the wall's 89); c4 the letters' card 0.36 to 0.7 (flat grey print). The deck's close slide moves to e16, finished | job01o |
| 04a back straight on | e17 | 12 (e18) | | | e18: four of four pass (the label's fall 27.5; the back's sheen card at 2.0, the panel 227.0; the fin card at 2.07, its fall 11.8; the side's fall 52.2). Then finished in post | job04a16 |
| 08b tweeter cutaway | e10 | 8 (e11) | | | e11: one of three pass (the pool at 5.0, the backdrop 35.2; c2 the ramp's fall 7.0 against 8 to 20; c3 the fin sheen at 0.6, its fall 4.9 against 5 to 14: both a level short). Then finished in post (no white paint in frame: contrast, clarity and sharpening only) | job08b11 |
| 03 waveguide close | e19 | 15 | 5.5 | 7.0 | e16's settings, finished, judged blind: 5.5 (e16 unfinished 6.0): the slope "one even pinkish sheen", the white body "a hot, featureless slab that pulls the eye off the hero". c1 the top panel's ramp to 0 below the bowl's band (the slope's fall 16.1, the ridge band one value); c2 the finish's white_out 236 to 208 (the band under the mouth 237-242, flat in the shoulder: the critic takes most of the white point back on a shot where the white is not the hero); c3 a net on the key before the front face; c4 to c6 the rims and the dome's glint up | job03q |
| 05 six flavours | e15 | 12 | 6.0 | 7.4 | The finished frame judged blind: 6.0 (e14 unfinished 6.0): "a clean, instantly legible line-up" but the cartons hover and the fronts are flat cards. c1 the finish's white_in 211.6 to 228 (the white fronts' upper half packed into 243-249 by the shoulder: like 03's critic, it keeps a smaller lift); c2 the plinths' strip off (the bands brighter than their roofs, the roofs left off swatch); c3 the roof sheen 4.35 to 2.6 (Oat's roof taupe, dE 12.6); c4 a net on the fill in front of the row (every side one value); c5 a reflection card for Matcha's and Oat's fronts; c6 the letters' card 1.58 to 0.6 (clipped letters) | job05s |
| 04b back three-quarter | e18 | 16 (e19) | | | e19: four of seven pass (the key at 2.35, the face 211.0; the side at 0.6, its red 128.0; the shaded plinth 59.6). c1 the backdrop 72.2 against 74 to 84; c4 the floor 137.7 against 112 to 135; c7 the glint's p95 51.1 against 70 to 130 | job04b19 |
| 02b late sun | e19 | 16 | 5.5 | 7.0 | The finished reshoot frame judged blind: 5.5 (e18 6.0): "a strong, witty graphic idea with believable shadow geometry", but the hero "a flat CG cut-out", its front and sunlit side one value (224.8 and 226.3; the raw side's red at 254 on 69 %). c1 the carton turned -40 to -45 degrees (the front falls out of the sun); c2 the floor's roughness 0.35 to 0.5 (a hot salmon pool mirrored under the plinth); c3 the letters' kick panel moved to where they now mirror (64.9 on a 63.5 plinth); c4 the fill's cutter narrowed (the left fifth dead black behind a hard edge) | job02b20 |
| 04a back straight on | e18 | 13 | 5.5 | 7.0 | The finished frame judged blind: 5.5 (e13 5.5): "one bright sheet of paper with no lacquer in it". c1 the finish's white_out 236 to 218 (the band under the eave a flat 246: the third critic to take part of the white point back); c2 the letters' ramp narrowed to a horizon; c3 the key's shadow on the set halved (a taupe pocket lower right); c4 the port's own lamp off; c5 the fin card's ramp to 0 at its foot. Out of scope, and found true: the back panel's shading normals bent (the engine's import re-read the CAD's normals when it marked faces smooth, p95 3.1 degrees, up to 6.3; fixed the same hour). Duel: e18 6.0 against e13 6.5, e13 stays the best | job04a19 |
| 08b tweeter cutaway | e11 | (duel) | | | Duel: e11 6.5 against the deck's e9 4.5 (e9 shows three stray magnet pucks floating on the cut face; e11 is clean): e11 is the best | duel |
| 05 six flavours | e15 | (duel) | | | Duel: e15 7.0 against e14 6.0 (e14's plinth sides glassy, the cream waveguide lost): e15 is the best | duel |
| 02b late sun | e19 | (duel) | | | Duel: e19 5.5 against e16 6.5 (e19's letters a muddy smudge, the sunlit red clipped coral, a crushed black wall): e16 stays the best, by a point; round 16's job is cancelled and 02b returns to e16's settings | duel |
| 08b tweeter cutaway | e11 | 9 | 5.0 | 6.5 | The finished frame judged blind: 5.0 (e10 5.5; it won its duel 6.5 to 4.5): "a crisp, clean cutaway" whose birch and grey sections read as CAD fills and whose tweeter is a black mass. c1 a net under the key's lower half (the section filled evenly to the crop); c2 the inside lamp 0.6 to 0.15 (the box a flat brown field); c3 the fin sheen warmed to #FF8A78 (the fin chalky pink, dE 14.6); c4 asked for a masked dodge on the tweeter's black parts, which the card lacked: the finish now has one (finish.dodge), and this round uses it at 1 stop below 70; c5 the tint 10 to 4 (a plum cast in the blacks); c6 the bowl streak x1.6 | job08b12 |
| (all) | | | | | Stopped at the owner's word on 2026-10-10, 17:07. Queued and running rounds cancelled (01 r13, 02a r12, 03 r15, 04a r13, 05 r12, 07 r15, 08 r12, 08b r9, 09 r14, 10 r12, 02b's re-render from e16, the hi-res A/B); their round files stay in critic/rounds for a later run. The live shot files are the last rendered frames' settings, and 02b is on e16's (its duel winner) with the finish. The deck and canvas show critic/best.json's frames | stop |
