nathe-vink/earmilk/critic/DRAWINGS.md

# The drawing checker

A render critic asks whether an image would ship; this asks whether a builder could make the speaker from the drawings
without phoning anyone. It is run like a critic round: a fresh reviewer, the files below, one JSON reply, and every
finding names exactly what to change. `fab/sheets.py` draws the sheets from the CAD, so a fix is a change to the CAD,
to `fab/params.py` or to the sheet code, never a hand edit of a PNG.

## The brief

You are a cabinetmaker and a loudspeaker builder checking a drawing set before it goes to the shop. You will build one
pair from these files alone: a CNC router or a table saw for the birch ply, a resin printer for the gable and the
waveguide insert, hand tools, a soldering iron. Read every file below before writing anything.

For each size (`fab/out/` is the floorstander, `fab/out-bookshelf/` the bookshelf):

- `drawings/sheet-1.png` to `sheet-8.png` (A3 at 200 dpi; crop and zoom where the print is small; sheets 7 and 8 hold
  the notes the other sheets point to by number) and `drawings/earmilk-sheets.pdf`
- `cutlist.csv` (every panel: name, size, thickness, quantity, operations)
- `cad.json` (the CAD's own numbers: panel sizes, cut-outs, the waveguide, the driver rebates)
- `dxf/` (the router files, one per panel; list them, open one or two)
- `stl/` and `step/` (the printed parts and the solids; list them)

and once: `fab/README.md` (the build order and the decisions), `fab/bom.csv` (the bought parts),
`fab/params.py` (the numbers, marked SPEC, PROPOSAL or PLACEHOLDER), `fab/research/` (the bought parts' own data).

Look for what would stop the build, cost a remake, or force a guess:

- a dimension that is missing (a panel, a cut-out, a hole's position, a depth), or given twice with two values, or
  that disagrees with `cutlist.csv`, `cad.json` or `params.py`;
- a part, a cut-out or a fixing the drawings never show (where does each screw go, what holds the baffle, how the
  back comes off, where the cable runs, how the amplifier plate is held);
- an order of assembly that cannot be followed (a panel that cannot go in after another, a part glued in before
  something has to pass it, a cable that cannot be fed);
- a bought part drawn at a size its own data sheet contradicts (a driver's cut-out, its depth behind the baffle, the
  amplifier plate's cut-out, the connector);
- tolerances and fits a builder needs and does not have (a rebate's depth for a flush driver, a printed part's
  clearance in its pocket, a press fit);
- anything a builder cannot read: text under 2.5 mm at A3, a leader pointing at nothing, a section without its
  cutting plane on another view, a view without a scale, a title block that does not say what the sheet is;
- an acoustic number the drawings carry that the README's acoustics contradict (a box volume, a port's length).

Do not redesign the speaker: its shape, sizes, drivers and the waveguide are decided (the waveguide by simulation).
If something decided looks wrong, list it under `questions` for the owner with the reason.

## The reply

Reply with only this JSON:

    {
      "verdict": "one paragraph: could you build a pair from this set today, and what would stop you",
      "buildable_score": 0.0,
      "findings": [
        {"id": "d1", "size": "floorstander|bookshelf|both", "sheet": "sheet-2|cutlist|bom|README|...",
         "where": "the view and the place on it (a crop box in the PNG's pixels if it helps)",
         "severity": "blocks|remake|guess|legibility",
         "problem": "one sentence",
         "evidence": "what the sheet says against what the CAD, cut list, params or data sheet says, with the numbers",
         "fix": "exactly what to add or change, with the value: 'add a 6.0 mm dimension from the rebate floor to the face on the section A-A', not 'dimension the rebate'"}
      ],
      "questions": [{"question": "...", "why": "..."}]
    }

`buildable_score` is out of 10: 10 hands to a shop today, 5 builds with phone calls. Rank findings by severity, the
ones that block first. Be exact: "the woofer cut-out is 282 on sheet 2 and 283.5 in cad.json (woofer.cutout_d)" is a
finding; "check the dimensions" is not.

## Rounds

Each round's reply is in `critic/drawings/`. The fixes go into the CAD, `fab/params.py`, `fab/flats.py`,
`fab/sheets.py`, `fab/bom.csv` and `fab/README.md`, and the drawings are regenerated from them.

| date | round | buildable | findings | what changed |
|---|---|---|---|---|
| 2026-10-09 | 1 | 3.5 | 2 block, 3 remake, 19 guess, 6 legibility; 6 owner questions | d1 the tweeter went in from behind past a bore smaller than its flange: one ø73.4 bore from the boss's back to the throat, the flange seated on the throat's ring (the bookshelf's boss 68.4, flattened on the top panel, 1.5 of insert under the bore); d2 the front dowels moved behind the insert's pocket (9.7 and 6.7 clear); d3 the lid's gland drawn from its front edge, 43, with FRONT EDGE on the DXF; d4 the rebates 1.0 deeper for a flange gasket; d5 the upper magnets level with the throat, 12.6 and 3.0 clear of the boss; d6 the amplifier's box and the port in section A-A; d7 the bookshelf's stale brace files and notes gone; d8 the drivers' screw holes (DRIVER_SCREWS, measure first) on sheet 1 and the baffle's DXF; d9 the plate's rebate 4.5 for EPDM tape, its screws and pilot holes; d10 the tweeter's heat-set holes in the CAD and on sheet 3; d11 the fixings' positions and fits; d12 the trim rings exported, a channel over the screw heads, held by silicone; d13 the port 5 mm too long; d14 the gland M25 / M20 everywhere; d15 the floorstander's cabinet lead 250 past the grommet; d16 the runs through the brace's window; d17 the build order; d18 28 mm dowels; d19, d30 sizes printed exactly; d20 sheet 6, panel details; d21 the bookshelf's shelf +8.3 dB; d22 tolerances in every title block; d24 cad.json's features; d25 no text under 6 pt; d26 the roof's dimensions drawn over the sections; d27 the cutting planes A-A and B-B; d28 the balloons on faces the view sees, the gable with its pocket, not to scale |
| 2026-10-09 | 2 | 4.5 | 1 block, 2 remake, 16 guess, 7 legibility; 5 owner questions | d1 the floorstander's tweeter held by a printed retaining sleeve over its motor, its flange screwed to the boss's back face outside the bore (no screw through the tweeter: SB's screws thread into the motor from the front), the pocket's bore 4 mm deeper for the flange; d2 the bookshelf's faceplate screws M2.5 low heads (0.65 clear of a 48 body) into bonded knurled inserts; d3 the fit toleranced (pocket +0.2/0, insert 0/-0.15) and the insert painted on its face only; d4 the trim rings dimensioned, their inner ø from the surround (+2, measure); d5 the printed gable in six resin-sized pieces keyed by 4 mm pins, the insert's halves by 3 mm pins in the BOM; d6 the pocket, bay, channel and dowel holes dimensioned on sheet 3; d7 the plate's pilots through 13.5, its corners; d8 the gland's counterbore in the lid's DXF, cut list and sheet 6; d9 the pins bonded (6.1 holes); d10 no heat-set in resin, the screws named; d11 the port printed 10 long and its fitting and trimming in the build; d12 the finish before anything is fitted; d13 T-nut barrels and button-head heights, fitted before the glue-up; d14 the bookshelf's lead 185; d15 a pull groove under the insert; d16 round-sheathed cable, the channel sealed with silicone (no grommet in 18 mm); d17 each rebate as flange + gasket + ring, measure first; d18 the FA122's cut-out 293; d19 the BOM and params agree with the sheets; d21 sheet 6's scale; d22 'n of 6', drawing numbers, revision C, the first-angle symbol, the README's six sheets; d23 balloon 10 on the port's flange; d24 the bookshelf's dimension under the top panel; d25 its Facts note under the view; d26 the throat a closed circle. d20 (10 pt text) waits for a notes sheet |
| 2026-10-09 | 3 | 4.5 | 2 block, 7 remake, 12 guess, 3 legibility; 6 owner questions | d1 the bookshelf insert's outline grown round its boss (0.5 over it; the pocket follows, its height on sheet 3) and a check that the boss and fixings lie inside the outline; d2 the bookshelf's gable printed in four pieces, each inside 218 x 123 x 220, keyed by 4 mm pins; d3 the pocket's bore 2.5 deeper (to y 222.5) behind the sleeve's heads, and an axial check; d4 the bookshelf's boss to y 126 and its bore to 127, 4.0 of gable over it, and a check; d5 the sleeve's screws turned off the insert's split, one on the horizontal at the speaker's right; d6 a step 0 in the README: buy and measure first; d7 the D3004's flat front, its grille and its hole circle in sheet 7's 'measure first' table; d8 one M16 long-thread gland per cable, each nut in a 24 x 8 counterbore, fitted after the finish through the amplifier's cut-out; d9 the rings' channels inside their width (the floorstander woofer's open to the bore, a 1.0 lip), no crown, their sections at 2:1 on sheet 6; d10 the plate's screw holes one value everywhere (ø3.5 through the 13.5, from the plate in hand; 4.3 x 16 pan heads, 8 or 10); d11 the glue-up G1 to G7 on sheet 7 and in the README; d12 the mated connector in the bay and the 20 mm silicone plug in the channel below it; d13 the insert's halves on sheet 3: the split, two pins (the second at the top), the tilted print; the woofer ring's 320 bed in the BOM; d14 both of the SB17's flange values and the 6.5 rule; d15 the driver screws and T-nuts by limits (F1); d16 the BOM's gable line; d17 the fin dimensioned; d18 the window R30, the amplifier cut-out's corners R3; d19 the letters, the back wordmark and the stencils located; d20 the pocket's floor masked and the front's top edge sanded flush; d21 the ply rule (M1), named in the cut list; d22 every figure and note 10 pt (2.5 mm) or more, the long notes on two notes sheets (7 and 8); d23 the insert and pocket widths to 0.1; d24 detail C on section A-A, the insert's label off the hatch, the bookshelf parts 1 to 12, a VIEW T arrow. The owner's questions: the cabinet's lead now ends at a socket in the bay and the tweeter's own 150 mm of flex is the slack; the insert tough resin or MJF, one piece from a service (the halves a fallback); the bookshelf's outline rises about 3 mm at the top; the ribbon loop kept |
| 2026-10-09 | 4 | 6.0 | 1 block, 3 remake, 11 guess, 2 legibility; 6 owner questions | d1 the tweeter's own lead 310 mm (220 on the bookshelf) so it reaches the socket with the insert held clear of its pocket (a CAD check, 75 for a hand), its spare looped in the bay on section B-B; d2 the socket standing on the bay's floor, the cabinet lead's end 77 above the top panel's underside (40), fed down from the bay; the connector named (Molex Mini-Fit Jr. 39-01-2020 and 39-01-2021, terminals 39-00-0077 and 39-00-0041, pin 1 red +); the bookshelf's bay ø32; d3 each size's own letters, templates and stencils in its notes and the BOM, the bookshelf template's centreline 110; d4 the sleeve's length from the front ring's thickness (M4: 39.5 - t), the sleeve dimensioned in 3.2, the bookshelf's screw length from its faceplate (M3); d5 the front glued last so every inner panel, the top included, slides in from the front; a clamp at each step; marks for the shelf and divider; d6 the glands' lock nuts 20 AF or less, epoxied into their counterbores before the lid goes in; d7 the plate's corner radius in the measure-first table (R = r + 0.5); d8 the rebate rule per driver (the barrel + 0.5 of birch under it); d9 every harness pair spliced inside the amplifier's box, only round cable through the glands; d10 the mid chamber lined with felt (G5), the woofer chamber's fill, cable-tie mounts on the runs; d11 epoxy for a printed gable (F3); d12 ø3 pins in ø3.2 holes; d13 the bookshelf's ring bed and lead notes its own; d14 the bookshelf's pins 2.5 clear of the magnets (a CAD check); d15 one pocket width; d16 the bookshelf's ring sections off its panels on sheet 6; d17 the trim rings' inner edges from their bores on sheet 1. The owner's questions answered as proposals: the lead looped in the bay, the bay ø32, the bookshelf's letters 1.2 mm, the ribbon folded into its groove; open: the D3004's body over 49, the SB17's flange. Then a layout pass on all sixteen sheets: section B-B's labels in the order of their targets, each leader leaving its label's near end (none crosses another or runs through text), the spare's loop inside the bay, the bookshelf's section 4 mm right and its two longest labels wrapped clear of the front view; the lower magnets named under their circles (the bookshelf's pins sit between the rows); detail C's tweeter label over the left slope, clear of the bay's; the waveguide named in its air under the axis; the lid's FRONT EDGE note inside the panel; sheet 1's insert label in two lines |
| 2026-10-09 | 5 | 6.0 | 1 block, 1 remake, 13 guess, 1 legibility; 7 owner questions | d1 (the block) stands: no bought part is measured, and the set itself says to measure first; it waits on one set of drivers, a tweeter and an amplifier per size. d2 the gable's layers follow the measured ply (GABLE_LAYER = WALL; M1 says when a 12th is needed); d3 the top panel's FRONT EDGE in its DXF and G6; d4 M1 gives the birch under each rebate, and a CAD check holds it 0.5 over the T-nuts' barrels; d5 the sleeve 0.25 longer than its gap, so its screws press the gasket (M4, 3.2); d6 the divider planed 0.3 under the top panel and sealed to it with a PU bead (G4, G6); d7 the printed gable's drain holes only in its outer slopes or ends (README step 1); d8 the insert printed solid in MJF, or hollow in SLA with drain holes in its base (3.9 for both sizes; bom.csv re-quoted at 2.5 L); d9 the bookshelf's inserts 3.5 or less across (M3, bom.csv); d10 the plate's thickness sets the rebate's depth and the screws (M5); d11 the pocket's magnet and pin holes as deep as the insert's, measured from the wall, with their own tolerances (3.8); d12 a DATS V3 required for the port's tuning (2.5, step 8, bom.csv); d13 the inner panels ±0.2 at one fence setting (G1), proud edges planed (G7); d14 the floorstander's runs tied along the brace and the top panel (4.6); d15 a speaker's fixings listed on sheet 5, five sundries added to bom.csv, its step and channel corrected; d16 extension lines on the roof's depth dimensions (the insert's back dimensioned below its boss; the bookshelf's boss's back instead) |
| 2026-10-09 | 6 | 5.5 | 3 block, 4 remake, 8 guess, 3 legibility; 6 owner questions | d1 to d3 (the blocks, the bought parts unmeasured): a datasheet check (fab/research/datasheets-2026-10-09.json; the PDFs themselves blocked, their text read through search) found SB's drawing gives the SB17NRX2C35-8's flange as 6.5, the 10.9 being all that stands in front of the baffle (85.9 - 75), so the bookshelf's rebate stands (marked SPEC); shops give the D3004/602200's cut-out as 47.8 to 48 (the 48 body holds) and list it 45.3 deep, so a new CAD check holds the tweeter's body inside its bore (the bookshelf's takes 26 behind the faceplate); SB's TW29DN-B faceplate drawing carries an unlabelled ø70.0, probably the motor, over the 69 the sleeve allows (M4 and an owner question: a cup on the motor's back in a larger bore); Hypex's manual allows the FA253 horizontal, in its own compartment; the woofer's circle is Audiophonics' 295 (was an estimated 298), its T-nuts 12 across or less (a CAD check against the cut-out). d4 every pinned joint's holes 0.5 deeper than half the pin (ø3.2 x 8.5, ø4.2 x 10.5) and a dry fit before the epoxy (3.9, README step 1); d5 the lid's counterbores in their own file, amp-box-lid-underside.dxf, drawn turned over left to right, dashed on sheet 6 and in the cut list; d6 the sleeve's flange ø85, holes ø3.2 on ø78.8 (1.5 of flange outside each, the heads inside the rim); d7 the bookshelf's rear dowels at y 175.5, 8 of block over them normal to the slope (a CAD check); d8 the divider planed 18.3 below the sides' top edges, the felt 15 short of the corner, the top panel slid in dry and a PU fillet run along the corner from the open front (G4 to G6, bom); d9 ten cable-tie mounts a floorstander, each stuck on its panel before it goes in (positions in 4.6, black squares on sections A-A and E-E), the mid's run along the right side and the divider to its hole; d10 the printed gable in plan on sheet 3: its split planes, each joint's pins with their heights, the bonding and hollowing rules, and its 12 (8) pins in sheet 5's fixings; d11 the drivers' first hole angles on sheet 1; d12 the divider drawn and filed seen from the front, FRONT FACE, TOP EDGE in its DXF; d13 the bookshelf's ties on the lid and the box's front, the tweeter's 60 mm run untied, 4 mounts in the bom; d14 the fits 0.30 to 0.48 a side, the tolerances on the widths; d15 the cable by size and length in the bom; d16 sheet 6's lid moved clear of the title block and its note cut to what 4.7 does not say; d17 sections D-D (at the port) and E-E (over the brace) in plan on sheet 2, the runs projected on A-A said so; d18 centrelines through the plate and the port on sheet 4. The CAD's checks now judge a margin as printed (1.4999 is the 1.5 the sheets give). Questions to the owner: the Molex reach test (a printed test bay), the bookshelf tweeter's depth, the TW29DN-B's cup |
| 2026-10-09 | 7 | 5.0 | 4 block, 7 guess, 4 legibility; 11 owner questions | d1 the cable-tie mounts off the top panel: two on the window brace's top face, two on the right side, two on the divider (G1, G3, G4), and G6 says nothing goes on the top panel's underside; d2 the floorstander's tweeter held by a printed cap on the motor's back rim, not a sleeve round the motor: a ring ø73 / ø54 x 7.75 on a ø85 x 3 flange, three 3.0 x 12 thread-forming screws into the boss, 0.25 of preload on the gasket, so any motor up to the front ring's diameter fits (SB's faceplate drawing shows ø70.0 behind it); CAD checks for the ring's width, wall and length, and the tweeter's body inside its bore; named in section B-B and detail C; d3 the D3004's listed 45.3 depth set beside the 26 the bore holds, M3 says print nothing until it is measured, and the README asks the owner (lower the throat, or a shorter tweeter); d4 a release status in every title block (sheets 1, 3 and 4 HOLD until the named measurement, sheet 6 cut after M1, its trim rings on hold), HOLD notes in the front baffle's and back panel's DXFs and the cut list, stl/HOLD.txt naming which print waits on which measurement, and a Cut row on sheet 7 for what may be cut once M1 is entered; d5 the woofer's T-nut flange 12 or less everywhere (DIN 1624, ground down if needed) and a CAD check against the cut-out; d6 the port tuned last, in the sealed box with a scrap board for the back (README step 9, note 2.5); d7 M6 says the 24 mated length is drawn from no maker's drawing and names the two Molex drawings that give it, with the test bay printed first; d8 a woofer high-pass and limiter in both DSP plans (25 Hz, 4th order, for the floorstander's port; 35 Hz, 2nd order, sealed) and on the sheets; d9 M2's bookshelf wording measured-first, the SB17's 6.5 flange marked SPEC from SB's drawing; d10 the FA122's cut-out 96 x 291, Hypex's manual; d11 the tweeter's gasket a punched ring, ID 46 / OD 73, never inside the throat; d12 the 52 in D-D written out as a note (the runs rise from their glands 52 and 87 from the tube); d13 balloon 10 on the port's lower flange; d14 the cap labelled in both sections, detail C noting its cable is simplified; d15 the lid's operations text whole. After the drawing check: sheet 1's rebate notes clear their circles at 1:3 and 1:5, the screw-hole patterns in a Driver holes block beside the views; sheet 3's cap label inside the frame |
| 2026-10-09 | 8 | 4.5 | 1 block, 2 remake, 9 guess, 2 legibility; 5 owner questions | The verdict: the set complete and consistent, the HOLD marks (the bought parts unmeasured) all that stops it. d4 the floorstander's TW29DN-B drawn from SB's drawing instead of the placeholders it contradicted: one ø70.0 body 21.7 behind the 5.0 faceplate, so the bore is ø70.4 and centres it, the cap 18.05 long (its screws now 3.0 of wall, not 1.5), M4 telling the builder to lift the faceplate as SB says and what to do if the diaphragm's rim is not held without it; the tweeter's lead 320 (a CAD check failed at 310 with the unit shorter); d1 M3 a go or no-go for the D3004's depth (26 behind the faceplate's rear face, the bore y 99.5 to 126) and the owner's fallback; d3 M3 the D3004's tabs measured against the M2.5 heads, or the faceplate bonded; d2 note 3.5 the print service's tolerance: the base's width and the boss ordered as critical dimensions, or the sides sanded until it slides home; d5 a connector test bay printed first (stl/connector-test-bay.stl, both sizes, cut from the gable block round the bay and the channel); d6 note 3.7 R3 only in the pocket's profile corners, sharp where the back wall meets the walls, and route A's reach said; d7 G6 the top panel's felt 334 wide and 75 deep (no mounts on it); d8 the divider cut 1 short of the top panel (251) instead of planed in place, G6's PU fillet closing it; d9 the lid's second set-up named on the part, so the nested sheets carry it; d10 the BOM's cap; d11 sheet 6 says 1.5 of each woofer screw head shows inside the ring's ø290 bore (ø285 covers them; the owner); d12 every STL closed (a zero-area triangle where the fin's round meets its face dropped, a build check on every file); d13 the bookshelf's sheet 7 without the port, its amplifier upright; d14 the README's nine sheets, the DSP figures and the woods' masses. Also: a notes heading keeps its first note in its column; sheet 6 leaves the routers' shop notes to the DXFs |
