nathe-vink/earmilk/copy/hero.md

# Copy by surface

Everything on the canvas that is not the label, transcribed from the artboards. Voice: dairy deadpan. One joke per surface, maximum. Placeholders stay placeholders.

## Wordmark

earmilk. Lowercase, Archivo Black, tight tracking. Never a flavor word under it. Since the 2026-10-02 amendments it is cast metal letters standing on the plinth's front, no plate, and an engraving on the birch back panel above the Nutrition Facts. Nowhere else.

## Hero (Main artboard)

- Headline: **earmilk**
- Deck: A serious floorstanding speaker in a half-gallon carton.
- Body: Birch inside, printed board outside, so it can change when your room does. The treble fires from a bowl carved into the top. *Draft 2026-10-02, no sleeve: "Birch, finished in the flavor's colors, standing on its own plinth. The treble fires from a bowl carved into the top." On the canvas as a draft; not approved.*
- Button: Reserve a pair
- Price line: Pair, [PAIR PRICE]
- Dimension callout on the drawing: 1,055 mm
- Flavor selector: Whole · 2% · Skim · Matcha · Chocolate · Oat. Default Whole.

## Flavors

- Flavor is the colorway. Same speaker, six finishes: the gable, the plinth and the throat take the color, and Chocolate and Oat take the whole cabinet. *(draft 2026-10-02, no sleeve; the earlier line read "Same speaker, different carton: the print, the lid and the throat take the color, and Chocolate and Oat take the whole board.")*
- Whole: Red on white.
- 2%: Blue on white.
- Skim: Light blue on white.
- Matcha: British racing green on matcha. *(added 2026-10-08; the body matcha since 2026-10-09)*
- Chocolate: Brown board, cream print. *(draft 2026-10-02: Brown all over, cream plinth.)*
- Oat: Unbleached board, brown print. *(draft 2026-10-02: Unbleached all over, dark plinth.)*

## Finish (the Sleeves artboard, redrawn 2026-10-02; all of it is draft copy)

- The cabinet is birch: a body and a carved gable, finished in the flavor's colors. The gable takes the accent on the white flavors; the bottom 110 mm is a plinth in the accent, built in, so the stand and the band are the same thing.
- The wordmark is cast metal lettering on the plinth, standing proud, no plate. On the back it is engraved in the birch, above the Nutrition Facts.
- Retired with the sleeve: "The cabinet is birch: a body and a carved gable. The sleeve is two pieces of heavy printed board: a tube that slides up over the body, and a lid, die-cut at the mouth, that drops over the gable. Both lock at the back seam." / "Rooms change. Swap the sleeve in ten minutes and the speaker changes with them. Any flavor, shipped flat." / "Sleeves, [SLEEVE PRICE] a set".

## Section (the bowl)

- The tweeter faces forward from the throat of a bowl carved into the gable; the mouth is an ellipse on the slope. The bowl is the waveguide: it flares smoothly, so there are no edges to ring, and its lips set the pattern.
- As drawn, the lower lip holds the pattern to about 12° down and the upper lip to about 37° up, aimed at a seated listener. Set 170 mm back, the dome lands roughly where its sound lines up with the mid. A deeper bowl narrows the pattern; a wider mouth opens it.
- Caption: Side section at the centerline. Front is left.
- Callouts: tweeter set back 170 mm · mouth 118 mm · tweeter · 6.5 in mid · fin · carved birch gable · sleeve · lid *(2026-10-02: "sleeve" and "lid" become "finish")*

## Back

- Bare birch where the sleeve opens. Nutrition Facts engraved above the port, binding posts below. *(draft 2026-10-02: "An engraved bronze plate carries the Nutrition Facts. The wordmark is cast metal above it; the port and the posts sit on the finish below, and the plinth says SHAKE WELL.")*
- The sleeve's back panel is a frame; it locks around the window, so the wood is what ages. *(draft 2026-10-02: "The finish stops at the plate, so the bronze is what ages.")* *(withdrawn 2026-10-07 with the plate; draft: "The Nutrition Facts are printed under the clear, so they last as long as the paint.")*

## Pint crate (parked)

- Pint
- The same carton at desk size, six to a crate. Mix the flavors.
- The crate is the amp and the charger. Lift the pints out and set them anywhere in the room; they stay in sync.
- Price line: Crate of six, [CRATE PRICE]

## Label

See `copy/label.md`.

## Owner's panel (dropped 2026-10-02; kept for the record)

On the right side above the band. Placeholder copy from the exploration; the headline is the one proposed, the rows and the footer are not approved.

- Headline: HAVE YOU HEARD ME?
- Portrait: the owner's photo, printed as a halftone. The renders use a generated silhouette.
- Rows: Name · [YOUR NAME]; Heard since · [DATE]; Last heard · [YOUR ROOM]; If heard, call · [YOUR NUMBER]
- Footer: Printed to order. Any flavor, any face. / [YOUR LINE]

## Stand (merged into the plinth 2026-10-02; no price line)

## Marks (spec since 2026-10-02)

- OPEN OTHER SIDE, with the arrow, on the back slope of the gable. It points at the bowl. *(2026-10-07, the owner: on the fin's back face, the top fold, instead of the slope.)*
- SHAKE WELL, on the plinth's back face, reversed in the body colour.
