nathe-vink/earmilk/prompts/shot-02-v26.md

# Shot 02 · Two rooms, years apart · v26

v26: after round 2 of the owner's answers (a: 5, flat colour and knife edges, placeholder drivers, the shadow running into a wedge of sun on the back wall at the frame's edge, no skirting on the left wall; b: 5, blockout edges, the darks crushed with no cool fill, the wall shadow a squat barn that does not read as the carton). a: the sun up to about 31.5 degrees, so its light through the door lands on the boards before the back wall and the shadow ends inside the frame; both visible corners lit in reflection; a skirting on the left wall. b: the back wall nearer (0.55 m) and the sun lower (20 degrees), so the silhouette climbs the wall nearer the cabinet; the cool lamp, the window's fill and sky and the room's bounce up; both corners lit in reflection. Both: the clear polished, the cones' ribs fainter. The last round in this batch.
v25: after round 1 of the owner's answers (a: 6, no finish to read, placeholder drivers, a CG floor; b: 5, no sky light, the wall's shadow darker than the unlit wall, the side caramel, the wordmark brown on red). Both through Khronos PBR Neutral; figure in the boards; a small light seen only in the cast letters, just above the boards in front of the plinth, where the letters mirror the floor. b: the window's sky back up and the cool fill at a fraction of the sun, the lamp back at a third of v23's and cool, so the shade is lit and the side reads white in shade. In the model as shot 01.
v24: the owner's 2026-10-08 changes (as shot 01), after round 3 of the v21 look (a: the light went to the chair and its shadow on the wall while the speaker stood in even light; b: a softbox product in a sunset room). a: the sun higher and further round (26 degrees up, 50 off the axis), so the speaker stands in the beam and lays its whole shadow, the gable's peak in frame, across the boards to the right, the beam reaching the back wall only low at the right edge; the chair in the shade at the far left. b: the sun the one main light: the lamp off, the fill and the window's sky down, the exposure up. A new batch for the critic (round 1 again).
v23: after round 2 of the v21 look (a 5: the sun without punch, the wall's patch pale cream, the shade the same warm taupe as the sun, the cabinet's shaded side a step below its front; the cabinet a default primitive with no sheen; b 6: the speaker not lit by the wall's sun, its front a pale off-white beside the amber patch; the wall's carton wider than the speaker, which is the sun striking the wall 50 degrees off its normal). Both: the finish a flat colour coat under a full clear, so the gloss is the clear's and mirrors the window; an edge light on the near corner, seen only in reflections, so the 3 mm round draws a line. (a) The sun stronger and a warm white, the sky outside the door and the fill inside it blue, the fill down, so the patches go near white and the shade cool, and the side the camera sees falls to sky light. (b) The sun a deep late-day amber and the exposure down, so the white front takes the sun's colour as the wall does instead of rolling off to white; the lamp at the right down, so the side falls to bounce. The camera unchanged, one for both frames.
v22: after round 1 of the v21 look (a 5: the white front almost blown out, one even plane; the tweeter a black lens in a shadowed slot; the sun hard on the floor only, no patch on the walls; b 5: the silhouette inside the window bars' pattern, the cabinet three-quarters of the frame with no floor under it, the chair cut in half). One new camera for both frames, as the brief requires: wider (40 mm) and level with lens shift, the cabinet on the left third with floor under its plinth. (a) The sun lower (18 degrees) and further toward the front (40 off the axis), so its beam lays a patch on the back wall behind the chair and the chair's shadow climbs it; the exposure down. (b) The glazing bar moved, so its shadow falls clear of the cabinet's silhouette on the wall; the chair out of frame. The owner's changes the same day (OPEN OTHER SIDE on the fin, the back's letters centred) do not show from here.
v21: the owner's 2026-10-07 changes. The body's vertical corners and the gable's hips rounded 3 mm in the model (the fin's edges 1.5), so the corners take a highlight and the outline softens by that much; a 3 mm shadow line where the gable meets the body, like the plinth's; no lip at the scoop, the mouth the finish's own eased edge, and the tweeter's ring and seat black; the shader eases what is left by 1.5 mm (was 6). A new look, so the critic count starts again at round 1. Light and camera as v19.
v19: after round 2 of the v17 batch (a 5, b 4). Both: the camera more frontal (about 18 degrees off the axis, was 25), so the tweeter sits inside the scoop's opening. (a) The walls a light warm grey, so the shaded side separates from them. (b) The sun higher (18 degrees, was 10) and a touch warmer, the window wider and taller, so the whole cabinet stands in the beam and its shadow runs visibly from the plinth across the boards to the silhouette on the wall. The last round in this batch.
v18: after round 1 of the v17 batch (both 5: the speaker did not seem to stand in the room's sun). (a) A French door in a wall closer still, the sun higher (30 degrees, 45 off the axis), so the beam is wide and the cabinet's whole shadow, gable and all, lies on the sunlit boards beside it. (b) The back wall 0.8 m behind the cabinet, the window narrower and down to the floor with one glazing bar, so the cabinet's shadow climbs the wall inside the sun's patch beside the bar's; the chair in the shade at the left. Both: edges eased 6 mm; each driver's flange covers its hole's cut edge.
v17: the owner's 2026-10-06 changes, and refinement round 3's carries. A polished stainless lip rings the scoop's mouth (the owner). (a) The window wall closer and its opening narrower and taller, the sun higher (24 degrees) and further round (40 off the axis), so its beam is a band that lands on the cabinet while the floor around it stays in the room's light; exposure up a little, set off the white face. (b) The window three panes wide, so past the cabinet the beam lays its patch on the back wall behind the chair, a glazing bar's shadow across it: the key has a source in frame; the sun less amber, so the carton keeps its red and white. A new batch for the critic (round 1 again).
v16: after refinement round 2. The cabinet's corners eased at last: the path tracer joins each cabinet's finish into one object before rendering, because the shader's bevel only sees its own object and every panel was its own mesh. The shared camera a little more frontal (about 25 degrees off the axis), so the tweeter sits further into the bowl's opening. The old room: the window taller (sill 0.35), so the beam takes the whole front from gable to plinth and lays a crisp patch on the boards; env, bounce, the lamp, the window's sky and the exposure up, so the room, the chair and the wordmark read and the red stays red.
v15: after refinement round 1. In both rooms the window moves to the left wall, so a low sun crosses the baffle and the gable and the side the camera sees falls a stop into shade; the cabinet's own shadow runs back-right across the boards. The neutral fill, the bounce and the old room's lamp down, exposure down so the white sits below clipping. The camera lower (0.95 m) with the speaker left of the centre line; the chair at the right for balance. Eased edges 4 mm in the shader (silhouette unchanged). The dust caps are round domes (until now squashed across their axis: pills).
v14: render polish (owner, 2026-10-05): the tweeter's polished chamfer and textile dome, orange peel in the lacquer, paper cones, grain and plaster, dining chairs. Nothing on the product's geometry changed.
v13: in both rooms the window moves to the right wall, the camera's side, so the sun lights the faces the camera sees and the cabinet's own shadow falls back-left, attached to its base; the chair moves out of that shadow. The old room's window glows more against its lamp. Paper cones matte; plank grain stronger; the eased arris 2 mm. Path-traced round 2 asked for a shadow that belongs to the cabinet.
v12: both rooms are closed boxes (ceiling, right wall, a wall behind the camera), so in the path-traced pass the only daylight is the window's: sun patch, sky glow, the fill inside the opening; the old room keeps its lamp. Nothing on the product changed. Path-traced round 1 on v11 asked for a key the room agrees with and a cabinet with weight on the floor.
v11: the window's mullion removed in both rooms so no bar crosses the hero face (critic rounds 1 to 3). The brief is the rebriefed one: the same pair in two homes, years apart. No critic round: the cap for this look is reached.
v8: the plate is gone. The wordmark on the plinth is cast metal letters standing on the lacquer with no plate behind them, the way the lettering sits on a La Marzocco machine: 44 mm type size, 2.5 mm proud, polished faces, satin sides. Nothing else changed.
v7: after critic round 1 on v6 (shot 01's note that the badge read as grey type on a grey rectangle at room distance). The badge is now a chrome rim around a dark inset field with polished raised letters, the way a cast espresso-machine badge reads; nothing else changed.
v6: the 2026-10-02 direction. No sleeve, so no skin change: both rooms show the same Whole, finished white and red with the plinth and the badge, until the shot is rebriefed (its point was the swap). Camera and light as v5.
v5: after critic round 4. The old room's low sun raised so the fin's shadow lands on the slope and not across the front between the spout and the mid driver. Whole by day and Oat by night is the shot's point and stays.
v4: the locked look from the 2026-10-01 amendments: lids in the print colour on Whole, 2% and Skim, a printed 110 mm base band carrying the wordmark on the front and the right side, nothing printed under the gable. The stand and the owner's panel are optional and not in this shot.
v3: after critic round 2. Occlusion pass, fold and crimp lines, glossier board, shaded cones, a cool sky ambient in the old room so the shadows are not sepia, chair moved clear of the carton's edge, 2x supersampling. The Oat print is dark brown by spec.
v2: after critic round 1. Windows moved to the front-left so the sun lights the faces the camera sees; a chair in each room for scale (the room changes, the speaker does not); contact shadows; floor bounce; driver hardware and board materials rebuilt. The colour change between a and b is the point of the shot and stays.
v1: first brief, from the README shot list.

**Proves:** the sleeve argument. One object, one floor spot, two skins, years apart. It must read as the same speaker that changed its skin, not as two products.

## Frames
- **a.** **Whole** in a bright apartment: white walls, daylight, a new floor.
- **b.** **Oat** in a darker, older room: warmer and lower light, older floor and walls, the same floor spot.

## Scene
- One speaker, not the pair. Same position on the floor in both frames.
- The room changes around it; the speaker's position, size and camera do not.

## Camera
- Identical in both frames: same height, lens, framing and distance. Lock it before rendering either frame.
- Three-quarter view, the speaker fully in frame.

## Must show
- Pixel-matched silhouette between a and b. Overlaying the two frames should align the speaker exactly.
- The sleeve colour and the room are the only differences.

## Must not
- Anything in the list in `prompts/README.md`.
- Move the camera, the speaker, or change its size between frames.

## Text-to-image form
Constant block, then, for a: One of them in a bright apartment, white board with the red wordmark, daylight from a large window, white walls, a light wood floor, three-quarter view. For b: The same speaker in the same spot years later, now unbleached oat-coloured board with a dark brown wordmark, in an older room with warm low lamplight, a darker worn floor and aged walls, the camera unchanged.

## Acceptance
- A viewer sees one object that changed its skin, not two speakers.
- Overlay test passes.
