nathe-vink/earmilk/prompts/shot-04-v26.md

# Shot 04 · Back · v26

v26: after round 2 of the owner's answers (a: 5, tight round the graphics, the fin and the slope within 3 %, the slope still mirroring OPEN OTHER SIDE under the fin; b: 5, the back slope blown to near white, the port a black disc, cream pixels at the roof's corners). a: from 1.9 m and 3.3 m back on an 80 mm lens, level, so the slope's mirror direction clears the fin and takes the light above the set; about a tenth of the frame over the fin and under the port; the key raking harder, the far fill down. b: the slope's strip a third as wide and a quarter as bright under the polished clear; a small light on the port's far wall. Both: the clear polished, the core clear of the groove's corner. The last round in this batch.
v25: after round 1 of the owner's answers (a: 4, so close that no roof, peak or fin survived, the face lit flat, cream lines at the corners; b: 6, dingy whites over a near-black shadow, no sweep on the roof, the port a black sticker, the black post lost in its cup). a: back far enough that the gable's peak and the fin stand above the label, from 1.3 m, level, the lens shifted (from the panel's height the gloss slope mirrored OPEN OTHER SIDE), the key raking from the right. b: the whites up and the shadow lifted, one fill; a strip seen only in the lacquer across the back slope; the reflector into the port's tube. Both through Khronos PBR Neutral. In the model: the core inside the rounds, the tube a lighter moulding, the cup dark grey and the black post glossy.
v24: the owner's 2026-10-08 changes, after round 3 of the v21 look (a: the carton a fifth of the frame, the type hairlines at homepage size; b: razor edges, the port a flat disc, the terminal plate a flat rectangle on the band's line, the Facts values pale). The owner rebriefs frame a as a straight-on detail of the label: level at the panel's height, close, from the gable's edge to below the Facts. In the model: the edges 6 mm; the posts in a recessed terminal cup at 175, its flange 3 proud on four screws; the letters 1.5 proud; the Facts values bold; the port's tube a satin black. A new batch for the critic (round 1 again).
v23: after round 2 of the v21 look (a 5: the white an even light grey, razor corners, the roof mirroring the fin's OPEN OTHER SIDE as a blurred ghost; b 5: no edge or opening catching light, the port a black sticker, the white light grey in a narrow band of midtones). The finish a flat colour coat under a full clear, so the ghost (the colour coat's own broad gloss catching the fin) is gone and the clear mirrors lights as shapes; AgX's very high contrast look and the exposure up, so the white reads white and the set falls below it; an edge light on each visible vertical corner, and on b's near hip; the port's tube moulded a real black plastic's 3 % (was 1 %), so its wall shows going in. (a) The camera raised to 1.3 m, still straight on and level with the lens shifted, so the back slope reads as a slope: from the panel's height the new gloss mirrored the fin's mark on it, sharp and upside down.
v22: after round 1 of the v21 look (b 5: the light on the set, a pool and a horizon, the label facing away from the copy space, the verticals leaning in; a 5: no true white, a long shadow out of frame). Both frames on an even mid-grey set (a darker floor, the backdrop lit on its own), a broad soft key that makes the printed back the brightest thing in frame, level cameras with lens shift; (b) mirrored to the back-right, so the label faces the empty right half. The owner's changes the same day: OPEN OTHER SIDE on the fin; the back's letters centred between the body's top edge and the Facts. The shadow lines are real recesses.
v21: the owner's 2026-10-07 changes. The body's vertical corners and the gable's hips rounded 3 mm in the model (the fin's edges 1.5), so the corners take a highlight and the outline softens by that much; a 3 mm shadow line where the gable meets the body, like the plinth's; no lip at the scoop, the mouth the finish's own eased edge, and the tweeter's ring and seat black; the shader eases what is left by 1.5 mm (was 6). A new look, so the critic count starts again at round 1. The Nutrition Facts printed on the body, as v20. Light and camera as v20.
v20: the owner's 2026-10-07 change. No bronze plate: the Nutrition Facts are printed directly on the back's finish, like a carton's panel, in the same place and size (266 × 260, top at 770 mm), a warm near-black on the white, sealed under the clear so they cannot scratch off; the ink takes the finish's sheen. The cast letters above, the port and the posts below, unchanged. Both frames as v19 otherwise. A change to the printed look, so the critic count starts again at round 1.
v19: after round 2 of the v17 batch. Frame (a) unchanged (v17). Frame (b): the key a stop less, a larger softbox (1.2 m) and higher (50 degrees), so the back falls off top to bottom and the shadow falls short and behind; the fill from the camera's side up as a bounce for the side; the strips up for a rim; the reflector brighter, so the plate reads as metal. The last round in this batch.
v18: after round 1 of the v17 batch. Frame (a) unchanged (v17; the straight-on back is the brief). Frame (b): the studio sweep turned to face this camera, so its curve no longer reads as a horizon behind the carton; the key 35 degrees off the back face (was 50) and gridded, so the back takes more of it than the side and no pool of spill lies on the empty floor; edges eased 6 mm.
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
