nathe-vink/earmilk/prompts/shot-05-v26.md

# Shot 05 · Five flavors lineup · v26

v26: after round 2 of the owner's answers (5: the whites clipped and every plane one tone, no edge highlight; two hot spots at the ends of the horizon; the wall within five levels of the brown carton's roof; a rectangle round Oat's letters). No edge strips (their pools made the hot spots); a light seen only in reflections on each carton's near corner; the exposure down a tenth, the fill down, the backdrop's light up; the clear polished; the letters' planes cut down to their glyphs, so the denoiser draws no rectangle round them. The last round in this batch.
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
