nathe-vink/earmilk/renders/2026-10-01/shot-02-v2b.png

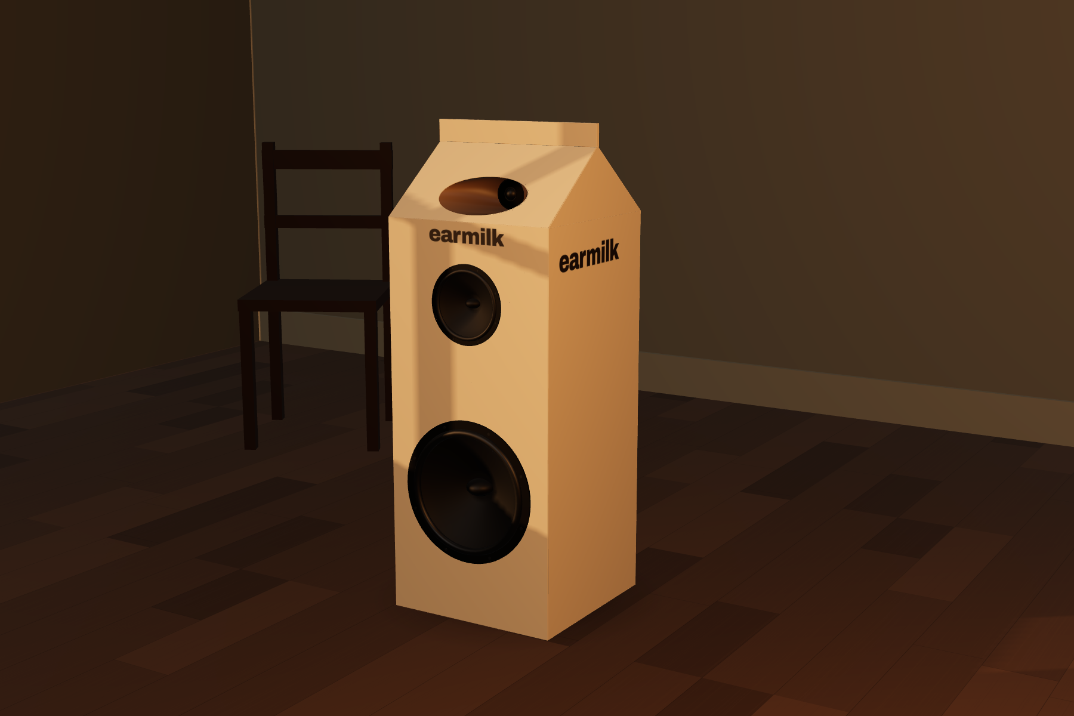
renders/2026-10-01/shot-02-v2b.png
