nathe-vink/earmilk/renders/2026-10-01/shot-02-v4a.png

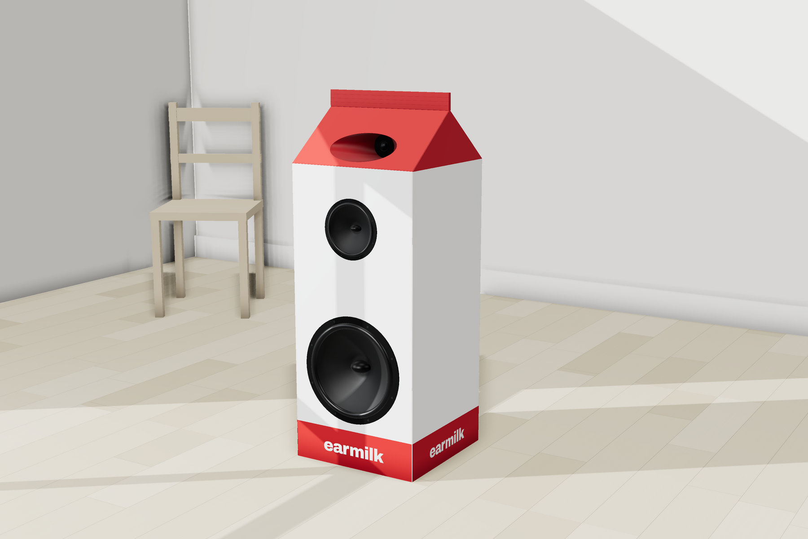
renders/2026-10-01/shot-02-v4a.png
