nathe-vink/earmilk/renders/2026-10-01/shot-03-v3.png

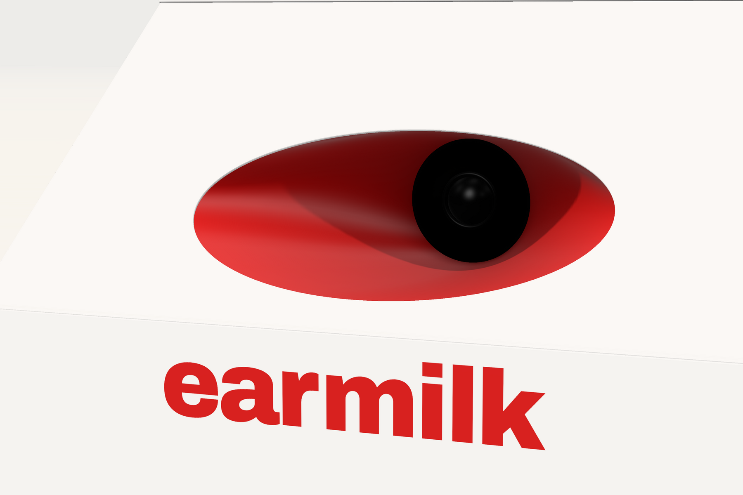
renders/2026-10-01/shot-03-v3.png
