nathe-vink/earmilk/renders/2026-10-01/shot-03-v5.png

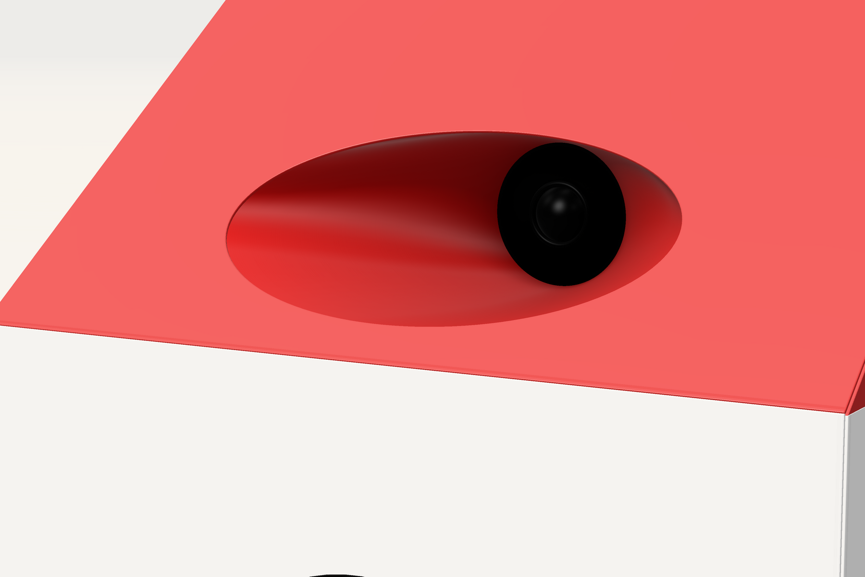
renders/2026-10-01/shot-03-v5.png
