nathe-vink/earmilk/renders/2026-10-01/shot-04-v1.png

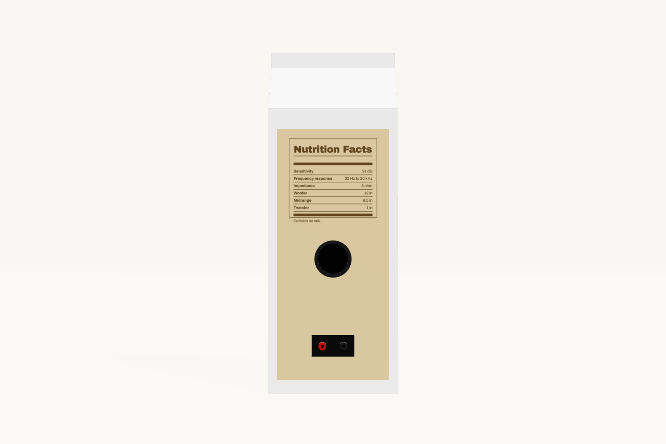
renders/2026-10-01/shot-04-v1.png
