nathe-vink/earmilk/renders/2026-10-01/shot-06-v2.png

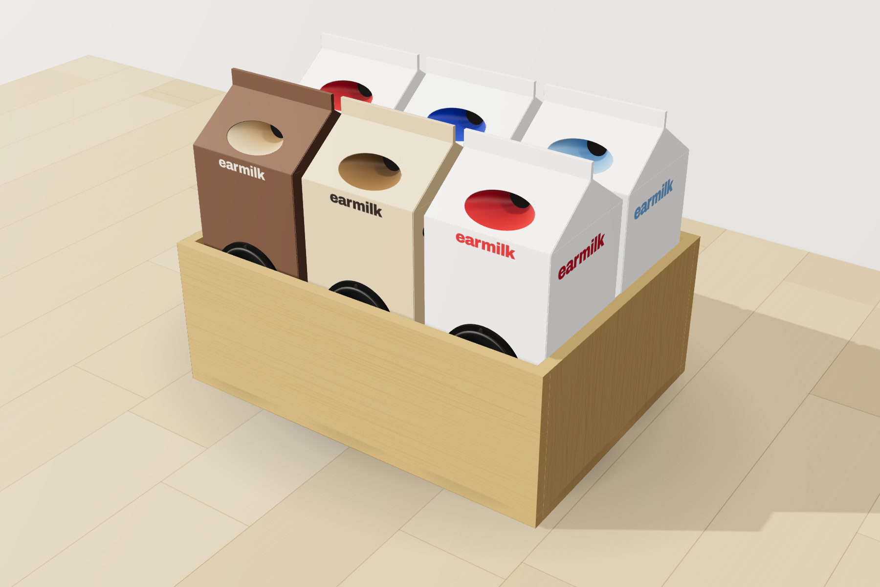
renders/2026-10-01/shot-06-v2.png
