nathe-vink/earmilk/renders/2026-10-01/shot-07-v3a.png

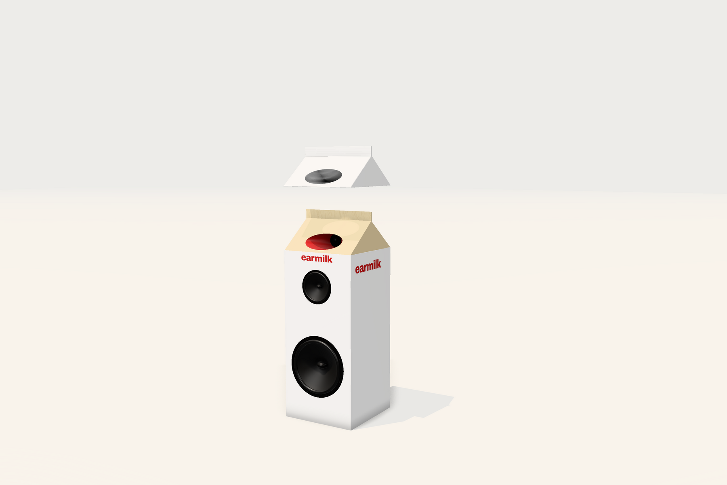
renders/2026-10-01/shot-07-v3a.png
