nathe-vink/earmilk/renders/2026-10-01/shot-07-v5b.png

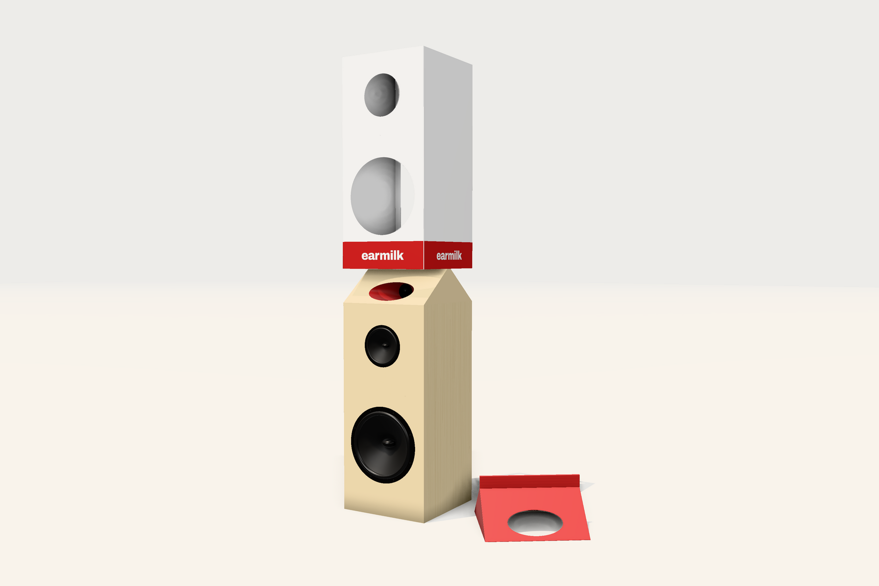
renders/2026-10-01/shot-07-v5b.png
