nathe-vink/earmilk/renders/2026-10-02/shot-03-v6.png

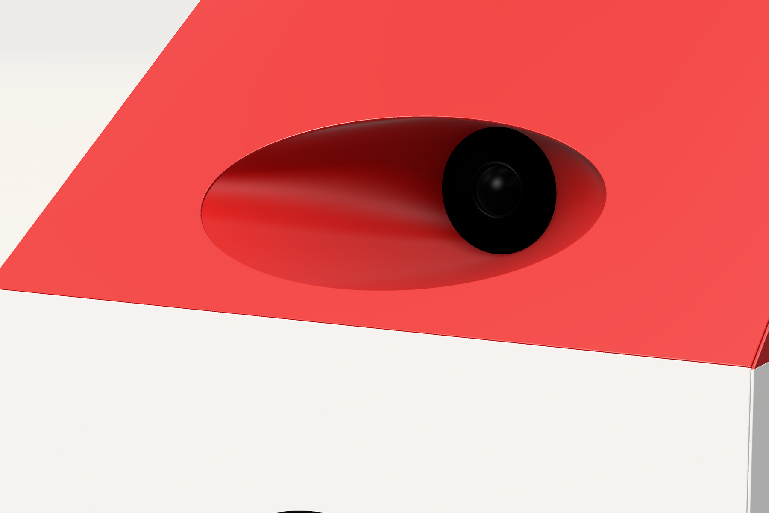
renders/2026-10-02/shot-03-v6.png
