nathe-vink/earmilk/renders/2026-10-02/shot-05-v11.png

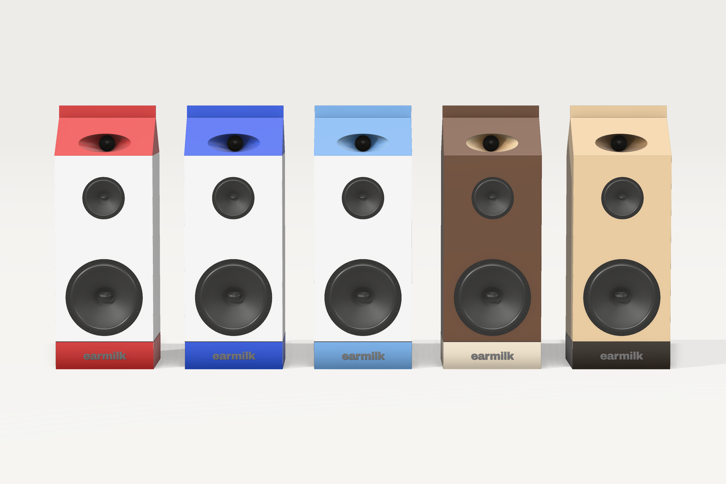
renders/2026-10-02/shot-05-v11.png
