nathe-vink/earmilk/renders/2026-10-03/shot-02-v12b-pt.png

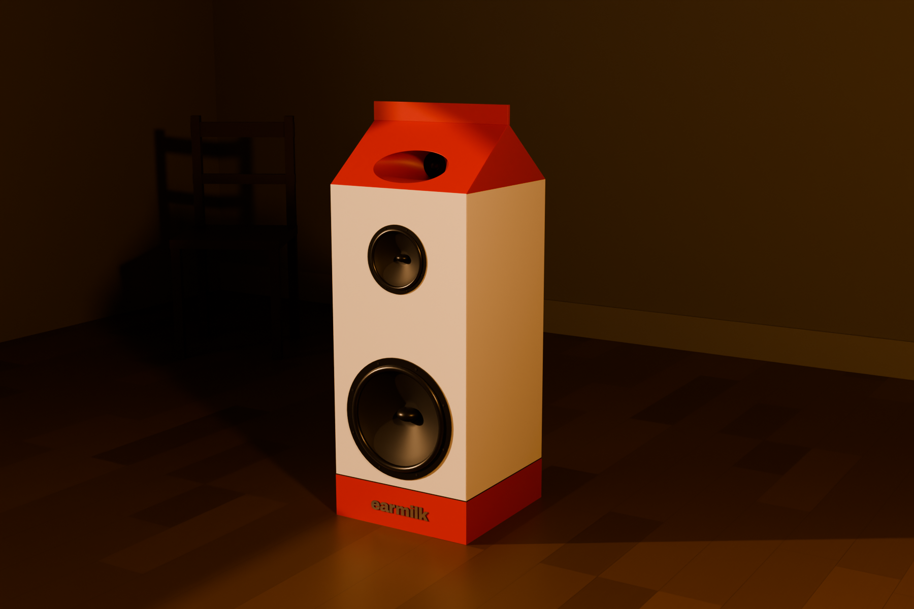
renders/2026-10-03/shot-02-v12b-pt.png
