nathe-vink/earmilk/renders/2026-10-03/shot-02-v12b.png

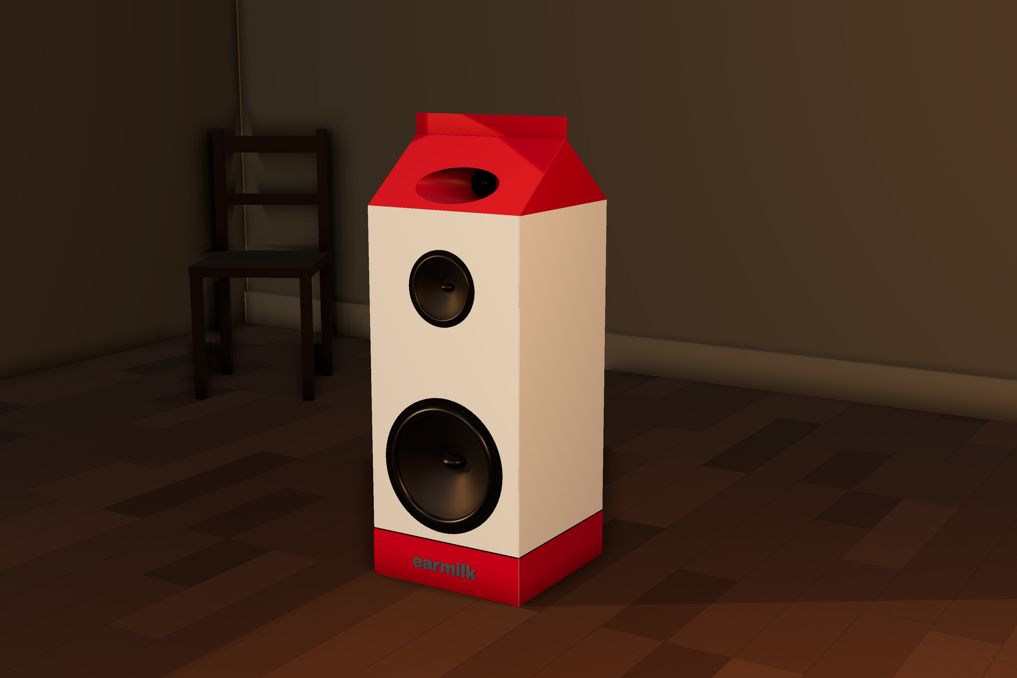
renders/2026-10-03/shot-02-v12b.png
