nathe-vink/earmilk/renders/2026-10-03/shot-03-v11-pt.png

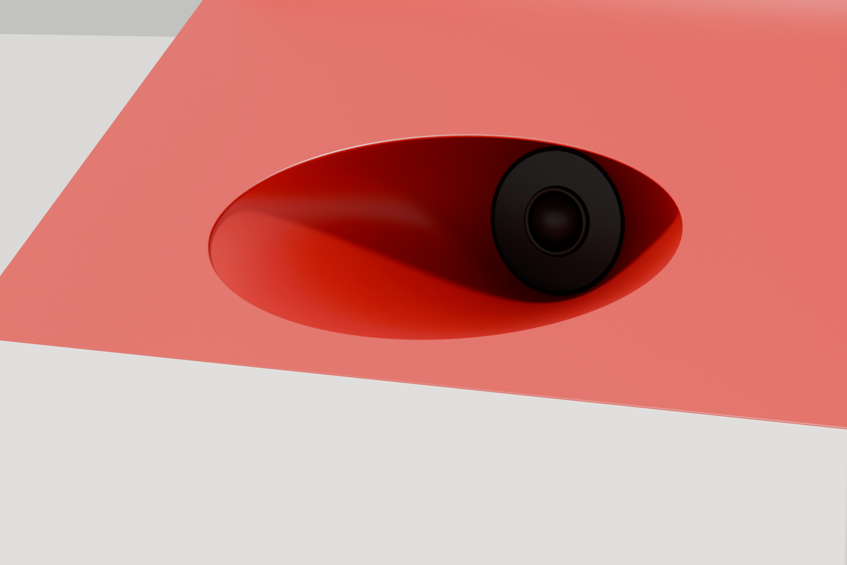
renders/2026-10-03/shot-03-v11-pt.png
