nathe-vink/earmilk/renders/2026-10-03/shot-03-v13-pt.png

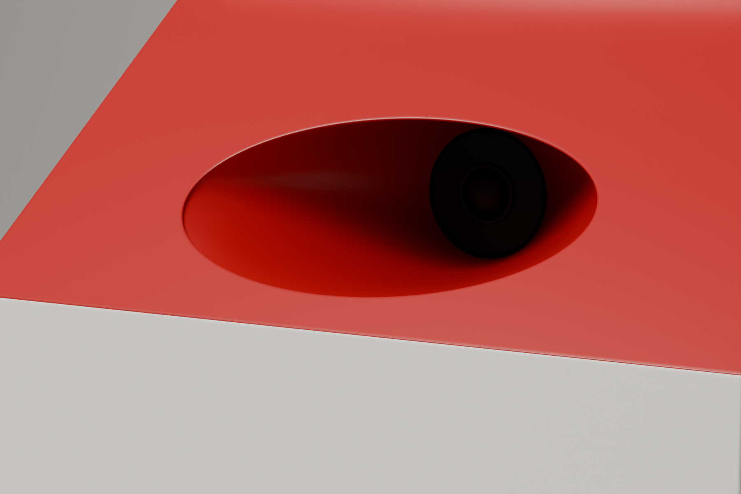
renders/2026-10-03/shot-03-v13-pt.png
