nathe-vink/earmilk/renders/2026-10-03/shot-04-v13.png

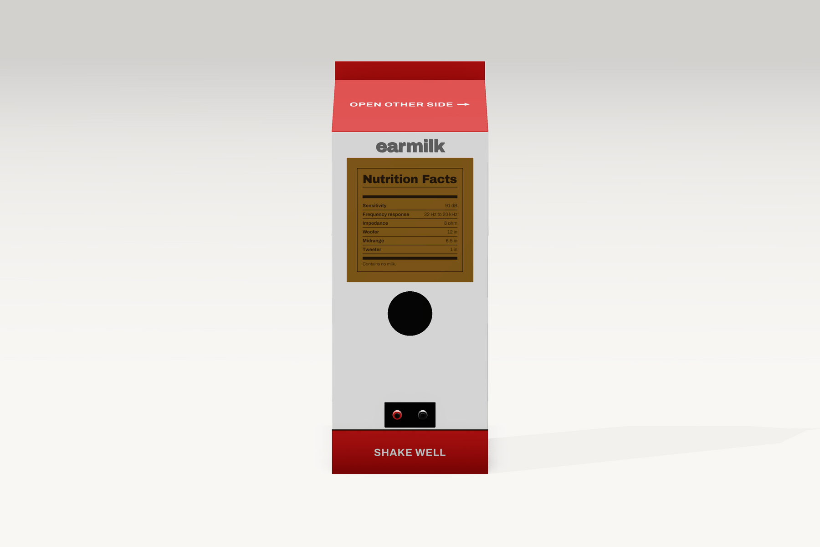
renders/2026-10-03/shot-04-v13.png
