nathe-vink/earmilk/renders/2026-10-03/shot-06-v12.png

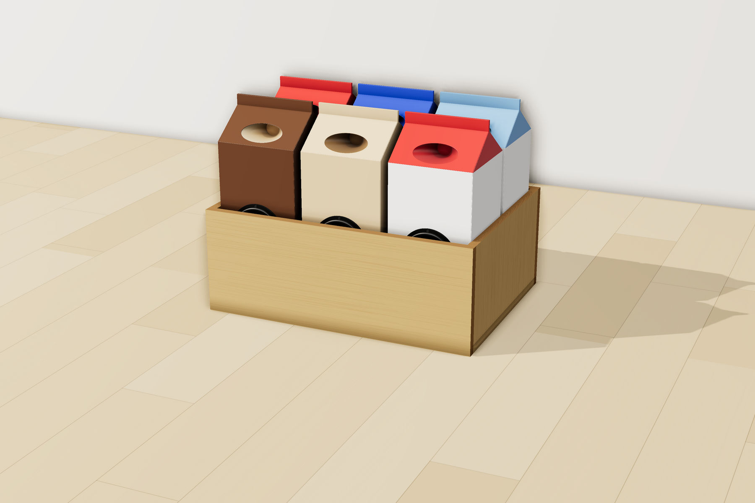
renders/2026-10-03/shot-06-v12.png
