nathe-vink/earmilk/renders/2026-10-05/shot-02-v16b-pt.png

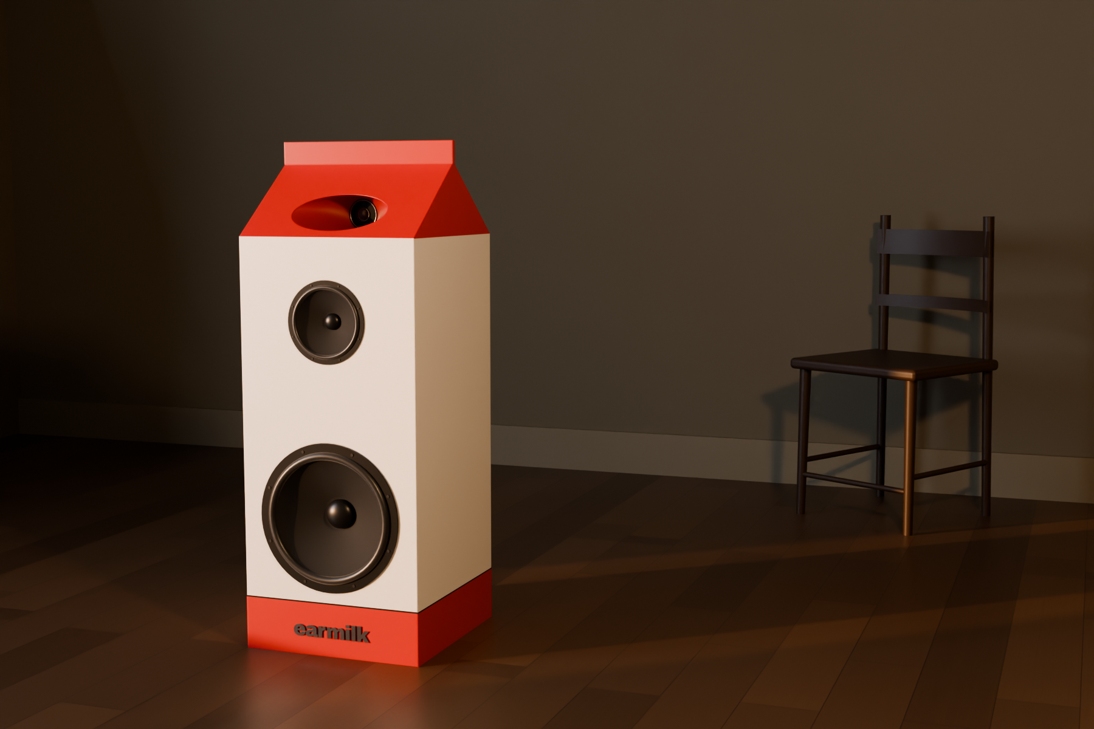
renders/2026-10-05/shot-02-v16b-pt.png
