nathe-vink/earmilk/renders/2026-10-05/shot-03-v15-pt.png

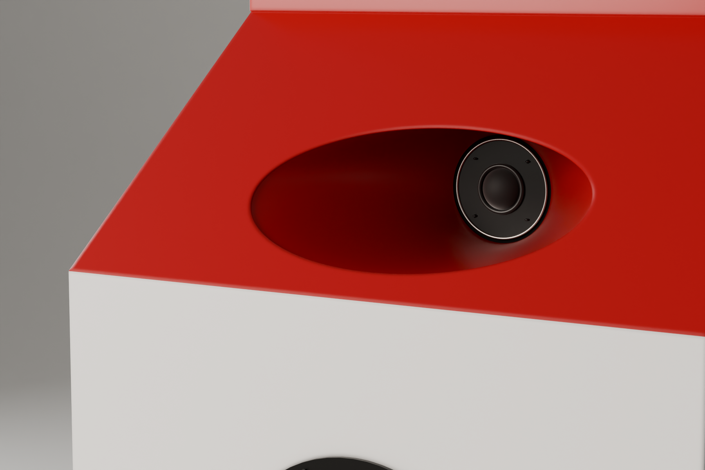
renders/2026-10-05/shot-03-v15-pt.png
