nathe-vink/earmilk/renders/2026-10-05/shot-04-v15-pt.png

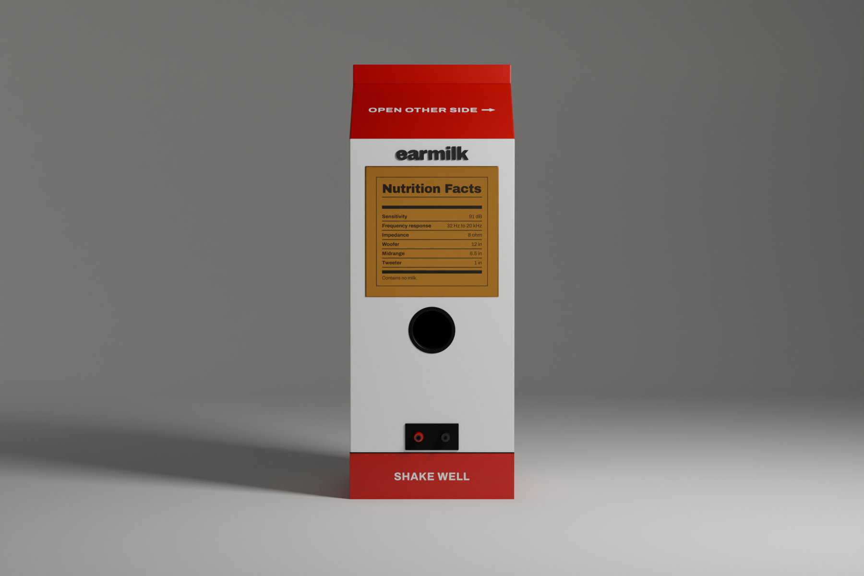
renders/2026-10-05/shot-04-v15-pt.png
