nathe-vink/earmilk/renders/2026-10-05/shot-05-v14-pt.png

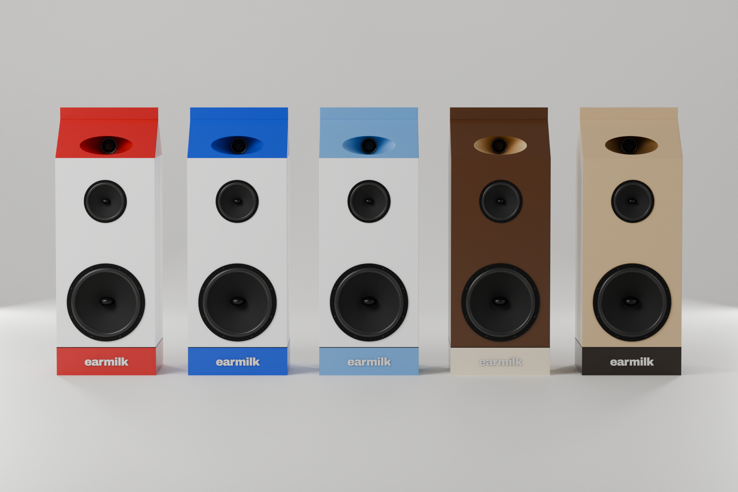
renders/2026-10-05/shot-05-v14-pt.png
