nathe-vink/earmilk/renders/2026-10-06/shot-01-v17-pt.png

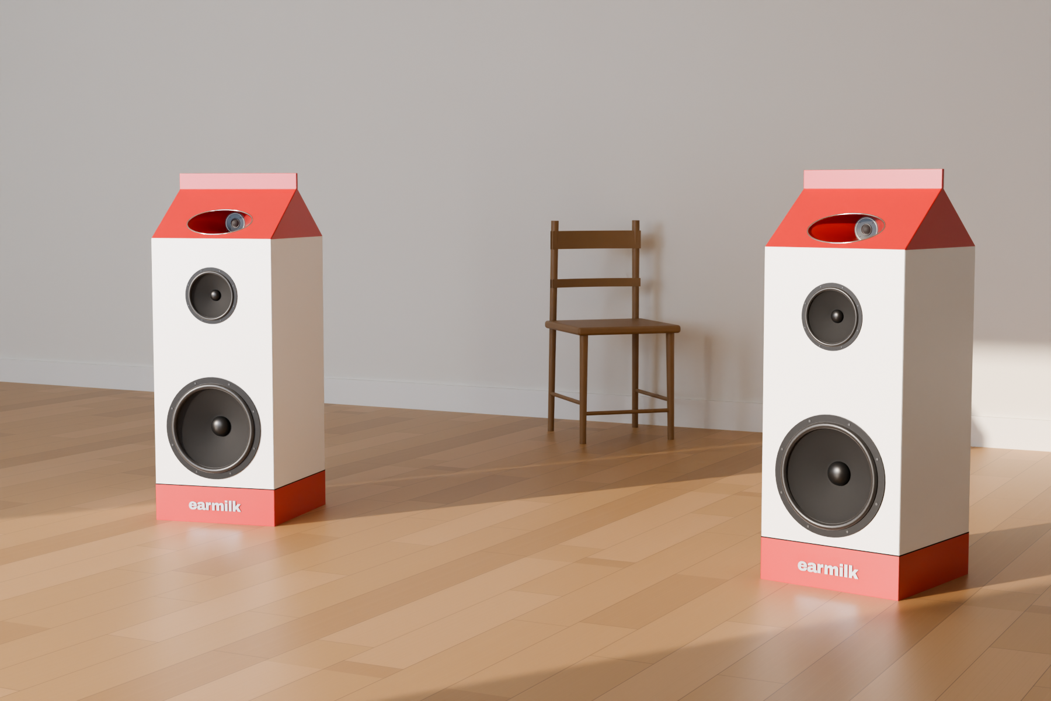
renders/2026-10-06/shot-01-v17-pt.png
