nathe-vink/earmilk/renders/2026-10-06/shot-01-v19-pt.png

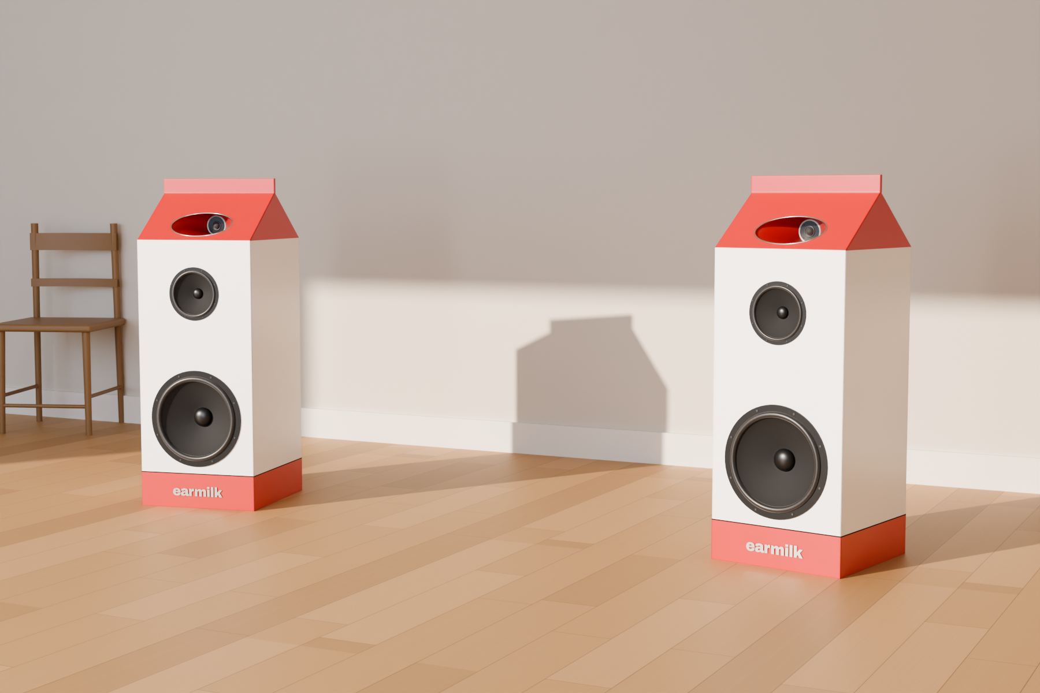
renders/2026-10-06/shot-01-v19-pt.png
