nathe-vink/earmilk/renders/2026-10-06/shot-02-v17a-pt.png

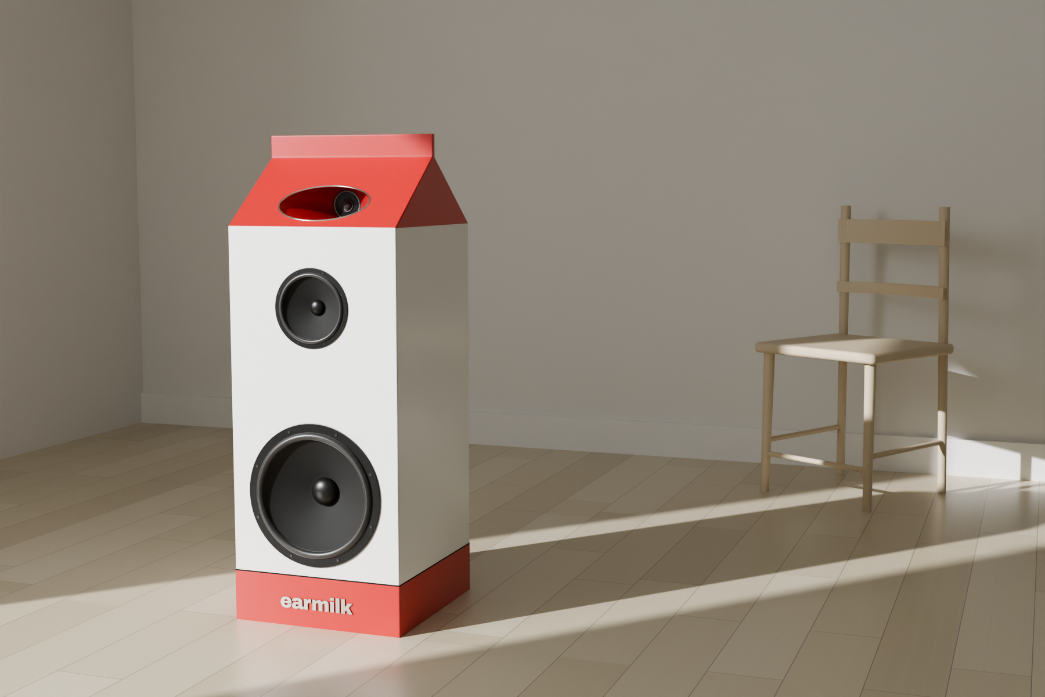
renders/2026-10-06/shot-02-v17a-pt.png
