nathe-vink/earmilk/renders/2026-10-06/shot-03-v17-pt.png

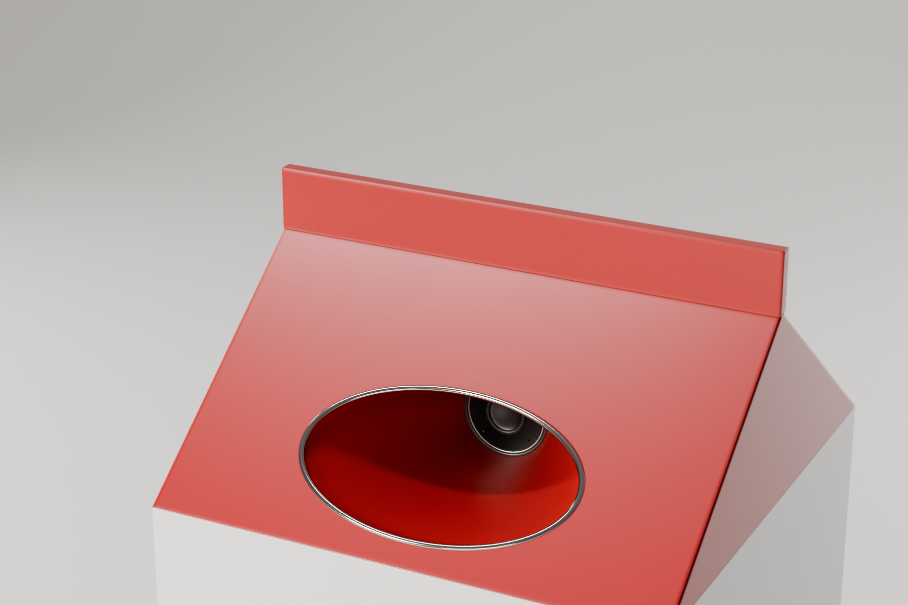
renders/2026-10-06/shot-03-v17-pt.png
