nathe-vink/earmilk/renders/2026-10-06/shot-04-v18b-pt.png

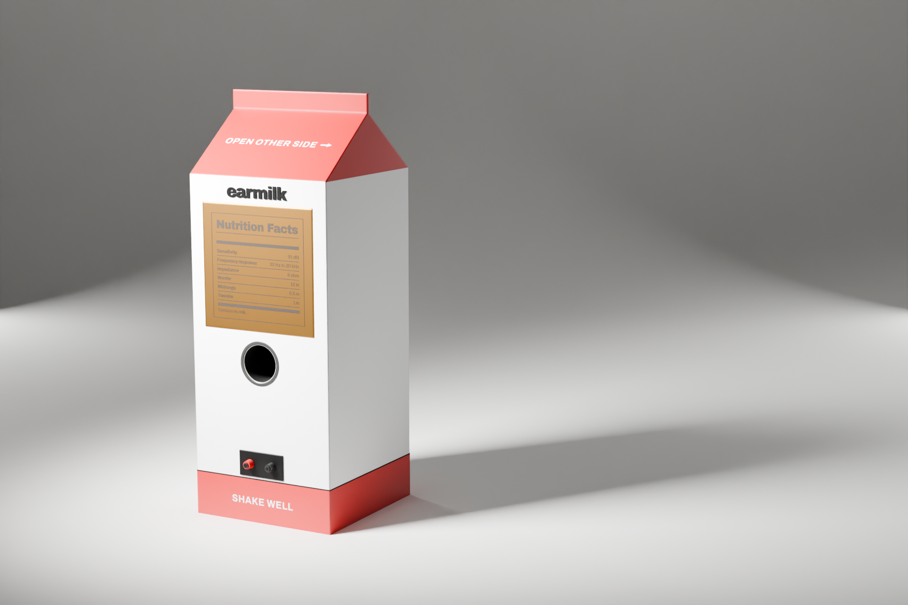
renders/2026-10-06/shot-04-v18b-pt.png
