nathe-vink/earmilk/renders/2026-10-06/shot-06-v18-pt.png

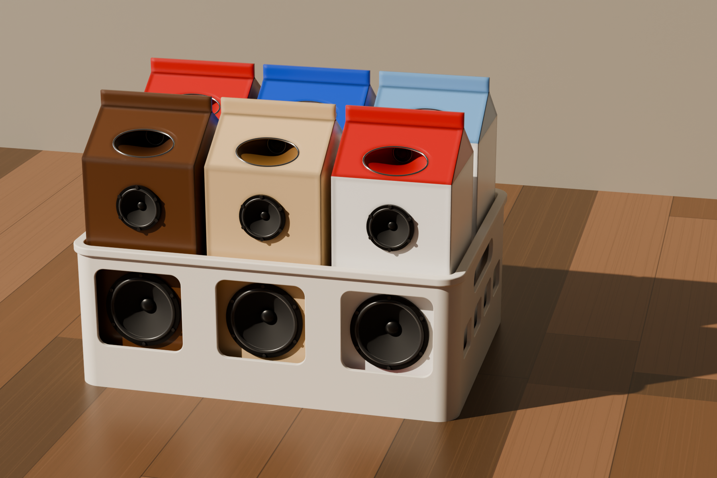
renders/2026-10-06/shot-06-v18-pt.png
