nathe-vink/earmilk/renders/2026-10-07/shot-01-v22-pt.png

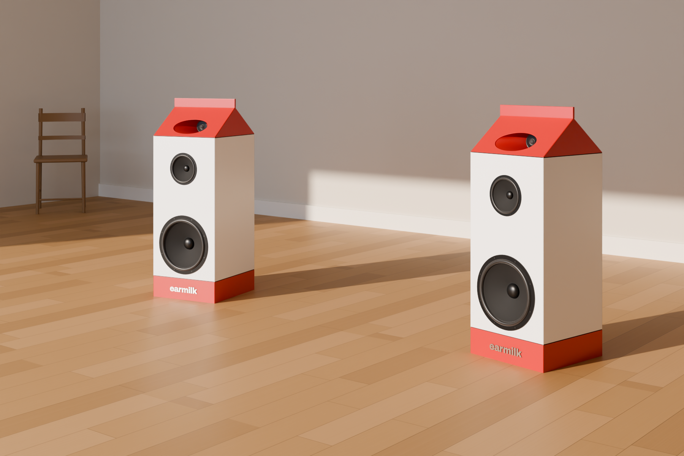
renders/2026-10-07/shot-01-v22-pt.png
