nathe-vink/earmilk/renders/2026-10-07/shot-02-v22a-pt.png

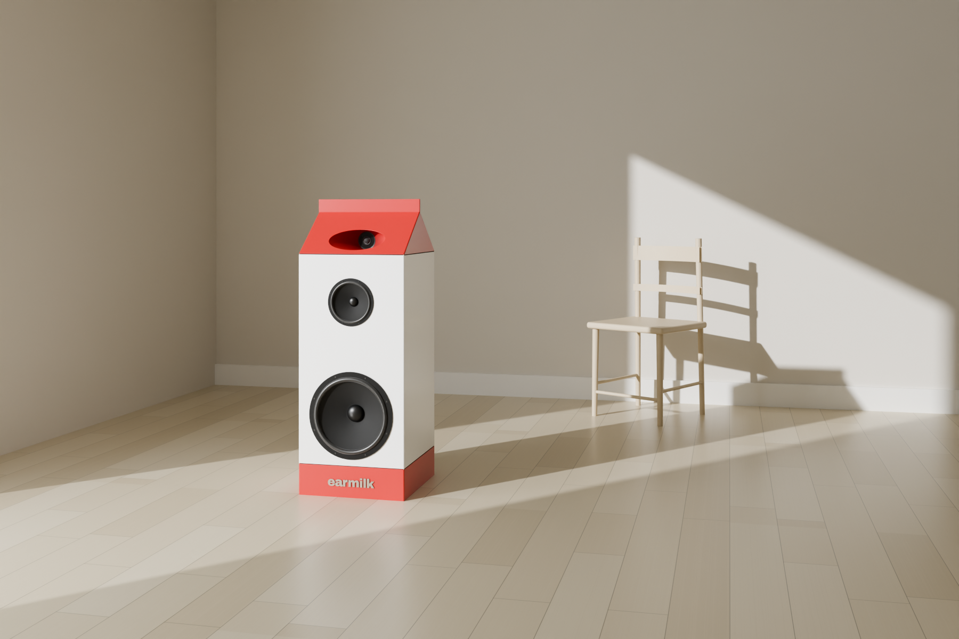
renders/2026-10-07/shot-02-v22a-pt.png
