nathe-vink/earmilk/renders/2026-10-07/shot-04-v20b-pt.png

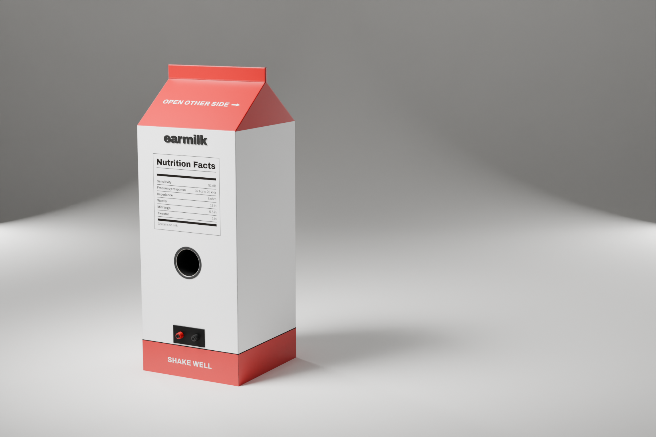
renders/2026-10-07/shot-04-v20b-pt.png
