nathe-vink/earmilk/renders/2026-10-08/engine/01-e16.raw.png

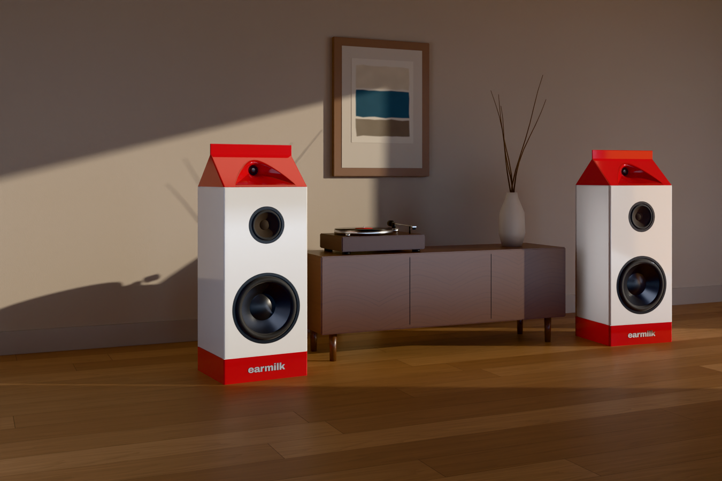
renders/2026-10-08/engine/01-e16.raw.png
