nathe-vink/earmilk/renders/2026-10-08/engine/01-e16.swatch.png

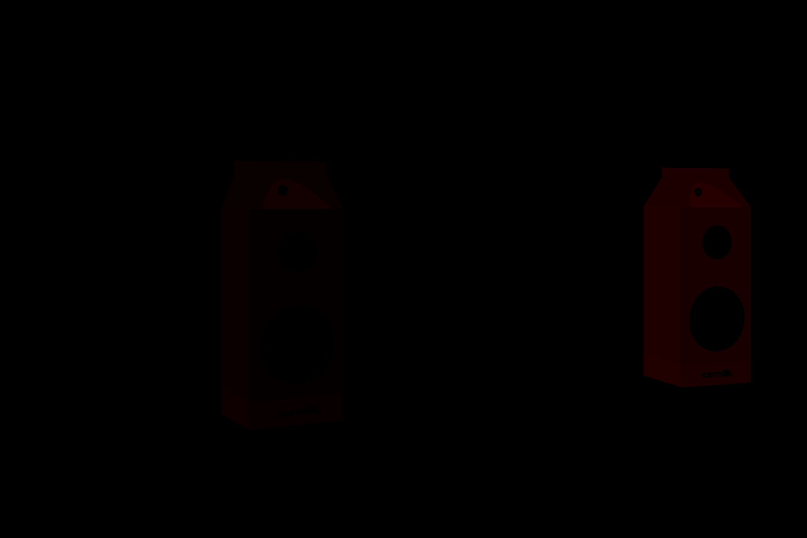
renders/2026-10-08/engine/01-e16.swatch.png
