nathe-vink/earmilk/renders/2026-10-08/engine/02a-e8.png

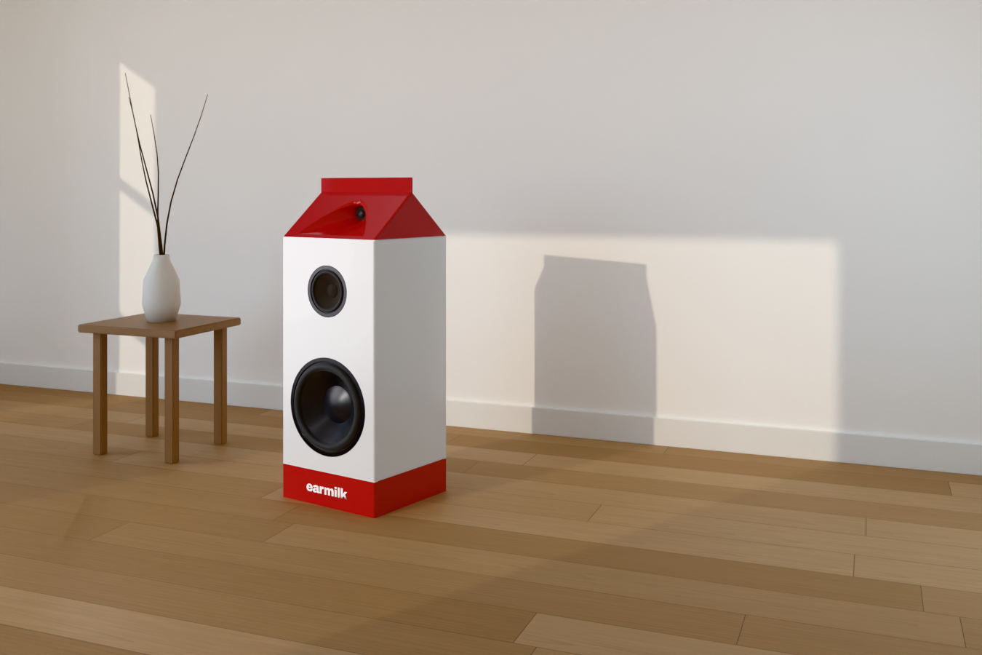
renders/2026-10-08/engine/02a-e8.png
