nathe-vink/earmilk/renders/2026-10-08/engine/02b-e9.png

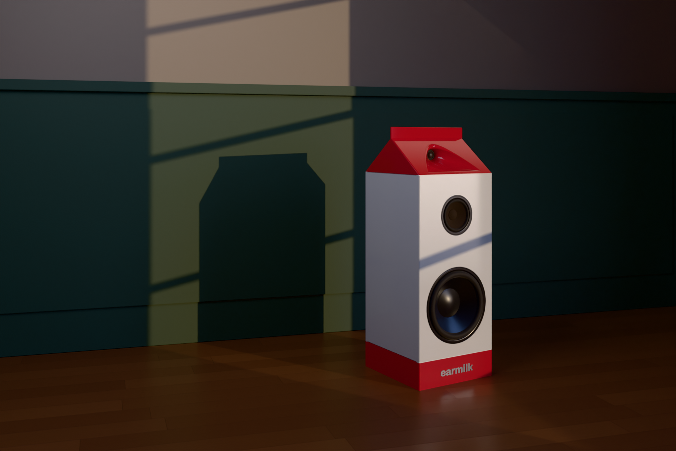
renders/2026-10-08/engine/02b-e9.png
