nathe-vink/earmilk/renders/2026-10-08/engine/02b-e15.png

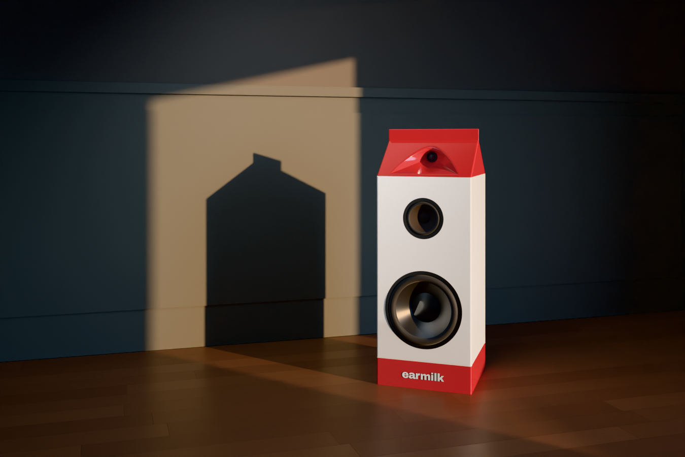
renders/2026-10-08/engine/02b-e15.png
