nathe-vink/earmilk/renders/2026-10-08/engine/03-e7.mask.png

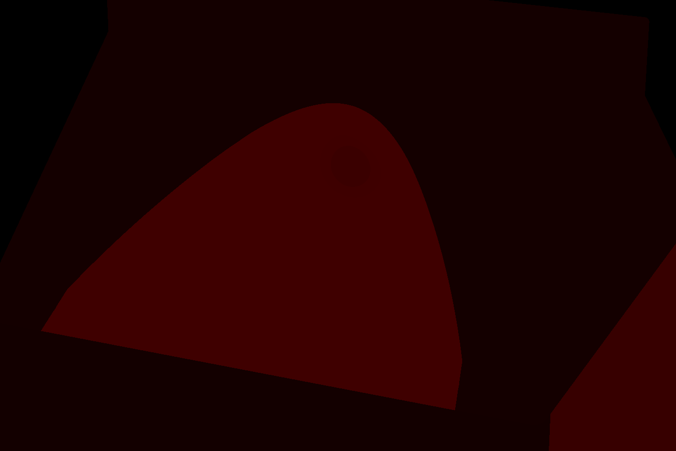
renders/2026-10-08/engine/03-e7.mask.png
