nathe-vink/earmilk/renders/2026-10-08/engine/03-e14.raw.png

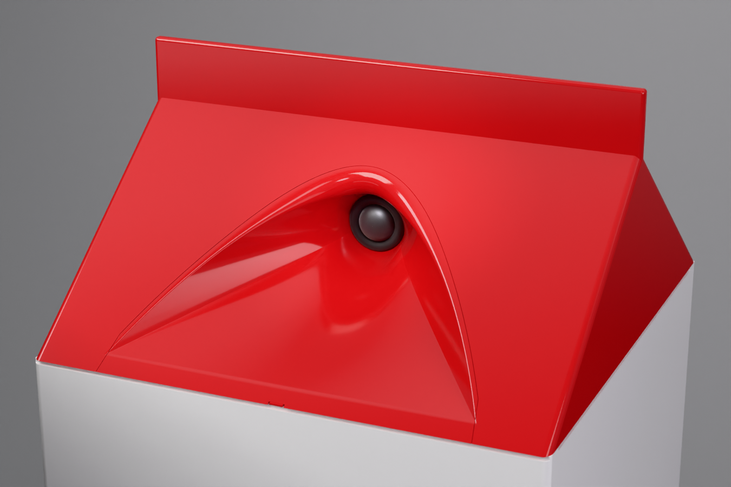
renders/2026-10-08/engine/03-e14.raw.png
