nathe-vink/earmilk/renders/2026-10-08/engine/04a-e7.mask.png

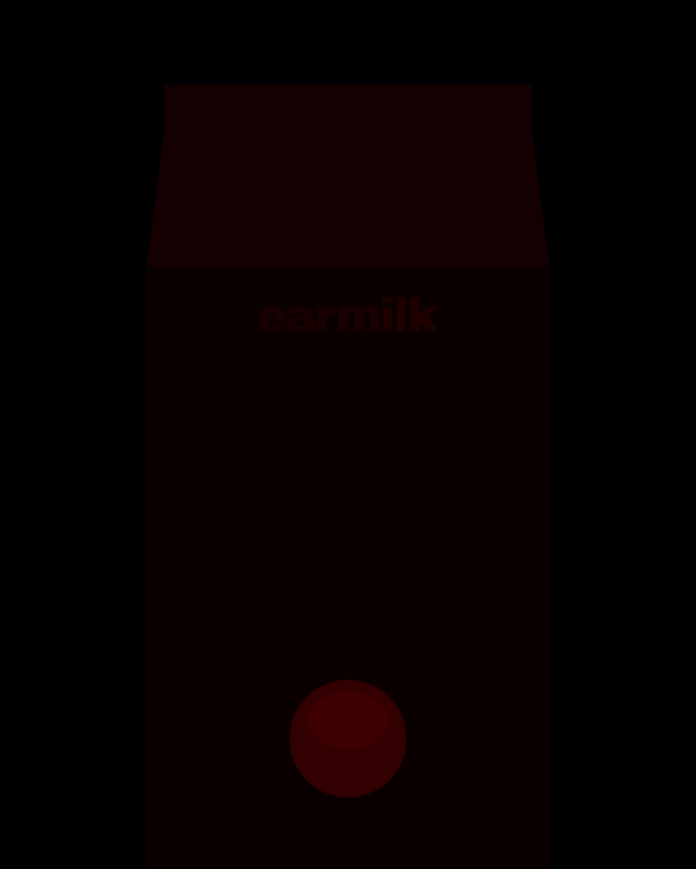
renders/2026-10-08/engine/04a-e7.mask.png
