nathe-vink/earmilk/renders/2026-10-08/engine/04a-e13.png

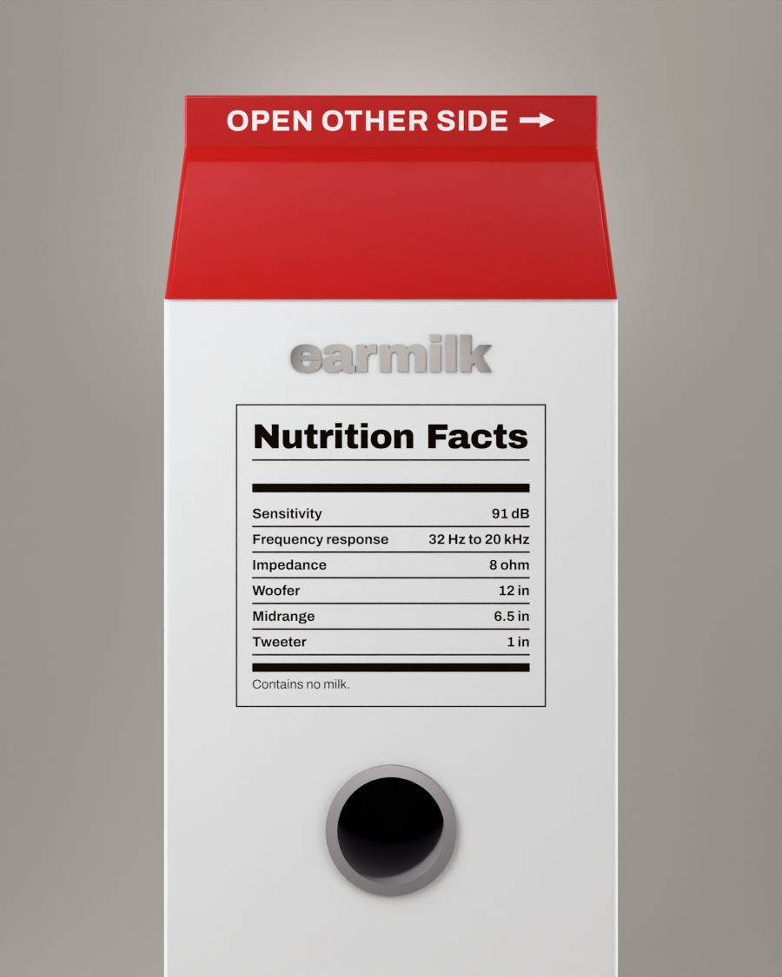
renders/2026-10-08/engine/04a-e13.png
