nathe-vink/earmilk/renders/2026-10-08/engine/04b-e3.mask.png

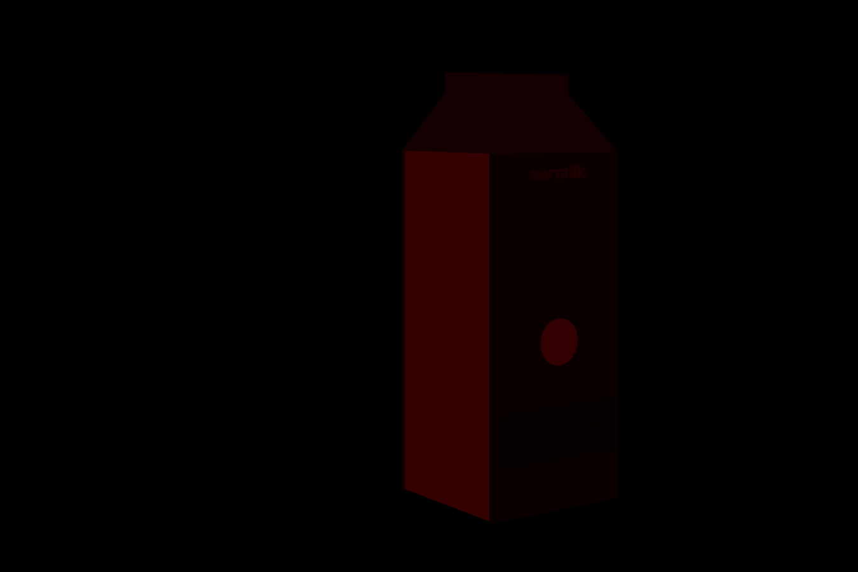
renders/2026-10-08/engine/04b-e3.mask.png
