nathe-vink/earmilk/renders/2026-10-08/engine/04b-e4.png

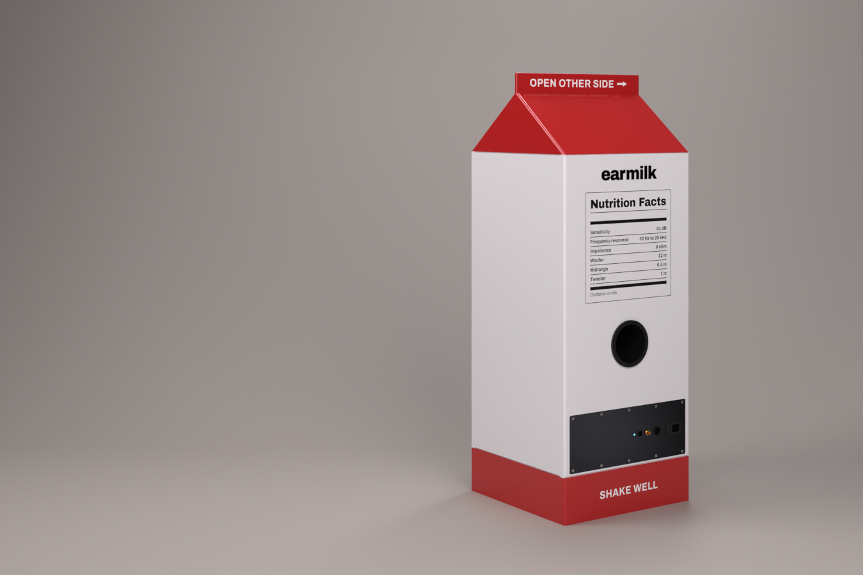
renders/2026-10-08/engine/04b-e4.png
