nathe-vink/earmilk/renders/2026-10-08/engine/04b-e6.png

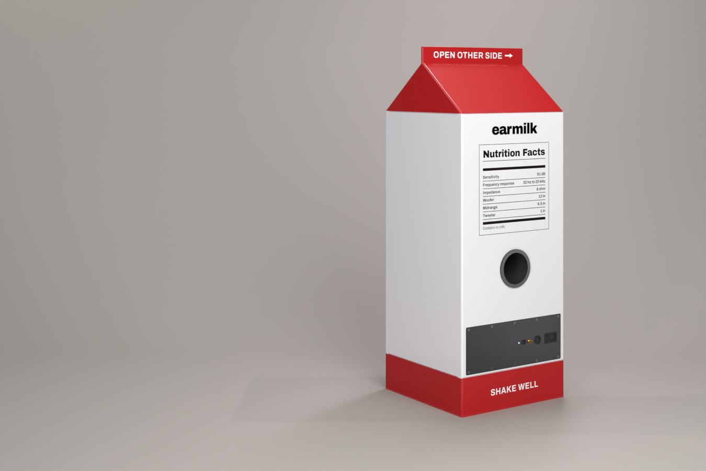
renders/2026-10-08/engine/04b-e6.png
