nathe-vink/earmilk/renders/2026-10-08/engine/05-e2.mask.png

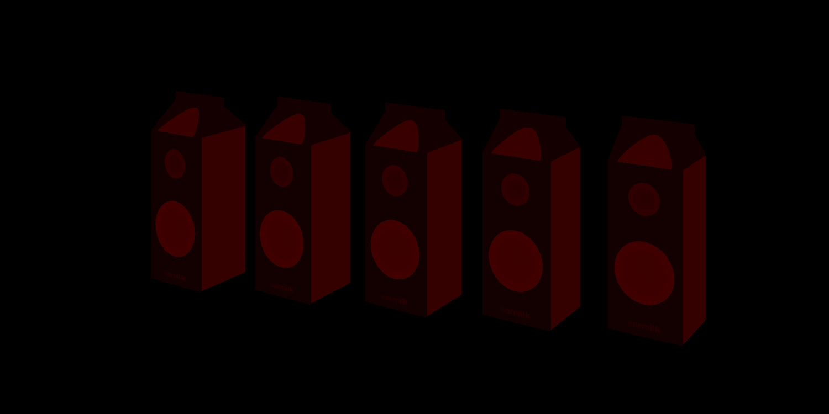
renders/2026-10-08/engine/05-e2.mask.png
