nathe-vink/earmilk/renders/2026-10-08/engine/05-e6.mask.png

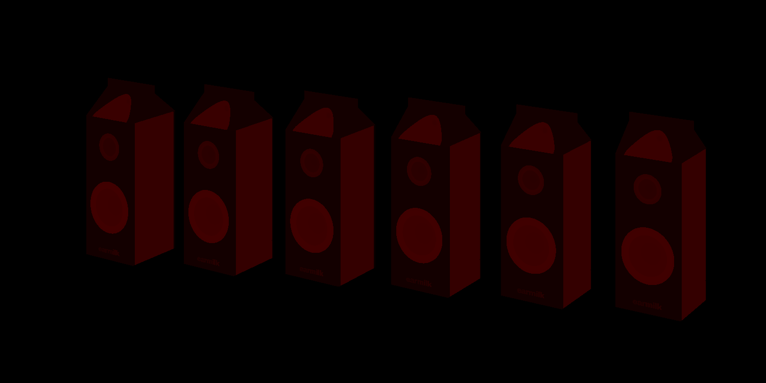
renders/2026-10-08/engine/05-e6.mask.png
