nathe-vink/earmilk/renders/2026-10-08/engine/05-e11.mirror.png

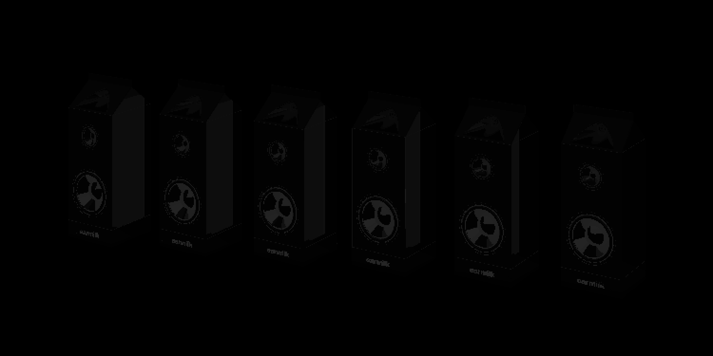
renders/2026-10-08/engine/05-e11.mirror.png
