nathe-vink/earmilk/renders/2026-10-08/engine/07-e1.png

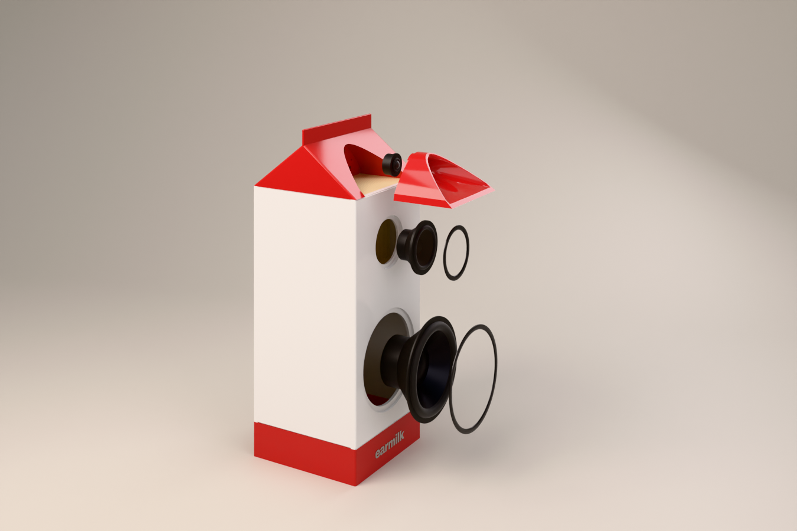
renders/2026-10-08/engine/07-e1.png
