nathe-vink/earmilk/renders/2026-10-08/engine/07-e12.mirror.png

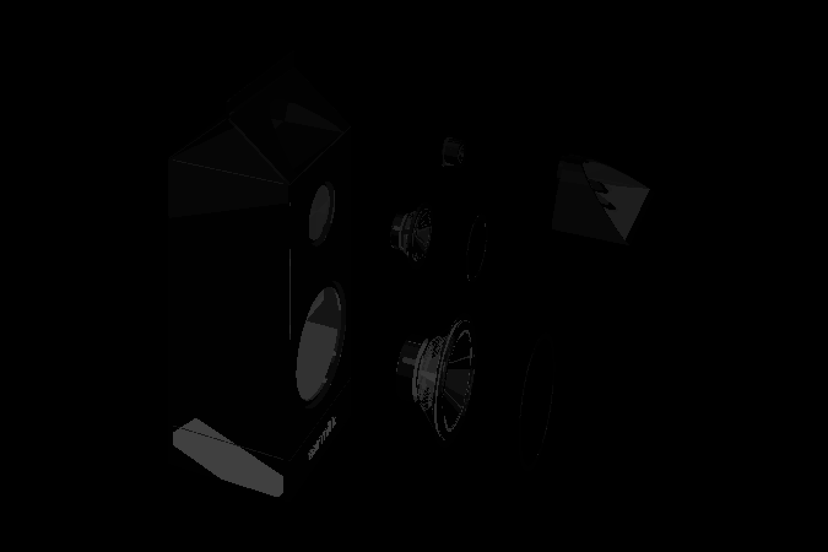
renders/2026-10-08/engine/07-e12.mirror.png
