nathe-vink/earmilk/renders/2026-10-08/engine/08-e2.png

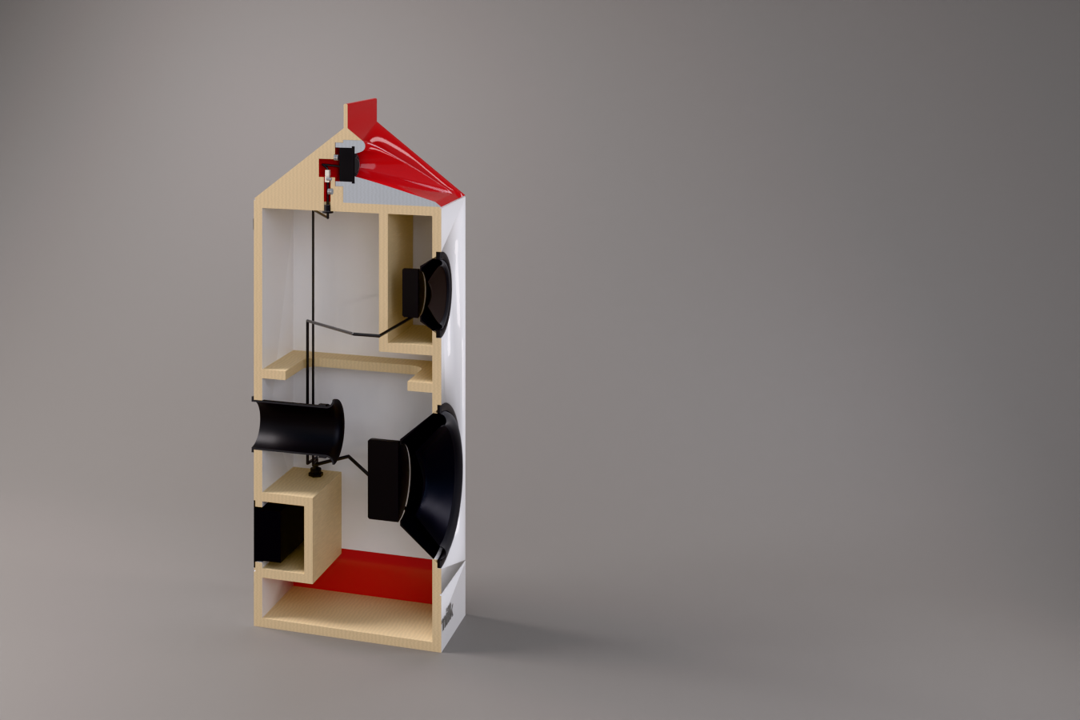
renders/2026-10-08/engine/08-e2.png
