nathe-vink/earmilk/renders/2026-10-08/engine/08-e15.raw.png

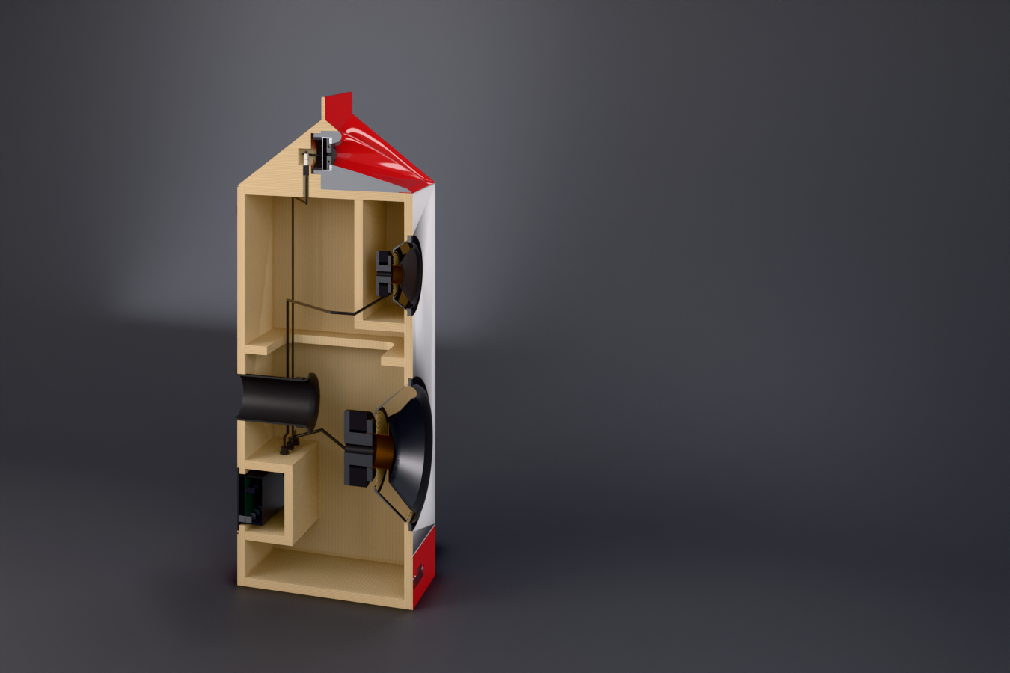
renders/2026-10-08/engine/08-e15.raw.png
