nathe-vink/earmilk/renders/2026-10-08/engine/08b-e1.mask.png

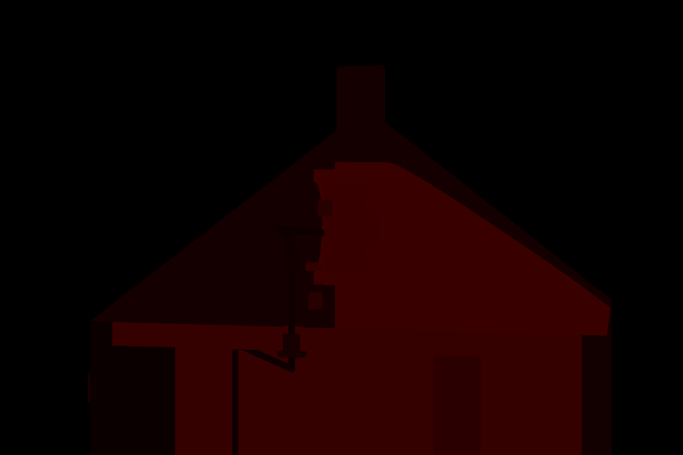
renders/2026-10-08/engine/08b-e1.mask.png
