nathe-vink/earmilk/renders/2026-10-08/engine/08b-e5.png

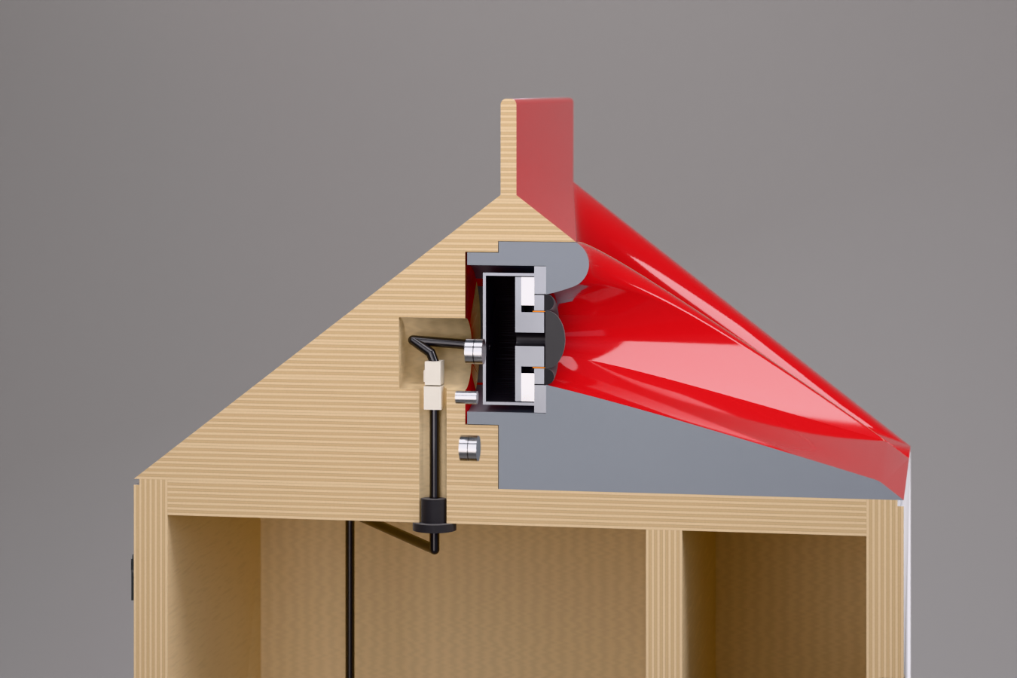
renders/2026-10-08/engine/08b-e5.png
