nathe-vink/earmilk/renders/2026-10-08/engine/08b-e9.mirror.png

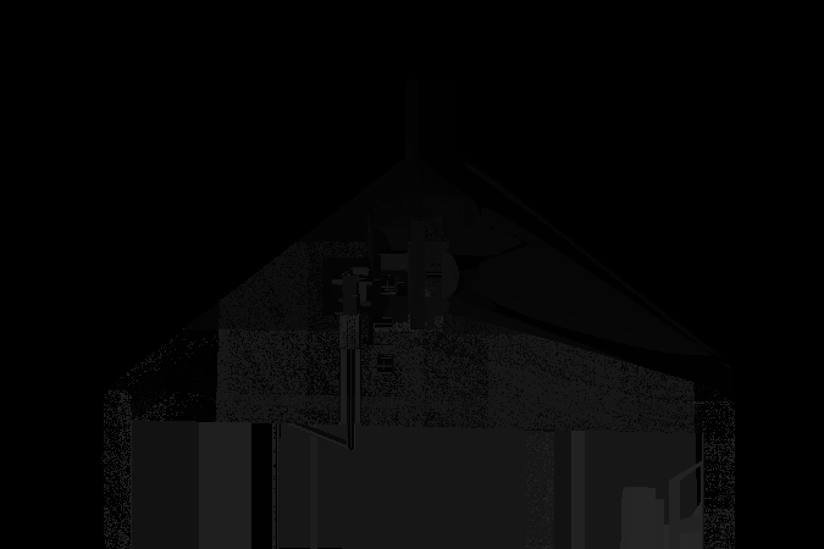
renders/2026-10-08/engine/08b-e9.mirror.png
