nathe-vink/earmilk/renders/2026-10-08/engine/08b-e11.raw.png

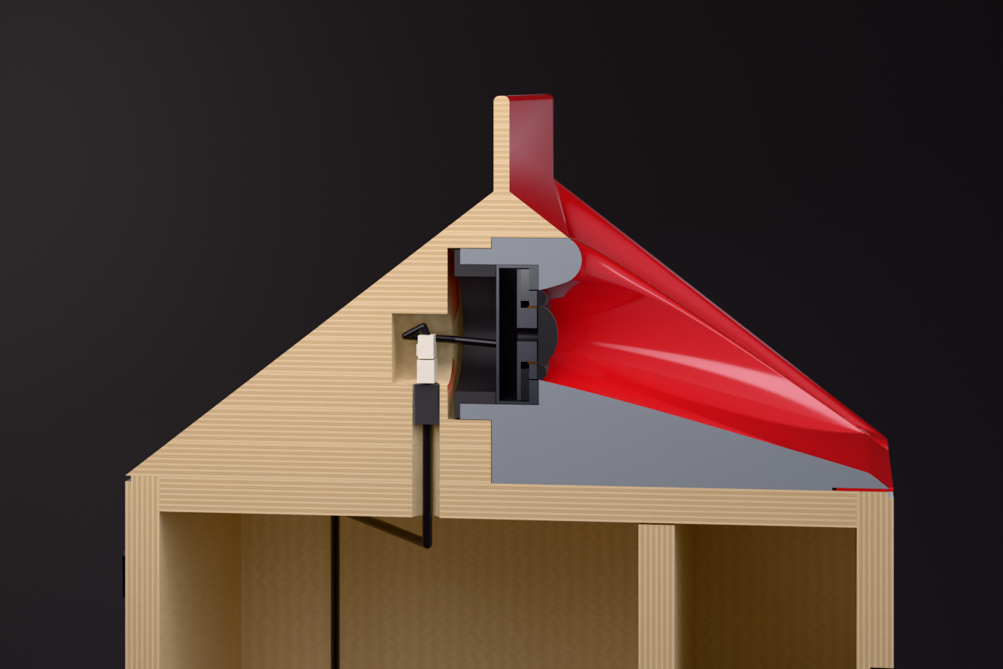
renders/2026-10-08/engine/08b-e11.raw.png
