nathe-vink/earmilk/renders/2026-10-08/engine/09-e11.mirror.png

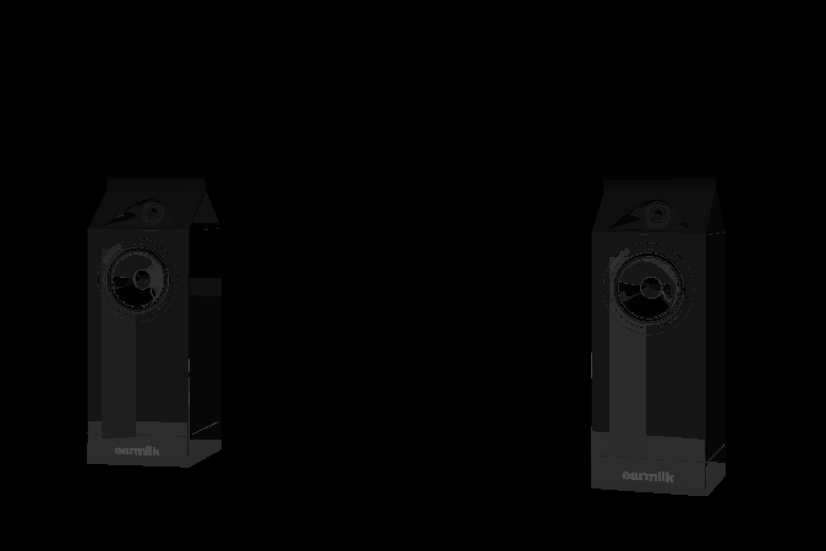
renders/2026-10-08/engine/09-e11.mirror.png
