nathe-vink/earmilk/renders/2026-10-08/engine/09-e14.mask.png

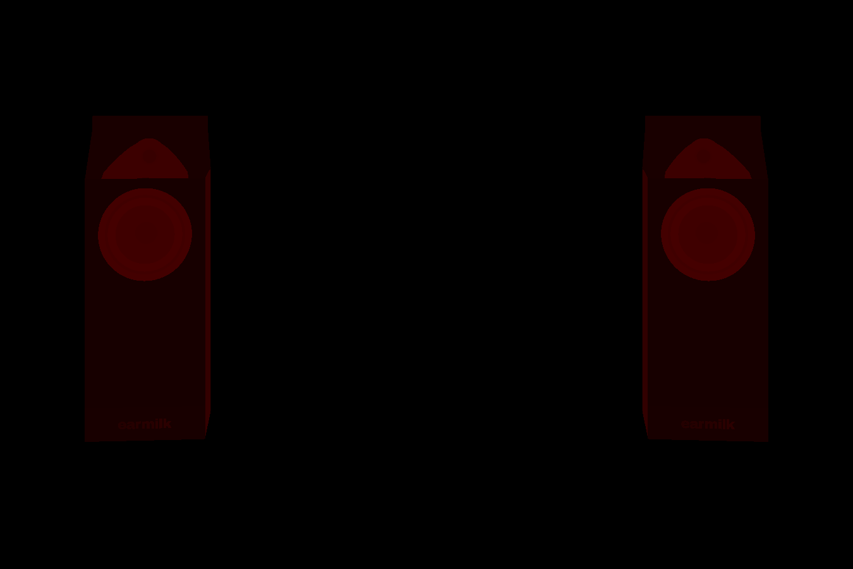
renders/2026-10-08/engine/09-e14.mask.png
