nathe-vink/earmilk/renders/2026-10-08/engine/10-e7.png

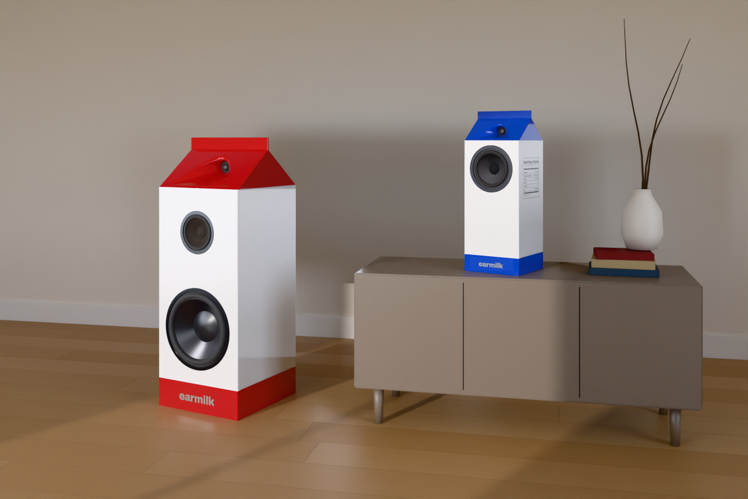
renders/2026-10-08/engine/10-e7.png
