nathe-vink/earmilk/renders/2026-10-08/engine/10-e11.swatch.png

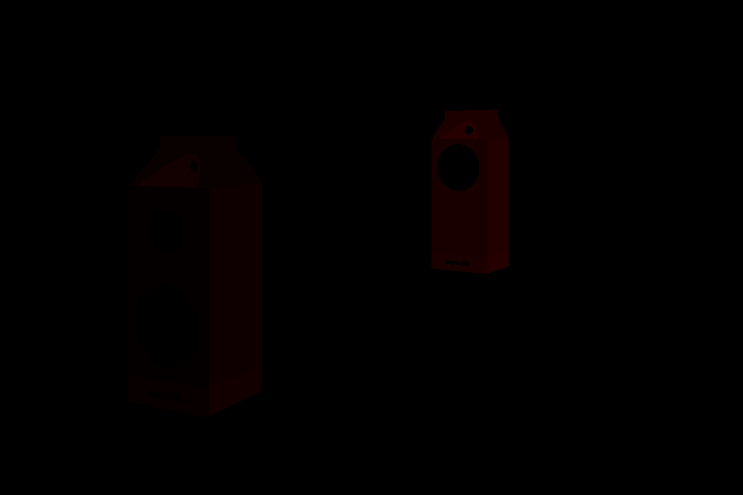
renders/2026-10-08/engine/10-e11.swatch.png
