nathe-vink/earmilk/renders/2026-10-08/shot-02-v26b-pt.png

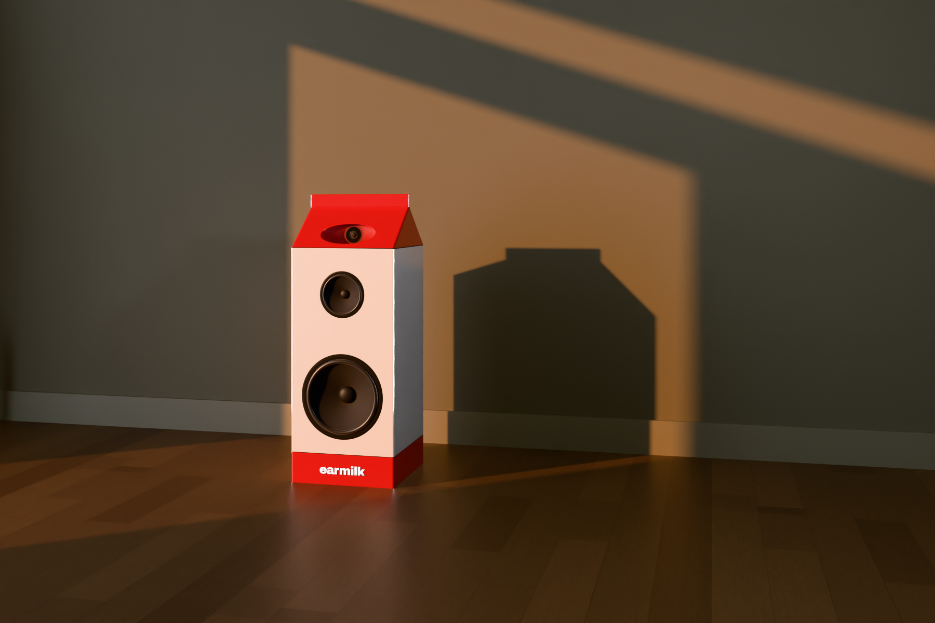
renders/2026-10-08/shot-02-v26b-pt.png
