nathe-vink/earmilk/renders/2026-10-08/shot-03-v23-pt.png

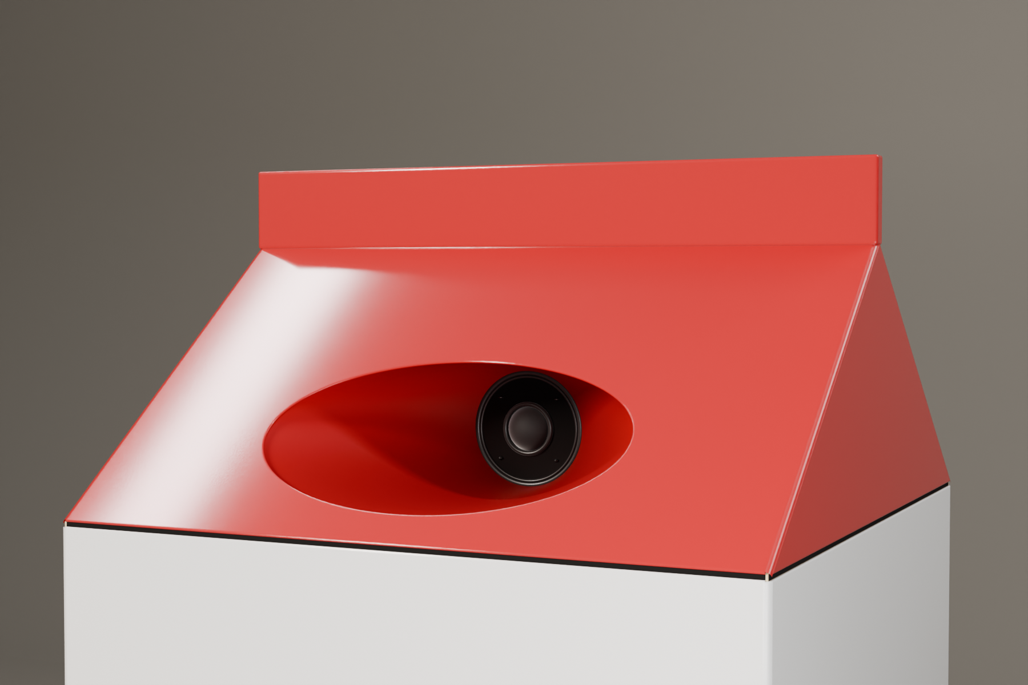
renders/2026-10-08/shot-03-v23-pt.png
