nathe-vink/earmilk/renders/2026-10-08/shot-03-v25-pt.png

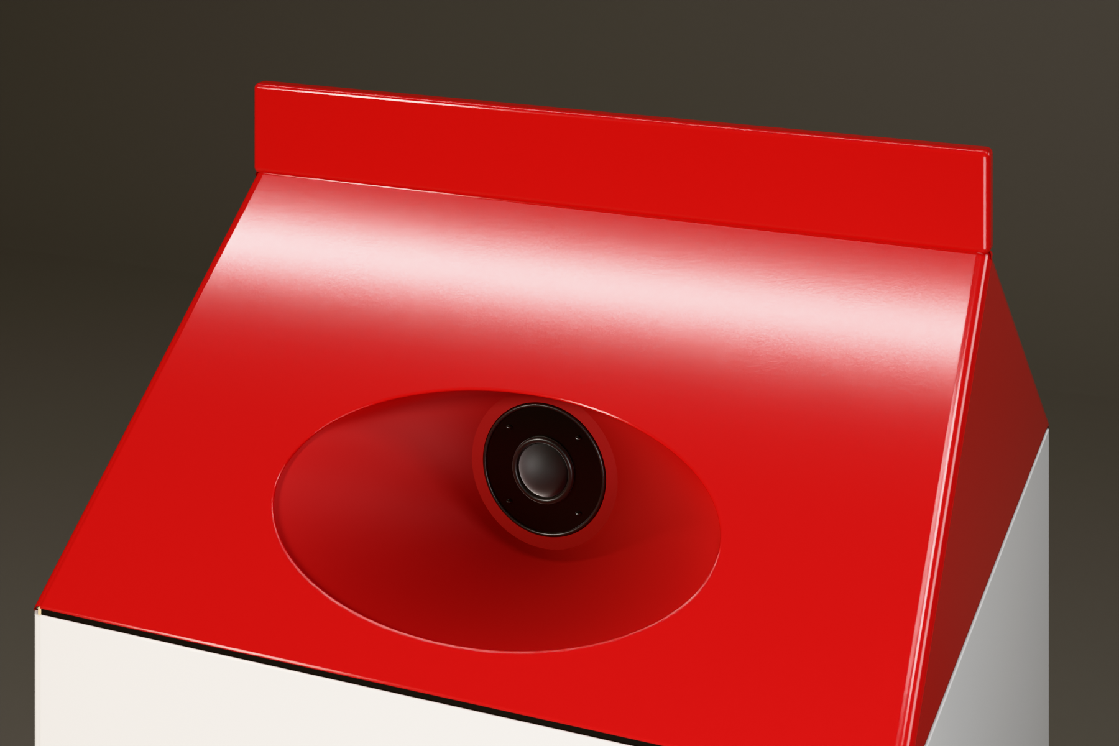
renders/2026-10-08/shot-03-v25-pt.png
