nathe-vink/earmilk/renders/2026-10-08/shot-03-v26-pt.png

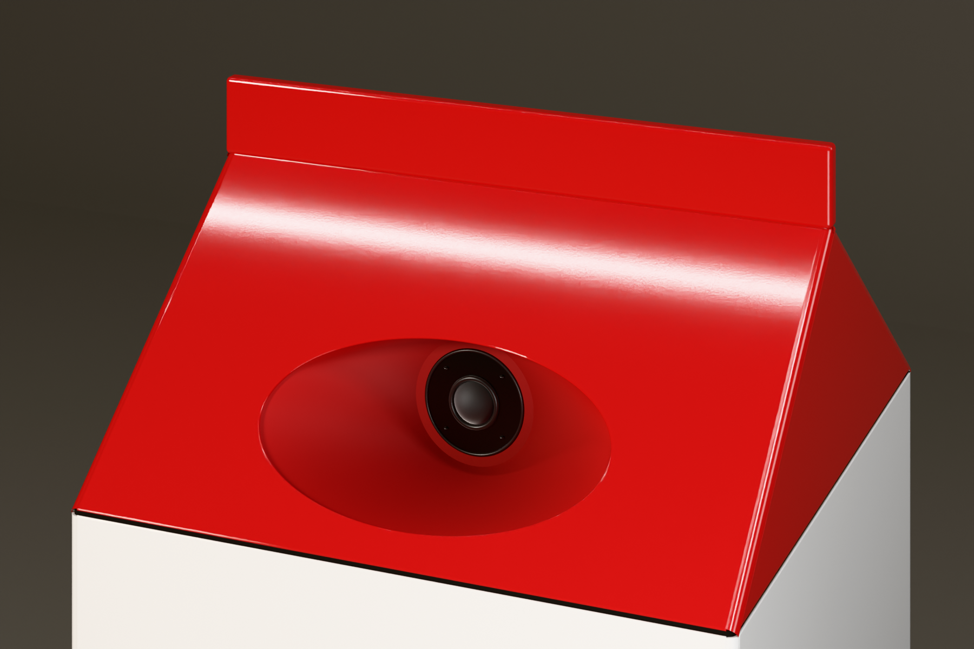
renders/2026-10-08/shot-03-v26-pt.png
