nathe-vink/earmilk/renders/2026-10-08/shot-04-v24a-pt.png

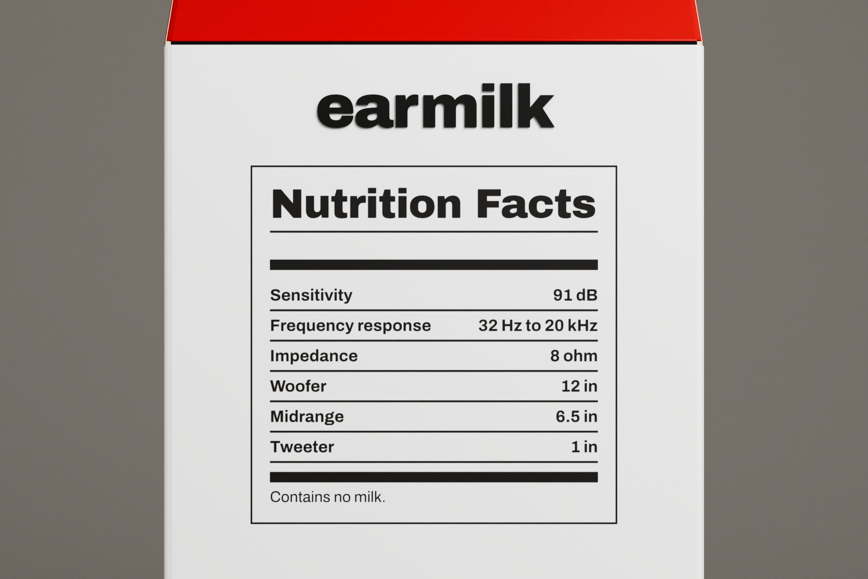
renders/2026-10-08/shot-04-v24a-pt.png
