nathe-vink/earmilk/renders/2026-10-08/shot-06-v24-pt.png

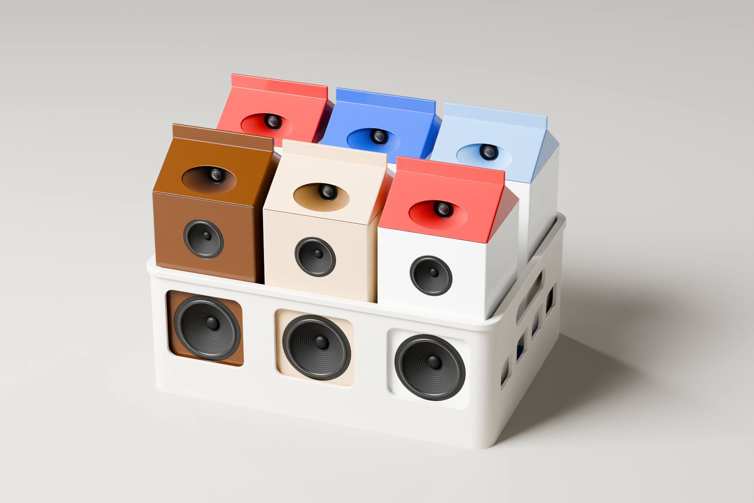
renders/2026-10-08/shot-06-v24-pt.png
