nathe-vink/earmilk/renders/2026-10-09/engine/polariser-03-proof.png

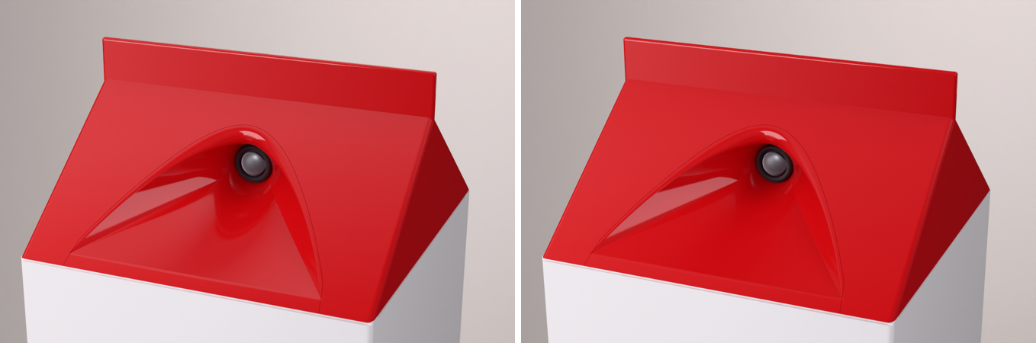
renders/2026-10-09/engine/polariser-03-proof.png
