nathe-vink/earmilk/renders/2026-10-10/barkhorn/birch-v2.png

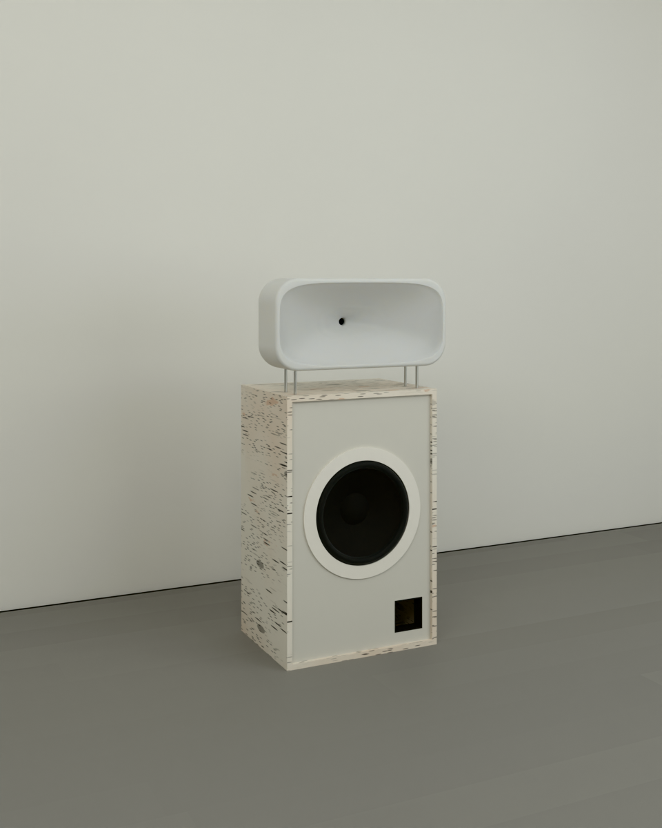
renders/2026-10-10/barkhorn/birch-v2.png
