nathe-vink/earmilk/renders/2026-10-10/barkhorn/covers/birch-cloth.png

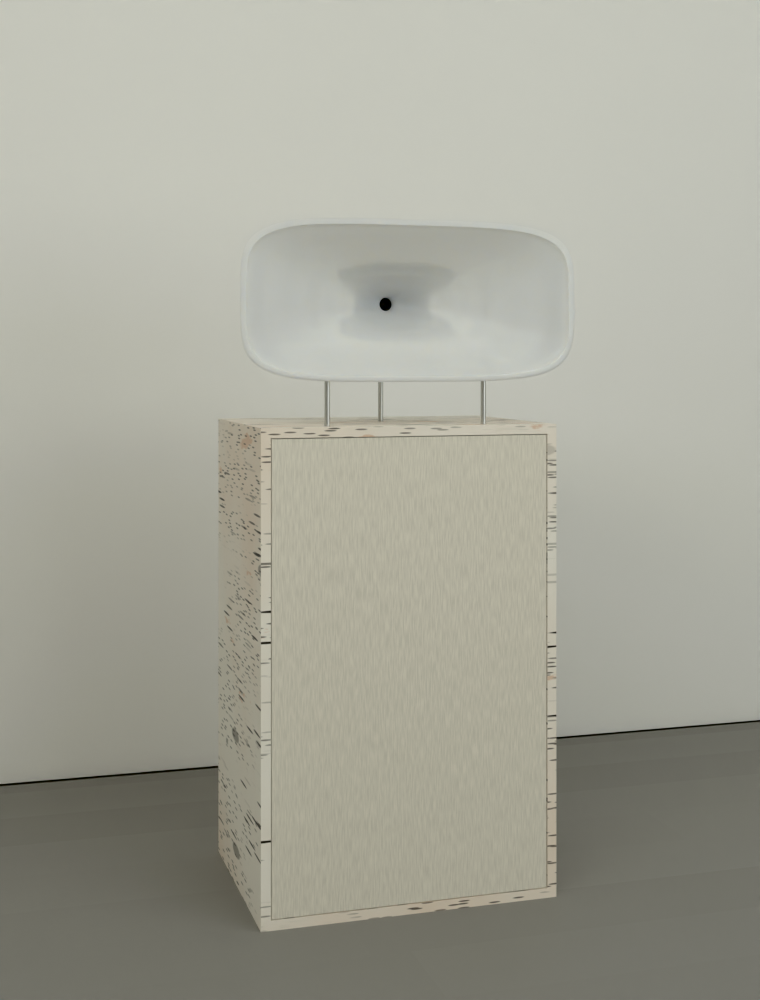
renders/2026-10-10/barkhorn/covers/birch-cloth.png
