nathe-vink/earmilk/renders/2026-10-10/barkhorn/covers/eucalyptus-bark-face.png

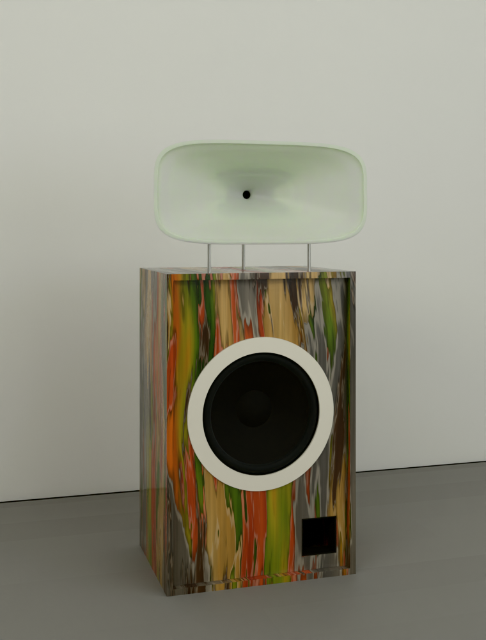
renders/2026-10-10/barkhorn/covers/eucalyptus-bark-face.png
