nathe-vink/earmilk/renders/2026-10-10/barkhorn/eucalyptus-detail-v3.png

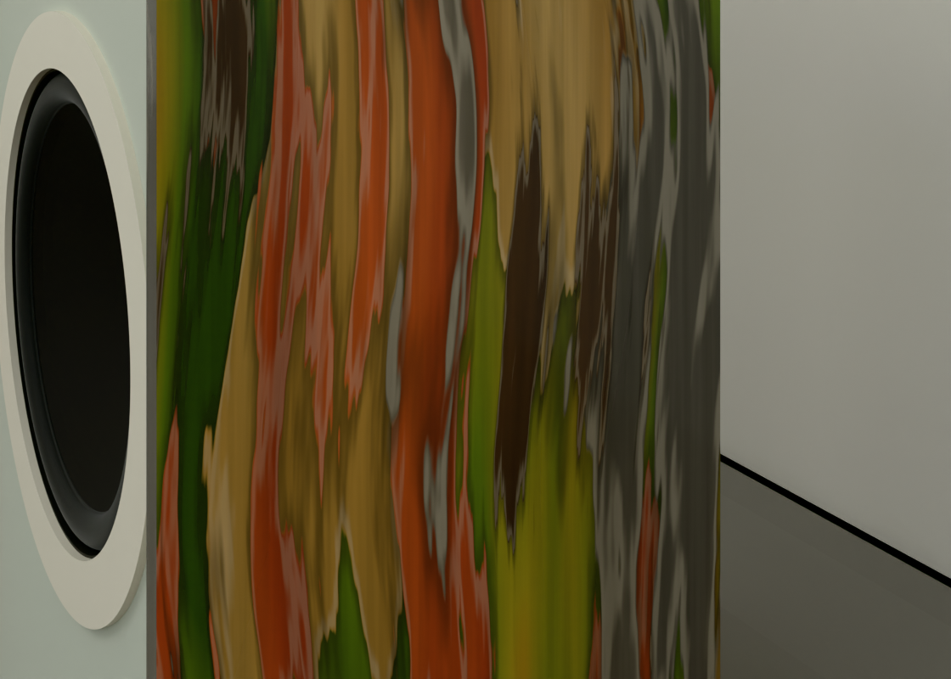
renders/2026-10-10/barkhorn/eucalyptus-detail-v3.png
