nathe-vink/earmilk/spinoffs/earwig/renders/detail-v1.png

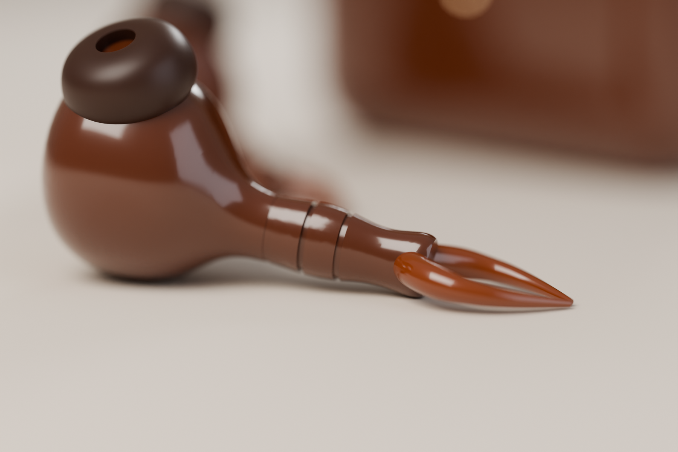
spinoffs/earwig/renders/detail-v1.png
