nathe-vink/earmilk/spinoffs/earwig/renders/detail-v4.png

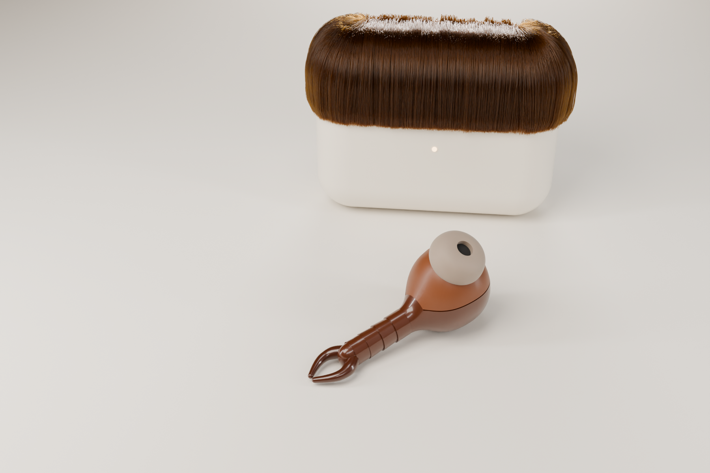
spinoffs/earwig/renders/detail-v4.png
