nathe-vink/earmilk/spinoffs/earwig/renders/detail-v6.png

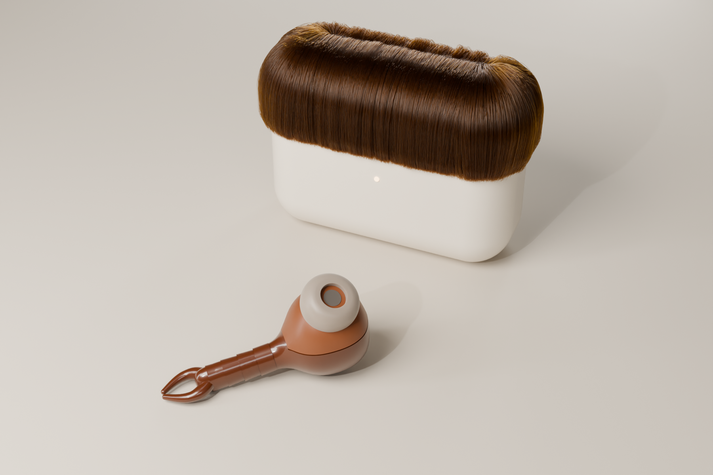
spinoffs/earwig/renders/detail-v6.png
