nathe-vink/earmilk/spinoffs/earwig/renders/hero-v3.png

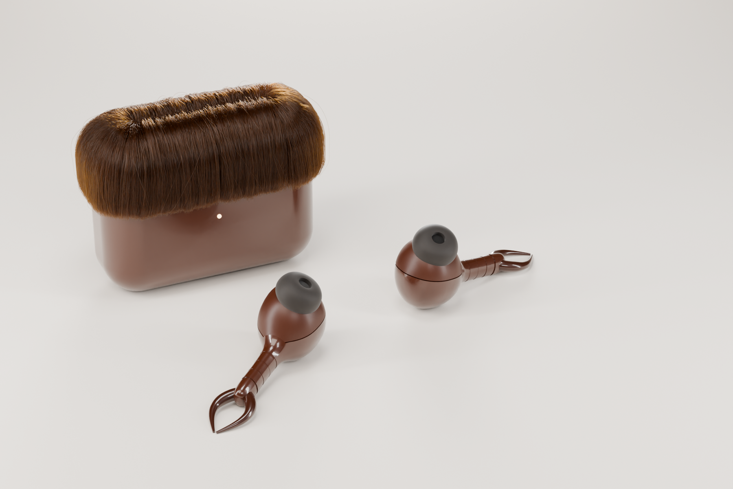
spinoffs/earwig/renders/hero-v3.png
