nathe-vink/earmilk/spinoffs/earwig/renders/hero-v5.png

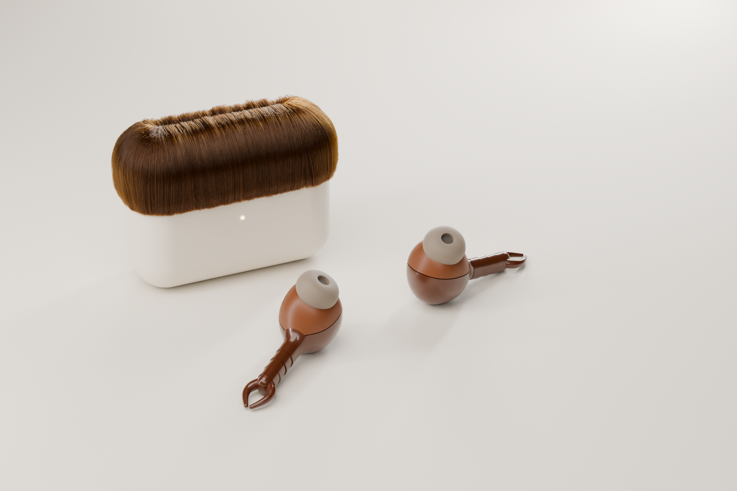
spinoffs/earwig/renders/hero-v5.png
