nathe-vink/earmilk/spinoffs/earworm/renders/detail-v2.png

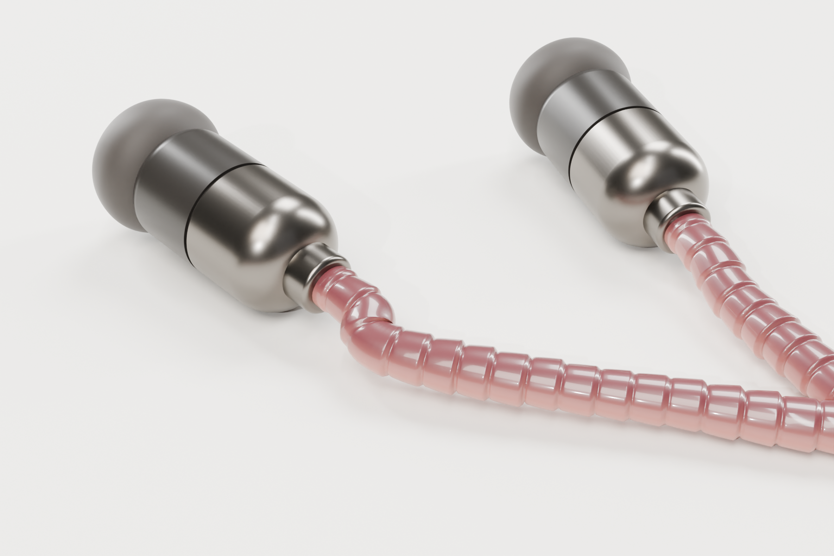
spinoffs/earworm/renders/detail-v2.png
