nathe-vink/earmilk/spinoffs/earworm/renders/detail-v6.png

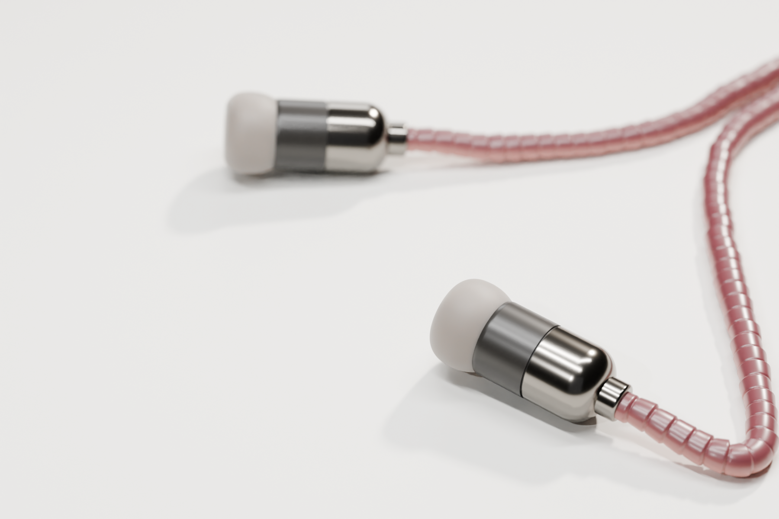
spinoffs/earworm/renders/detail-v6.png
