nathe-vink/earmilk/spinoffs/earworm/renders/hero-v1.png

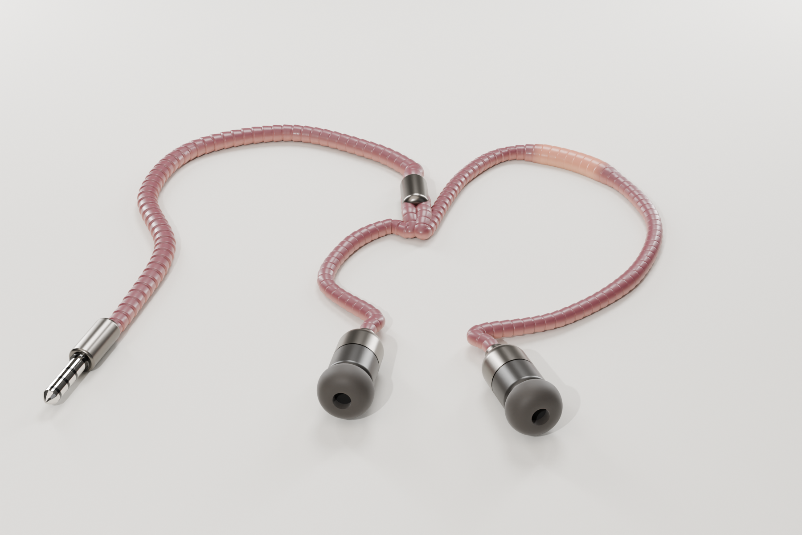
spinoffs/earworm/renders/hero-v1.png
