nathe-vink/earmilk/spinoffs/earworm/renders/hero-v2.png

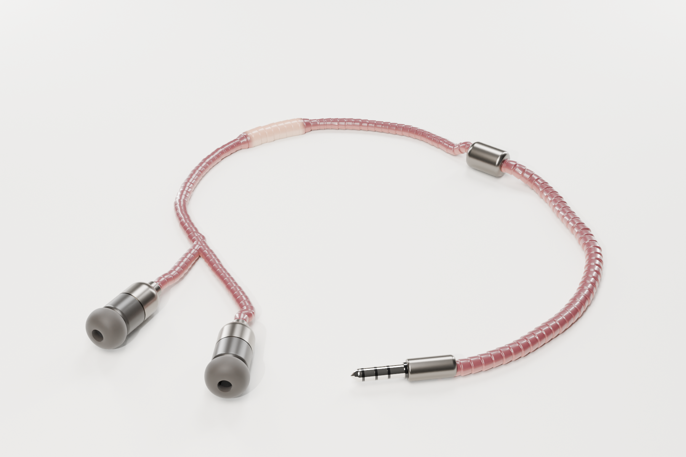
spinoffs/earworm/renders/hero-v2.png
