nathe-vink/earmilk/spinoffs/earworm/renders/hero-v3.png

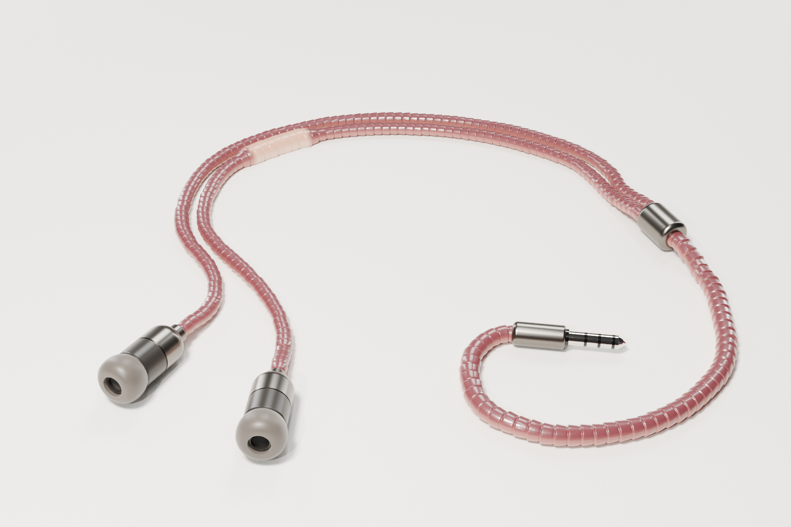
spinoffs/earworm/renders/hero-v3.png
