nathe-vink/earmilk/spinoffs/earworm/renders/hero-v4.png

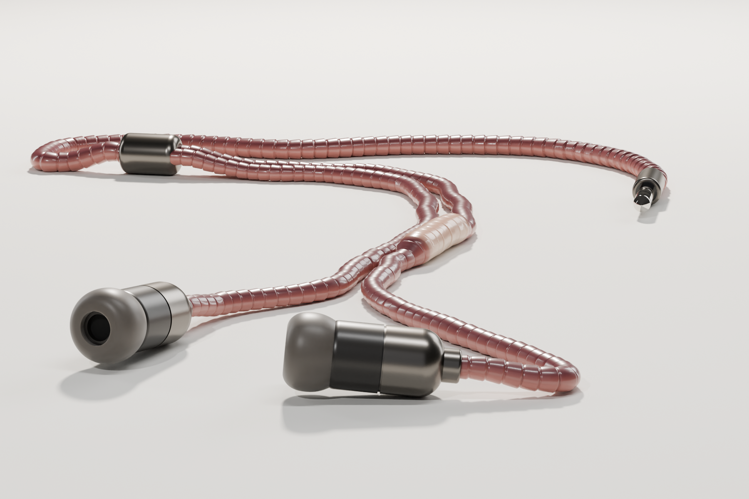
spinoffs/earworm/renders/hero-v4.png
