nathe-vink/earmilk/spinoffs/earworm/renders/over-ear/hero-v2.png

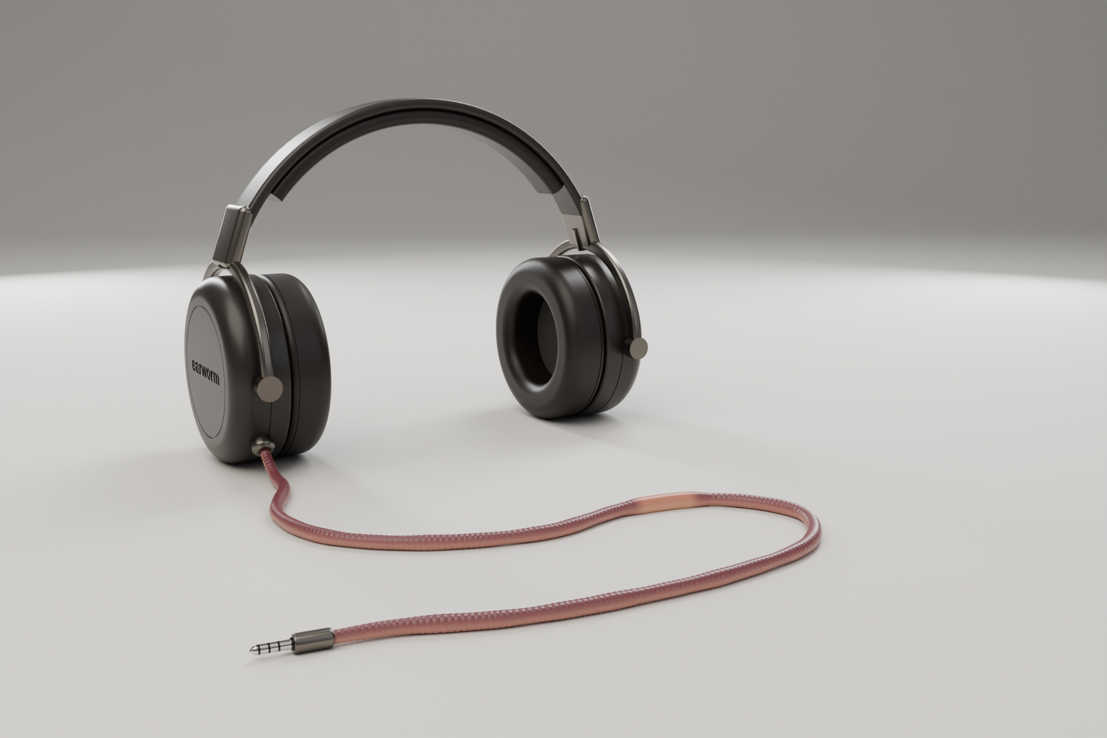
spinoffs/earworm/renders/over-ear/hero-v2.png
