nathe-vink/earmilk/spinoffs/earworm/out/step/plug.step

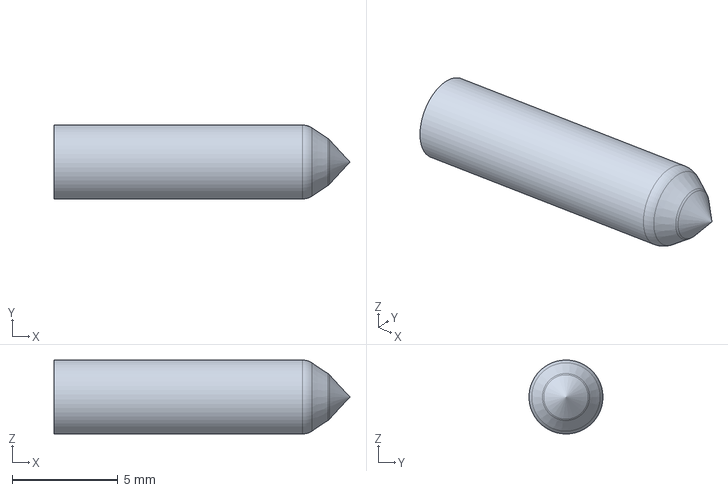
[picture p197: CAD file, 2026-10-05]
spinoffs/earworm/out/step/plug.step
14.0 x 3.50 x 3.50 mm
