nathe-vink/earmilk/studio/fabkit/example/out/dxf/left.dxf

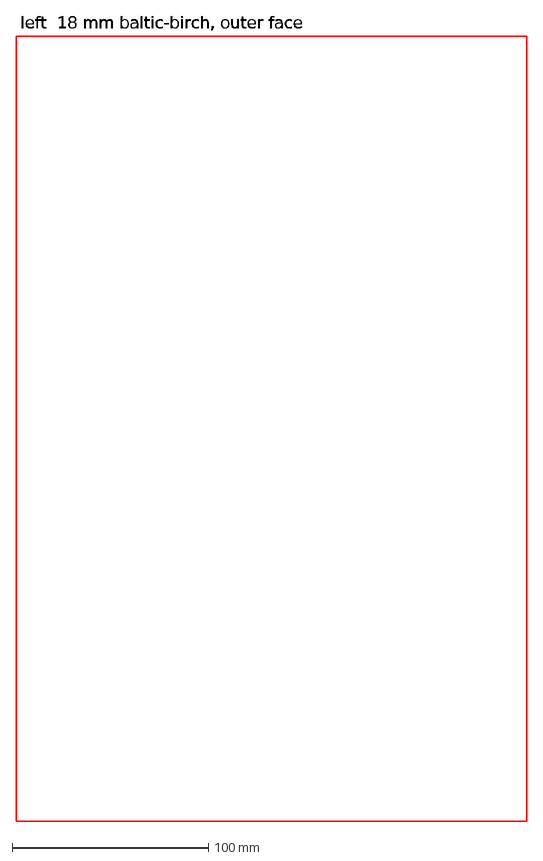
[picture p198: CAD file, 2026-10-11]
studio/fabkit/example/out/dxf/left.dxf
left 18 mm baltic-birch, outer face
