nathe-vink/earmilk/fab/out-bookshelf/dxf/side.dxf

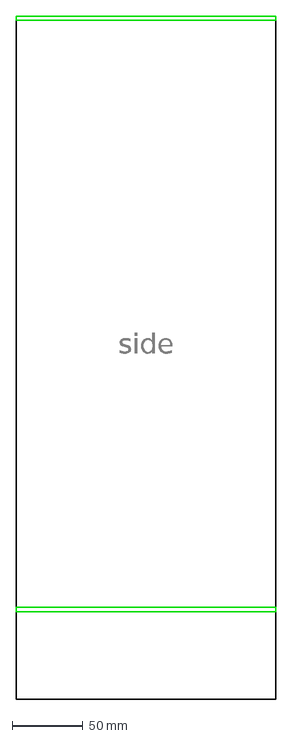
[picture p199: CAD file, 2026-10-09]
fab/out-bookshelf/dxf/side.dxf
side
