nathe-vink/earmilk/fab/out-bookshelf/step/amp-box-lid.step

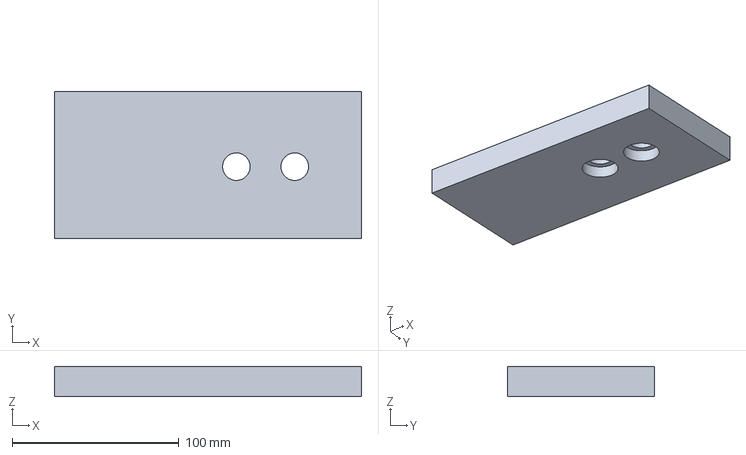
[picture p200: CAD file, 2026-10-09]
fab/out-bookshelf/step/amp-box-lid.step
184.0 x 88.0 x 18.0 mm
