nathe-vink/earmilk/fab/out-bookshelf/stl/trim-ring-woofer.stl

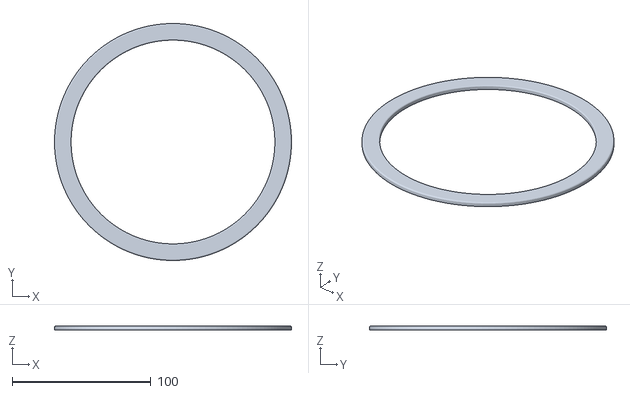
[picture p201: CAD file, 2026-10-09]
fab/out-bookshelf/stl/trim-ring-woofer.stl
171.0 x 170.9 x 3.00
