nathe-vink/earmilk/fab/out/dxf/sheet-1.dxf

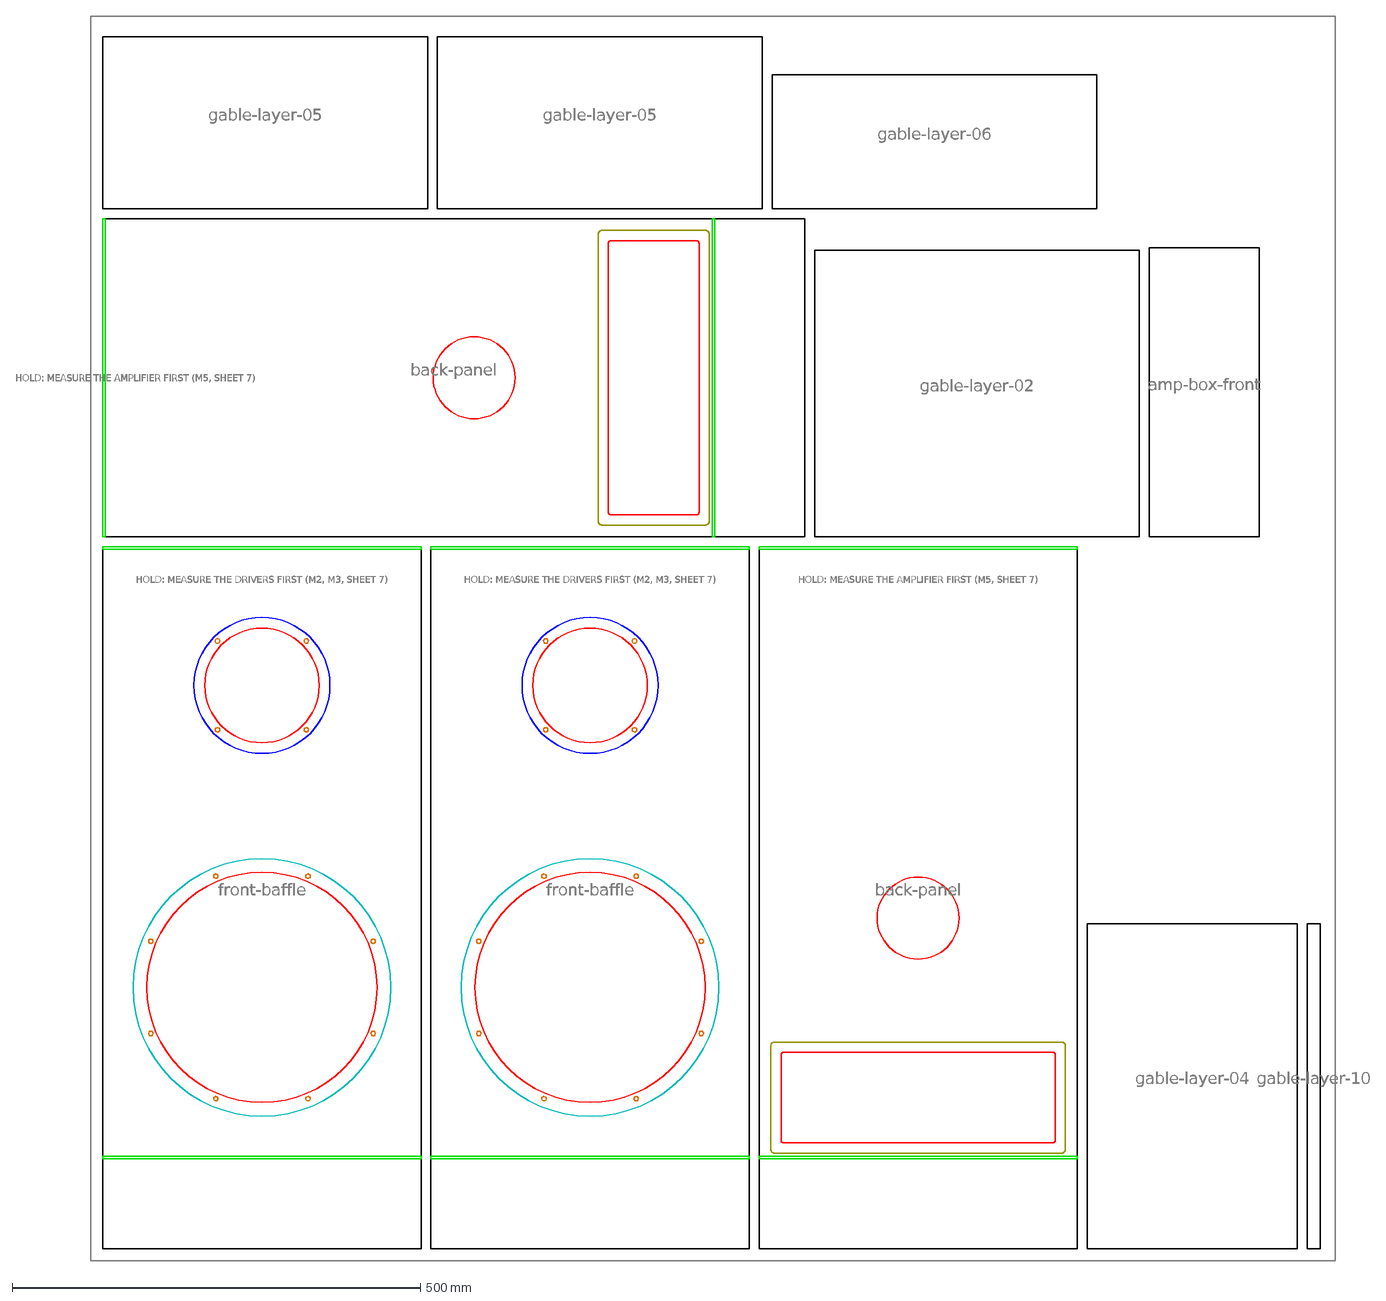
[picture p202: CAD file, 2026-10-09]
fab/out/dxf/sheet-1.dxf
HOLD: MEASURE THE DRIVERS FIRST (M2, M3, SHEET 7)
front-baffle
HOLD: MEASURE THE AMPLIFIER FIRST (M5, SHEET 7)
back-panel
gable-layer-02
gable-layer-04
gable-layer-05
gable-layer-06
gable-layer-10
amp-box-front
