nathe-vink/earmilk/fab/out/step/port-flare-collar.step

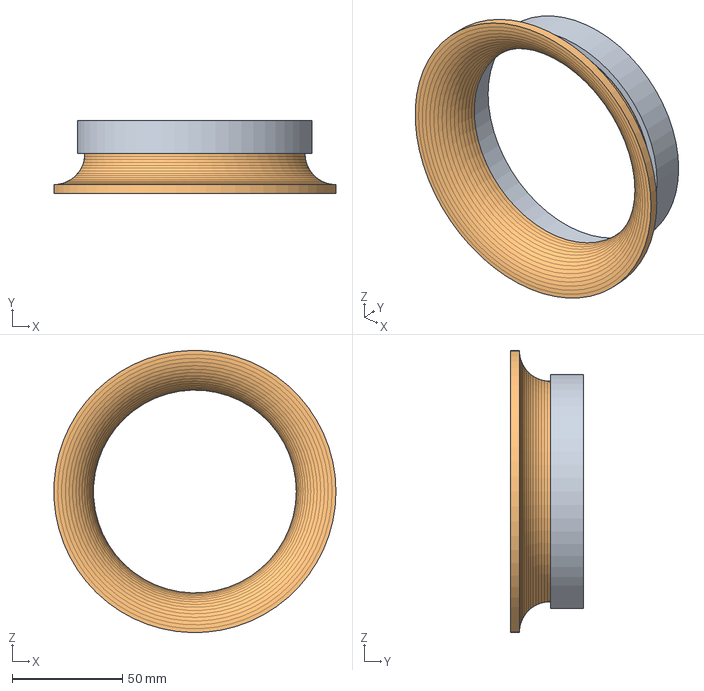
[picture p203: CAD file, 2026-10-09]
fab/out/step/port-flare-collar.step
127.9 x 33.0 x 128.0 mm
