nathe-vink/earmilk/spinoffs/earnest/out/step/feet-24.step

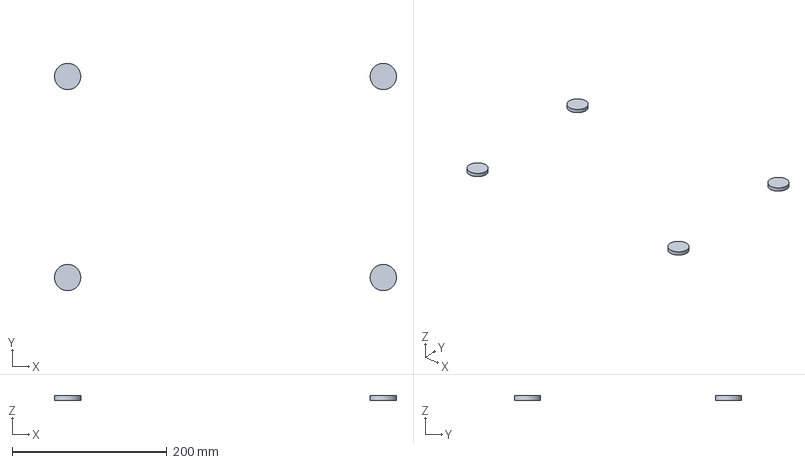
[picture p204: CAD file, 2026-10-09]
spinoffs/earnest/out/step/feet-24.step
441.6 x 293.6 x 6.00 mm
