nathe-vink/earmilk/spinoffs/earnest/out/stl/crate-12.stl

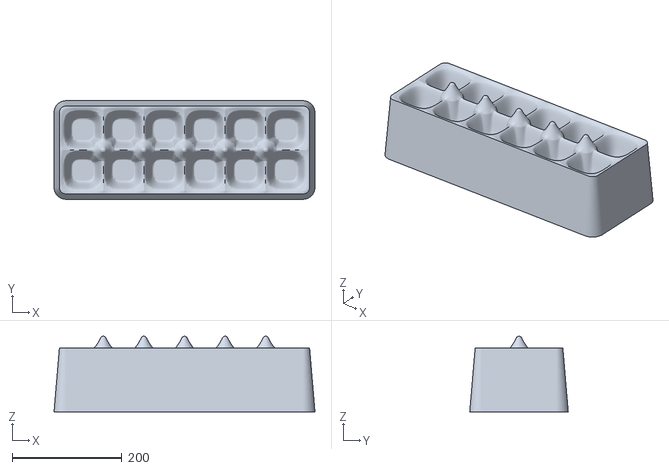
[picture p205: CAD file, 2026-10-09]
spinoffs/earnest/out/stl/crate-12.stl
475.6 x 179.6 x 138.0
