nathe-vink/earmilk/spinoffs/earwig/out/step/inner-r.step

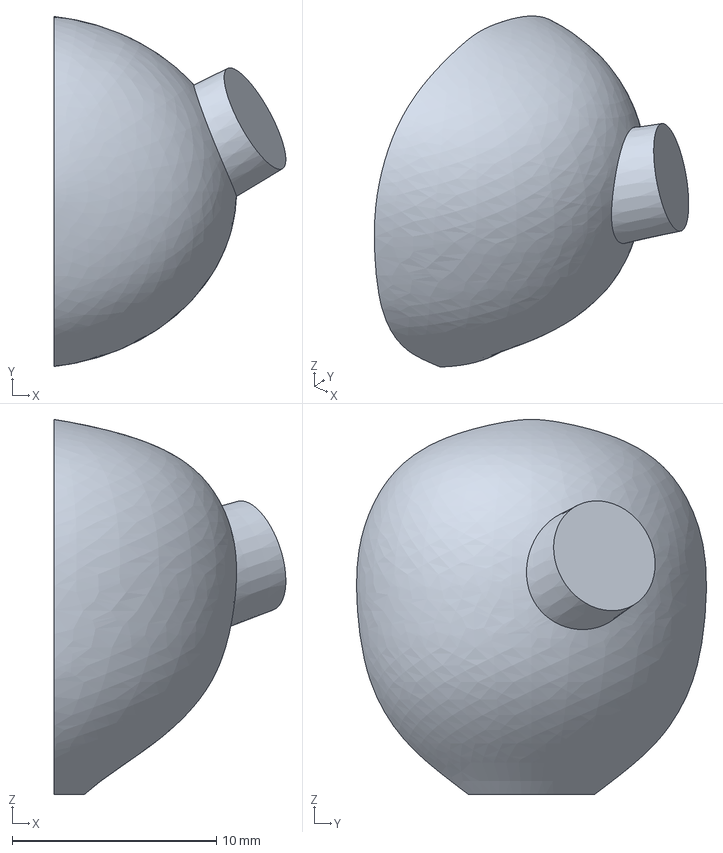
[picture p206: CAD file, 2026-10-06]
spinoffs/earwig/out/step/inner-r.step
11.3 x 17.1 x 18.4 mm
