nathe-vink/earmilk/spinoffs/earworm/out/step/print-shell.step

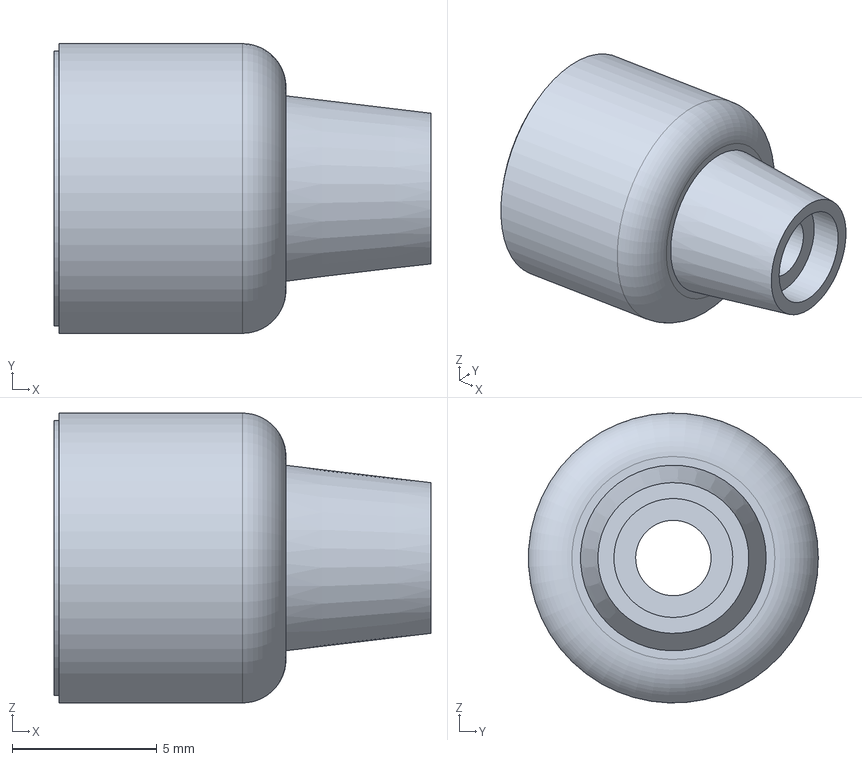
[picture p207: CAD file, 2026-10-05]
spinoffs/earworm/out/step/print-shell.step
13.0 x 9.99 x 10.00 mm
