nathe-vink/earmilk/studio/fabkit/example/out/dxf/top.dxf

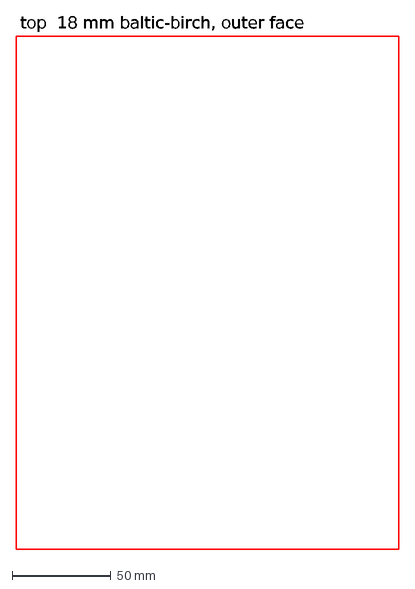
[picture p208: CAD file, 2026-10-11]
studio/fabkit/example/out/dxf/top.dxf
top 18 mm baltic-birch, outer face
