nathe-vink/earmilk/fab/out-bookshelf/dxf/gable-layer-06.dxf

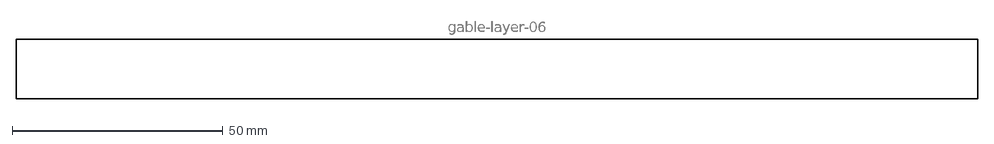
[picture p209: CAD file, 2026-10-09]
fab/out-bookshelf/dxf/gable-layer-06.dxf
gable-layer-06
