nathe-vink/earmilk/fab/out-bookshelf/step/side-right.step

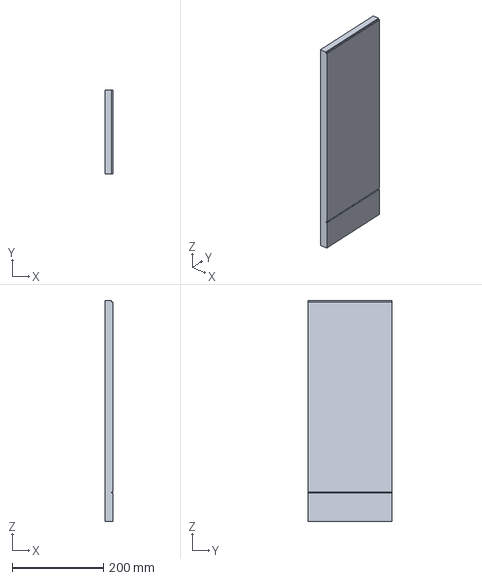
[picture p210: CAD file, 2026-10-09]
fab/out-bookshelf/step/side-right.step
18.0 x 184.0 x 484.0 mm
