nathe-vink/earmilk/fab/out-bookshelf/stl/gable-print/gable-print-rear-left.stl

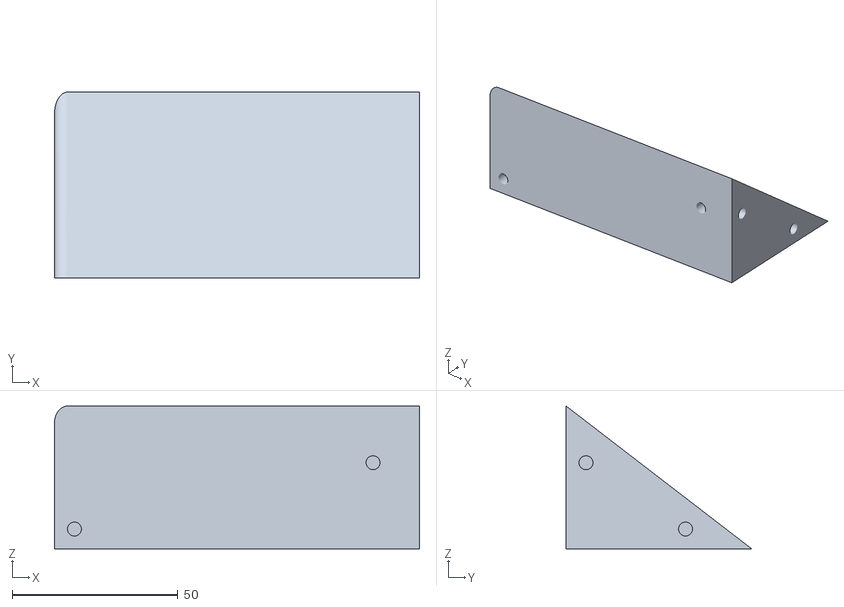
[picture p211: CAD file, 2026-10-09]
fab/out-bookshelf/stl/gable-print/gable-print-rear-left.stl
110.0 x 56.0 x 43.1
