nathe-vink/earmilk/fab/out/dxf/gable-layer-04.dxf

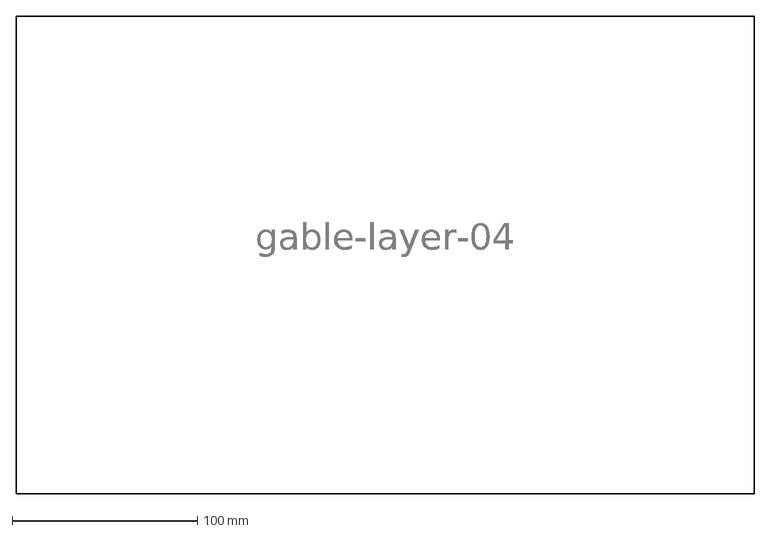
[picture p212: CAD file, 2026-10-09]
fab/out/dxf/gable-layer-04.dxf
gable-layer-04
