nathe-vink/earmilk/fab/out/step/side-right.step

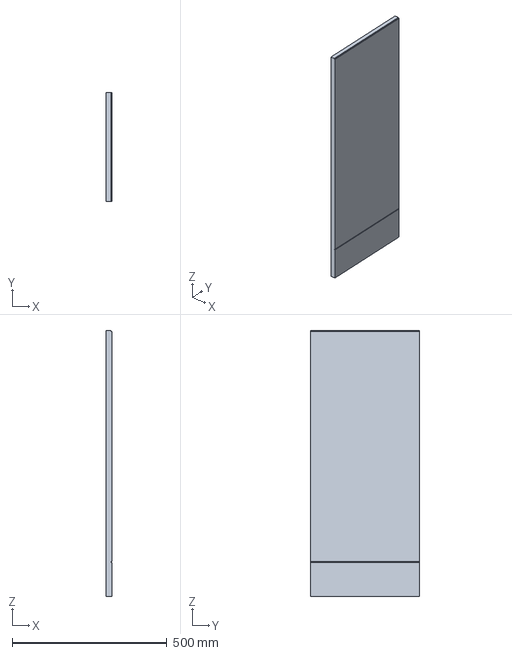
[picture p213: CAD file, 2026-10-09]
fab/out/step/side-right.step
18.0 x 354.0 x 860.0 mm
