nathe-vink/earmilk/fab/out/stl/connector-test-bay.stl

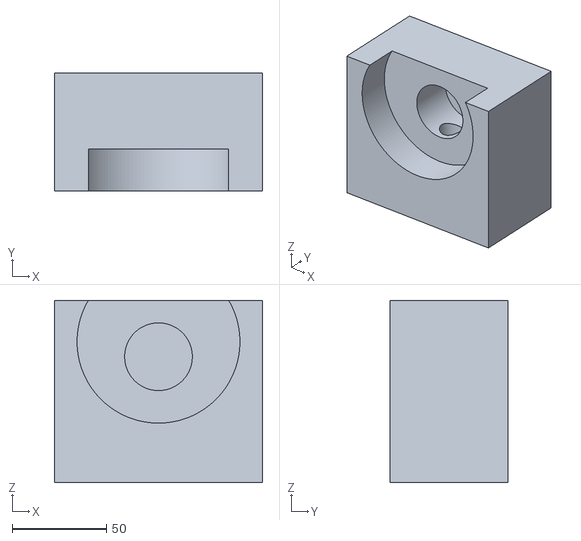
[picture p214: CAD file, 2026-10-09]
fab/out/stl/connector-test-bay.stl
110.6 x 62.7 x 97.0
