nathe-vink/earmilk/fab/out/stl/gable-print/gable-print-front-left.stl

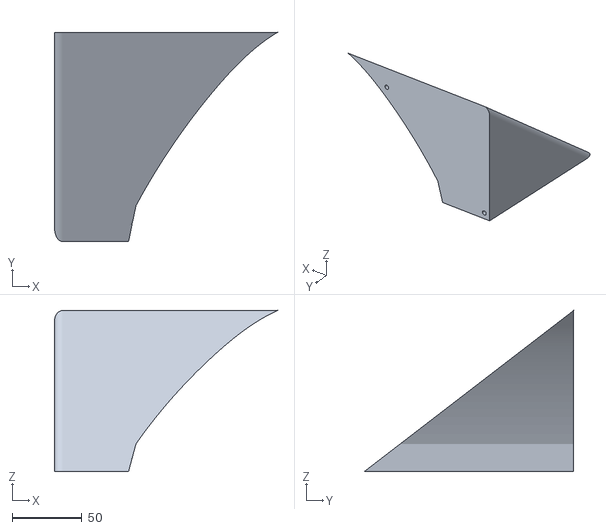
[picture p215: CAD file, 2026-10-09]
fab/out/stl/gable-print/gable-print-front-left.stl
159.8 x 150.0 x 115.4
