nathe-vink/earmilk/spinoffs/barkhorn/out/dxf/nest-baltic-birch-18-1.dxf

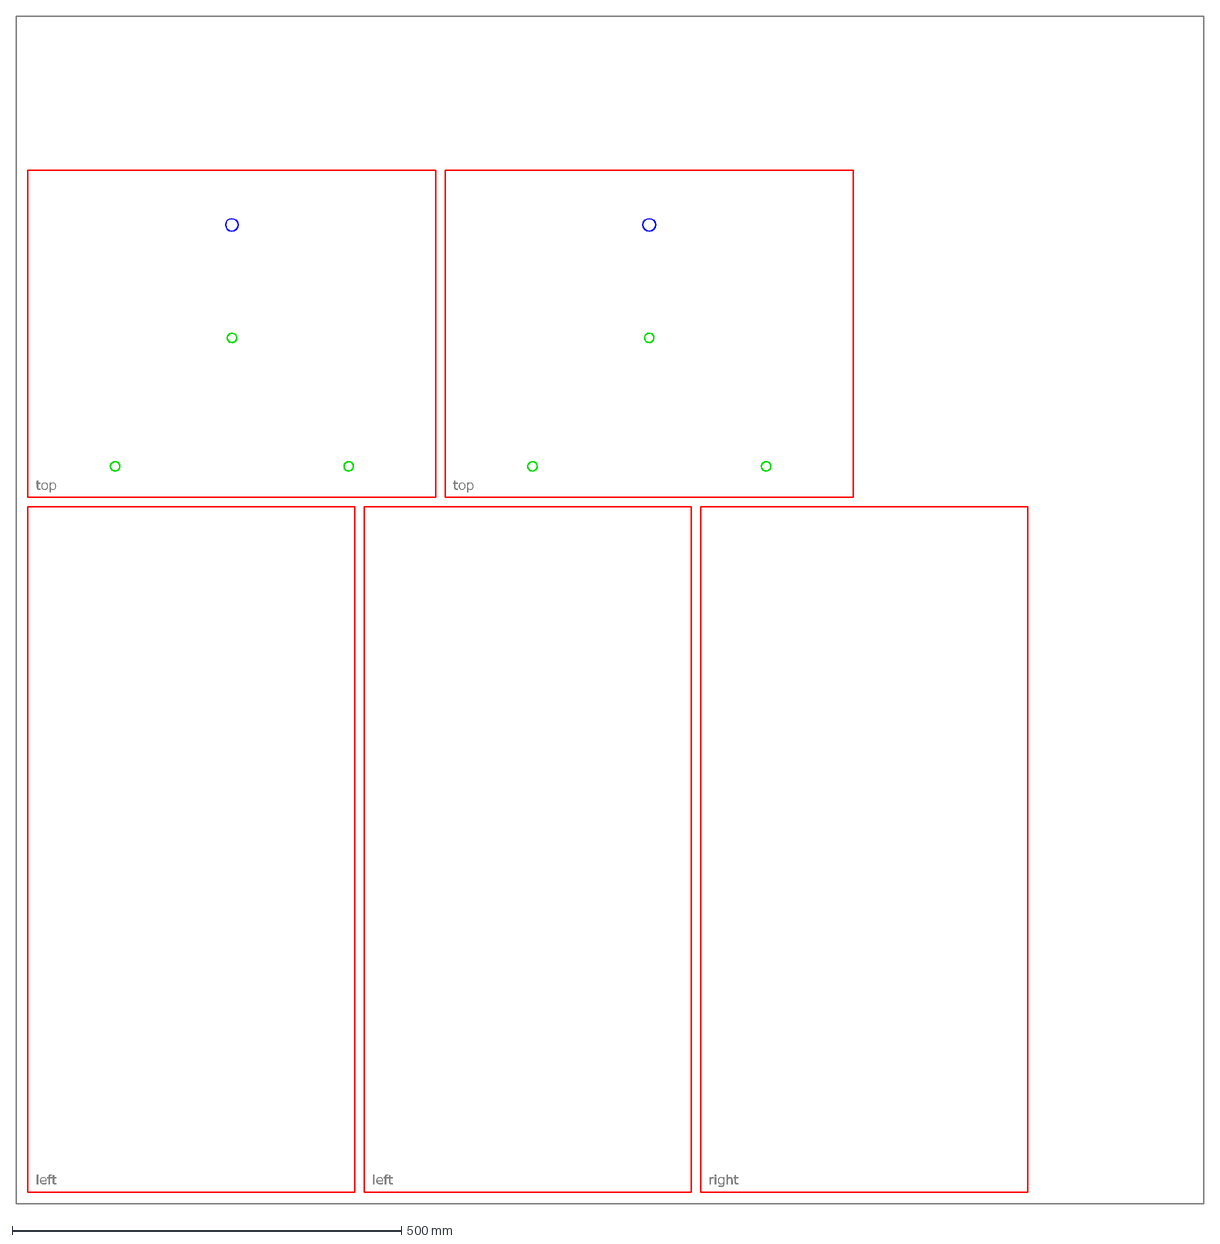
[picture p216: CAD file, 2026-10-11]
spinoffs/barkhorn/out/dxf/nest-baltic-birch-18-1.dxf
left
right
top
