nathe-vink/earmilk/spinoffs/earnest/out/step/valve-base.step

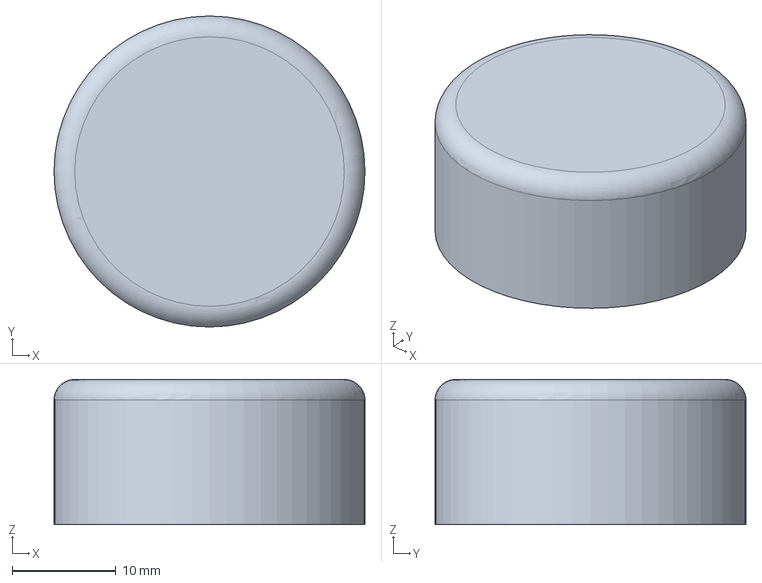
[picture p217: CAD file, 2026-10-09]
spinoffs/earnest/out/step/valve-base.step
30.0 x 30.0 x 14.0 mm
