nathe-vink/earmilk/spinoffs/earnest/out/stl/crate-24.stl

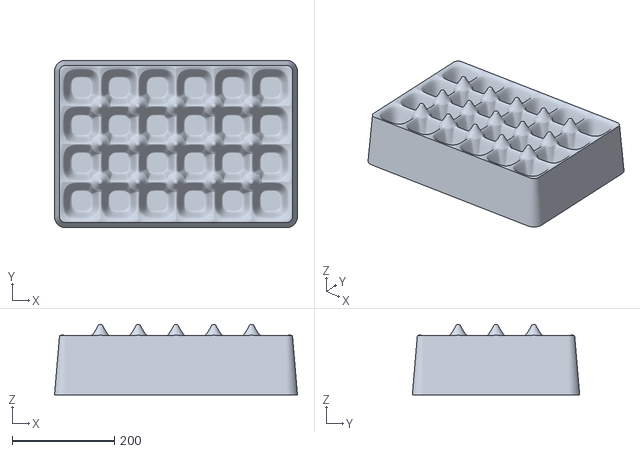
[picture p218: CAD file, 2026-10-09]
spinoffs/earnest/out/stl/crate-24.stl
475.6 x 327.6 x 138.0
