nathe-vink/earmilk/spinoffs/earwig/out/step/case-base.step

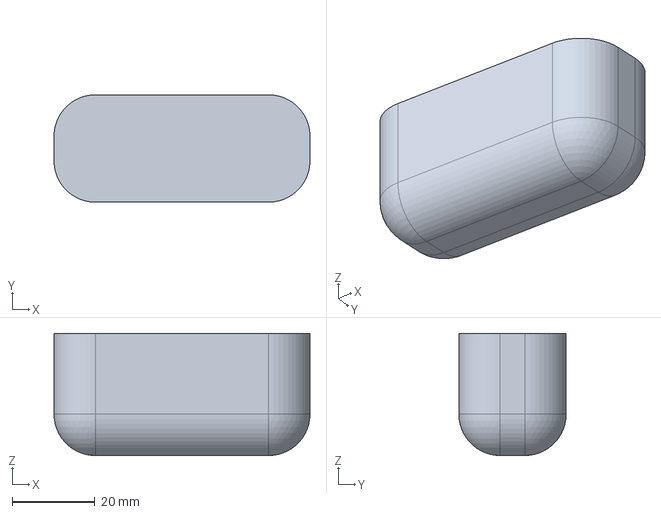
[picture p219: CAD file, 2026-10-06]
spinoffs/earwig/out/step/case-base.step
62.0 x 26.0 x 29.6 mm
