nathe-vink/earmilk/spinoffs/earworm/out/step/bud-shell.step

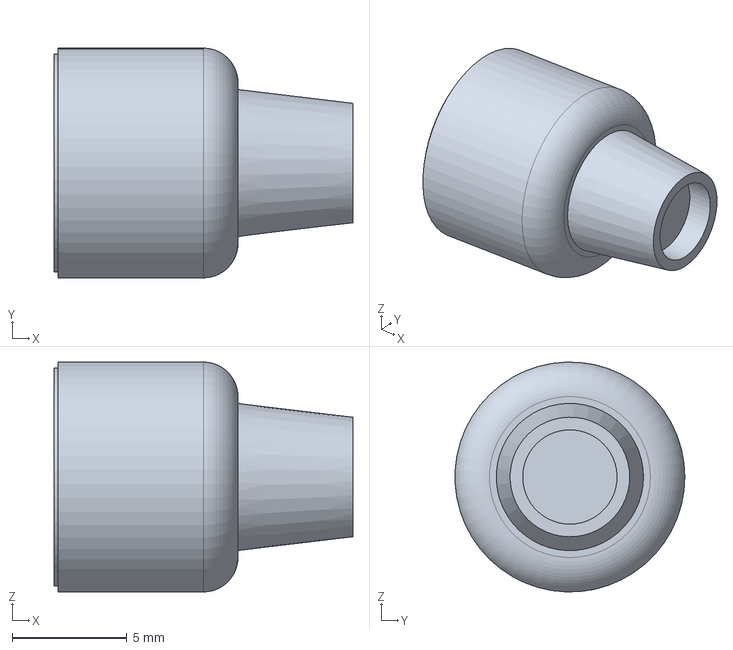
[picture p220: CAD file, 2026-10-05]
spinoffs/earworm/out/step/bud-shell.step
13.0 x 9.99 x 10.00 mm
