nathe-vink/earmilk/studio/fabkit/example/out/dxf/nest-baltic-birch-18-1.dxf

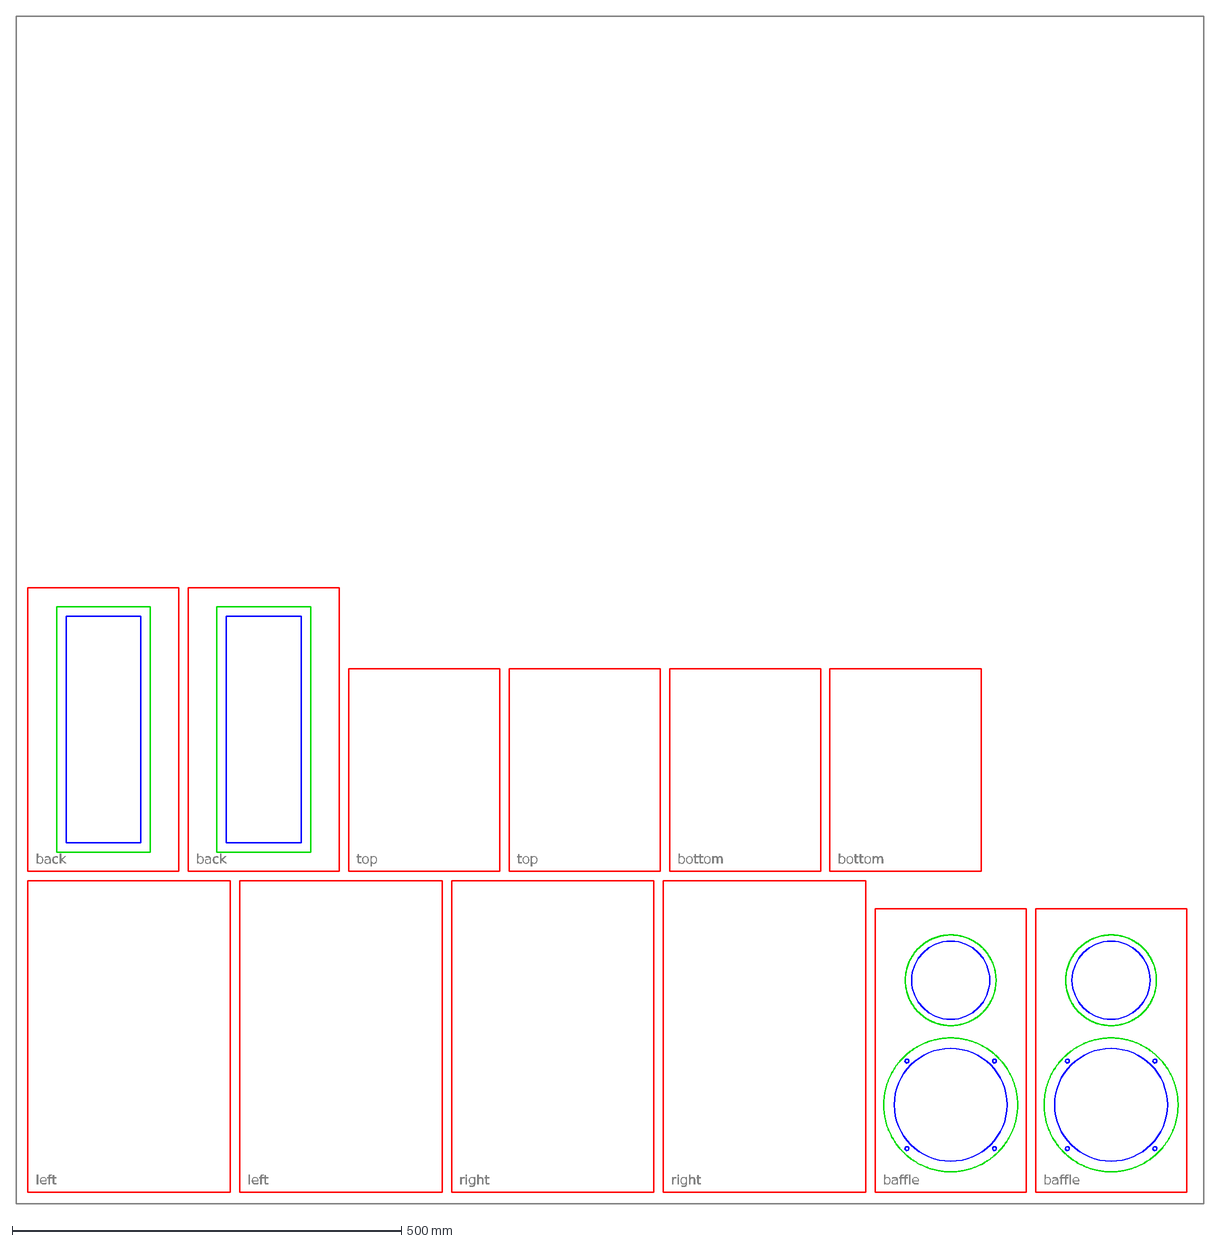
[picture p221: CAD file, 2026-10-11]
studio/fabkit/example/out/dxf/nest-baltic-birch-18-1.dxf
left
right
baffle
back
top
bottom
