nathe-vink/earmilk/fab/out-bookshelf/dxf/sheet-1.dxf

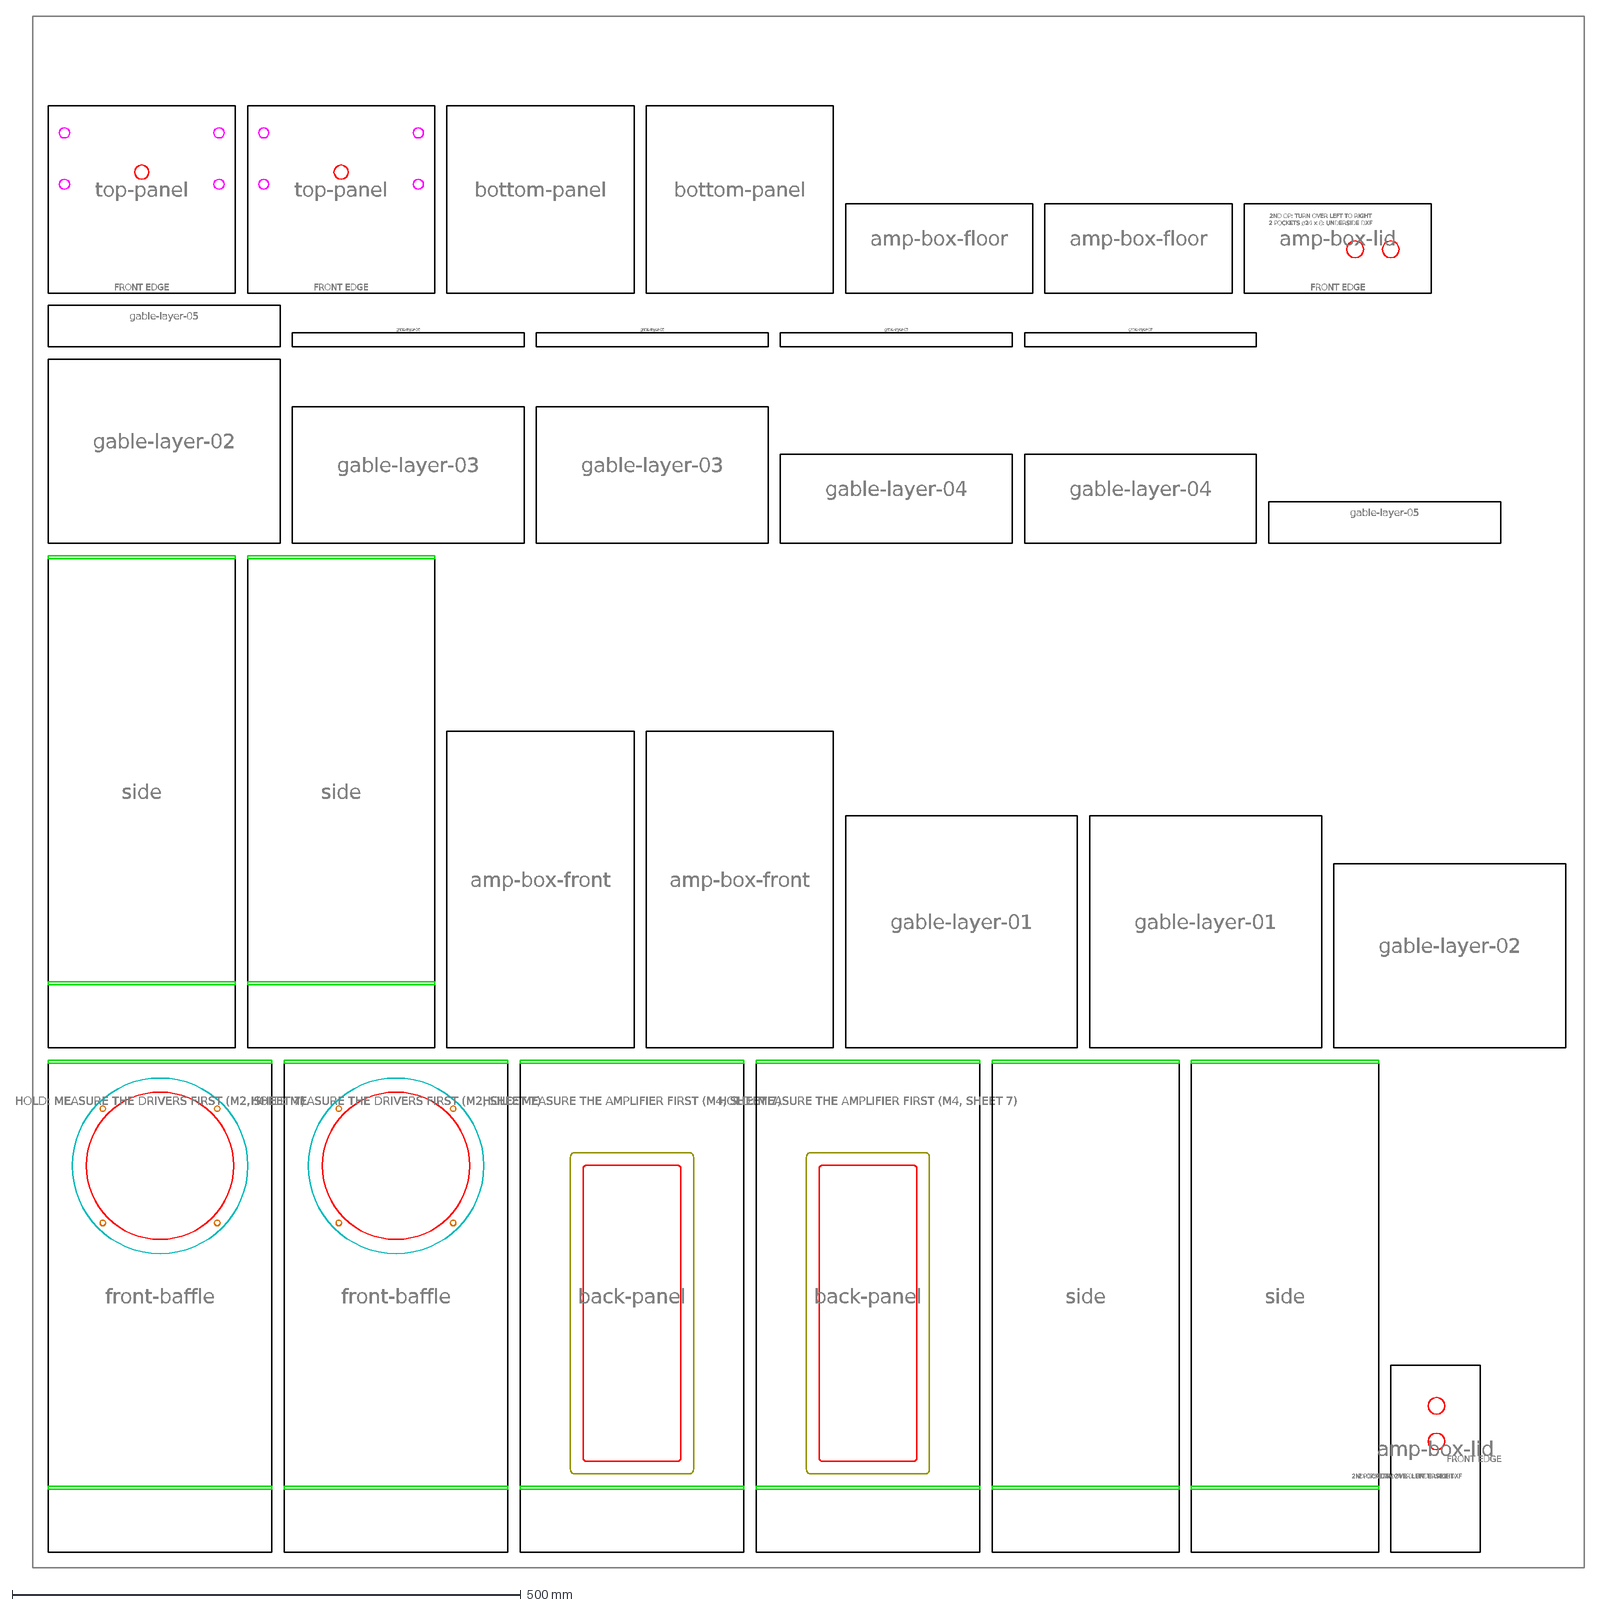
[picture p222: CAD file, 2026-10-09]
fab/out-bookshelf/dxf/sheet-1.dxf
HOLD: MEASURE THE DRIVERS FIRST (M2, SHEET 7)
front-baffle
HOLD: MEASURE THE AMPLIFIER FIRST (M4, SHEET 7)
back-panel
side
amp-box-front
gable-layer-01
gable-layer-02
gable-layer-03
gable-layer-04
gable-layer-05
gable-layer-06
gable-layer-07
FRONT EDGE
top-panel
bottom-panel
amp-box-floor
2ND OP: TURN OVER LEFT TO RIGHT
2 POCKETS ø24 x 8: UNDERSIDE DXF
amp-box-lid
