nathe-vink/earmilk/fab/out/dxf/side.dxf

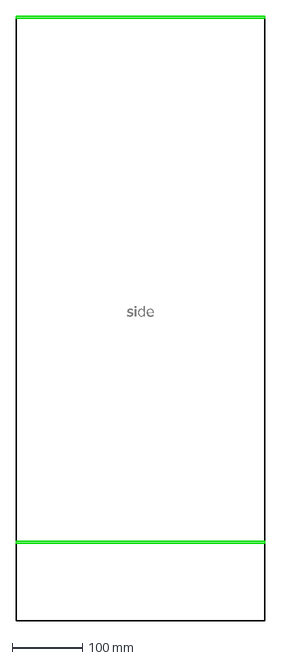
[picture p223: CAD file, 2026-10-09]
fab/out/dxf/side.dxf
side
