nathe-vink/earmilk/fab/out/step/amp-box-lid.step

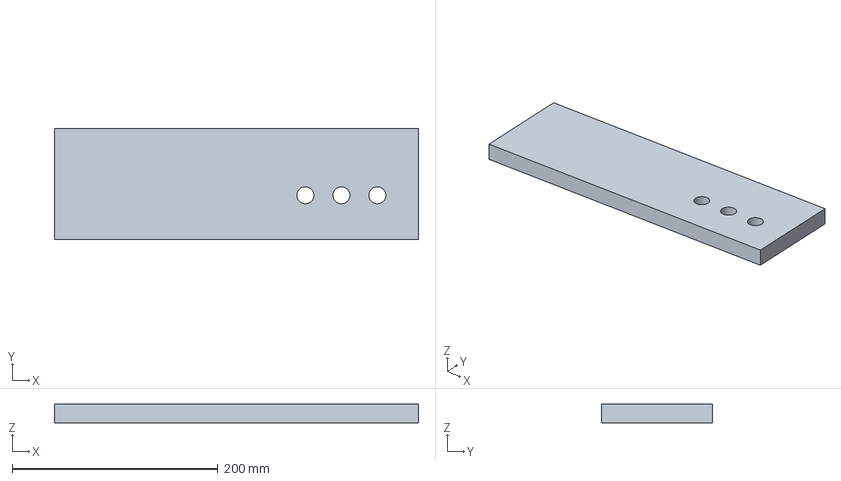
[picture p224: CAD file, 2026-10-09]
fab/out/step/amp-box-lid.step
354.0 x 108.0 x 18.0 mm
