nathe-vink/earmilk/fab/out/stl/gable-print/gable-print-rear-right.stl

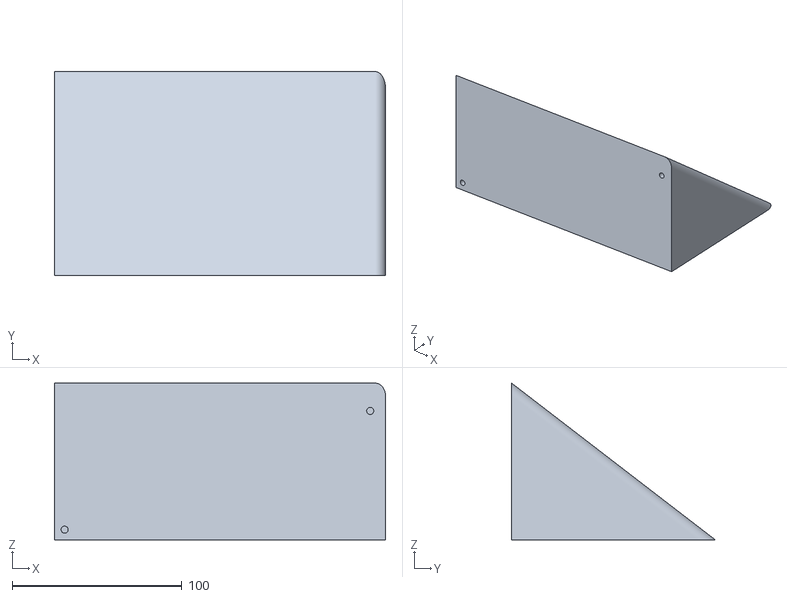
[picture p225: CAD file, 2026-10-09]
fab/out/stl/gable-print/gable-print-rear-right.stl
195.0 x 120.0 x 92.3
