nathe-vink/earmilk/fab/out/stl/trim-ring-woofer.stl

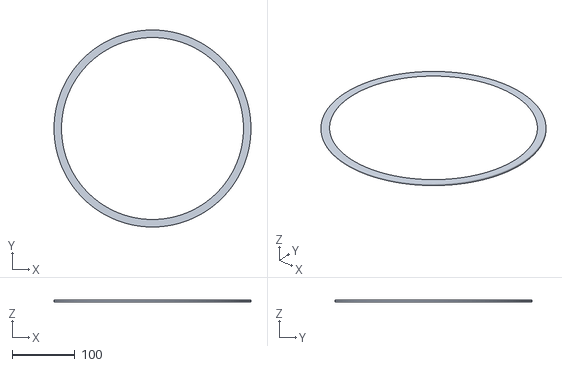
[picture p226: CAD file, 2026-10-09]
fab/out/stl/trim-ring-woofer.stl
314.0 x 313.9 x 3.00
