nathe-vink/earmilk/spinoffs/barkhorn/out/dxf/nest-spotted-gum-ply-6-strip-grille-1.dxf

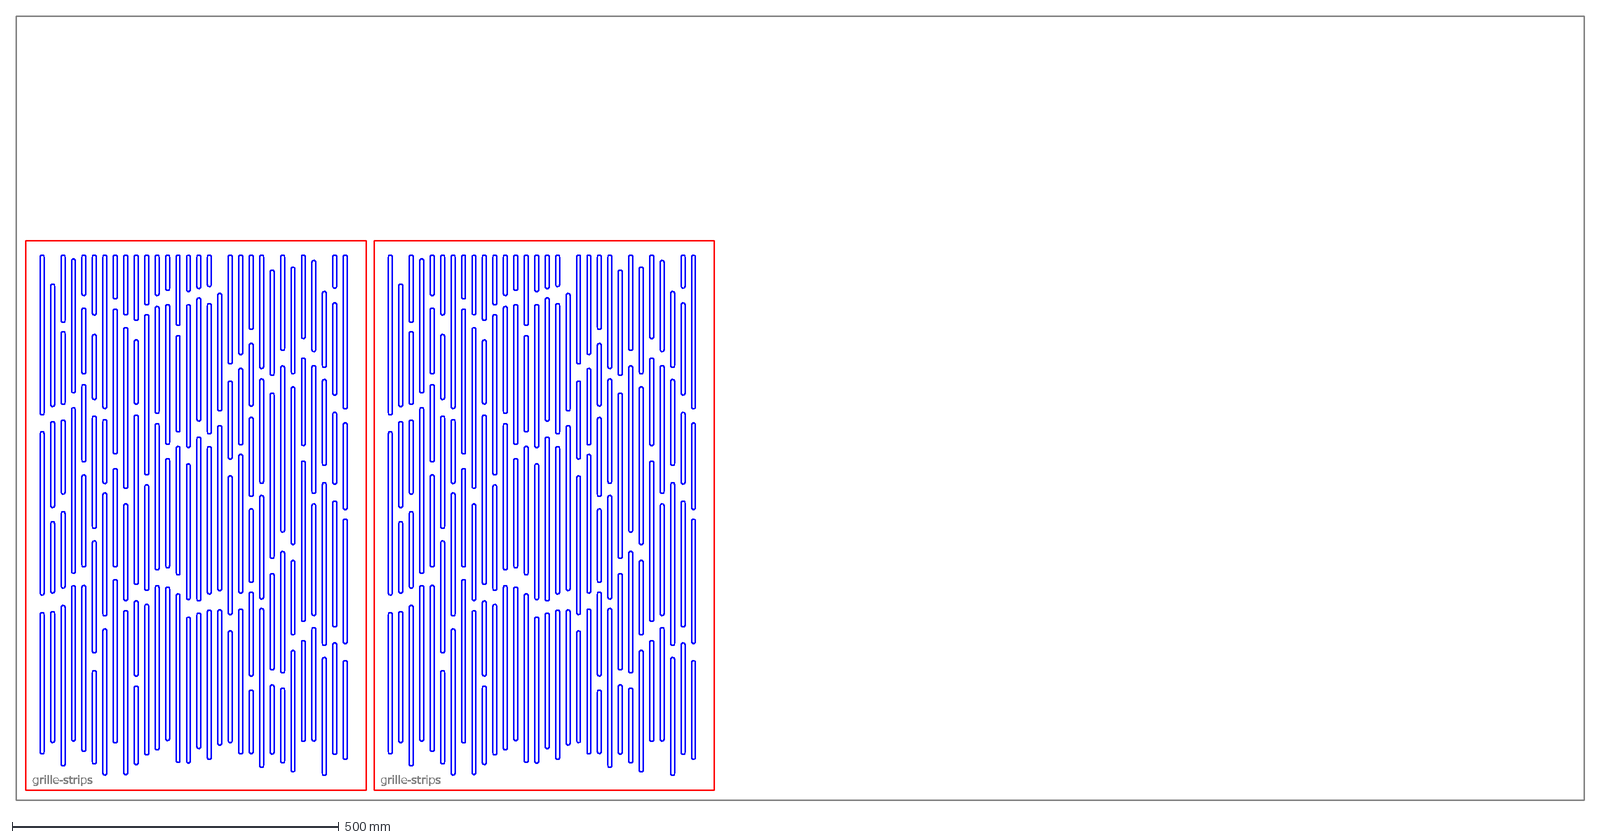
[picture p227: CAD file, 2026-10-11]
spinoffs/barkhorn/out/dxf/nest-spotted-gum-ply-6-strip-grille-1.dxf
grille-strips
