nathe-vink/earmilk/spinoffs/earnest/out/step/feet-6.step

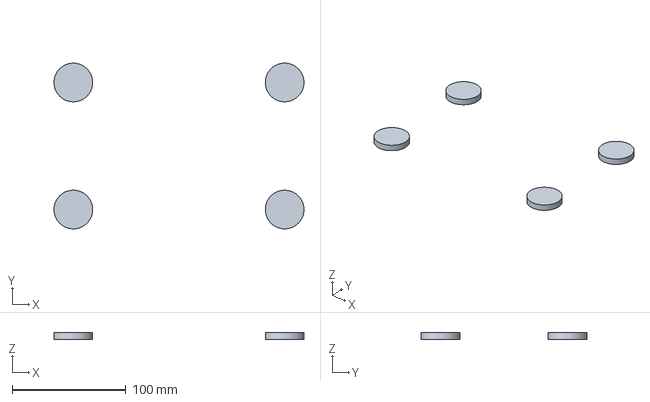
[picture p228: CAD file, 2026-10-09]
spinoffs/earnest/out/step/feet-6.step
219.6 x 145.6 x 6.00 mm
