nathe-vink/earmilk/spinoffs/earwig/out/step/collar-l.step

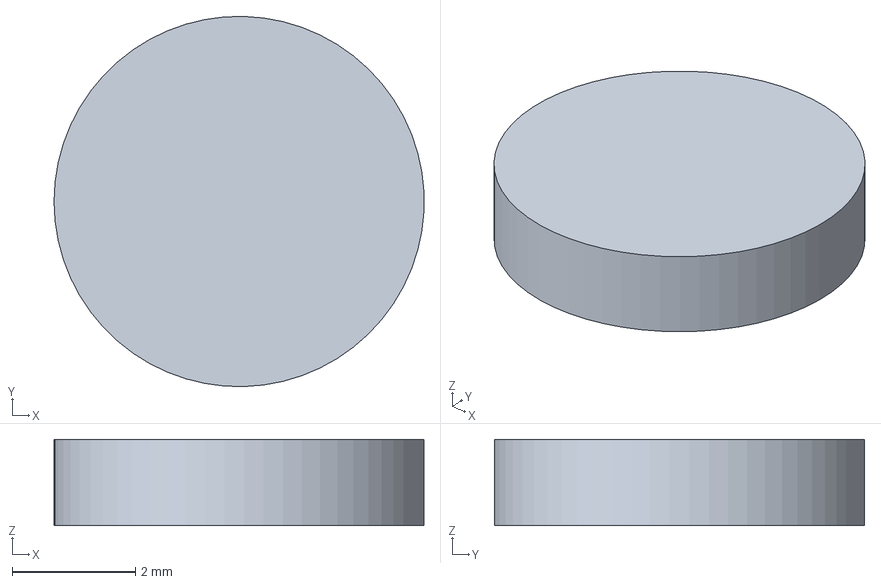
[picture p229: CAD file, 2026-10-06]
spinoffs/earwig/out/step/collar-l.step
6.00 x 6.00 x 1.40 mm
