nathe-vink/earmilk/spinoffs/earworm/out/step/print-cap.step

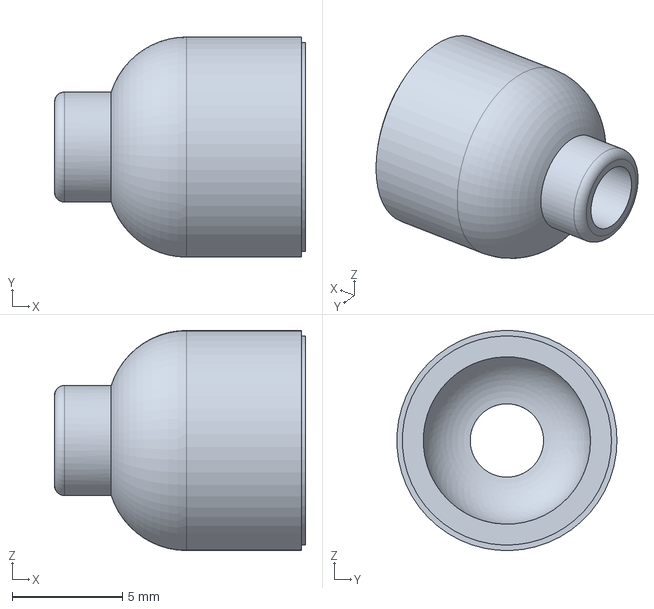
[picture p230: CAD file, 2026-10-05]
spinoffs/earworm/out/step/print-cap.step
11.4 x 9.99 x 10.00 mm
