nathe-vink/earmilk/studio/fabkit/example/out/dxf/right.dxf

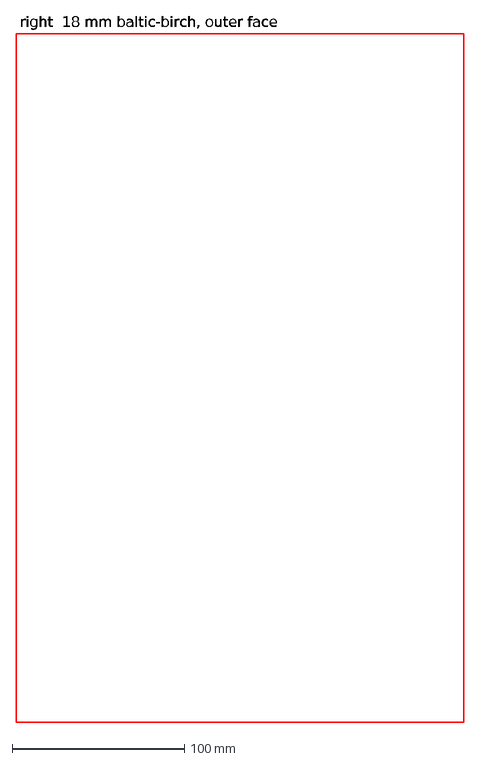
[picture p231: CAD file, 2026-10-11]
studio/fabkit/example/out/dxf/right.dxf
right 18 mm baltic-birch, outer face
