nathe-vink/earmilk/fab/out-bookshelf/dxf/gable-layer-03.dxf

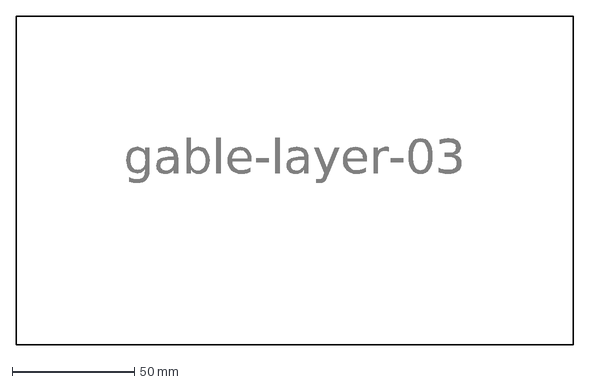
[picture p232: CAD file, 2026-10-09]
fab/out-bookshelf/dxf/gable-layer-03.dxf
gable-layer-03
