nathe-vink/earmilk/fab/out/dxf/amp-box-lid-underside.dxf

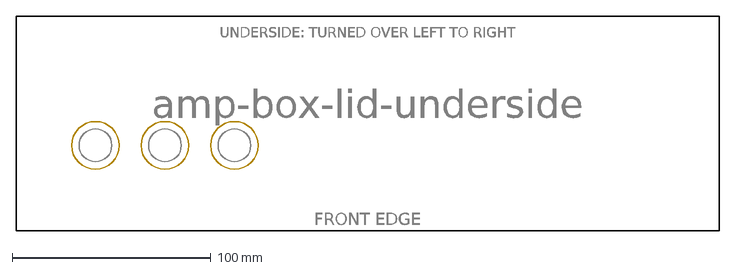
[picture p234: CAD file, 2026-10-09]
fab/out/dxf/amp-box-lid-underside.dxf
FRONT EDGE
UNDERSIDE: TURNED OVER LEFT TO RIGHT
amp-box-lid-underside
