nathe-vink/earmilk/fab/out/step/mid-shelf.step

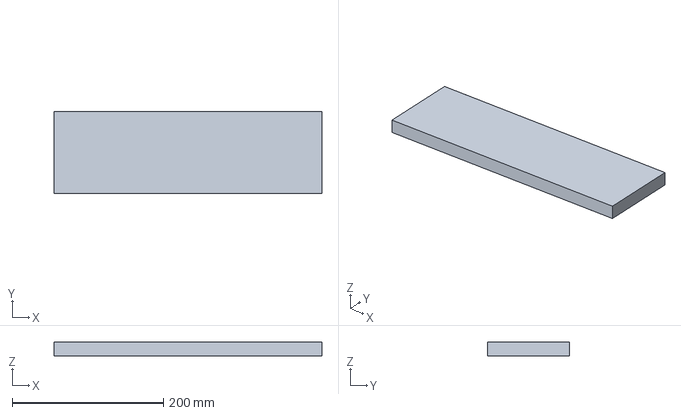
[picture p235: CAD file, 2026-10-09]
fab/out/step/mid-shelf.step
354.0 x 108.0 x 18.0 mm
