nathe-vink/earmilk/fab/out/stl/trim-ring-mid.stl

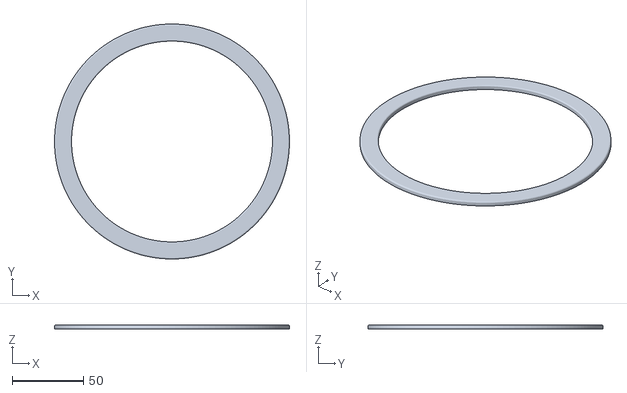
[picture p236: CAD file, 2026-10-09]
fab/out/stl/trim-ring-mid.stl
165.0 x 164.9 x 3.00
