nathe-vink/earmilk/spinoffs/barkhorn/out/dxf/top.dxf

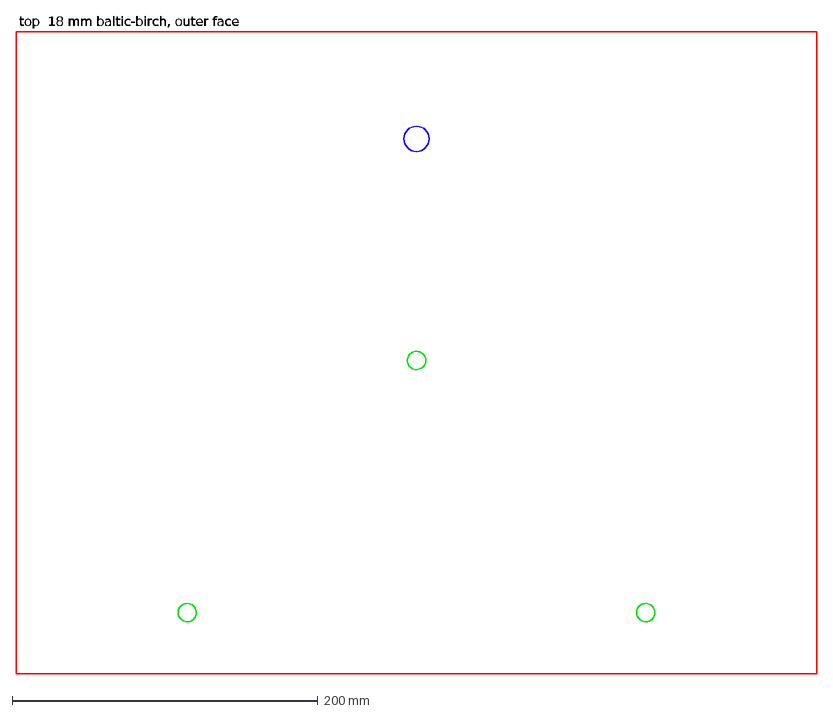
[picture p237: CAD file, 2026-10-11]
spinoffs/barkhorn/out/dxf/top.dxf
top 18 mm baltic-birch, outer face
