nathe-vink/earmilk/spinoffs/earnest/out/step/valve-anode.step

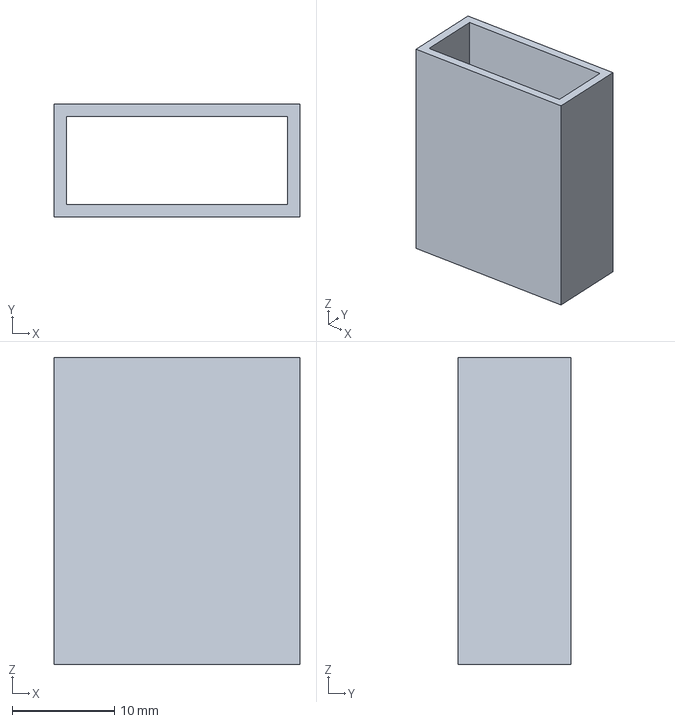
[picture p238: CAD file, 2026-10-09]
spinoffs/earnest/out/step/valve-anode.step
24.0 x 11.0 x 30.0 mm
