nathe-vink/earmilk/spinoffs/earwig/out/step/sensor-r.step

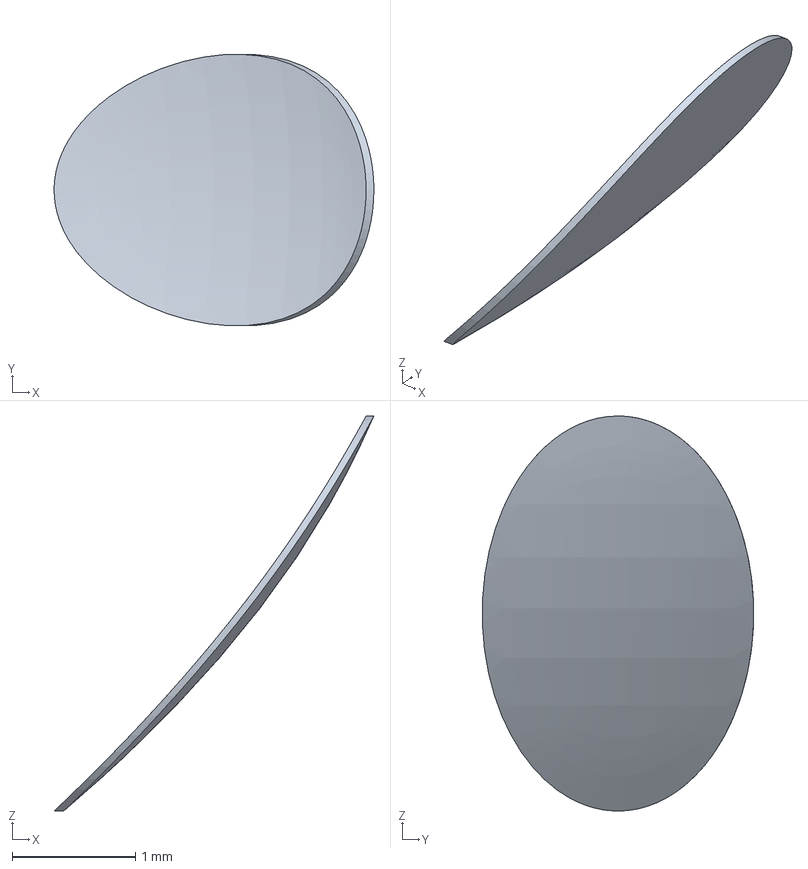
[picture p239: CAD file, 2026-10-06]
spinoffs/earwig/out/step/sensor-r.step
2.59 x 2.20 x 3.20 mm
