nathe-vink/earmilk/spinoffs/earworm/out/step/bud-tip.step

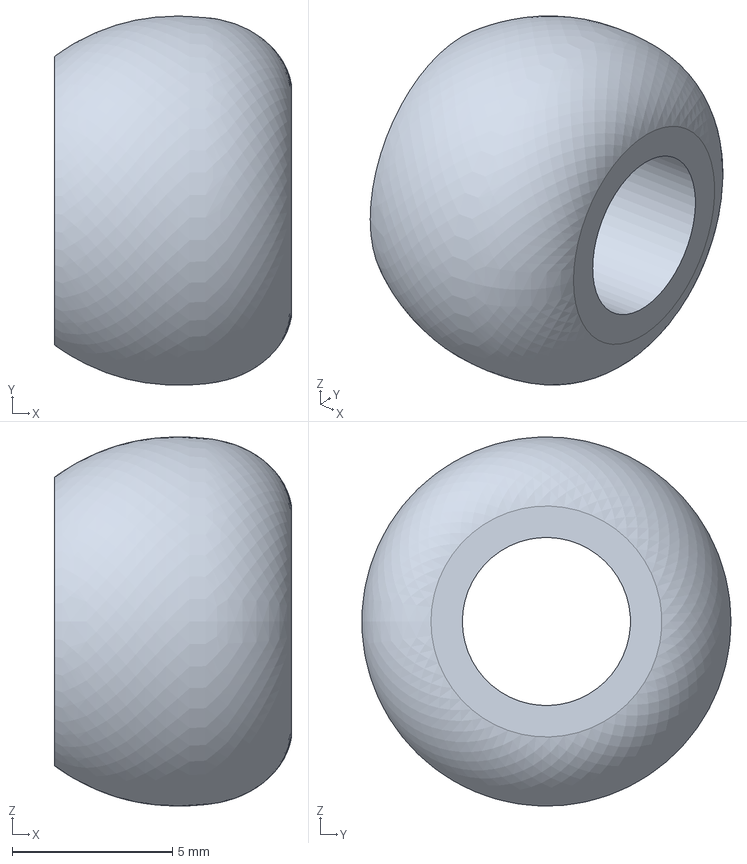
[picture p240: CAD file, 2026-10-05]
spinoffs/earworm/out/step/bud-tip.step
7.40 x 11.5 x 11.5 mm
