nathe-vink/earmilk/studio/fabkit/example/out/dxf/bottom.dxf

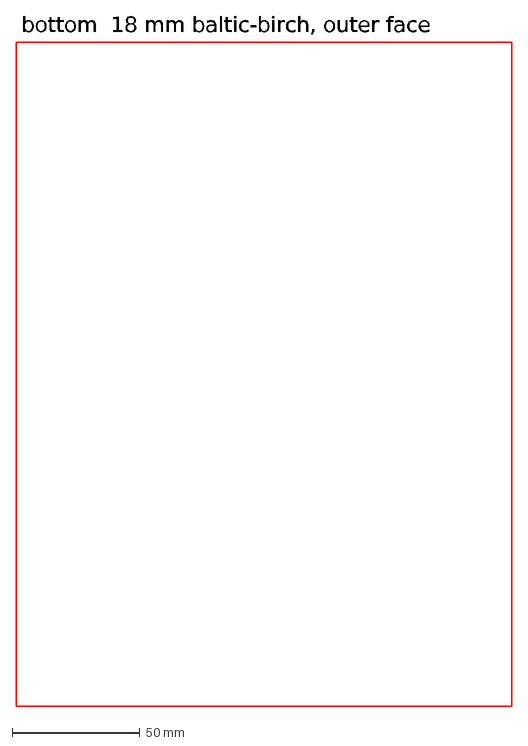
[picture p241: CAD file, 2026-10-11]
studio/fabkit/example/out/dxf/bottom.dxf
bottom 18 mm baltic-birch, outer face
