nathe-vink/earmilk/fab/out-bookshelf/dxf/gable-layer-01.dxf

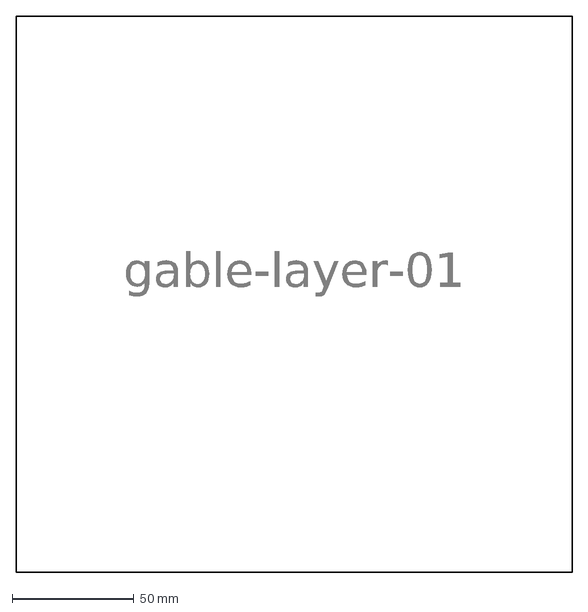
[picture p242: CAD file, 2026-10-09]
fab/out-bookshelf/dxf/gable-layer-01.dxf
gable-layer-01
