nathe-vink/earmilk/fab/out/dxf/gable-layer-05.dxf

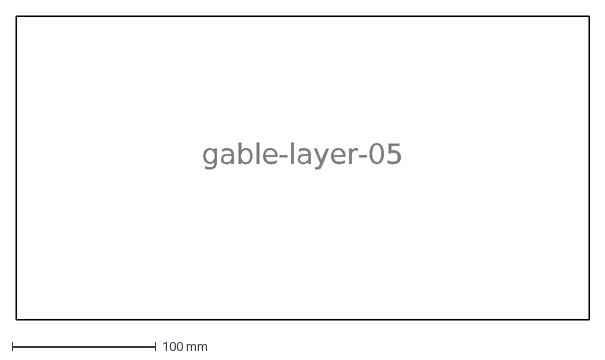
[picture p244: CAD file, 2026-10-09]
fab/out/dxf/gable-layer-05.dxf
gable-layer-05
