nathe-vink/earmilk/fab/out/step/port-tube.step

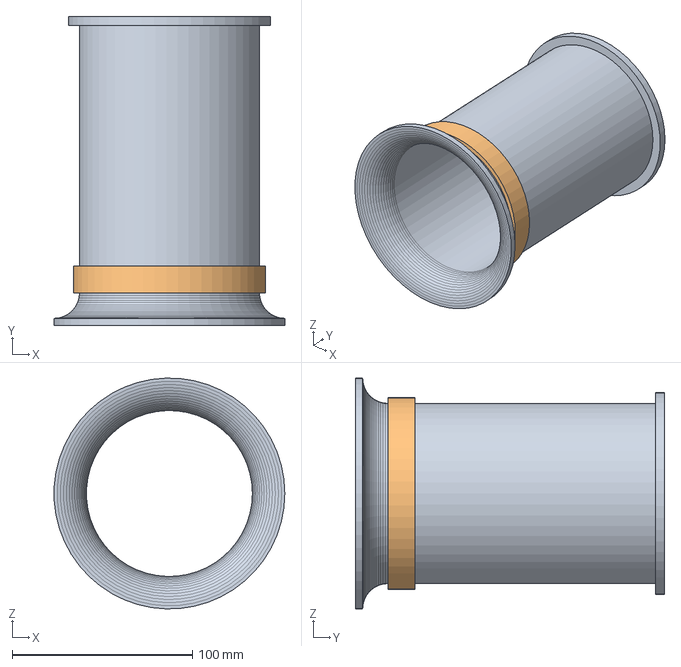
[picture p245: CAD file, 2026-10-09]
fab/out/step/port-tube.step
127.9 x 171.3 x 127.9 mm
