nathe-vink/earmilk/spinoffs/barkhorn/out/dxf/back.dxf

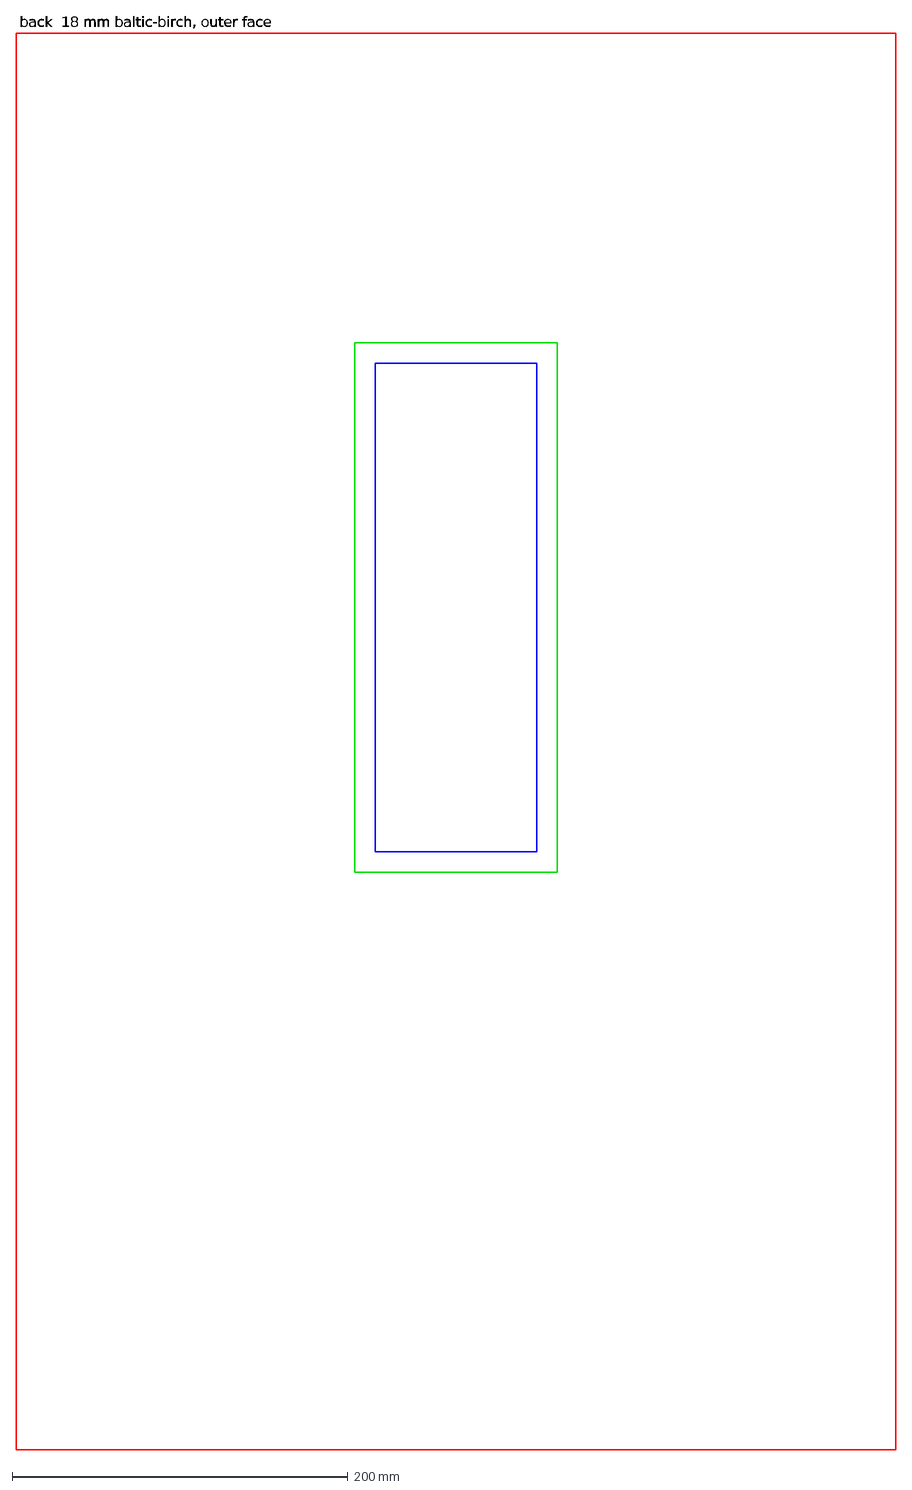
[picture p246: CAD file, 2026-10-11]
spinoffs/barkhorn/out/dxf/back.dxf
back 18 mm baltic-birch, outer face
