nathe-vink/earmilk/spinoffs/earnest/out/step/valve-mica.step

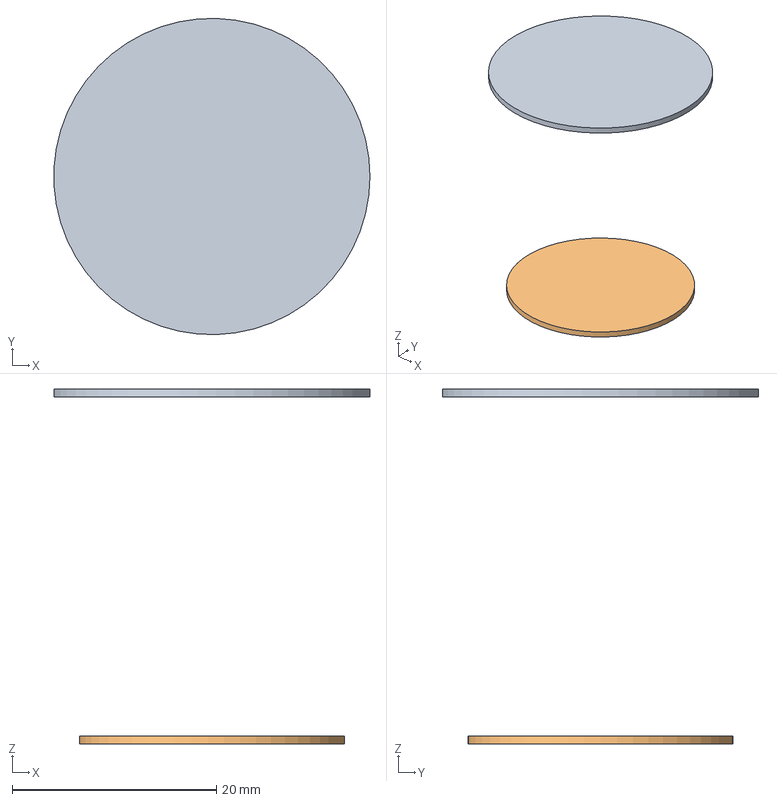
[picture p247: CAD file, 2026-10-09]
spinoffs/earnest/out/step/valve-mica.step
31.0 x 31.0 x 34.8 mm
