nathe-vink/earmilk/spinoffs/earwig/out/step/case-lid.step

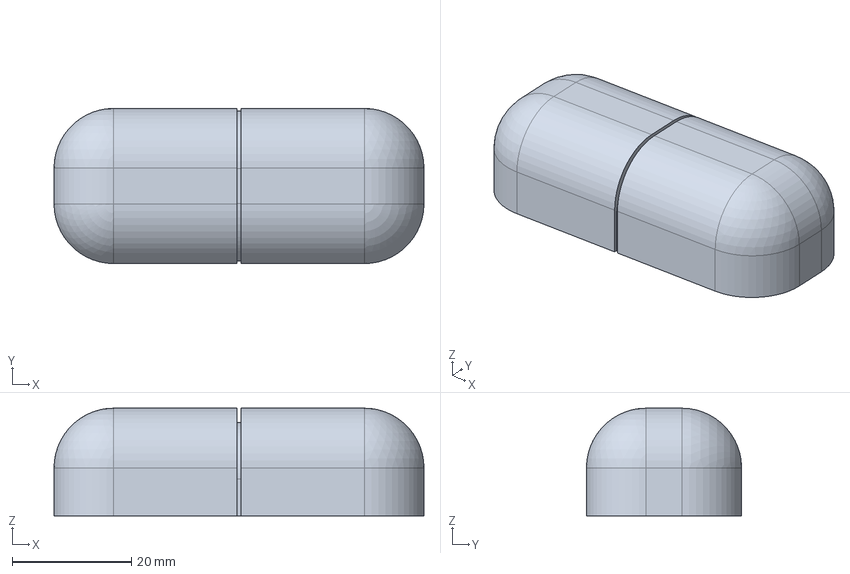
[picture p248: CAD file, 2026-10-06]
spinoffs/earwig/out/step/case-lid.step
62.0 x 26.0 x 18.0 mm
