nathe-vink/earmilk/spinoffs/earworm/out/step/bud-cap.step

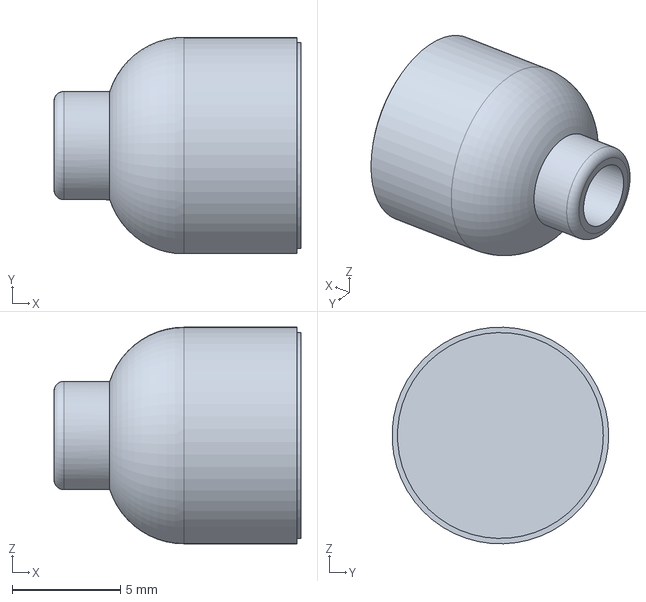
[picture p249: CAD file, 2026-10-05]
spinoffs/earworm/out/step/bud-cap.step
11.4 x 9.99 x 10.00 mm
