nathe-vink/earmilk/studio/fabkit/example/out/dxf/back.dxf

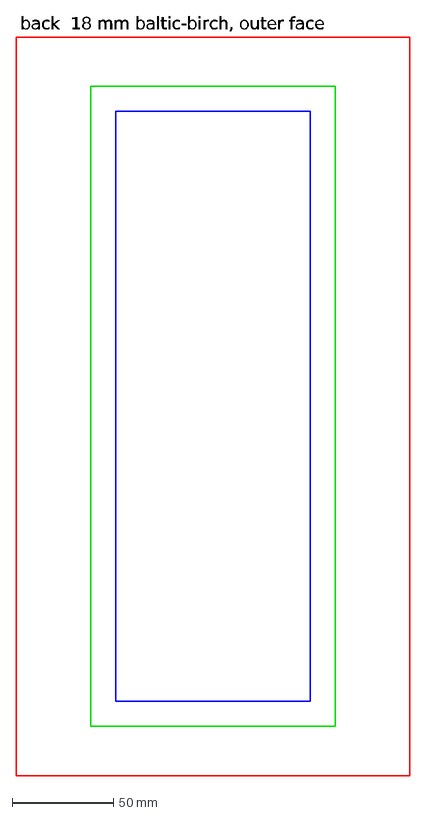
[picture p250: CAD file, 2026-10-11]
studio/fabkit/example/out/dxf/back.dxf
back 18 mm baltic-birch, outer face
