nathe-vink/earmilk/fab/out-bookshelf/dxf/gable-layer-04.dxf

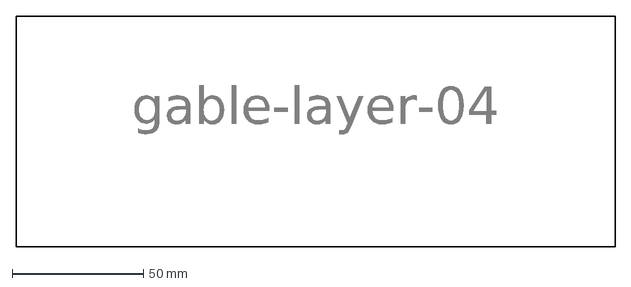
[picture p251: CAD file, 2026-10-09]
fab/out-bookshelf/dxf/gable-layer-04.dxf
gable-layer-04
