nathe-vink/earmilk/fab/out-bookshelf/step/amp-box-front.step

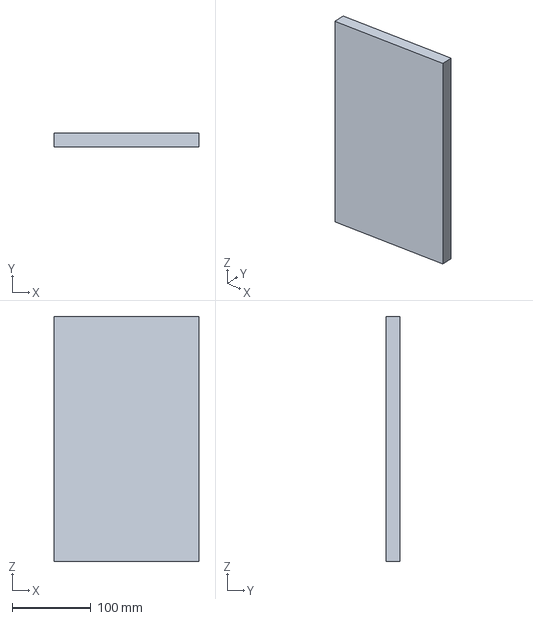
[picture p252: CAD file, 2026-10-09]
fab/out-bookshelf/step/amp-box-front.step
184.0 x 18.0 x 311.0 mm
