nathe-vink/earmilk/fab/out/dxf/gable-layer-01.dxf

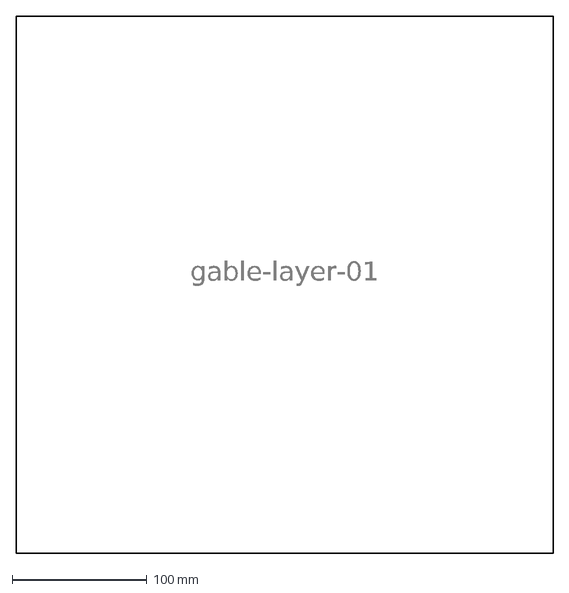
[picture p253: CAD file, 2026-10-09]
fab/out/dxf/gable-layer-01.dxf
gable-layer-01
