nathe-vink/earmilk/fab/out/step/port-tube-with-flange.step

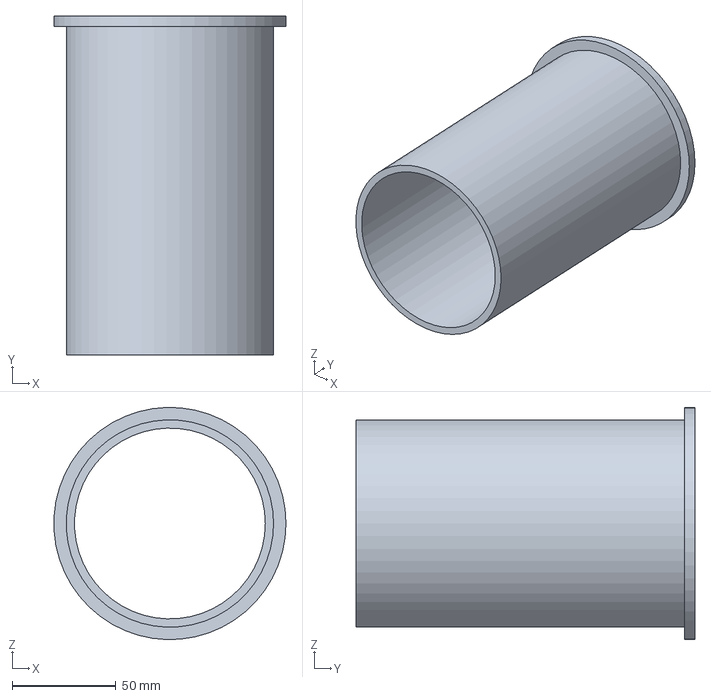
[picture p254: CAD file, 2026-10-09]
fab/out/step/port-tube-with-flange.step
111.9 x 163.3 x 111.9 mm
