nathe-vink/earmilk/spinoffs/barkhorn/out/dxf/woofer-ring-underside.dxf

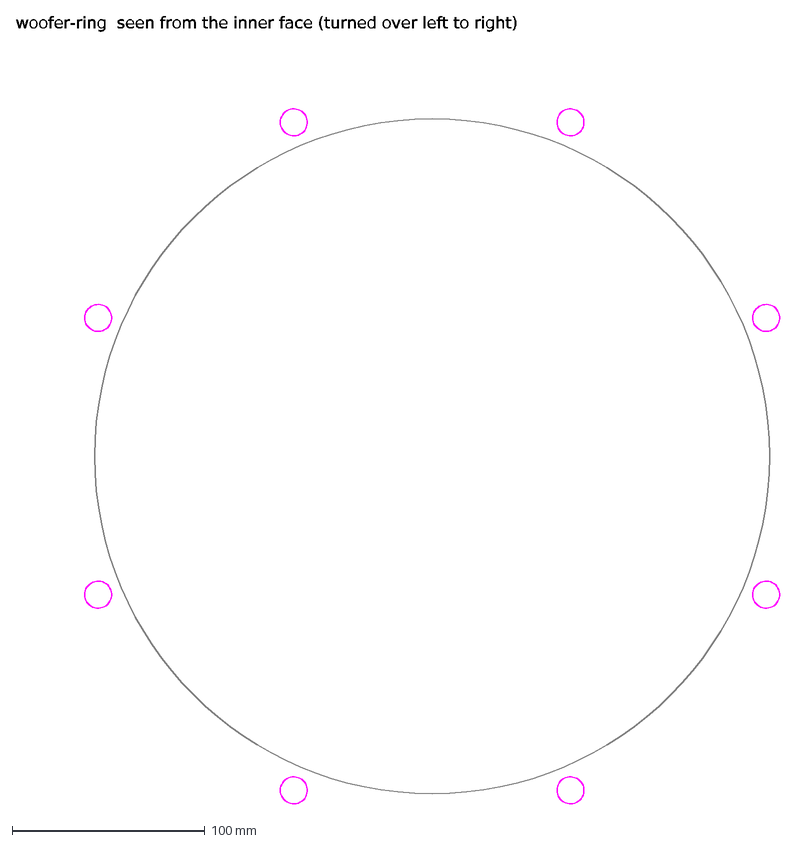
[picture p255: CAD file, 2026-10-11]
spinoffs/barkhorn/out/dxf/woofer-ring-underside.dxf
woofer-ring seen from the inner face (turned over left to right)
