nathe-vink/earmilk/spinoffs/earworm/out/step/plug-rings.step

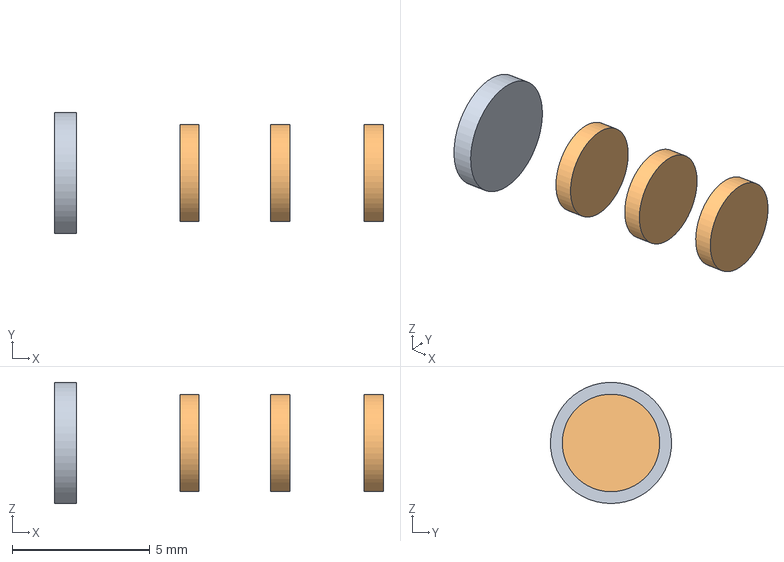
[picture p256: CAD file, 2026-10-05]
spinoffs/earworm/out/step/plug-rings.step
11.9 x 4.40 x 4.40 mm
