nathe-vink/earmilk/studio/fabkit/example/out/dxf/baffle.dxf

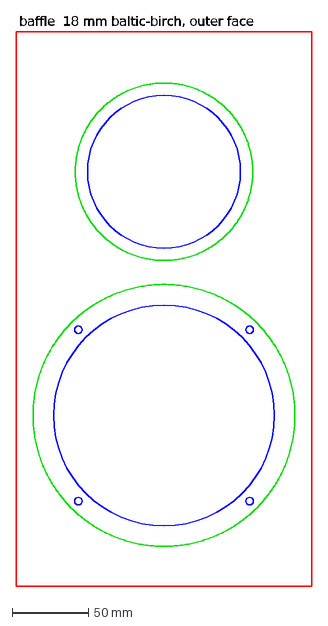
[picture p257: CAD file, 2026-10-11]
studio/fabkit/example/out/dxf/baffle.dxf
baffle 18 mm baltic-birch, outer face
