nathe-vink/earmilk/fab/out-bookshelf/dxf/gable-layer-07.dxf

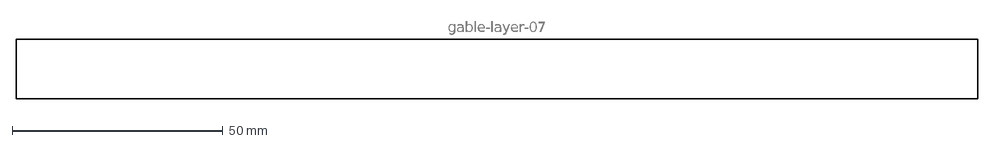
[picture p258: CAD file, 2026-10-09]
fab/out-bookshelf/dxf/gable-layer-07.dxf
gable-layer-07
