nathe-vink/earmilk/fab/out/dxf/sheet-3.dxf

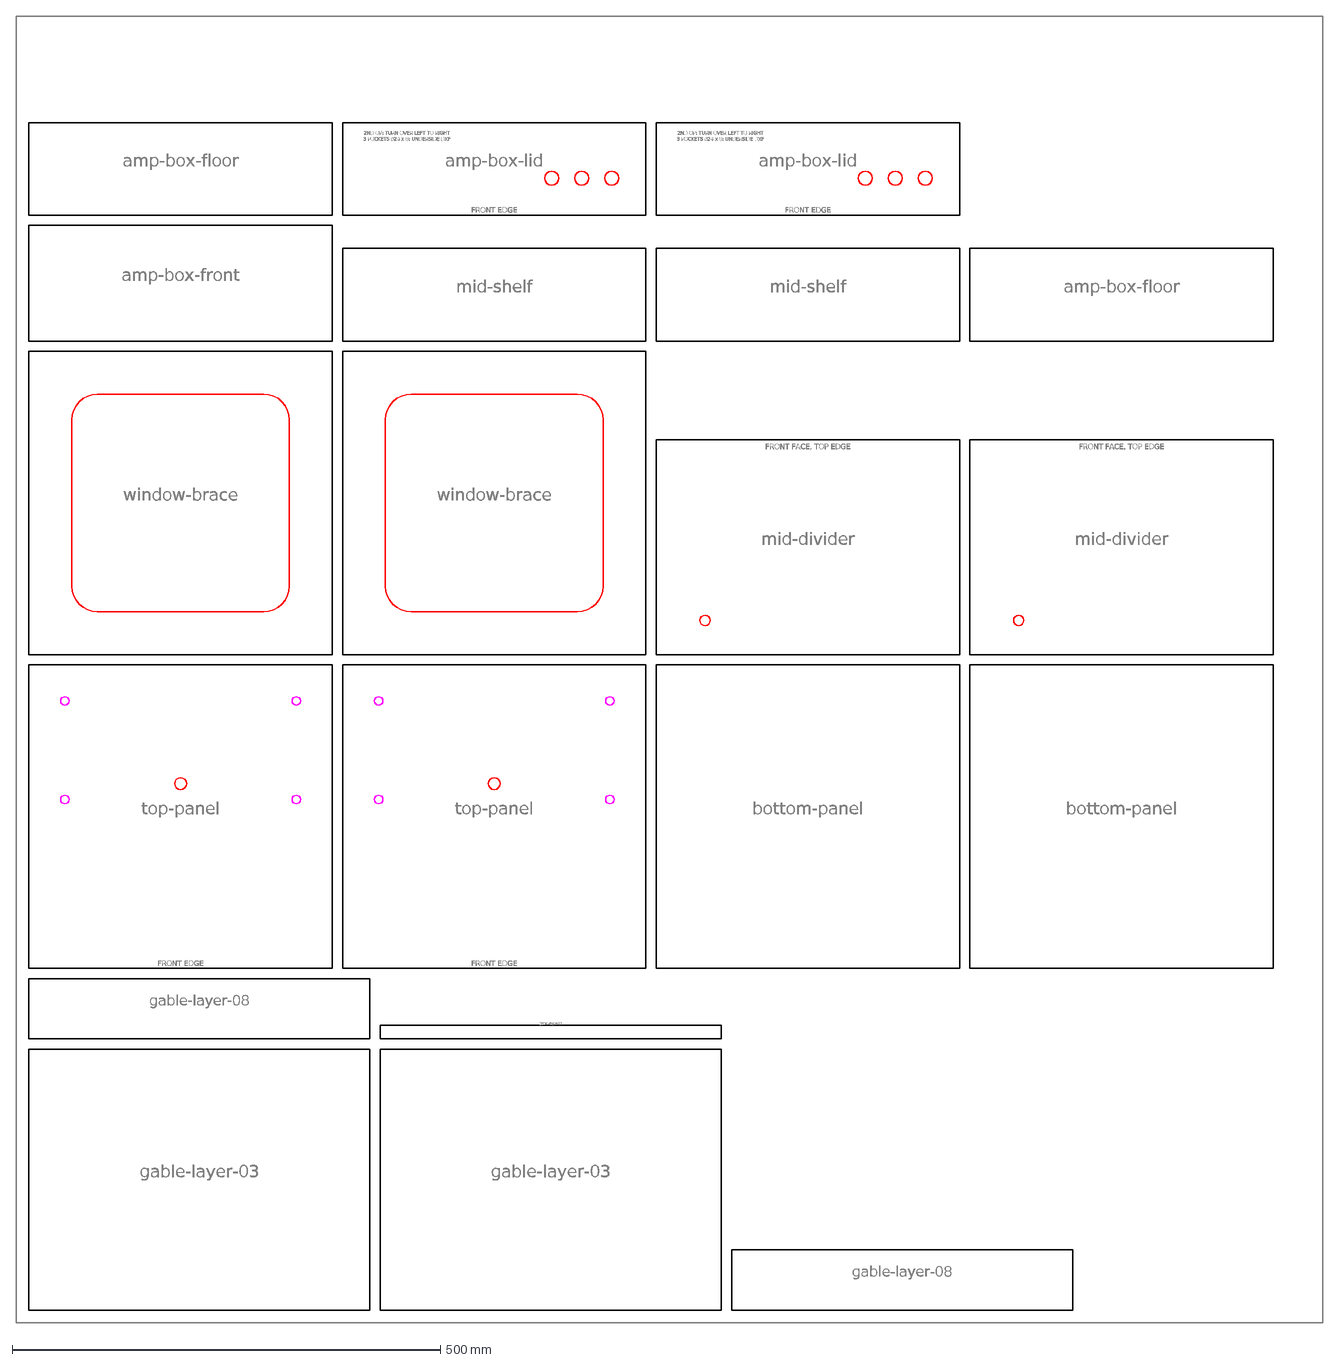
[picture p260: CAD file, 2026-10-09]
fab/out/dxf/sheet-3.dxf
gable-layer-03
gable-layer-08
gable-layer-11
FRONT EDGE
top-panel
bottom-panel
window-brace
FRONT FACE, TOP EDGE
mid-divider
amp-box-front
mid-shelf
amp-box-floor
2ND OP: TURN OVER LEFT TO RIGHT
3 POCKETS ø24 x 8: UNDERSIDE DXF
amp-box-lid
