nathe-vink/earmilk/fab/out/step/gable-block.step

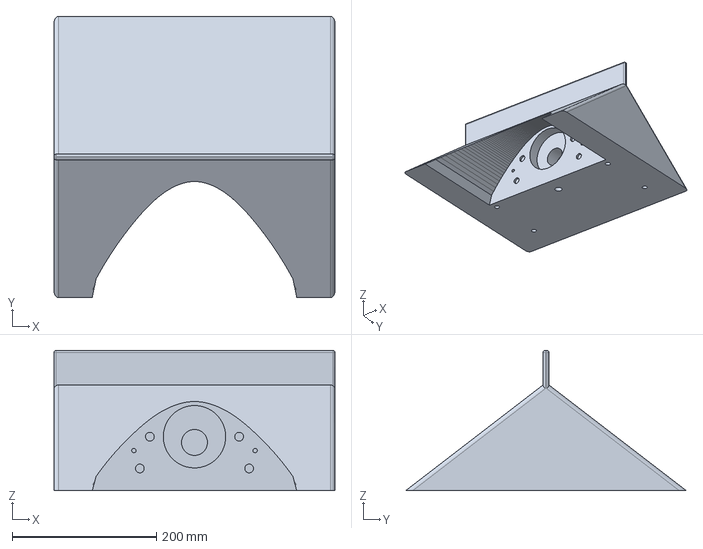
[picture p261: CAD file, 2026-10-09]
fab/out/step/gable-block.step
390.0 x 390.0 x 195.0 mm
