nathe-vink/earmilk/spinoffs/barkhorn/out/dxf/brace.dxf

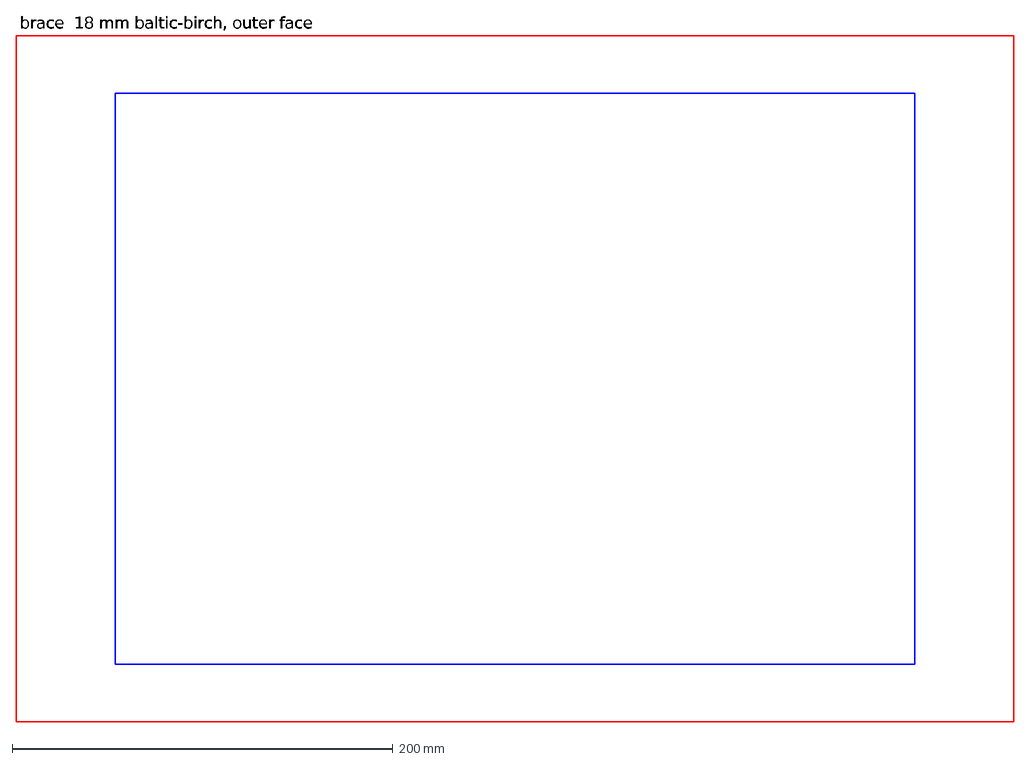
[picture p262: CAD file, 2026-10-11]
spinoffs/barkhorn/out/dxf/brace.dxf
brace 18 mm baltic-birch, outer face
