nathe-vink/earmilk/spinoffs/earnest/out/step/valve-heater.step

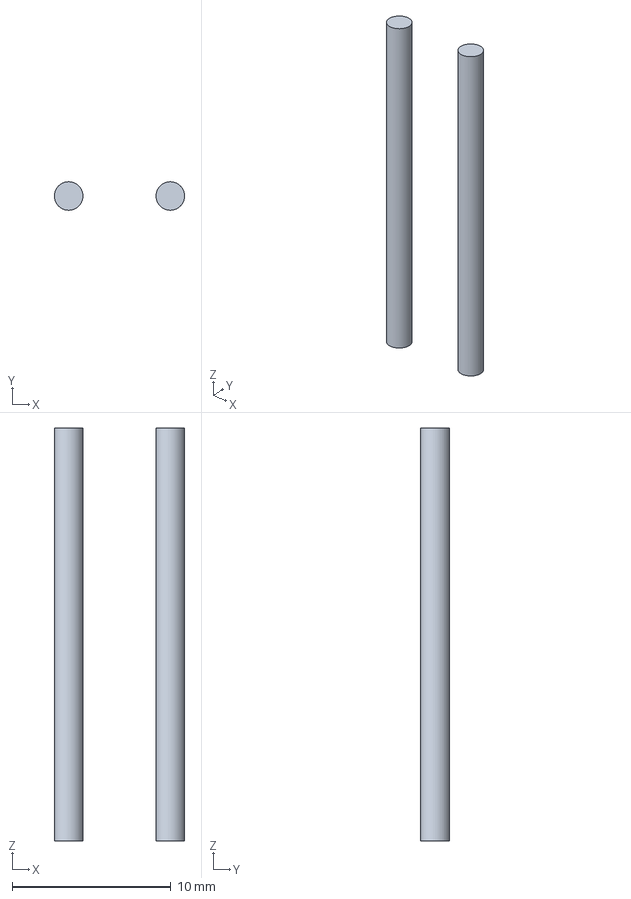
[picture p263: CAD file, 2026-10-09]
spinoffs/earnest/out/step/valve-heater.step
8.20 x 1.80 x 26.0 mm
