nathe-vink/earmilk/spinoffs/earwig/out/step/bud-r.step

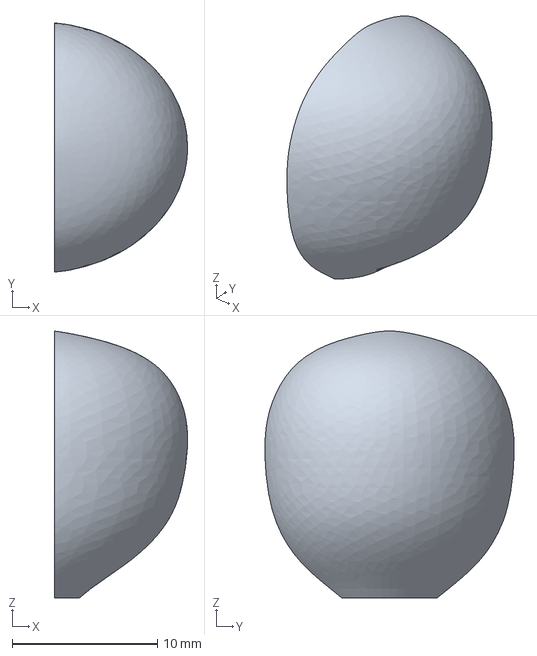
[picture p264: CAD file, 2026-10-06]
spinoffs/earwig/out/step/bud-r.step
9.18 x 17.2 x 18.4 mm
