nathe-vink/earmilk/spinoffs/earworm/out/step/splitter.step

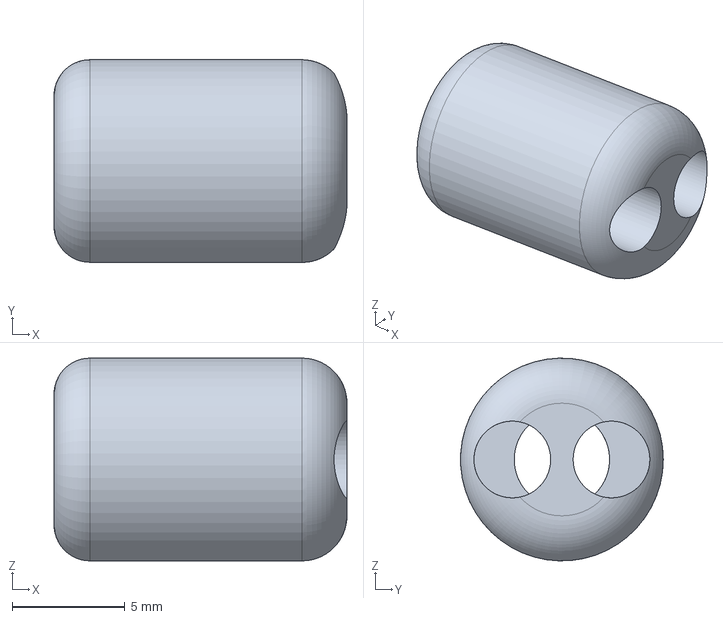
[picture p265: CAD file, 2026-10-05]
spinoffs/earworm/out/step/splitter.step
13.0 x 8.99 x 9.00 mm
