nathe-vink/earmilk/fab/out-bookshelf/dxf/amp-box-lid-underside.dxf

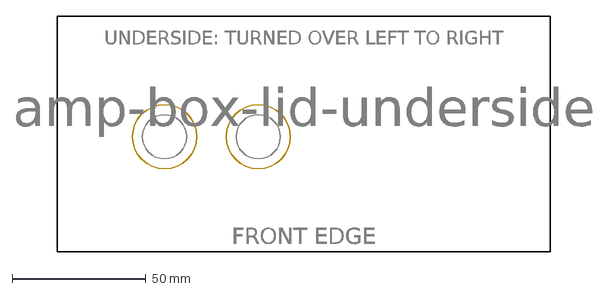
[picture p266: CAD file, 2026-10-09]
fab/out-bookshelf/dxf/amp-box-lid-underside.dxf
FRONT EDGE
UNDERSIDE: TURNED OVER LEFT TO RIGHT
amp-box-lid-underside
