nathe-vink/earmilk/fab/out-bookshelf/step/front-baffle.step

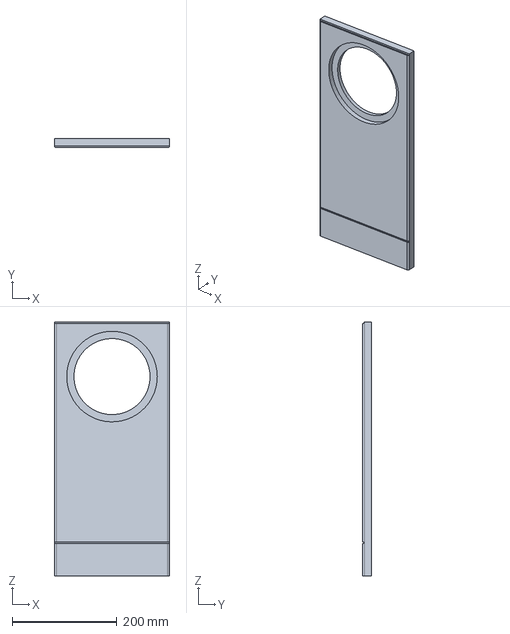
[picture p267: CAD file, 2026-10-09]
fab/out-bookshelf/step/front-baffle.step
220.0 x 18.0 x 484.0 mm
