nathe-vink/earmilk/fab/out/dxf/sheet-2.dxf

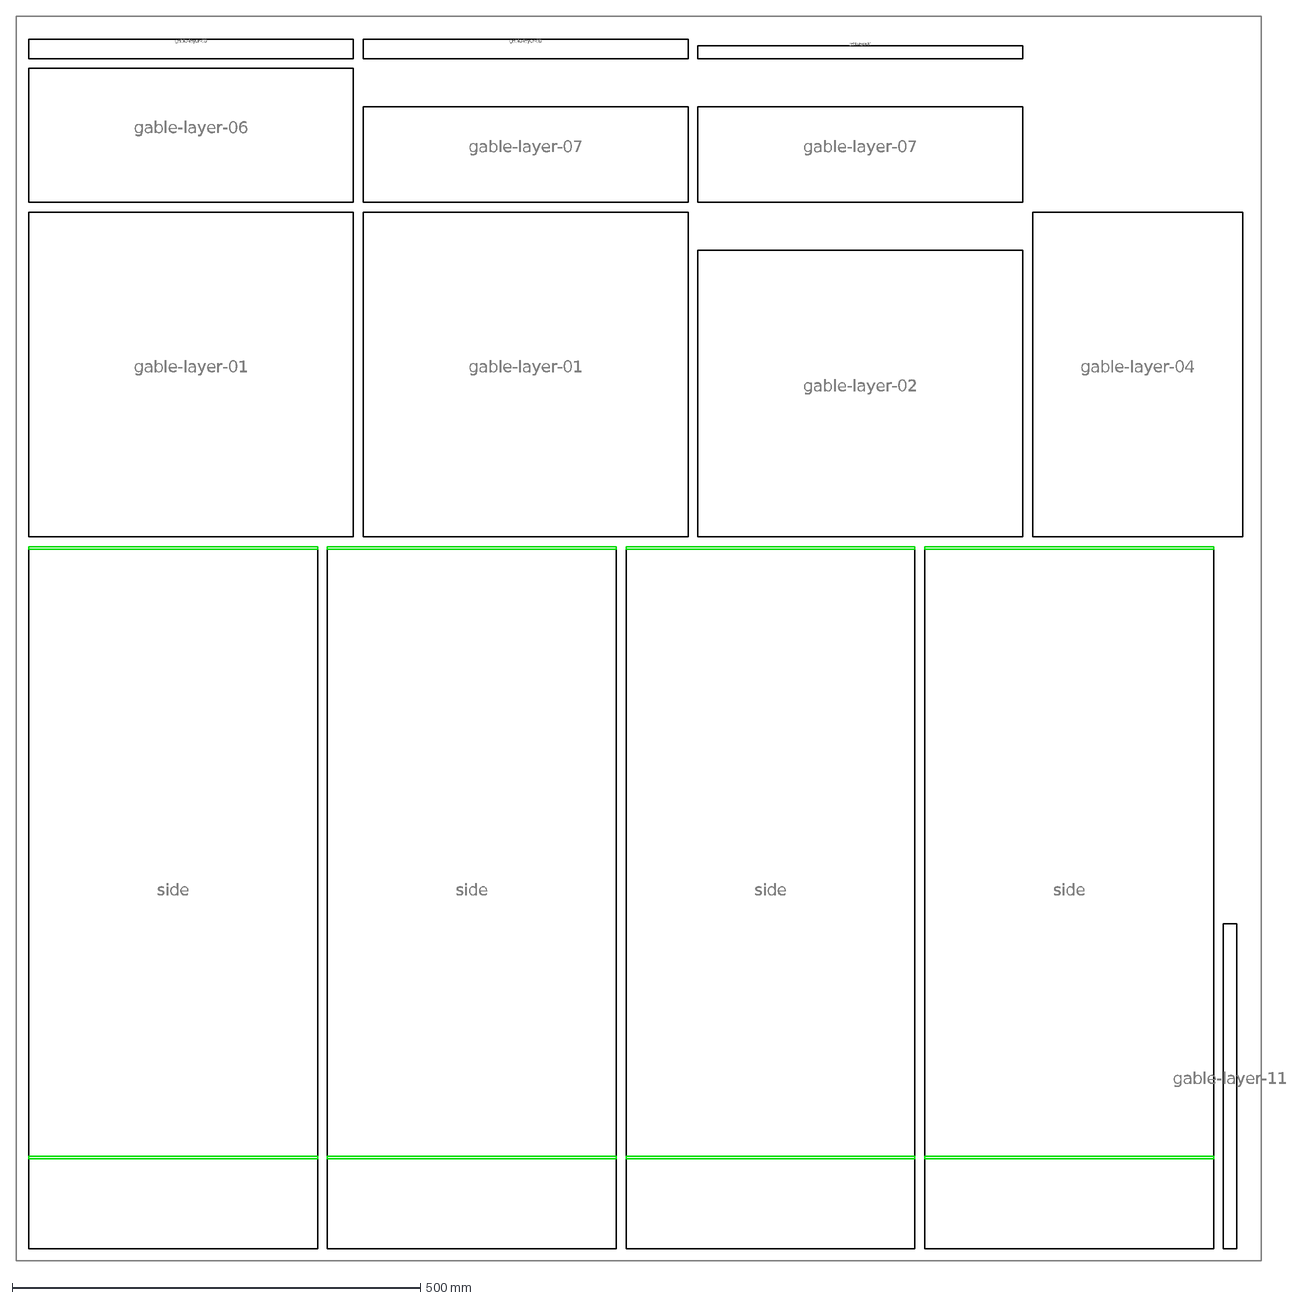
[picture p268: CAD file, 2026-10-09]
fab/out/dxf/sheet-2.dxf
side
gable-layer-01
gable-layer-02
gable-layer-04
gable-layer-06
gable-layer-07
gable-layer-09
gable-layer-10
gable-layer-11
