nathe-vink/earmilk/fab/out/step/front-baffle.step

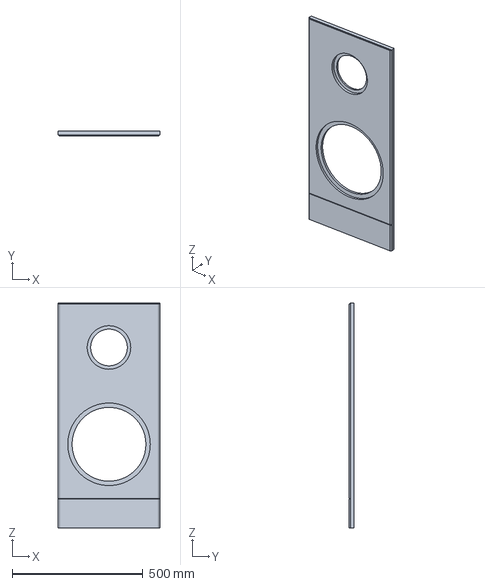
[picture p269: CAD file, 2026-10-09]
fab/out/step/front-baffle.step
390.0 x 18.0 x 860.0 mm
