nathe-vink/earmilk/spinoffs/barkhorn/out/dxf/cork-face.dxf

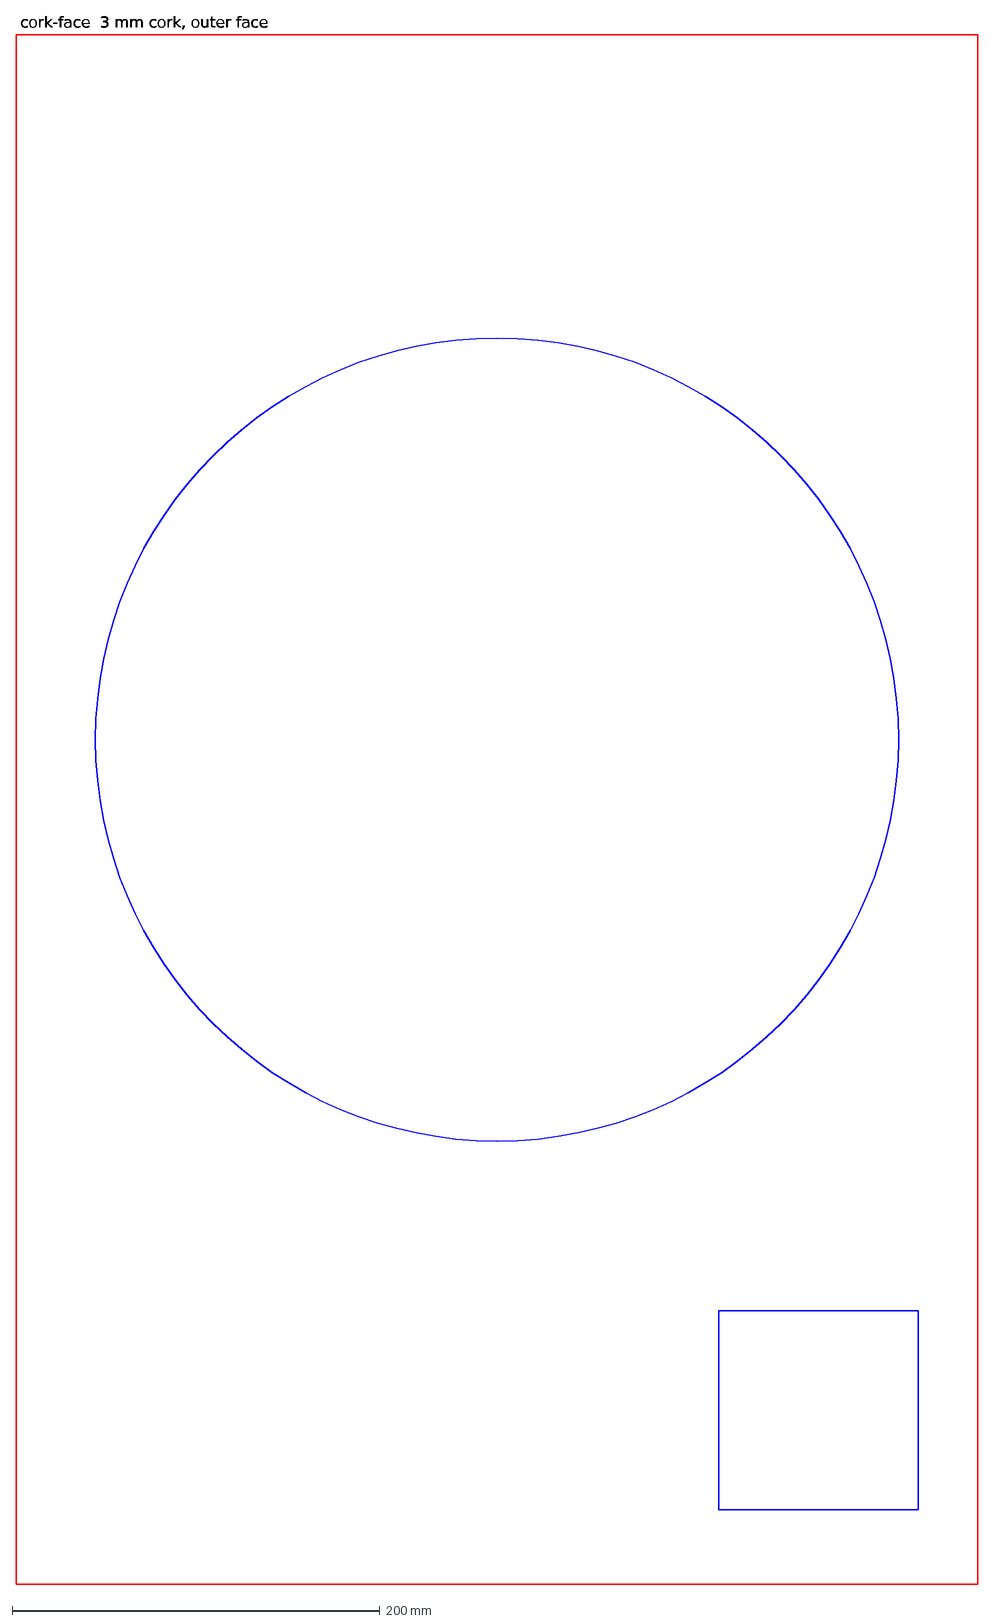
[picture p270: CAD file, 2026-10-11]
spinoffs/barkhorn/out/dxf/cork-face.dxf
cork-face 3 mm cork, outer face
