nathe-vink/earmilk/spinoffs/earnest/out/step/feet-12.step

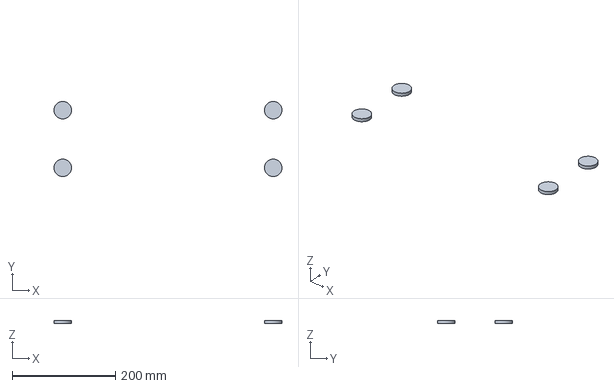
[picture p271: CAD file, 2026-10-09]
spinoffs/earnest/out/step/feet-12.step
441.6 x 145.6 x 6.00 mm
