nathe-vink/earmilk/spinoffs/earworm/out/step/bud-mesh.step

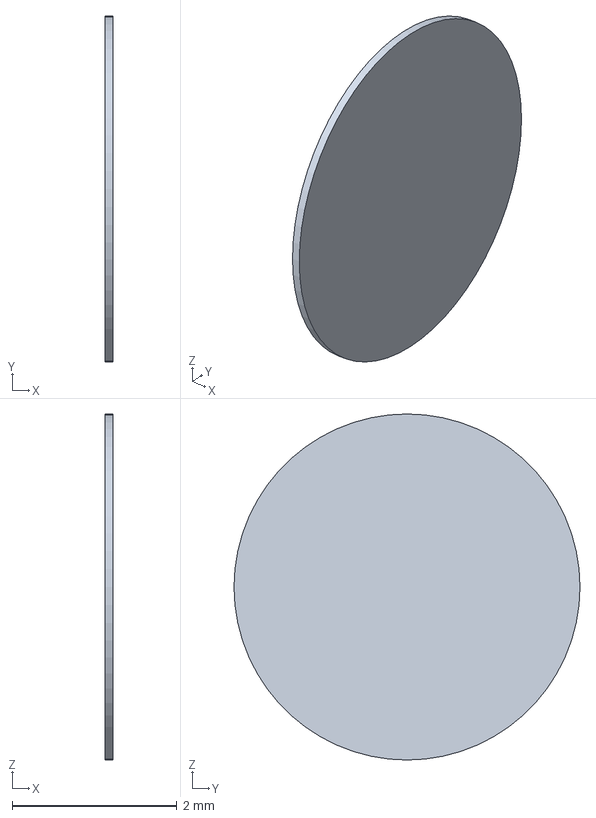
[picture p272: CAD file, 2026-10-05]
spinoffs/earworm/out/step/bud-mesh.step
0.1 x 4.20 x 4.20 mm
