nathe-vink/earmilk/fab/out-bookshelf/dxf/gable-layer-02.dxf

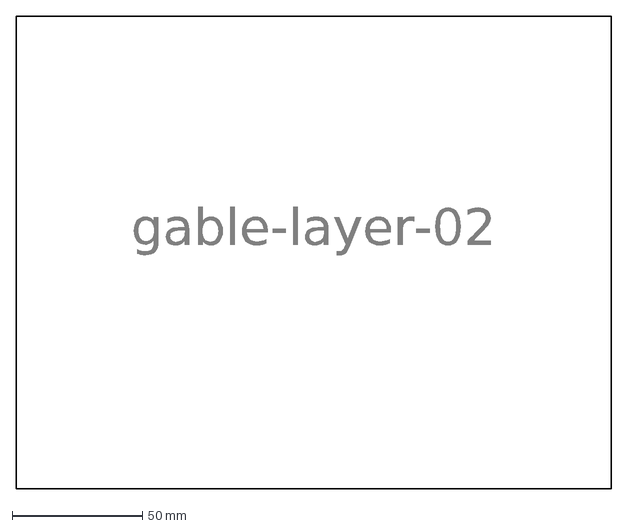
[picture p273: CAD file, 2026-10-09]
fab/out-bookshelf/dxf/gable-layer-02.dxf
gable-layer-02
