nathe-vink/earmilk/fab/out-bookshelf/step/top-panel.step

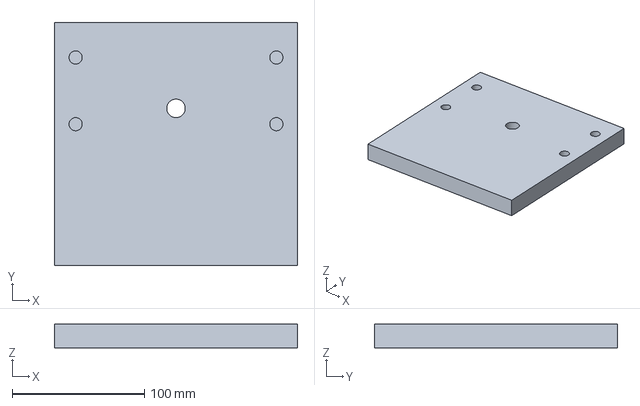
[picture p274: CAD file, 2026-10-09]
fab/out-bookshelf/step/top-panel.step
184.0 x 184.0 x 18.0 mm
