nathe-vink/earmilk/fab/out/dxf/gable-layer-11.dxf

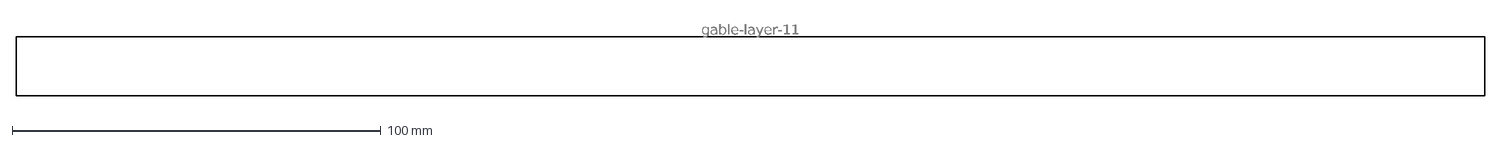
[picture p275: CAD file, 2026-10-09]
fab/out/dxf/gable-layer-11.dxf
gable-layer-11
