nathe-vink/earmilk/fab/out/step/mid-divider.step

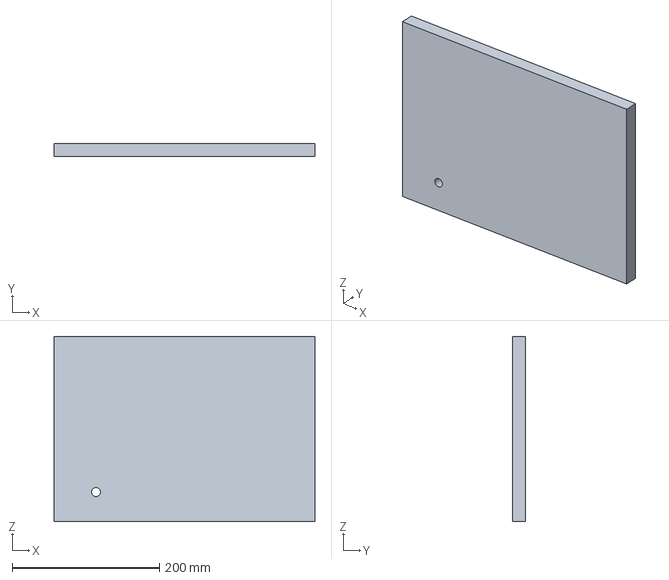
[picture p276: CAD file, 2026-10-09]
fab/out/step/mid-divider.step
354.0 x 18.0 x 251.0 mm
