nathe-vink/earmilk/spinoffs/barkhorn/out/dxf/front-panel.dxf

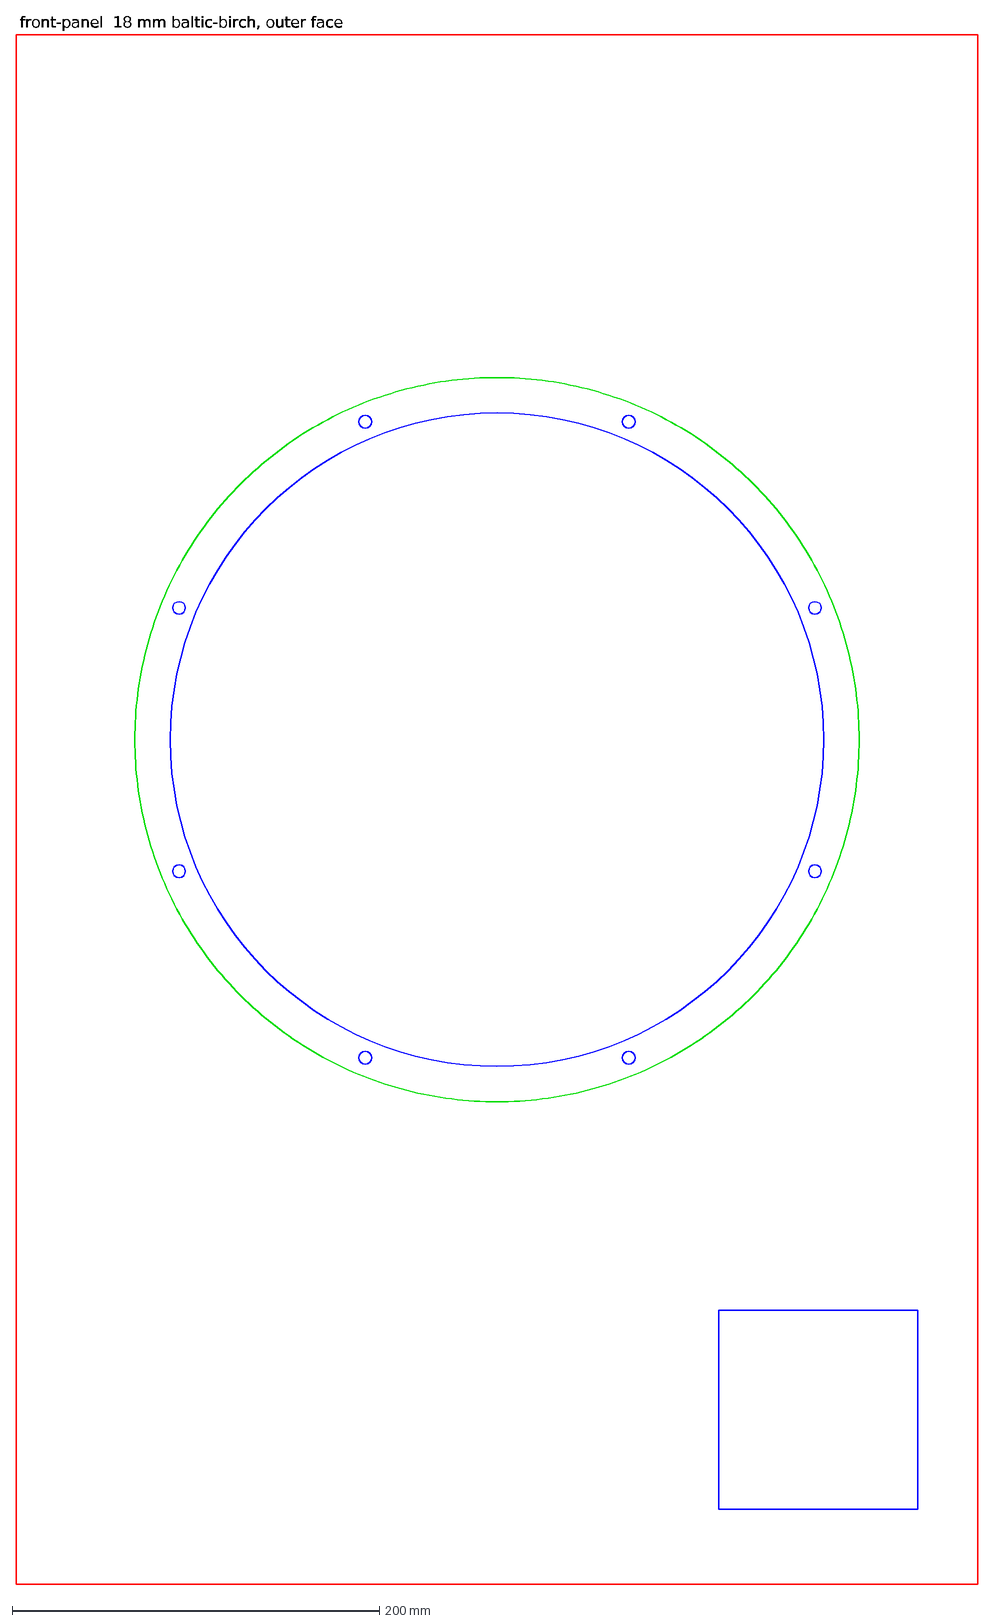
[picture p277: CAD file, 2026-10-11]
spinoffs/barkhorn/out/dxf/front-panel.dxf
front-panel 18 mm baltic-birch, outer face
