nathe-vink/earmilk/spinoffs/earnest/out/step/crate-12-top.step

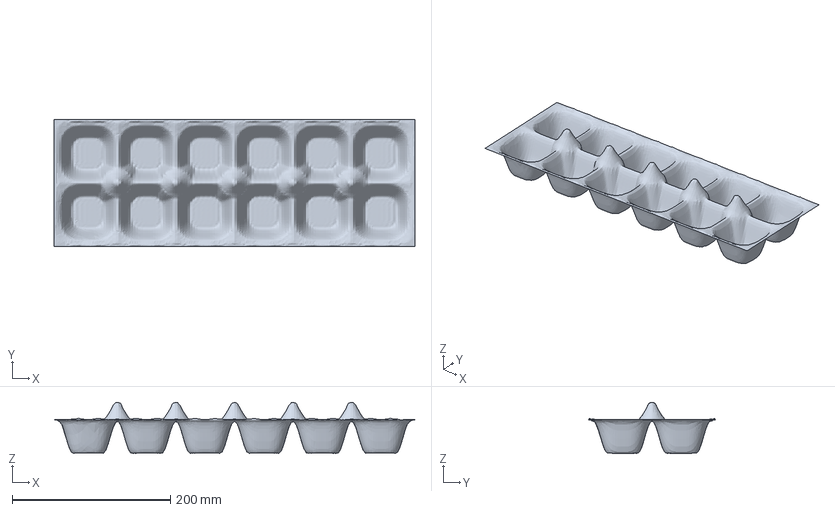
[picture p278: CAD file, 2026-10-09]
spinoffs/earnest/out/step/crate-12-top.step
456.0 x 160.0 x 64.4 mm
