nathe-vink/earmilk/spinoffs/earwig/out/step/grille-r.step

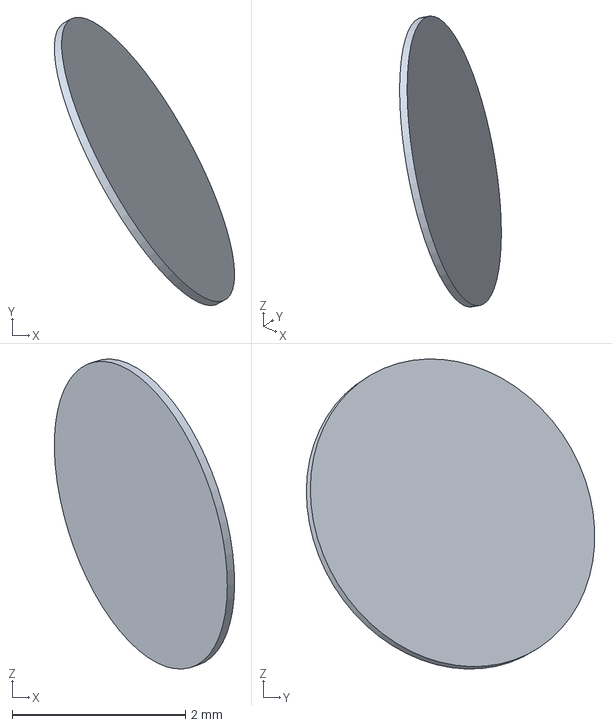
[picture p279: CAD file, 2026-10-06]
spinoffs/earwig/out/step/grille-r.step
2.08 x 3.33 x 3.58 mm
