nathe-vink/earmilk/spinoffs/earworm/out/step/plug-barrel.step

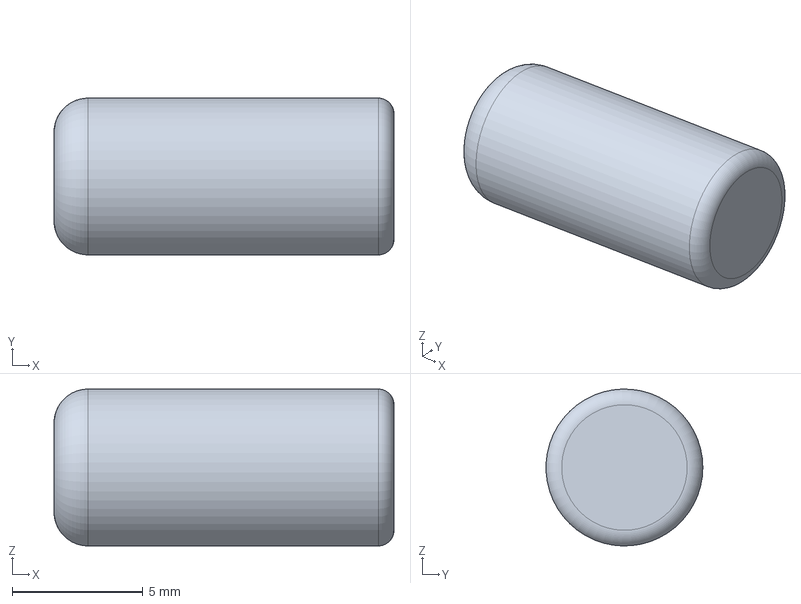
[picture p280: CAD file, 2026-10-05]
spinoffs/earworm/out/step/plug-barrel.step
13.0 x 5.99 x 6.00 mm
