nathe-vink/earmilk/fab/out-bookshelf/step/waveguide-insert.step

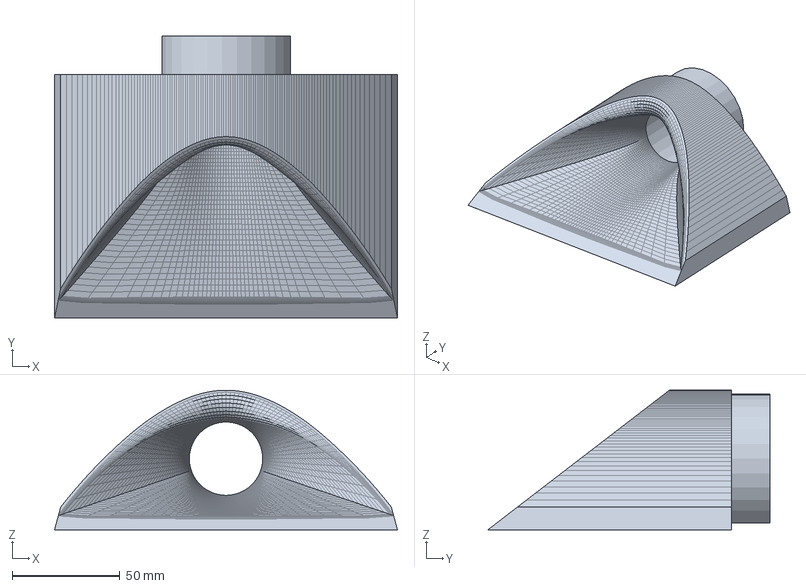
[picture p281: CAD file, 2026-10-08]
fab/out-bookshelf/step/waveguide-insert.step
159.3 x 131.0 x 64.8 mm
