nathe-vink/earmilk/fab/out/dxf/gable-layer-10.dxf

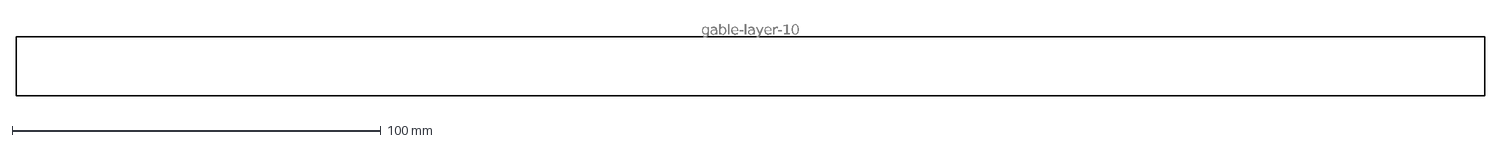
[picture p282: CAD file, 2026-10-09]
fab/out/dxf/gable-layer-10.dxf
gable-layer-10
