nathe-vink/earmilk/fab/out/step/window-brace.step

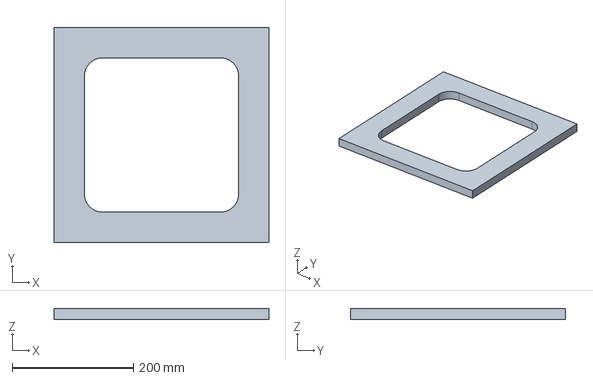
[picture p283: CAD file, 2026-10-09]
fab/out/step/window-brace.step
354.0 x 354.0 x 18.0 mm
