nathe-vink/earmilk/spinoffs/barkhorn/out/dxf/cloth-frame.dxf

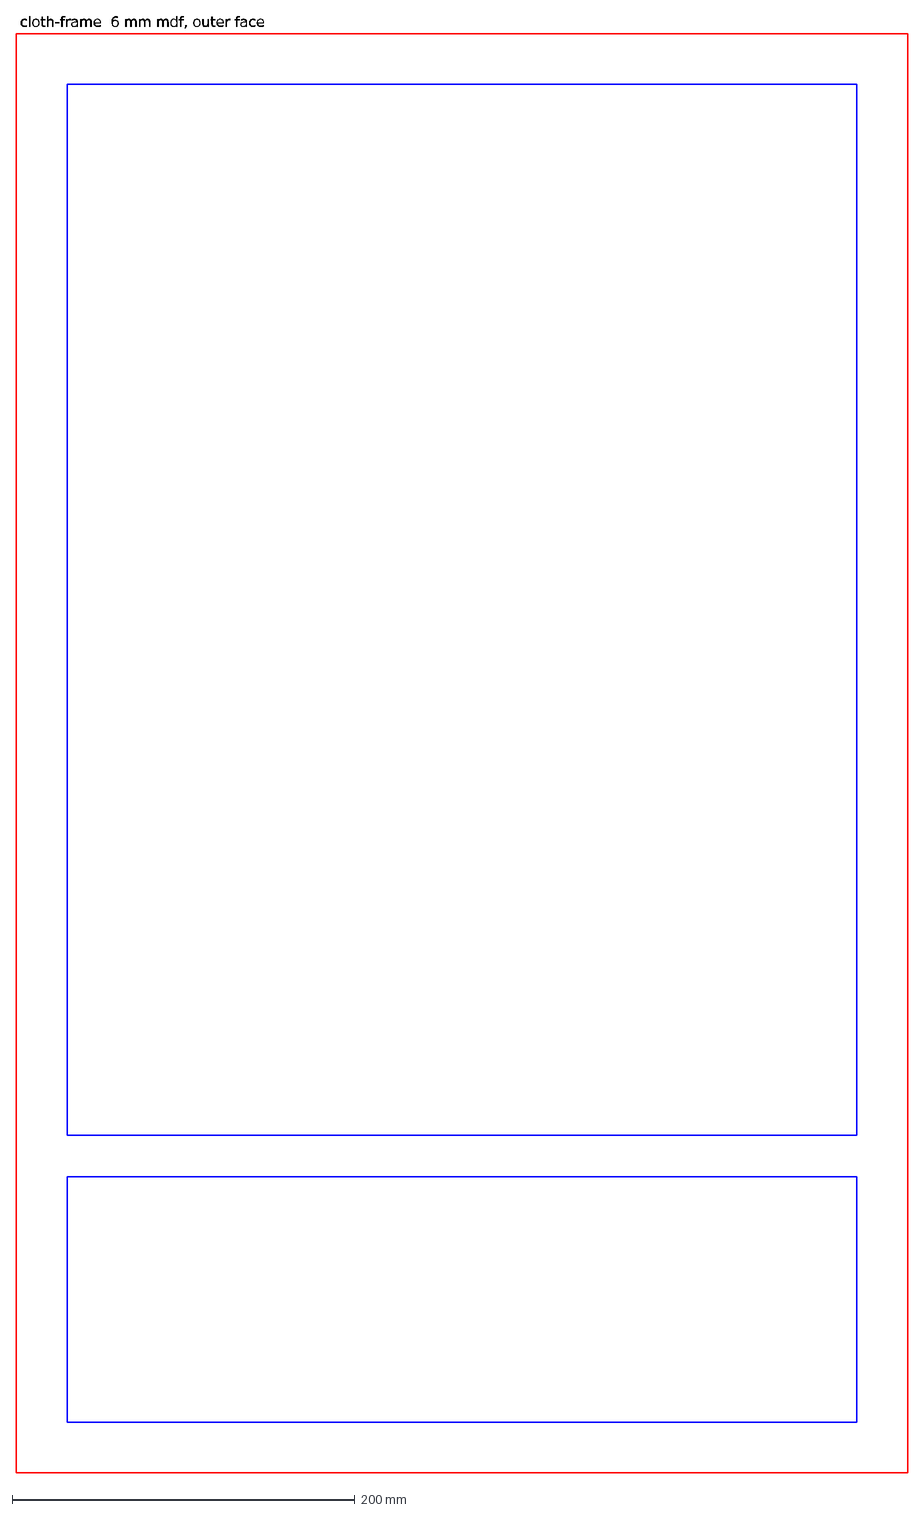
[picture p284: CAD file, 2026-10-11]
spinoffs/barkhorn/out/dxf/cloth-frame.dxf
cloth-frame 6 mm mdf, outer face
