nathe-vink/earmilk/spinoffs/earnest/out/step/crate-6-top.step

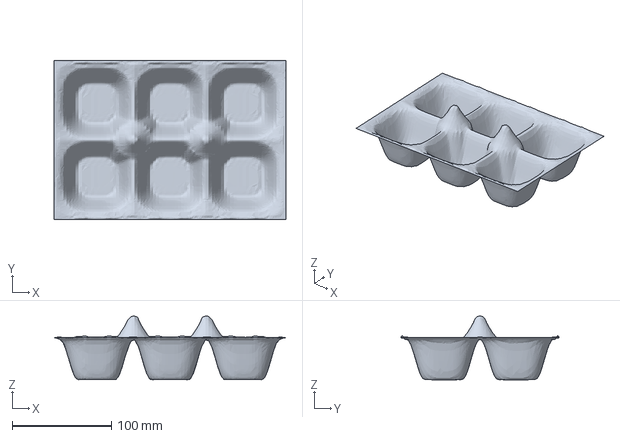
[picture p285: CAD file, 2026-10-09]
spinoffs/earnest/out/step/crate-6-top.step
234.0 x 160.0 x 64.4 mm
