nathe-vink/earmilk/spinoffs/earwig/out/step/forceps.step

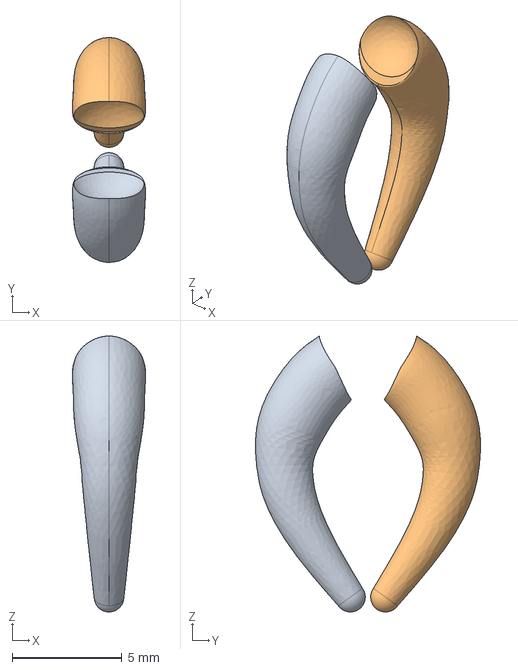
[picture p286: CAD file, 2026-10-06]
spinoffs/earwig/out/step/forceps.step
3.35 x 10.3 x 12.6 mm
