nathe-vink/earmilk/spinoffs/earworm/out/step/baffle-r.step

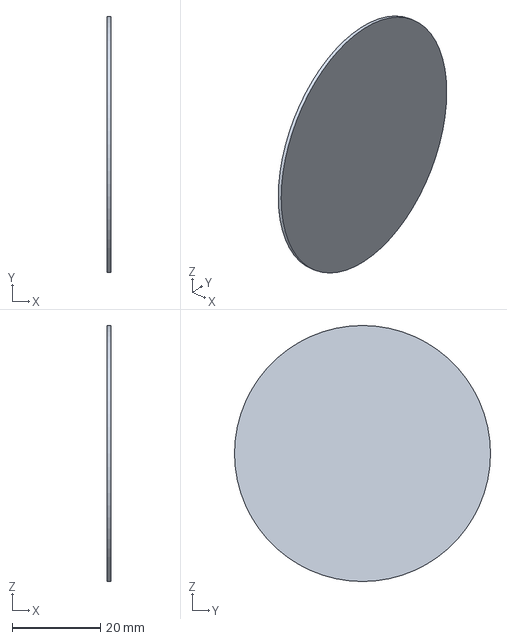
[picture p287: CAD file, 2026-10-04]
spinoffs/earworm/out/step/baffle-r.step
0.8 x 58.0 x 58.0 mm
