nathe-vink/earmilk/fab/out-bookshelf/step/earmilk-bookshelf.step

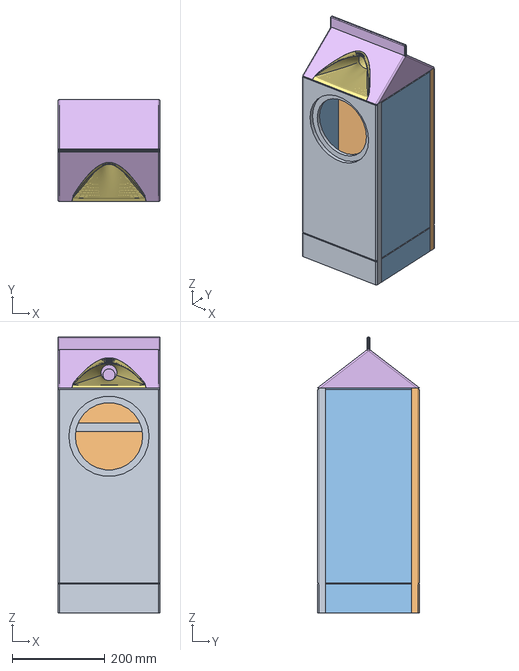
[picture p288: CAD file, 2026-10-08]
fab/out-bookshelf/step/earmilk-bookshelf.step
220.0 x 220.0 x 593.6 mm
