nathe-vink/earmilk/fab/out/dxf/gable-layer-02.dxf

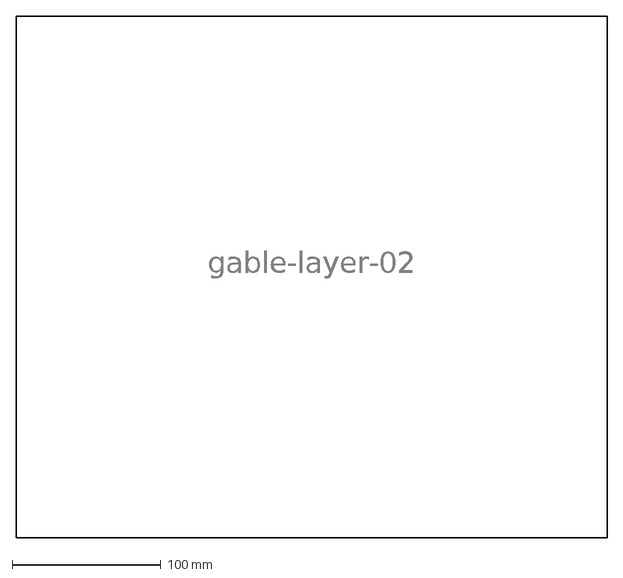
[picture p289: CAD file, 2026-10-09]
fab/out/dxf/gable-layer-02.dxf
gable-layer-02
