nathe-vink/earmilk/spinoffs/barkhorn/out/dxf/nest-baltic-birch-6-lenticel-grille-1.dxf

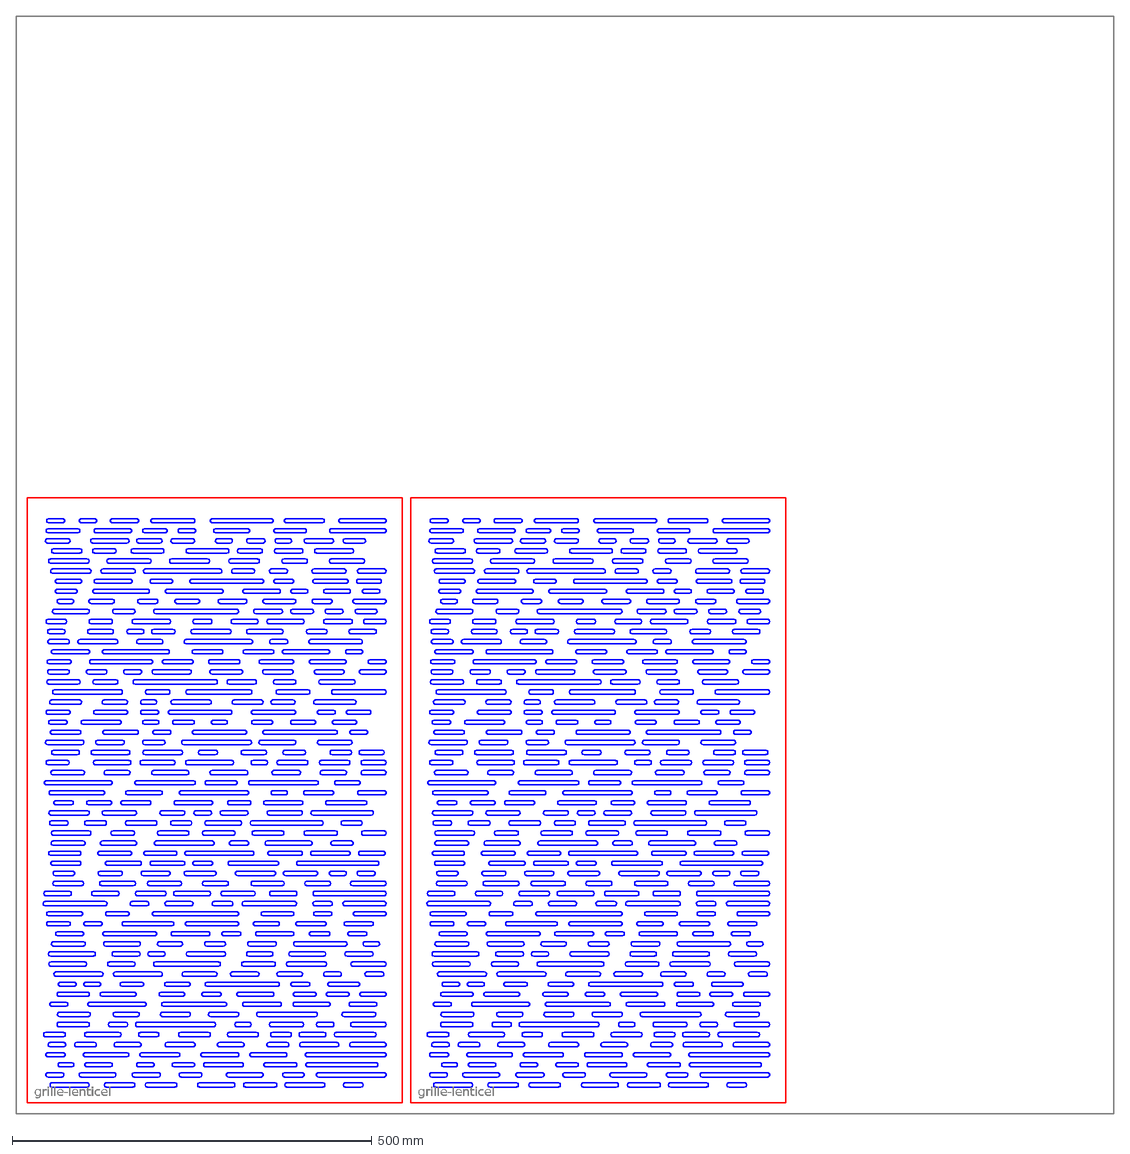
[picture p290: CAD file, 2026-10-11]
spinoffs/barkhorn/out/dxf/nest-baltic-birch-6-lenticel-grille-1.dxf
grille-lenticel
