nathe-vink/earmilk/spinoffs/earnest/out/step/valve-getter.step

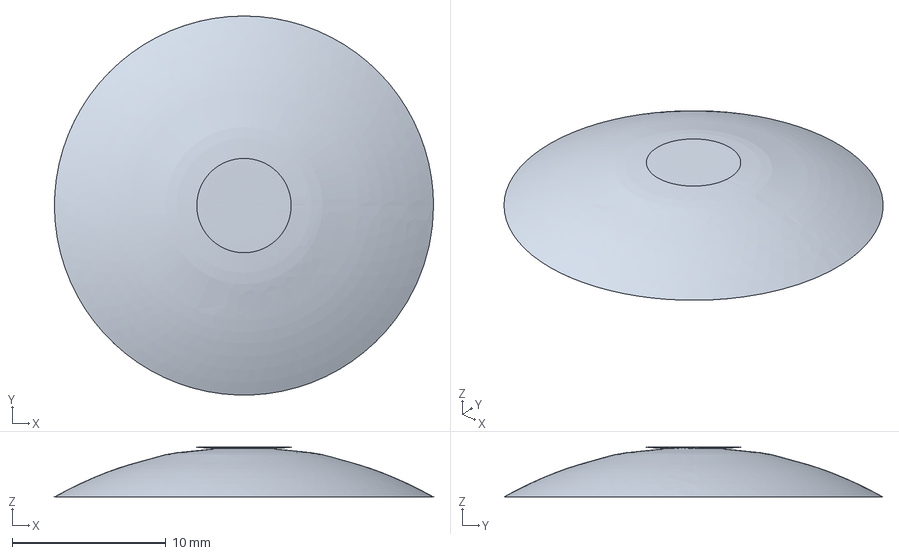
[picture p291: CAD file, 2026-10-09]
spinoffs/earnest/out/step/valve-getter.step
24.7 x 24.7 x 3.25 mm
