nathe-vink/earmilk/fab/out/dxf/gable-layer-08.dxf

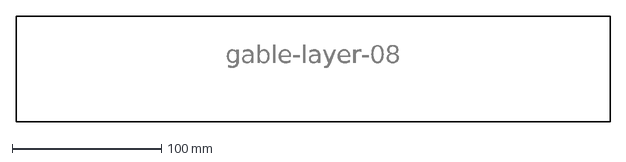
[picture p292: CAD file, 2026-10-09]
fab/out/dxf/gable-layer-08.dxf
gable-layer-08
