nathe-vink/earmilk/fab/out/step/tweeter-retainer.step

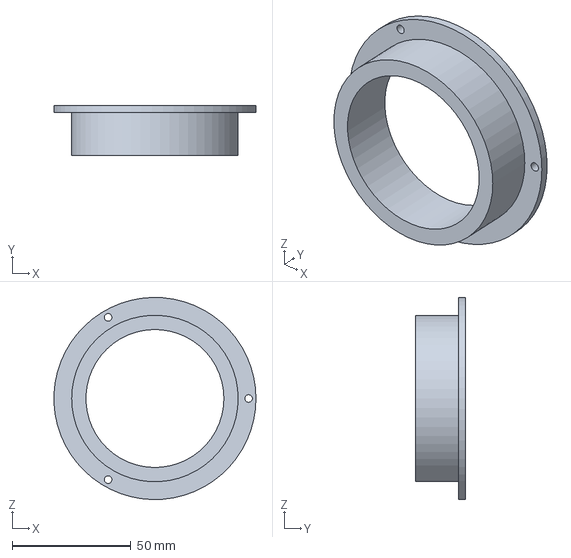
[picture p293: CAD file, 2026-10-09]
fab/out/step/tweeter-retainer.step
84.9 x 21.1 x 85.0 mm
