nathe-vink/earmilk/spinoffs/barkhorn/out/dxf/grille-lenticel.dxf

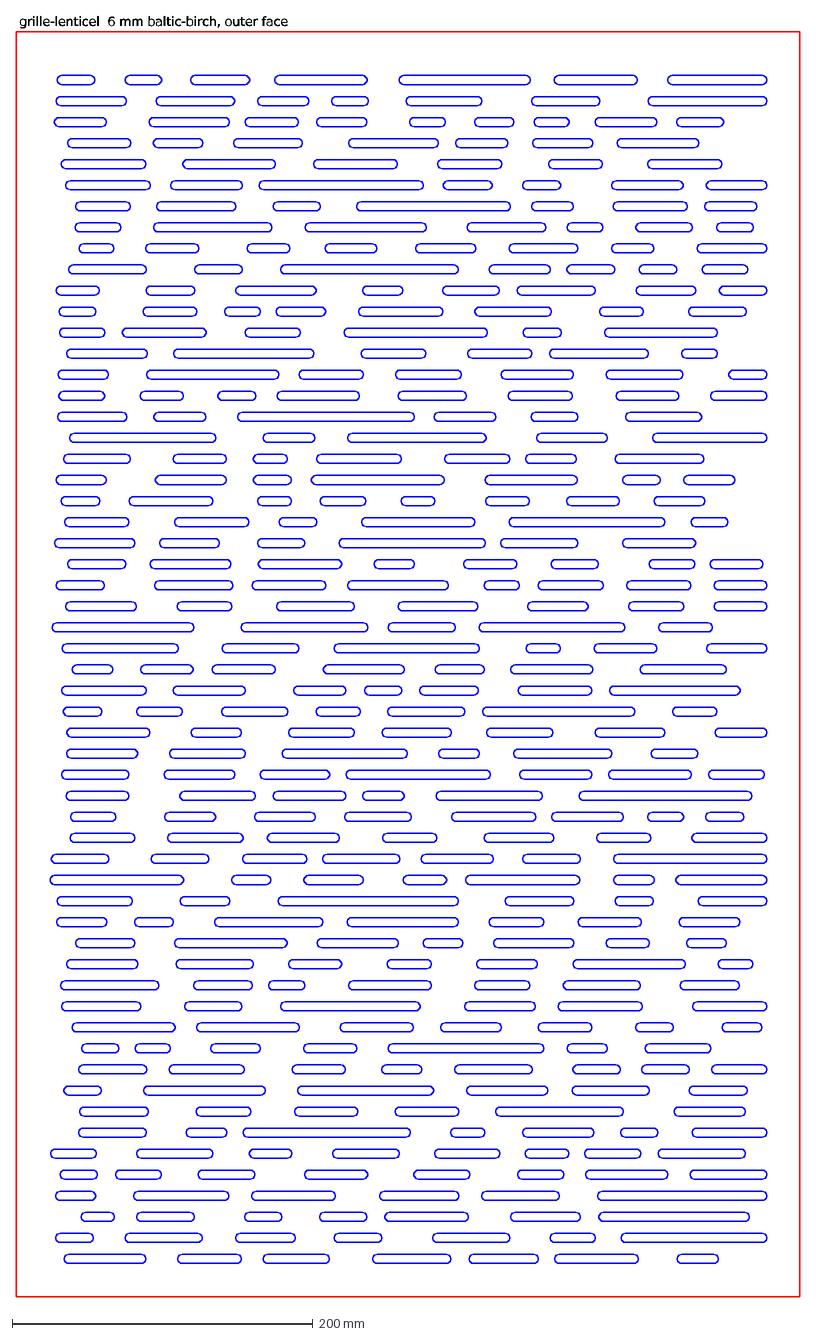
[picture p294: CAD file, 2026-10-11]
spinoffs/barkhorn/out/dxf/grille-lenticel.dxf
grille-lenticel 6 mm baltic-birch, outer face
