nathe-vink/earmilk/spinoffs/earnest/out/step/valve-glass.step

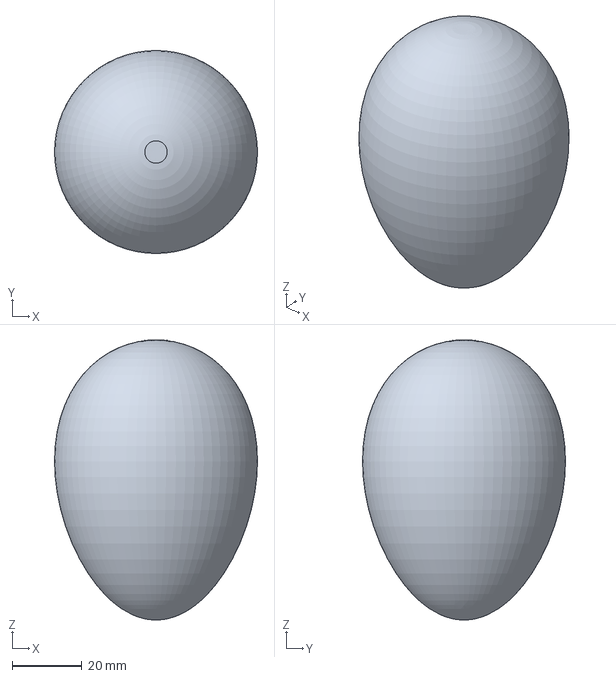
[picture p295: CAD file, 2026-10-09]
spinoffs/earnest/out/step/valve-glass.step
58.0 x 58.0 x 80.0 mm
