nathe-vink/earmilk/fab/out/dxf/gable-layer-07.dxf

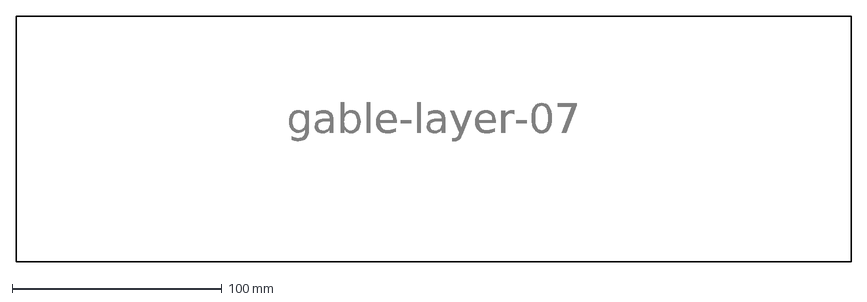
[picture p296: CAD file, 2026-10-09]
fab/out/dxf/gable-layer-07.dxf
gable-layer-07
