nathe-vink/earmilk/spinoffs/barkhorn/out/dxf/bottom.dxf

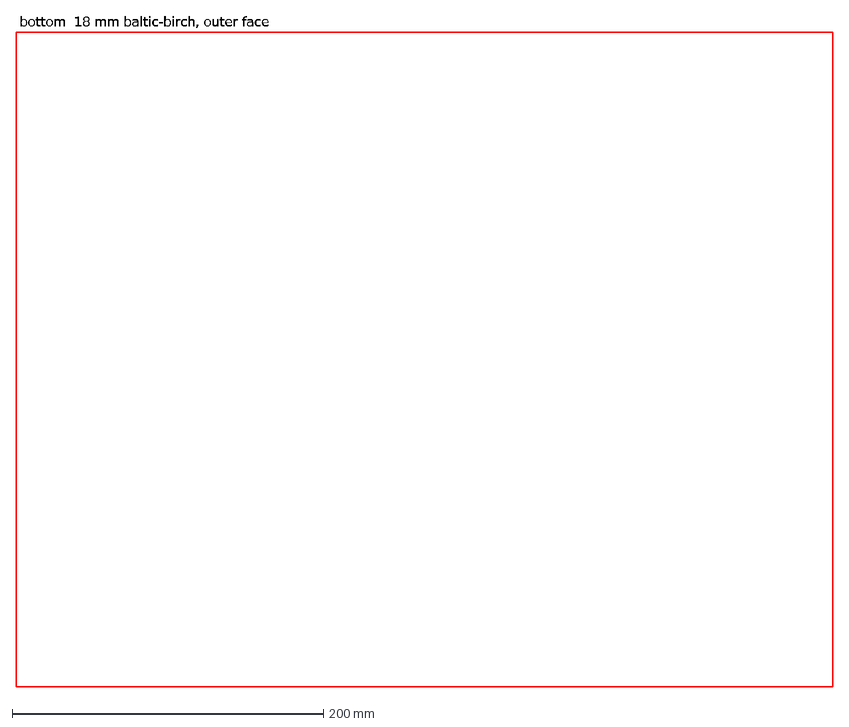
[picture p297: CAD file, 2026-10-11]
spinoffs/barkhorn/out/dxf/bottom.dxf
bottom 18 mm baltic-birch, outer face
