nathe-vink/earmilk/fab/out/dxf/gable-layer-06.dxf

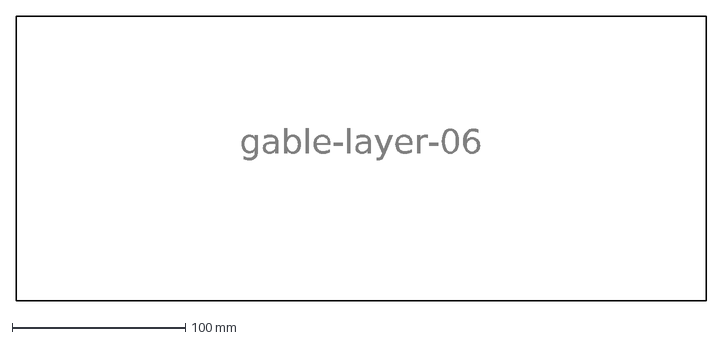
[picture p298: CAD file, 2026-10-09]
fab/out/dxf/gable-layer-06.dxf
gable-layer-06
