nathe-vink/earmilk/fab/out/step/back-panel.step

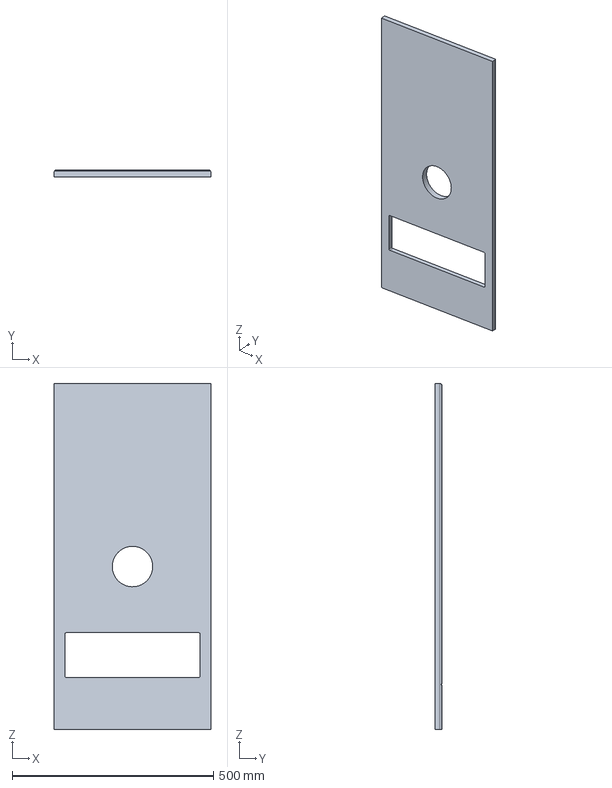
[picture p299: CAD file, 2026-10-09]
fab/out/step/back-panel.step
390.0 x 18.0 x 860.0 mm
