nathe-vink/earmilk/spinoffs/barkhorn/out/dxf/woofer-ring.dxf

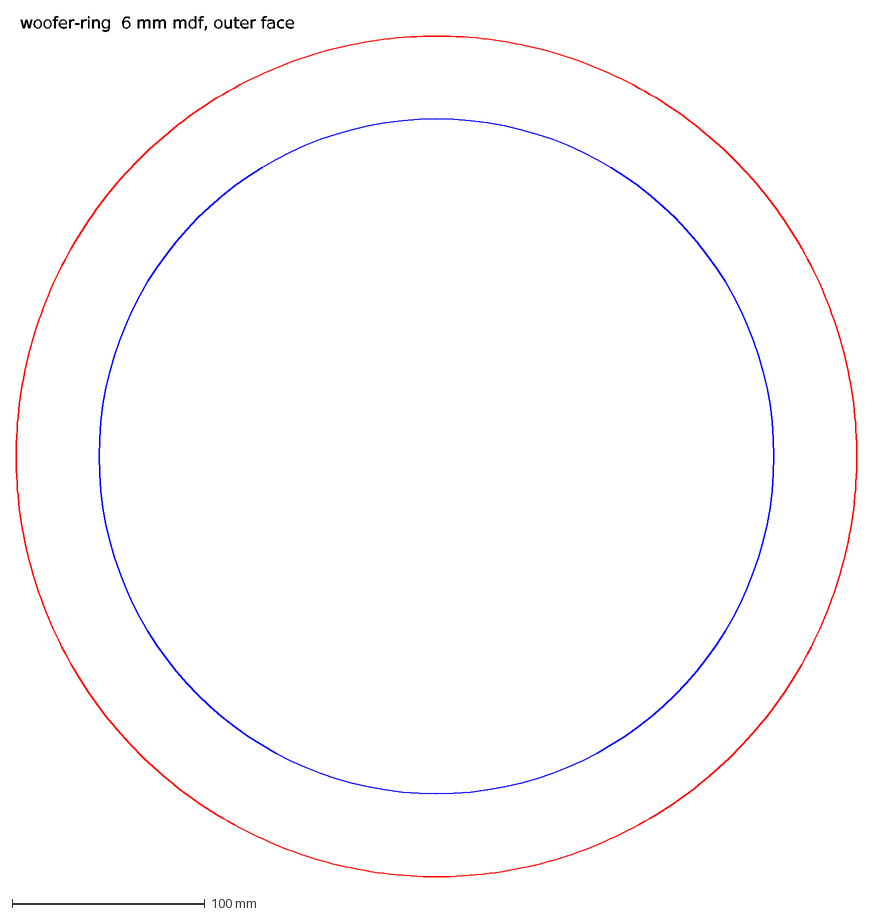
[picture p300: CAD file, 2026-10-11]
spinoffs/barkhorn/out/dxf/woofer-ring.dxf
woofer-ring 6 mm mdf, outer face
