nathe-vink/earmilk/fab/out/dxf/gable-layer-09.dxf

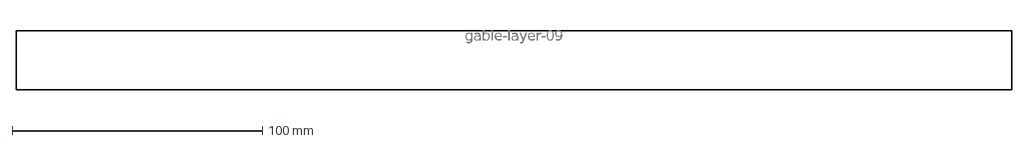
[picture p301: CAD file, 2026-10-09]
fab/out/dxf/gable-layer-09.dxf
gable-layer-09
