nathe-vink/earmilk/spinoffs/barkhorn/out/dxf/nest-baltic-birch-18-2.dxf

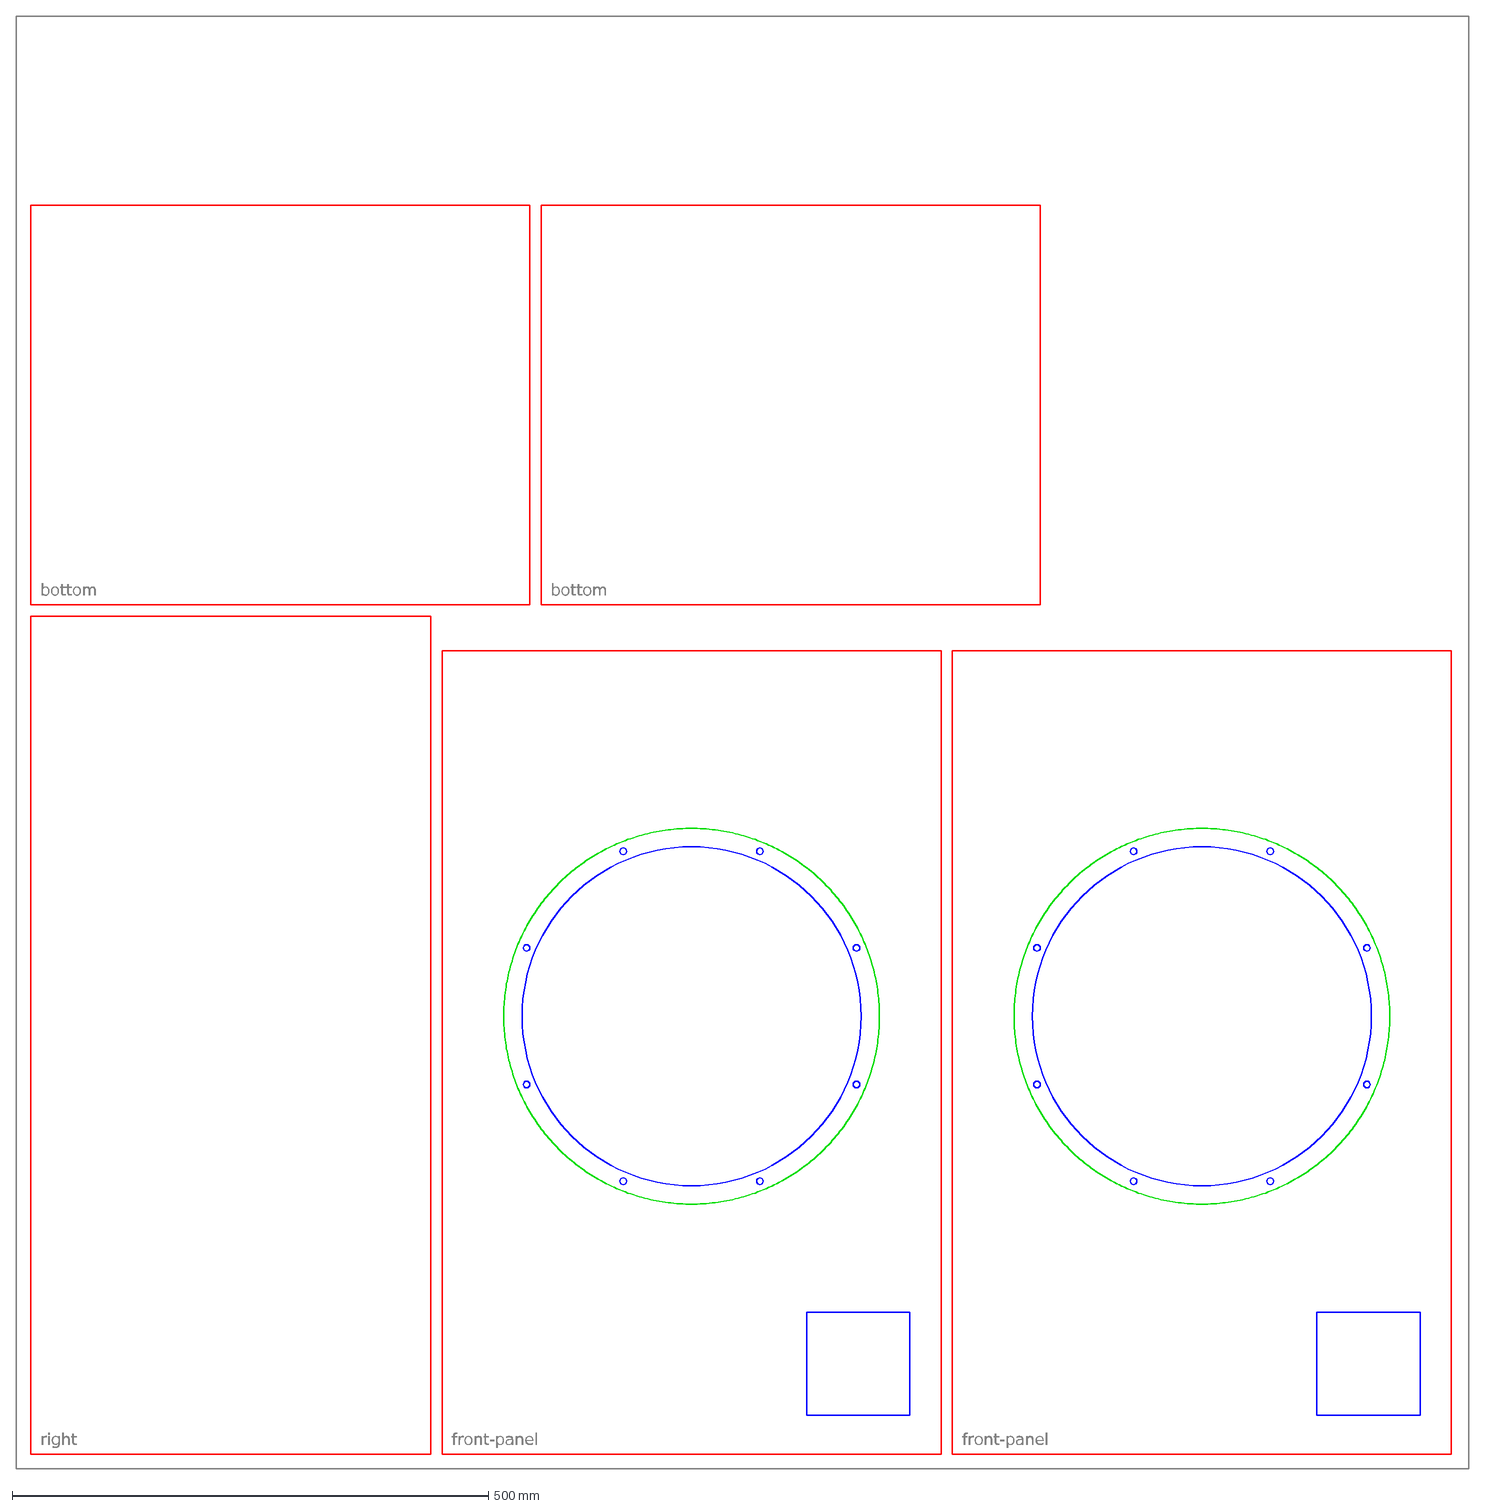
[picture p302: CAD file, 2026-10-11]
spinoffs/barkhorn/out/dxf/nest-baltic-birch-18-2.dxf
right
front-panel
bottom
