nathe-vink/earmilk/spinoffs/earwig/out/step/case-led.step

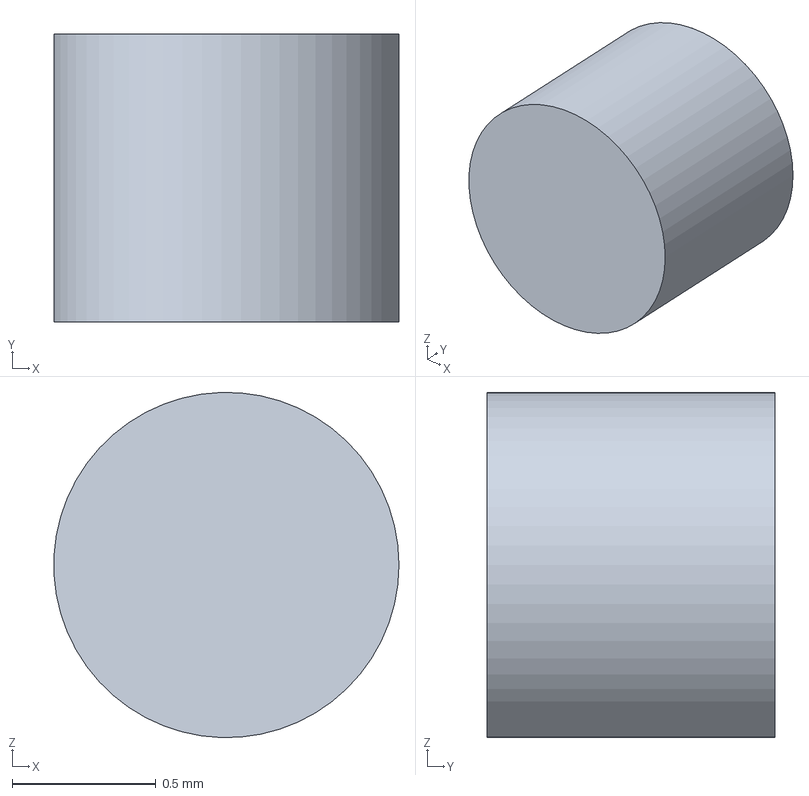
[picture p303: CAD file, 2026-10-05]
spinoffs/earwig/out/step/case-led.step
1.20 x 1.00 x 1.20 mm
