nathe-vink/earmilk/fab/out/step/amp-box-front.step

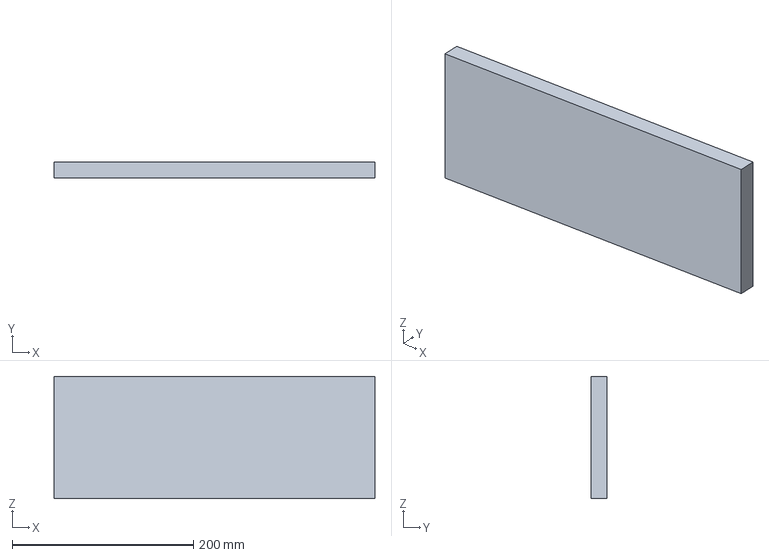
[picture p304: CAD file, 2026-10-09]
fab/out/step/amp-box-front.step
354.0 x 18.0 x 135.0 mm
