nathe-vink/earmilk/spinoffs/barkhorn/out/dxf/nest-cork-3-cork-face-1.dxf

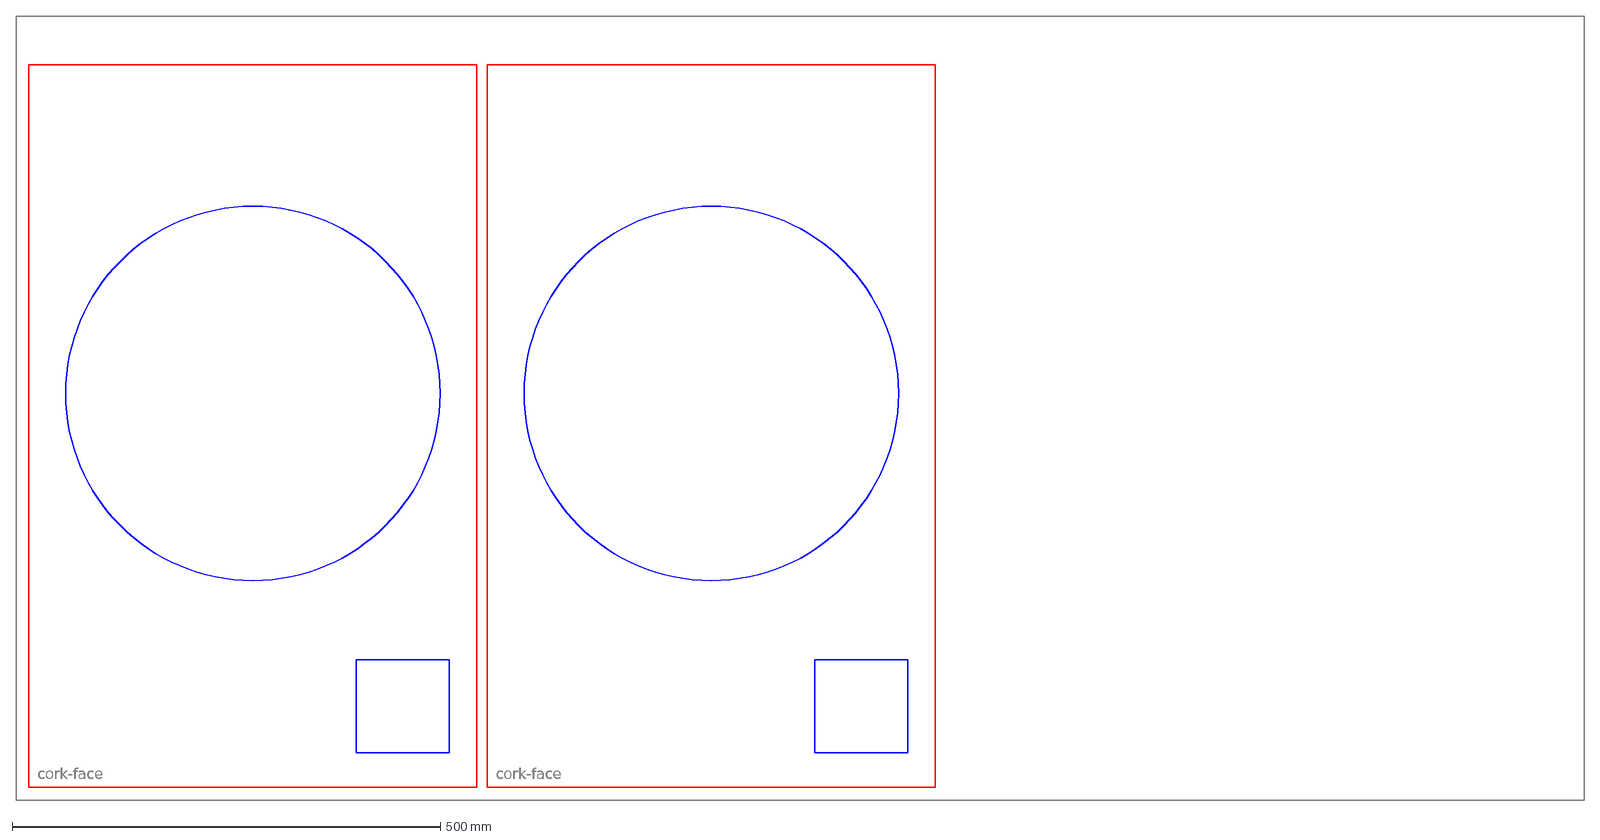
[picture p305: CAD file, 2026-10-11]
spinoffs/barkhorn/out/dxf/nest-cork-3-cork-face-1.dxf
cork-face
