nathe-vink/earmilk/fab/out/step/waveguide-insert.step

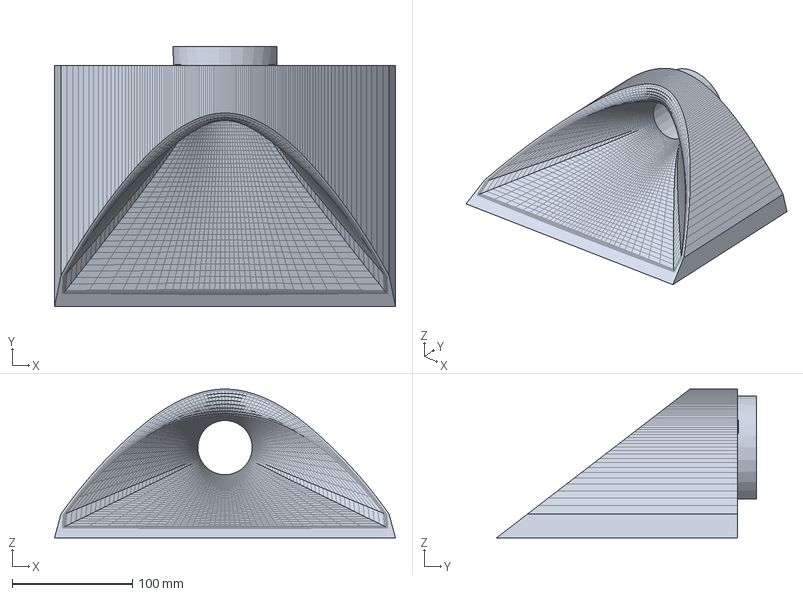
[picture p306: CAD file, 2026-10-08]
fab/out/step/waveguide-insert.step
283.3 x 216.0 x 123.6 mm
