nathe-vink/earmilk/spinoffs/barkhorn/out/dxf/nest-baltic-birch-18-3.dxf

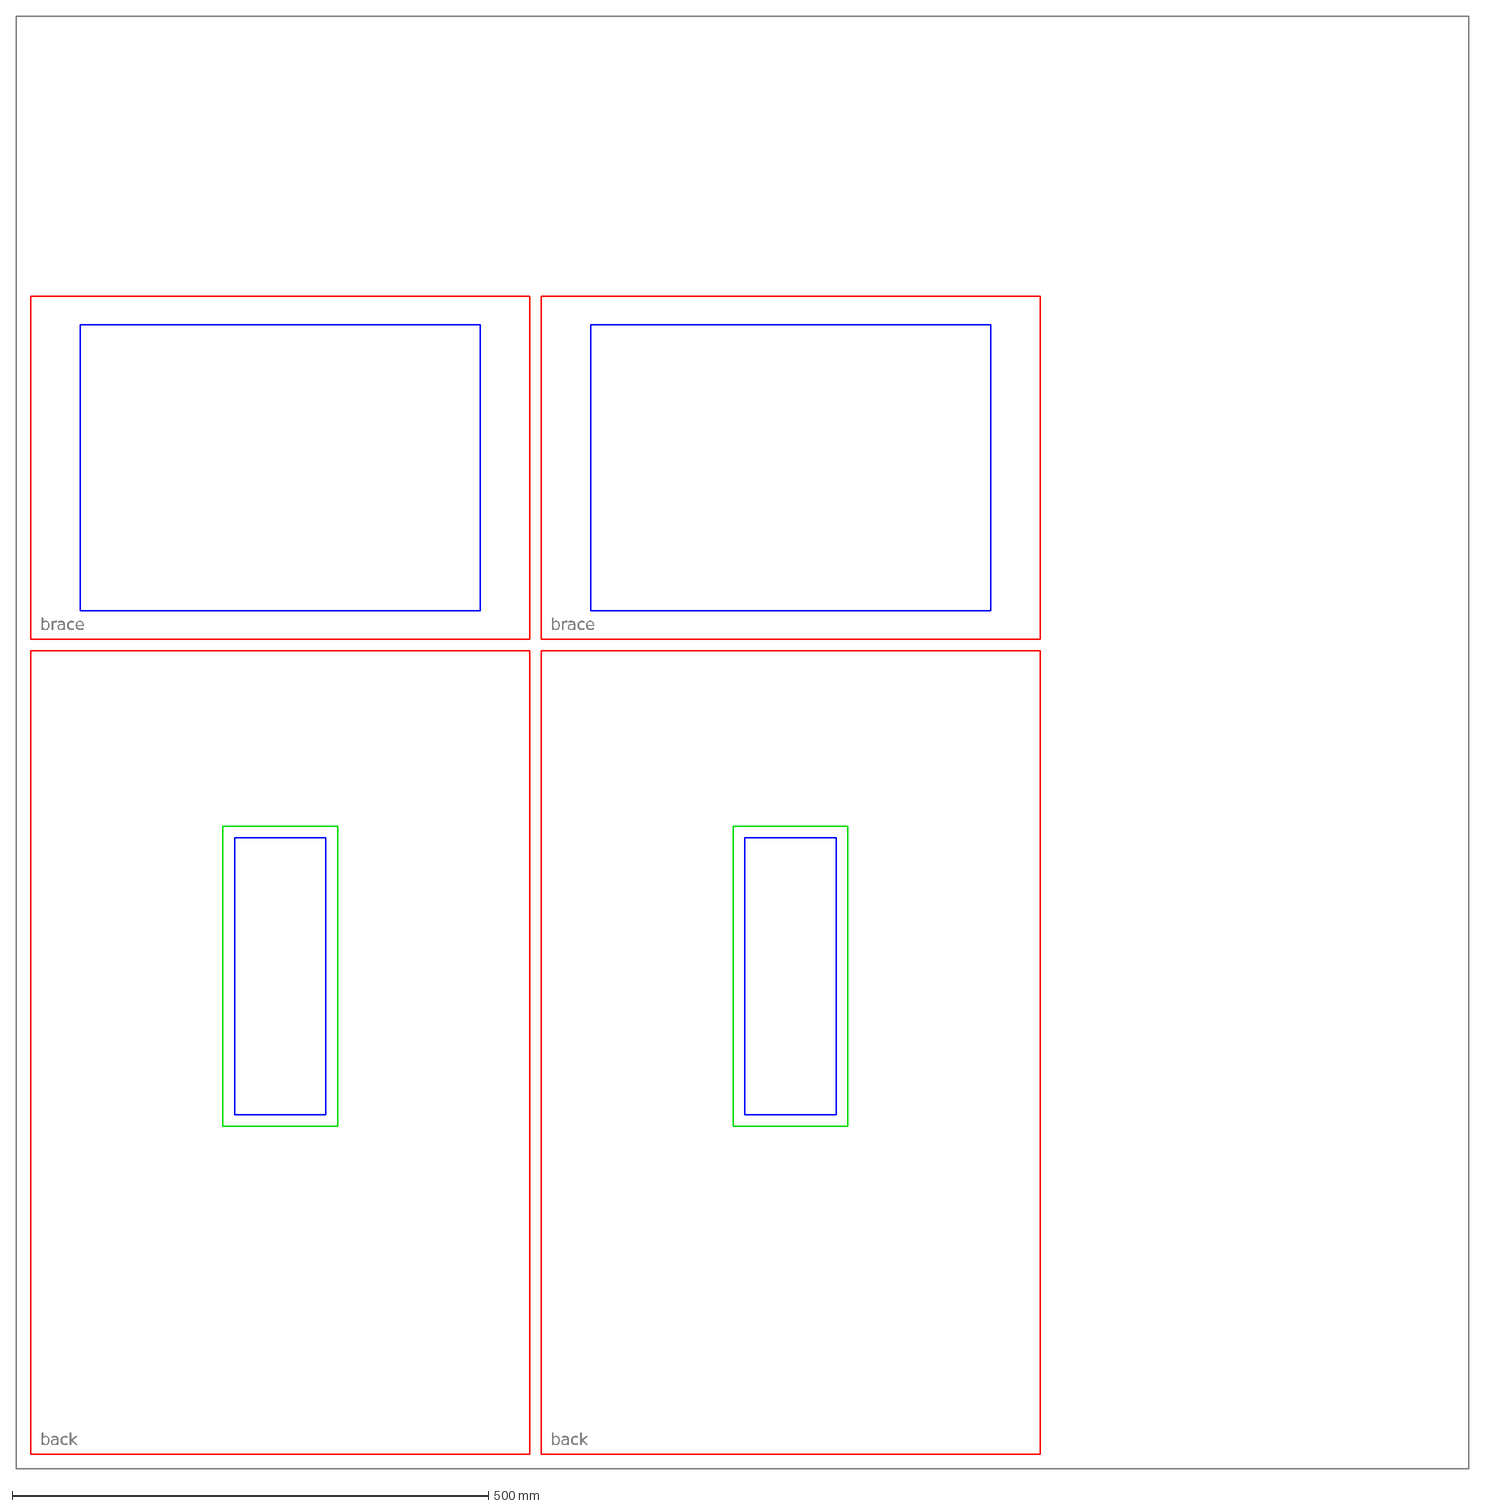
[picture p307: CAD file, 2026-10-11]
spinoffs/barkhorn/out/dxf/nest-baltic-birch-18-3.dxf
back
brace
