nathe-vink/earmilk/fab/out/step/earmilk-floorstander.step

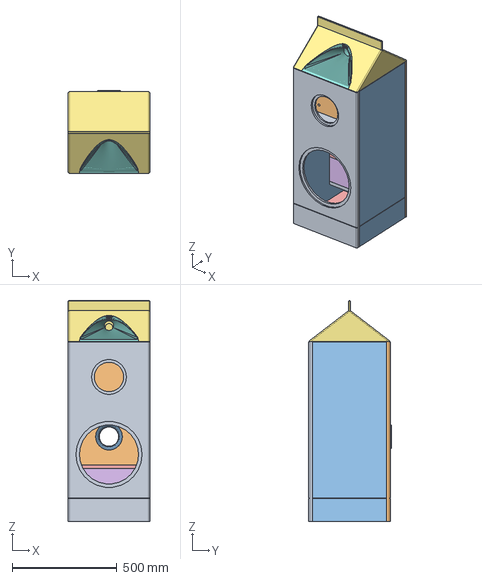
[picture p308: CAD file, 2026-10-08]
fab/out/step/earmilk-floorstander.step
390.0 x 395.0 x 1055.0 mm
