nathe-vink/earmilk/spinoffs/barkhorn/out/dxf/grille-strips.dxf

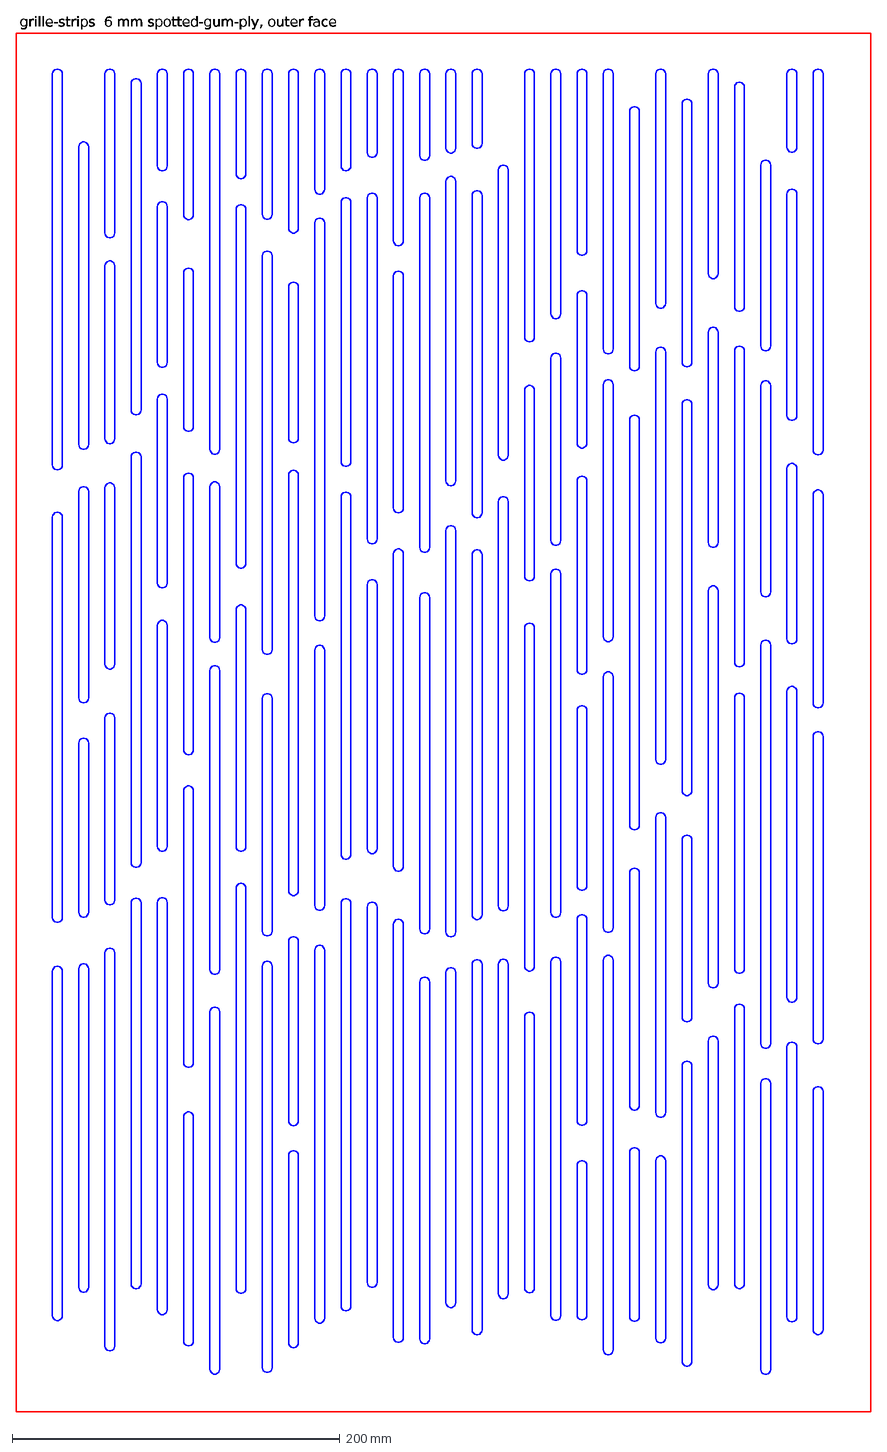
[picture p309: CAD file, 2026-10-11]
spinoffs/barkhorn/out/dxf/grille-strips.dxf
grille-strips 6 mm spotted-gum-ply, outer face
