nathe-vink/earmilk/spinoffs/barkhorn/out/dxf/right.dxf

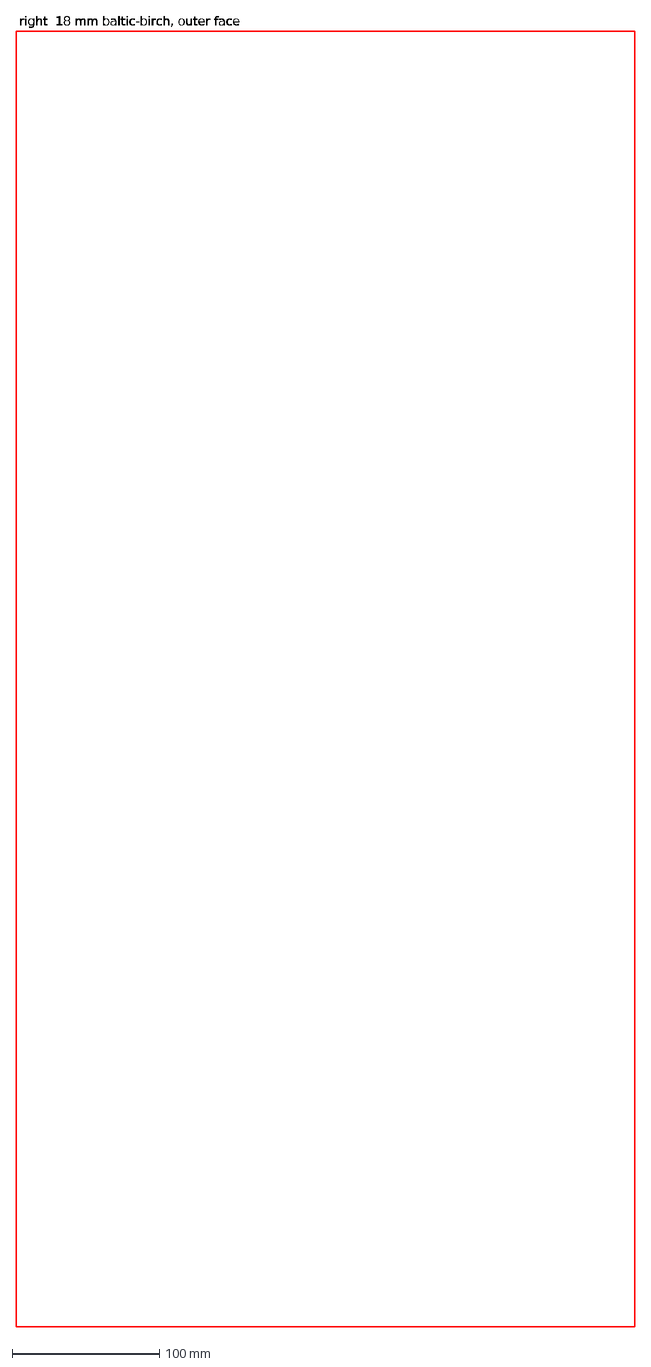
[picture p310: CAD file, 2026-10-11]
spinoffs/barkhorn/out/dxf/right.dxf
right 18 mm baltic-birch, outer face
