nathe-vink/earmilk/spinoffs/barkhorn/out/dxf/left.dxf

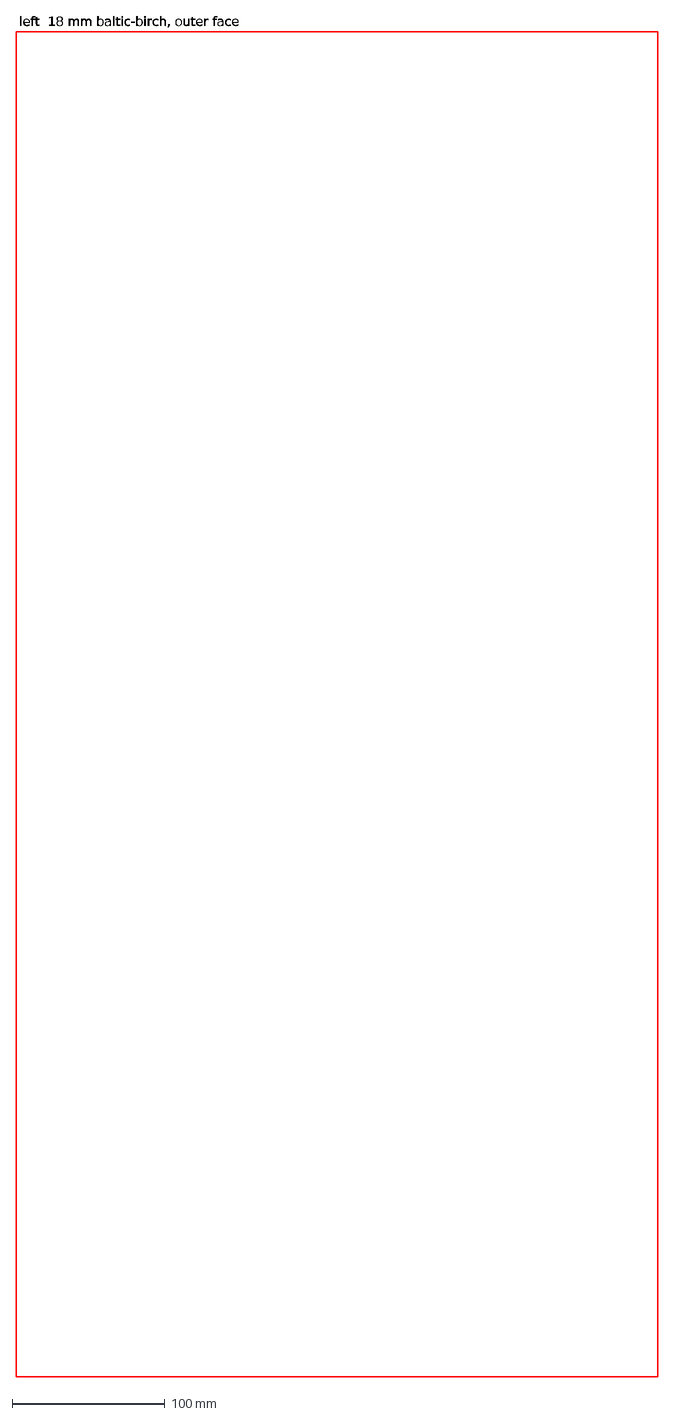
[picture p311: CAD file, 2026-10-11]
spinoffs/barkhorn/out/dxf/left.dxf
left 18 mm baltic-birch, outer face
