nathe-vink/earmilk/spinoffs/barkhorn/out/dxf/saddle-2.dxf

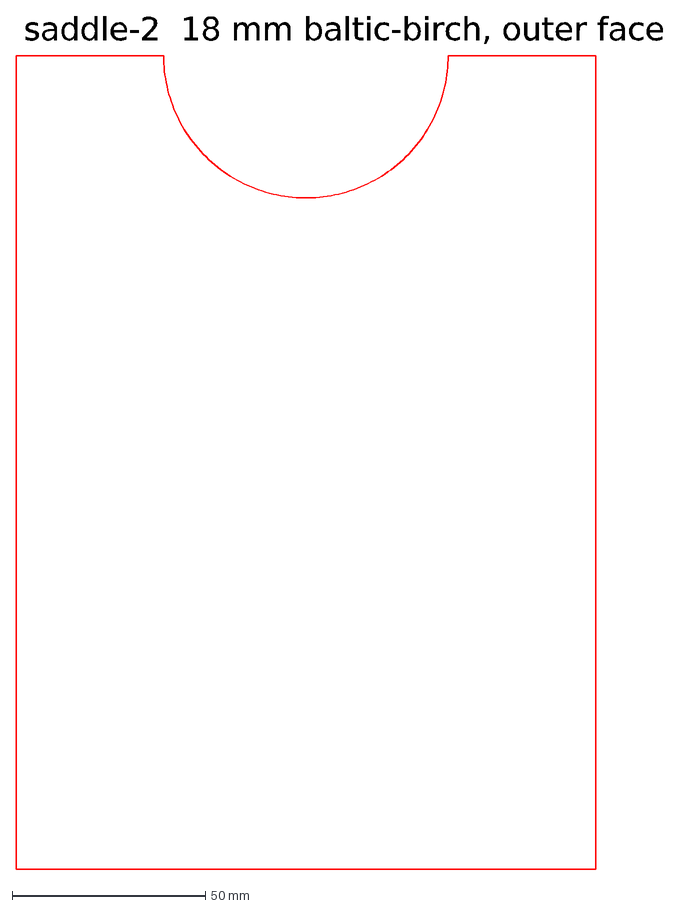
[picture p312: CAD file, 2026-10-10]
spinoffs/barkhorn/out/dxf/saddle-2.dxf
saddle-2 18 mm baltic-birch, outer face
