nathe-vink/earmilk/spinoffs/barkhorn/out/dxf/saddle-1.dxf

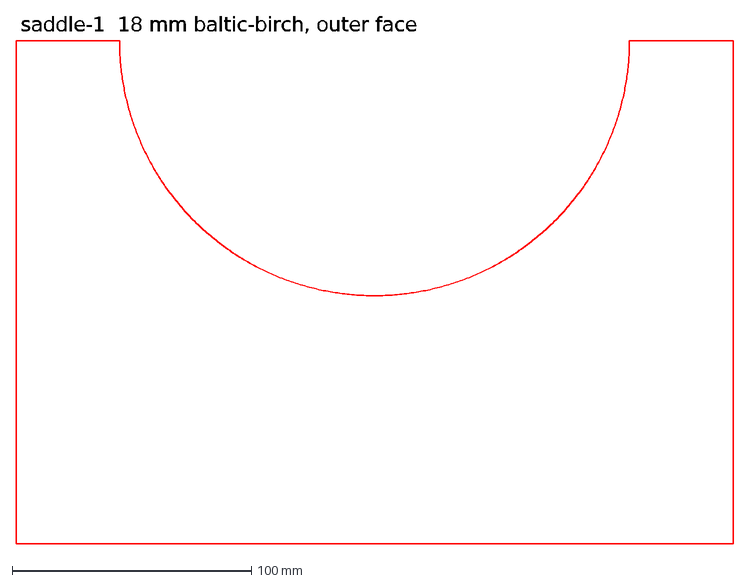
[picture p313: CAD file, 2026-10-10]
spinoffs/barkhorn/out/dxf/saddle-1.dxf
saddle-1 18 mm baltic-birch, outer face
