nathe-vink/earmilk/fab/out-bookshelf/marks/facts-print-preview.png

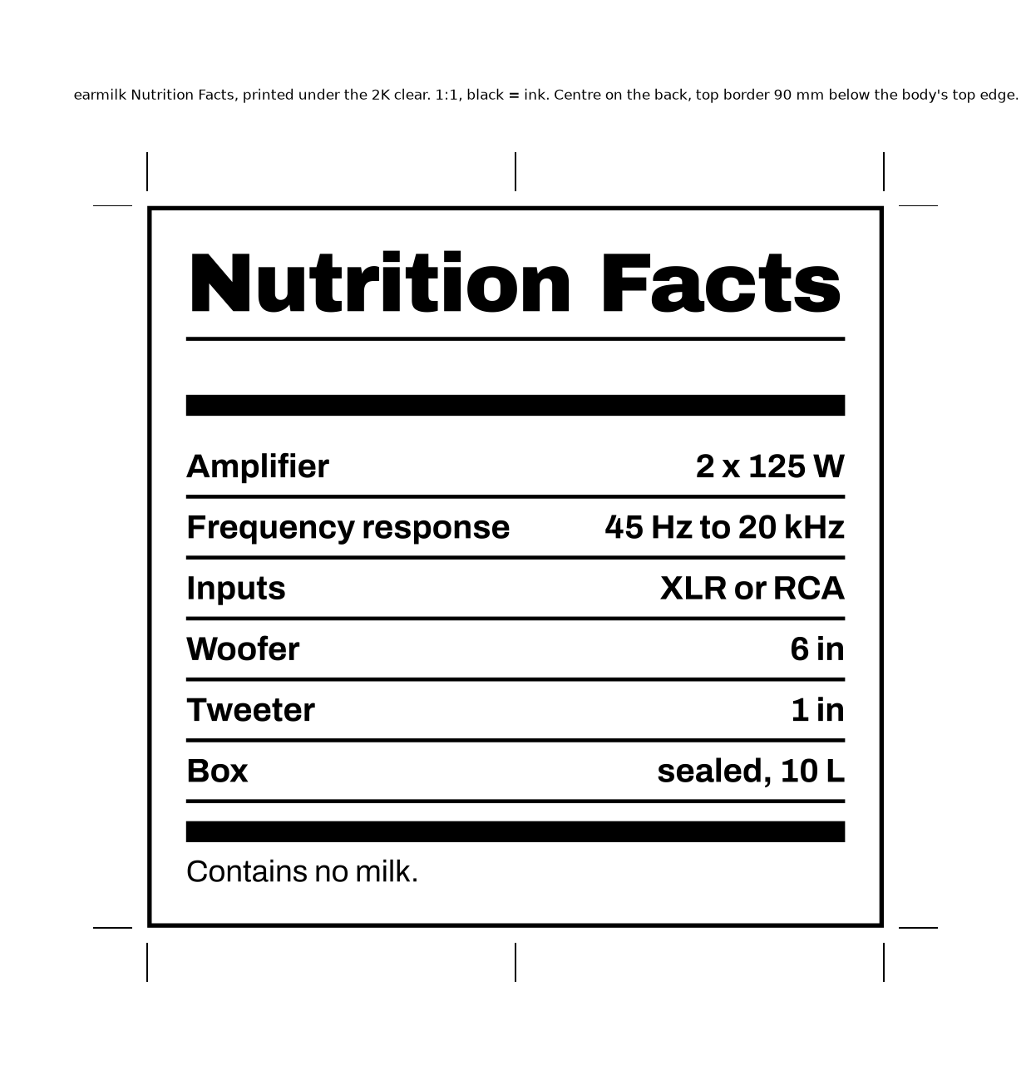
fab/out-bookshelf/marks/facts-print-preview.png
