nathe-vink/earmilk/fab/out/acoustics/waveguide/study.png

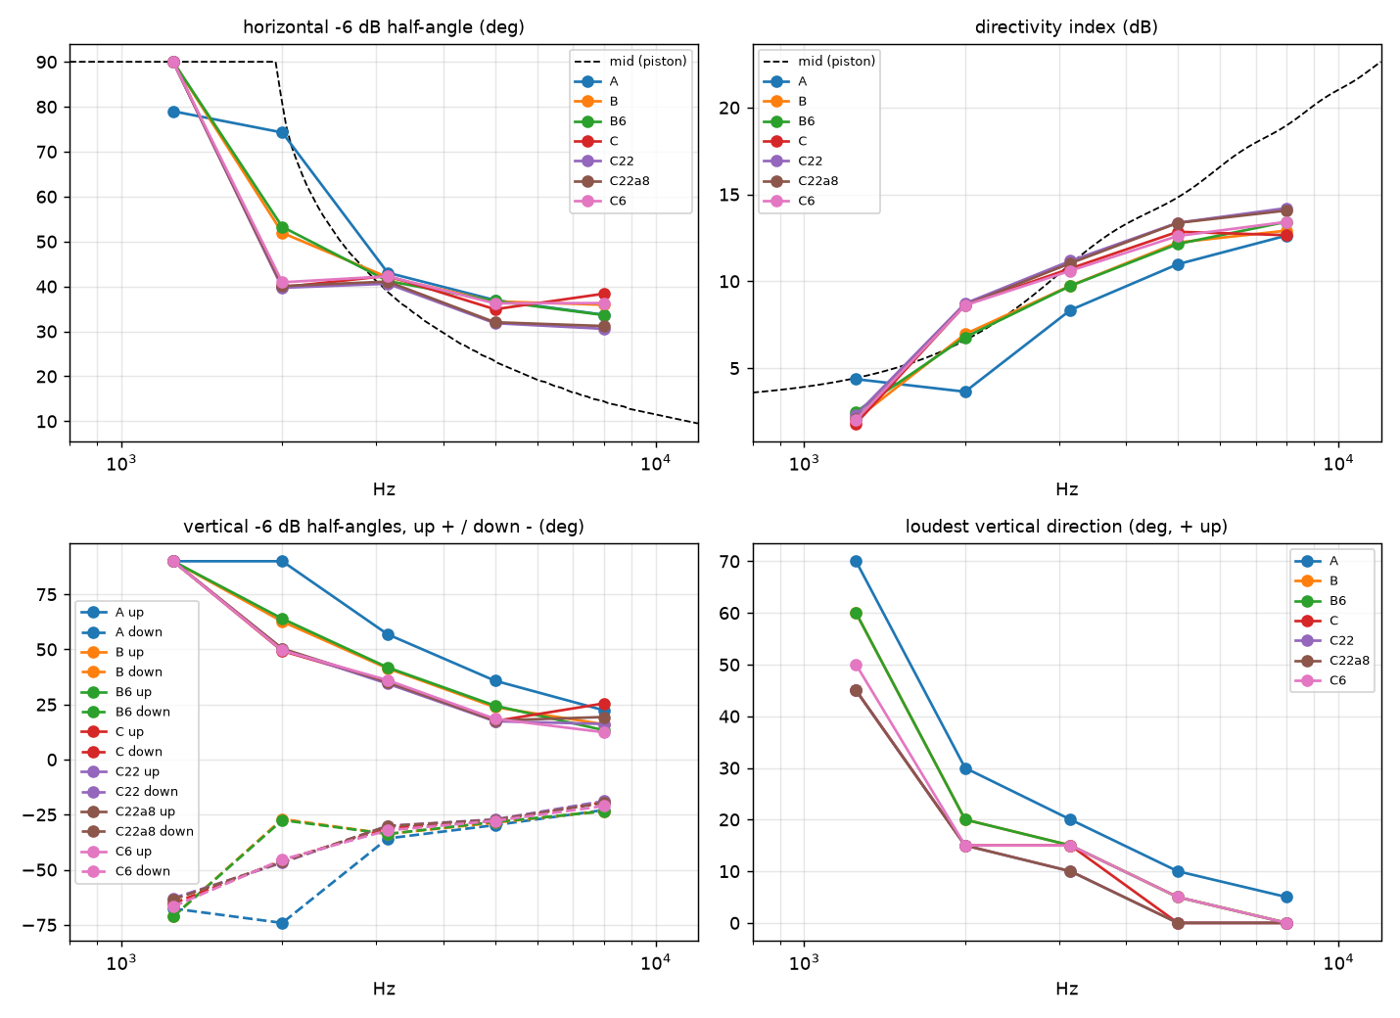
fab/out/acoustics/waveguide/study.png
