nathe-vink/earmilk/fab/out/marks/facts-print-preview.png

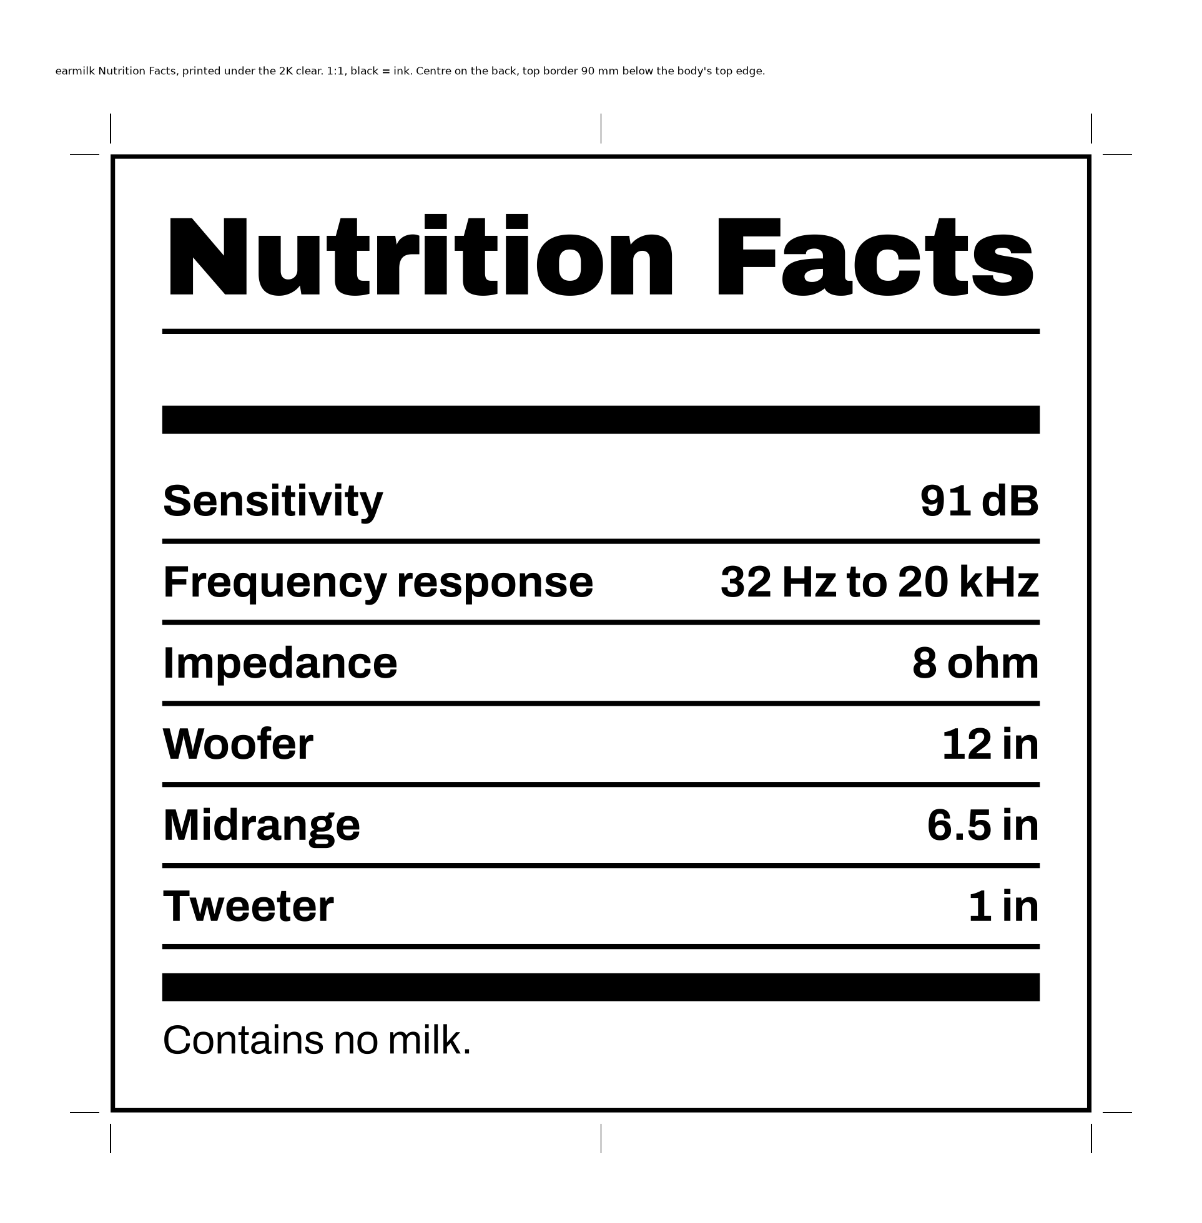
fab/out/marks/facts-print-preview.png
